mexdulon/tetra-Boards/doc/deutsch/DEC_1_0.pdf

# Decoder v1.0

mexdulon

11. April 2017

1

mexdulon | 1 DECODER

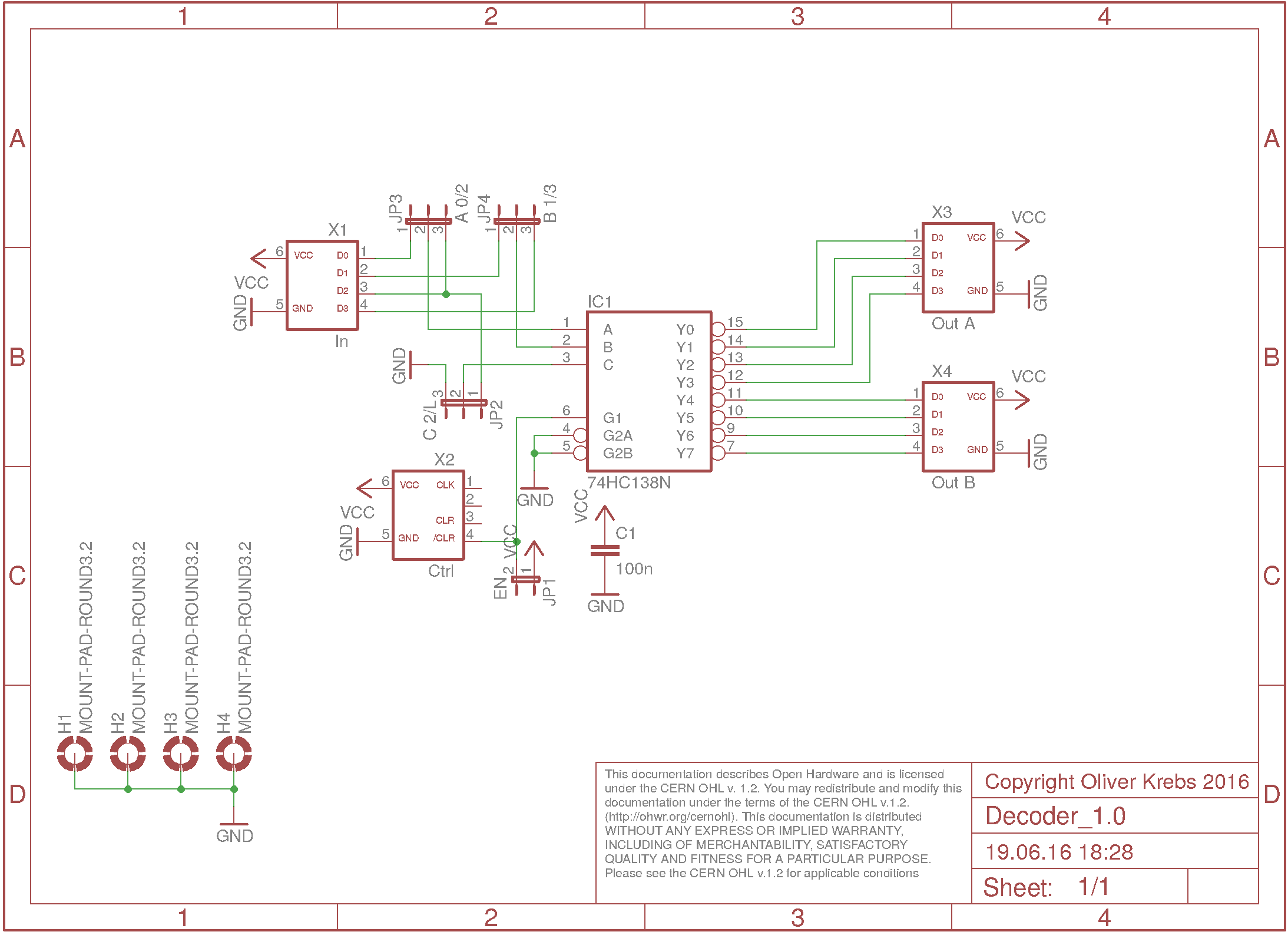
[picture p60: figure]

## 1 Decoder

### 1.1 Allgemein

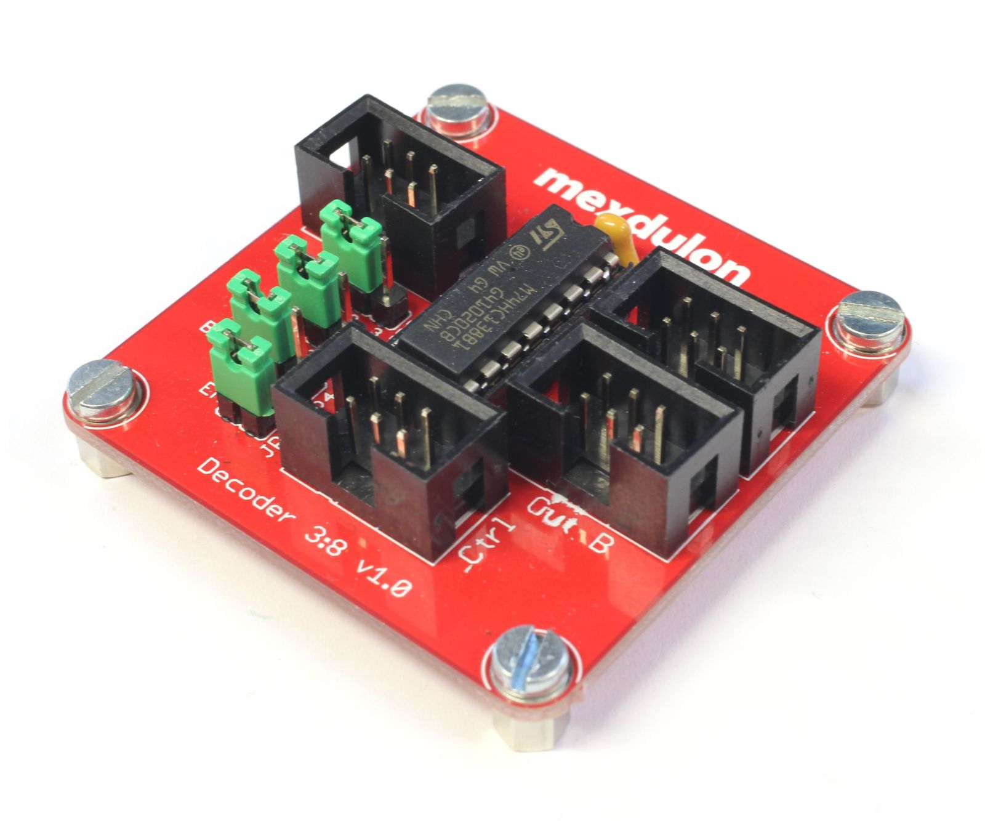
[picture p61: figure]

2

mexdulon | 1 DECODER

### 1.2 Funktion

### 1.3 Aufbau

Kürzel | Wert | Bezeichnung
C1 | 100n | Kondensator
IC1 | 74HC138N | IC (Decoder)
JP1 | EN | Stiftleiste 1x2
JP2 | C 2/L | Stiftleiste 1x3
JP3 | A 0/2 | Stiftleiste 1x3
JP4 | B 1/3 | Stiftleiste 1x3
X1 | In | Wannenstecker
X2 | Ctrl | Wannenstecker
X3 | Out A | Wannenstecker
X4 | Out B | Wannenstecker

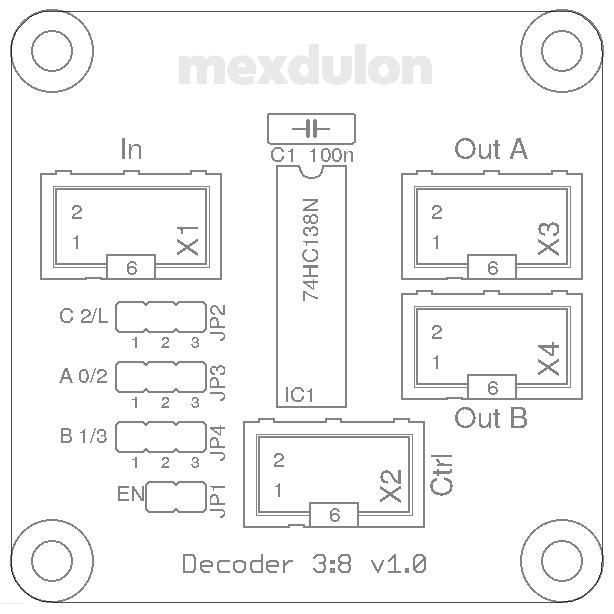
[picture p62: figure]

### 1.4 Test

3
