mexdulon/tetra-Boards/doc/deutsch/INV_1_0.pdf

# Inverter v1.0

mexdulon

11. April 2017

1

mexdulon | 1 INVERTER

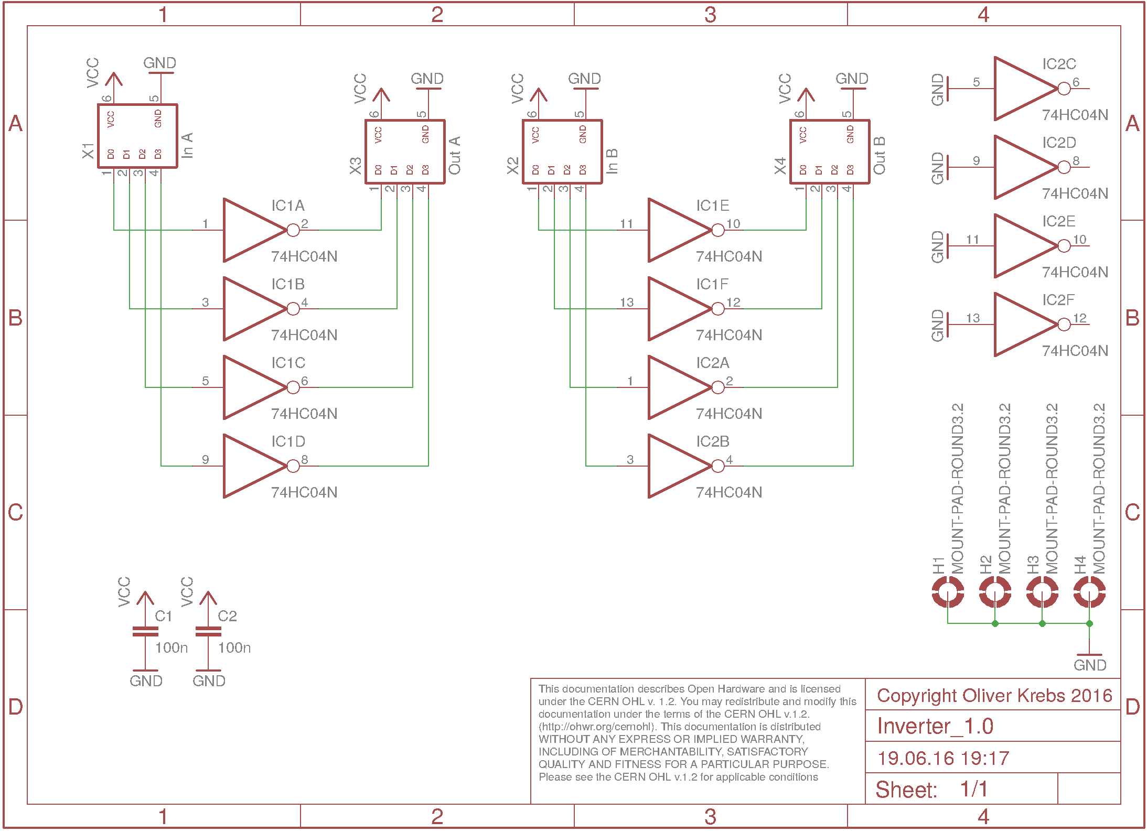
[picture p63: figure]

## 1 Inverter

### 1.1 Allgemein

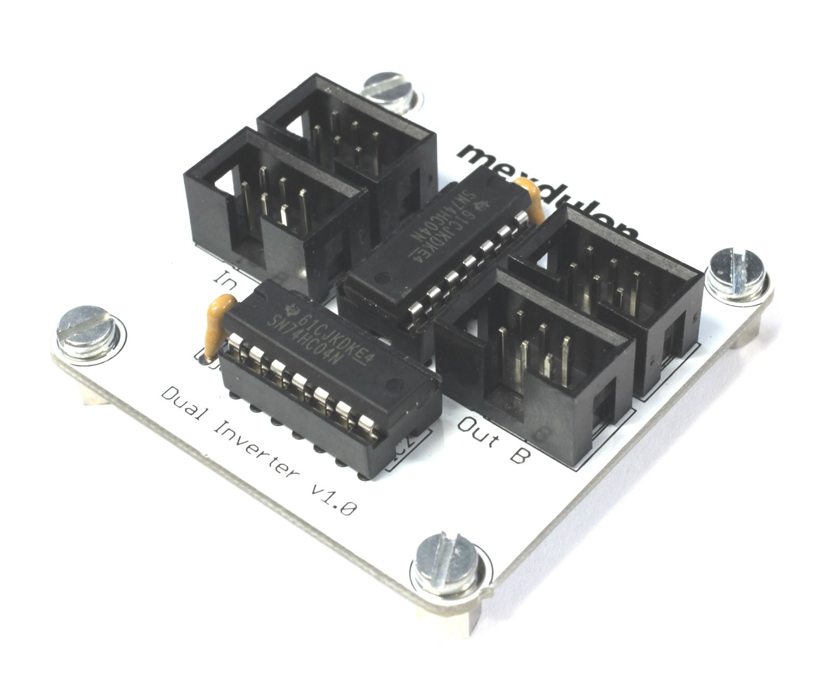
[picture p64: figure]

2

mexdulon | 1 INVERTER

### 1.2 Funktion

### 1.3 Aufbau

Kürzel | Wert | Bezeichnung
C1 | 100n | Kondensator
C2 | 100n | Kondensator
IC1 | 74HC04N | IC (Inverter)
IC2 | 74HC04N | IC (Inverter)
X1 | In A | Wannenstecker
X2 | In B | Wannenstecker
X3 | Out A | Wannenstecker
X4 | Out B | Wannenstecker

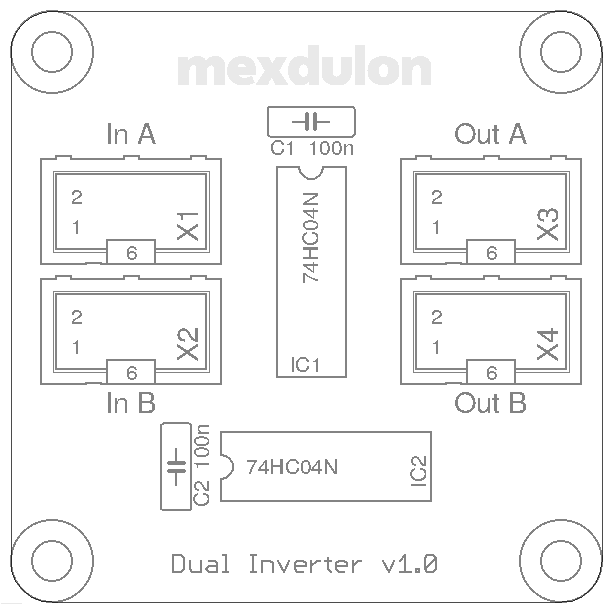
[picture p65: figure]

### 1.4 Test

3
