mexdulon/tetra-Boards/doc/deutsch/JAD_1_0.pdf

# Jumper Adapter v1.0

mexdulon

11. April 2017

1

mexdulon | 1 JUMPER ADAPTER

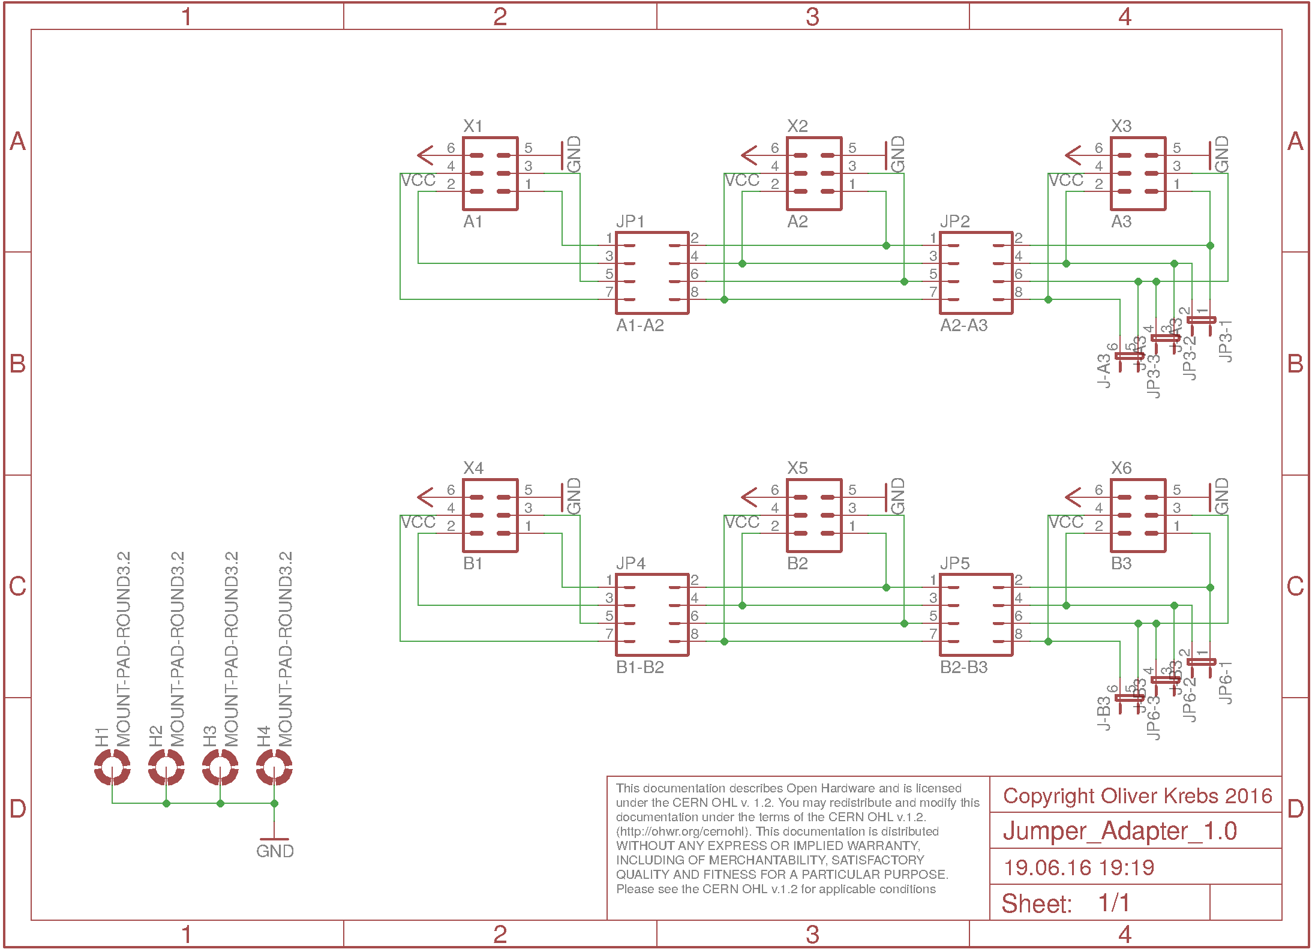
[picture p66: figure]

## 1 Jumper Adapter

### 1.1 Allgemein

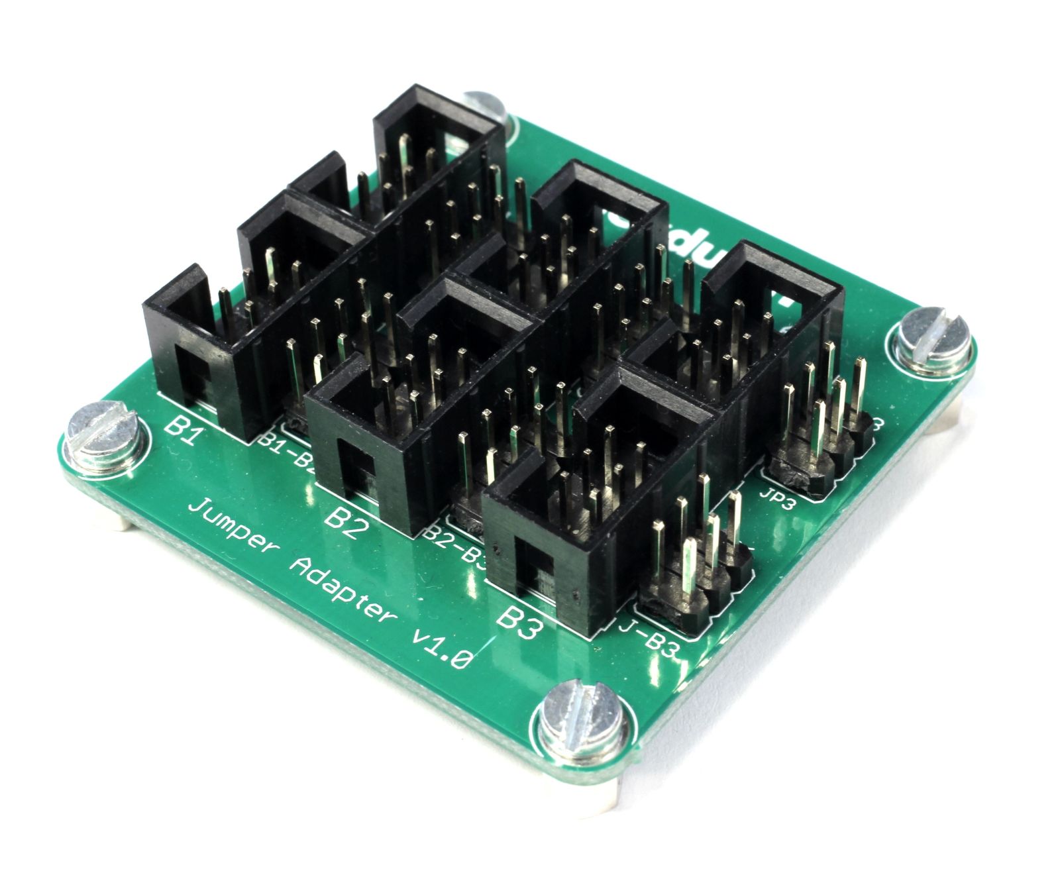
[picture p67: figure]

2

mexdulon | 1 JUMPER ADAPTER

### 1.2 Funktion

### 1.3 Aufbau

Kürzel | Wert | Bezeichnung
JP1 | A1-A2 | Stiftleiste 2x4
JP2 | A2-A3 | Stiftleiste 2x4
JP3 | J-A3 | Stiftleiste 2x3
JP4 | B1-B2 | Stiftleiste 2x4
JP5 | B2-B3 | Stiftleiste 2x4
JP6 | J-B3 | Stiftleiste 2x3
X1 | A1 | Wannenstecker
X2 | A2 | Wannenstecker
X3 | A3 | Wannenstecker
X4 | B1 | Wannenstecker
X5 | B2 | Wannenstecker
X6 | B3 | Wannenstecker

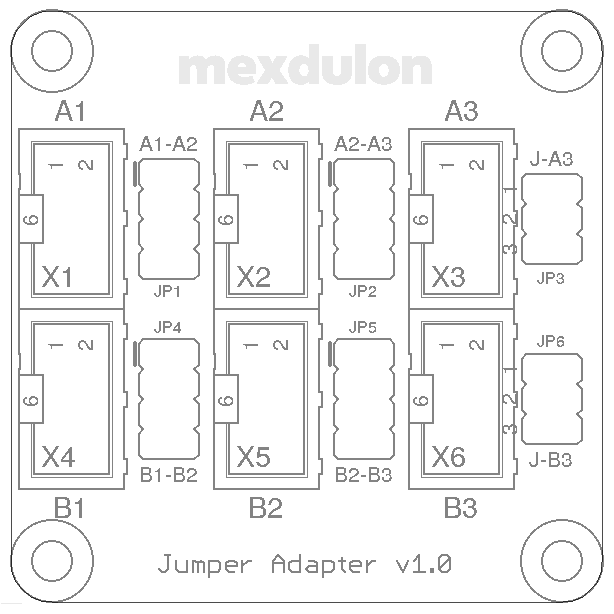
[picture p68: figure]

### 1.4 Test

3
