mexdulon/tetra-Boards/doc/deutsch/JKF_1_0.pdf

# JK Flip-flop v1.0

mexdulon

11. April 2017

1

mexdulon | 1 JK FLIPFLOP

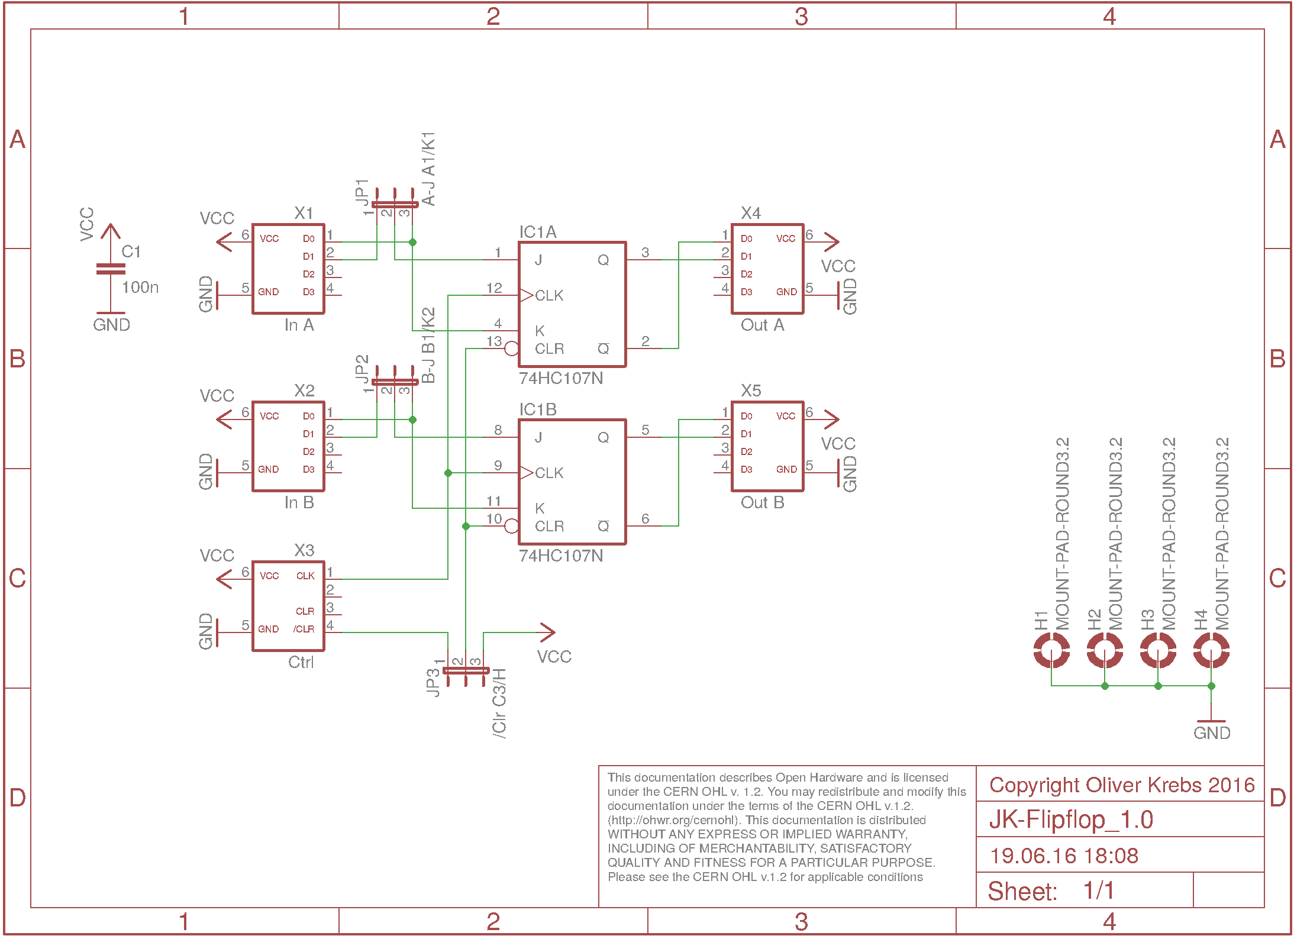
[picture p69: figure]

## 1 JK Flipflop

### 1.1 Allgemein

### 1.2 Funktion

### 1.3 Aufbau

Kürzel | Wert | Bezeichnung
C1 | 100n | Kondensator
IC1 | 74HC107N | IC (Dual Flipflop)
JP1 | A-J A1/K1 | Stiftleiste 1x3
JP2 | B-J B1/K2 | Stiftleiste 1x3
JP3 | /Clr C3/H | Stiftleiste 1x3
X1 | In A | Wannenstecker
X2 | In B | Wannenstecker
X3 | Ctrl | Wannenstecker
X4 | Out A | Wannenstecker
X5 | Out B | Wannenstecker

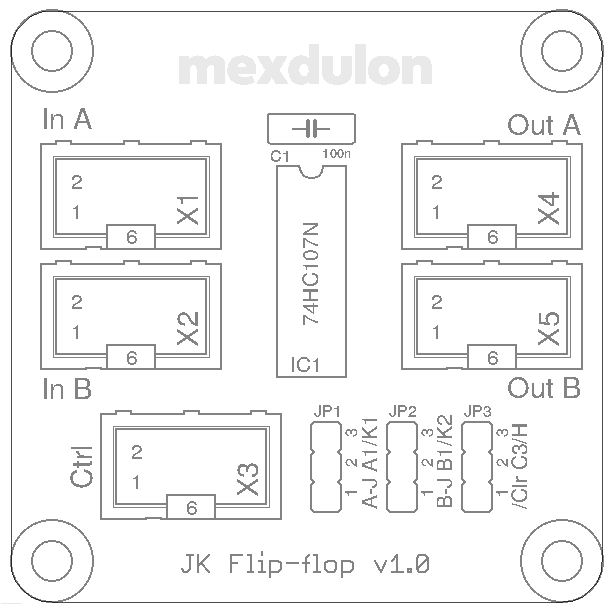
[picture p70: figure]

### 1.4 Test

2
