mexdulon/tetra-Boards/doc/deutsch/LAD_1_0.pdf

# Line Adapter v1.0

mexdulon

11. April 2017

1

mexdulon | 1 LINE ADAPTER

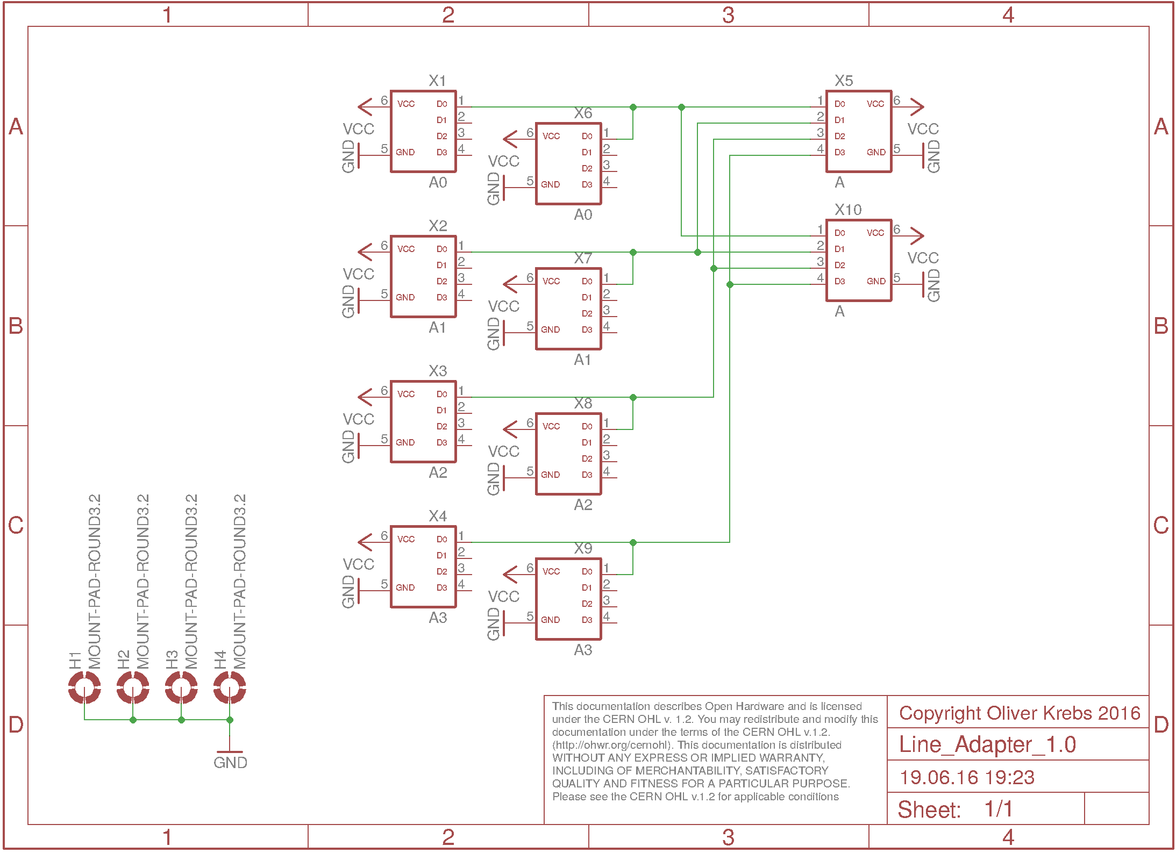
[picture p71: figure]

## 1 Line Adapter

### 1.1 Allgemein

### 1.2 Funktion

### 1.3 Aufbau

Kürzel | Wert | Bezeichnung
X1 | A0 | Wannenstecker
X2 | A1 | Wannenstecker
X3 | A2 | Wannenstecker
X4 | A3 | Wannenstecker
X5 | A | Wannenstecker
X6 | A0 | Wannenstecker
X7 | A1 | Wannenstecker
X8 | A2 | Wannenstecker
X9 | A3 | Wannenstecker
X10 | A | Wannenstecker

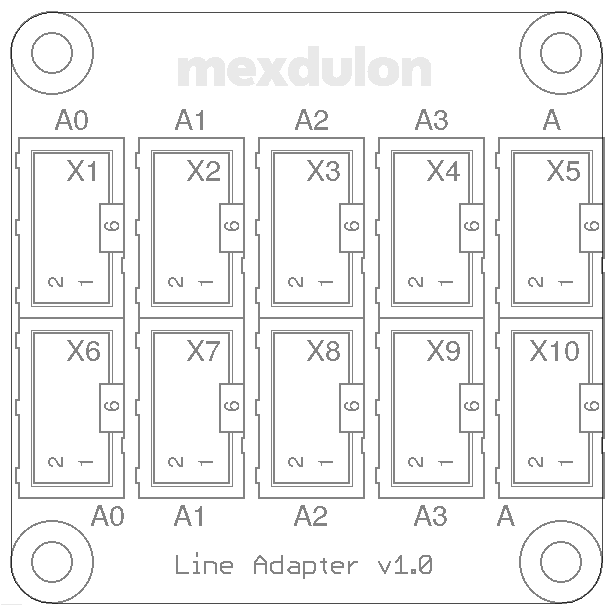
[picture p72: figure]

### 1.4 Test

2
