mexdulon/tetra-Boards/doc/deutsch/SAD_1_0.pdf

# Shift Adapter v1.0

mexdulon

11. April 2017

1

mexdulon | 1 SHIFT ADAPTER

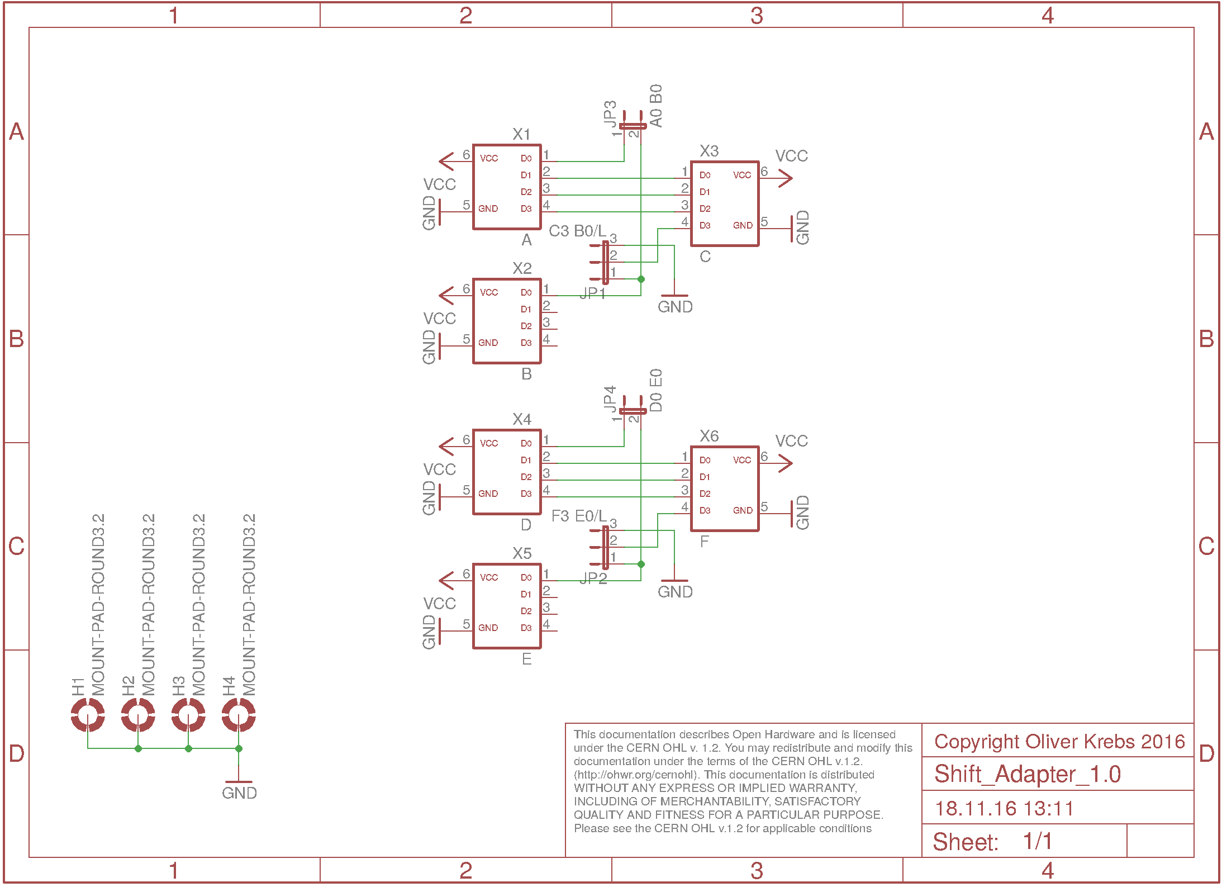
[picture p78: figure]

## 1 Shift Adapter

### 1.1 Allgemein

### 1.2 Funktion

### 1.3 Aufbau

Kürzel | Wert | Bezeichnung
JP1 | C3 B0/L | Stiftleiste 1x3
JP2 | F3 E0/L | Stiftleiste 1x3
JP3 | A0 B0 | Stiftleiste 1x2
JP4 | D0 E0 | Stiftleiste 1x2
X1 | A | Wannenstecker
X2 | B | Wannenstecker
X3 | C | Wannenstecker
X4 | D | Wannenstecker
X5 | E | Wannenstecker
X6 | F | Wannenstecker

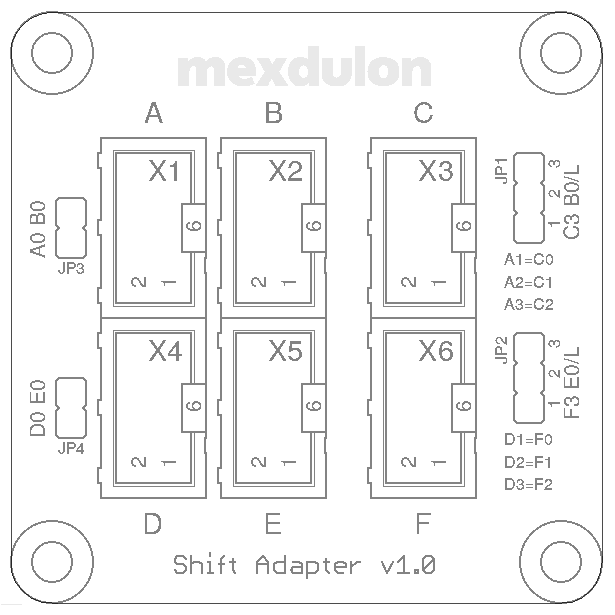
[picture p79: figure]

### 1.4 Test

2
