mexdulon/tetra-Boards/doc/7SD_1_1_sch.png

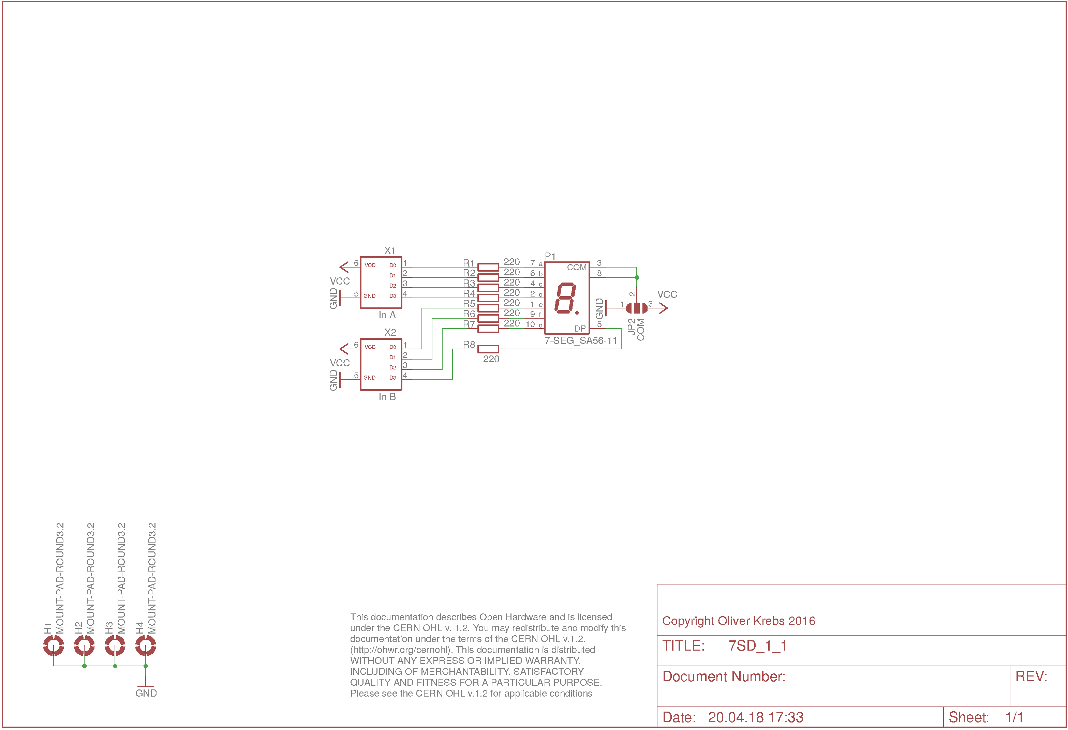
doc/7SD_1_1_sch.png
