mexdulon/tetra-Boards/doc/7SD_1_1_silk.png

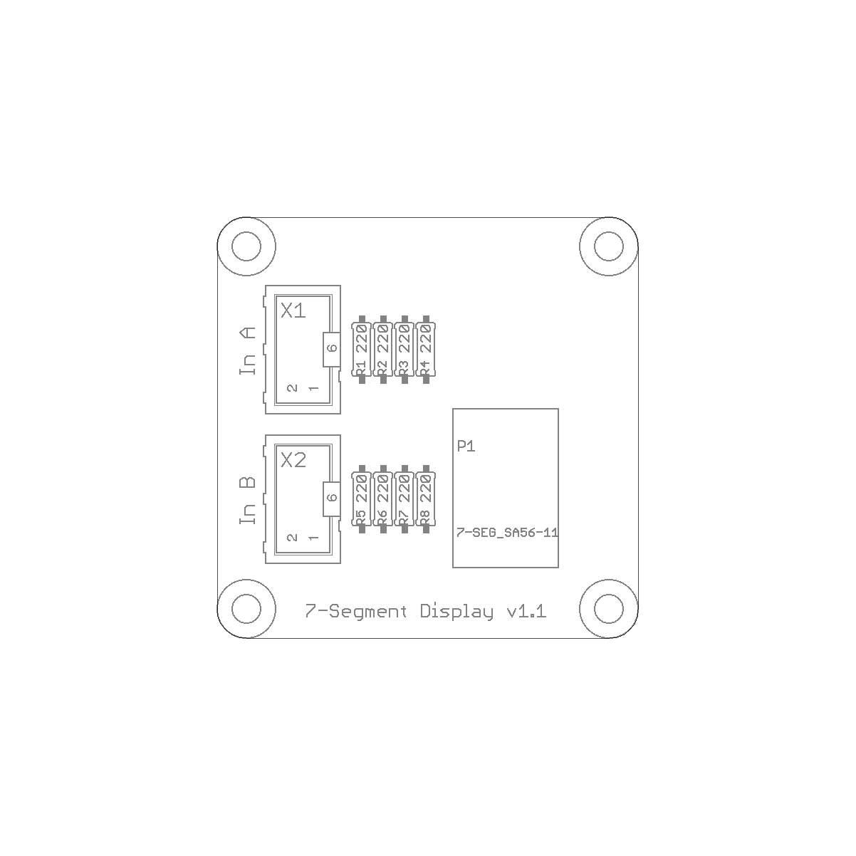
doc/7SD_1_1_silk.png
