mexdulon/tetra-Boards/doc/ADA_1_1_sch.png

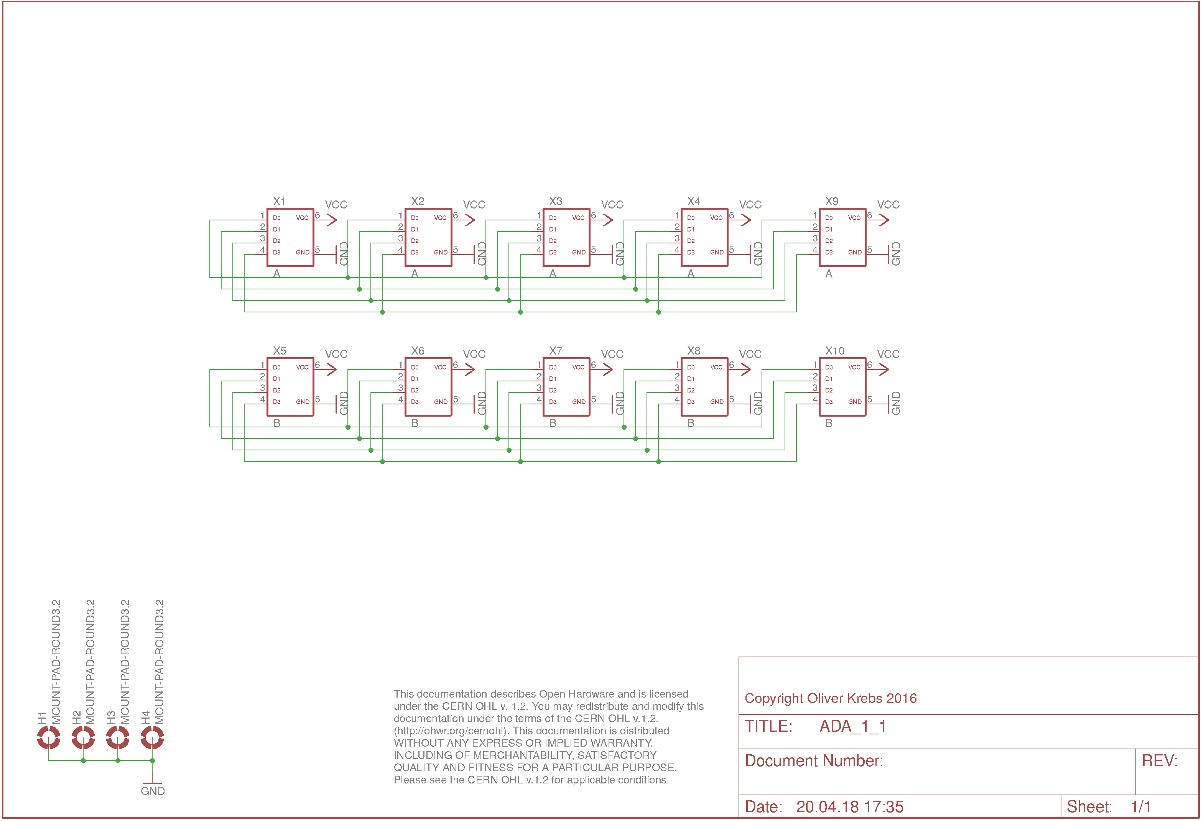
doc/ADA_1_1_sch.png
