mexdulon/tetra-Boards/doc/ADA_1_1_silk.png

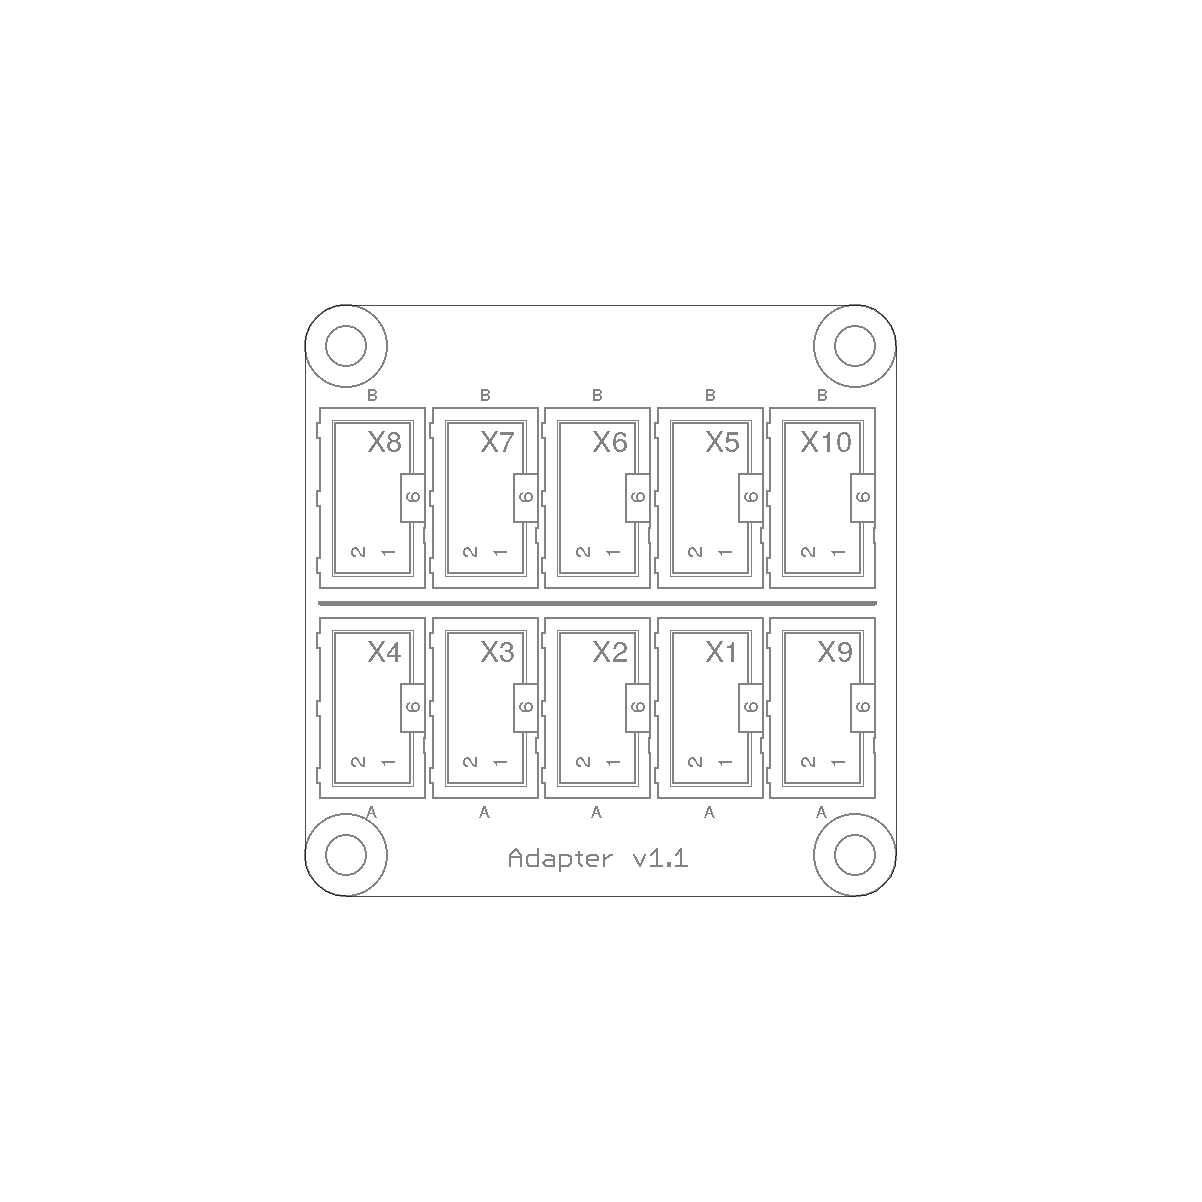
doc/ADA_1_1_silk.png
