mexdulon/tetra-Boards/doc/ADC_1_0_sch.png

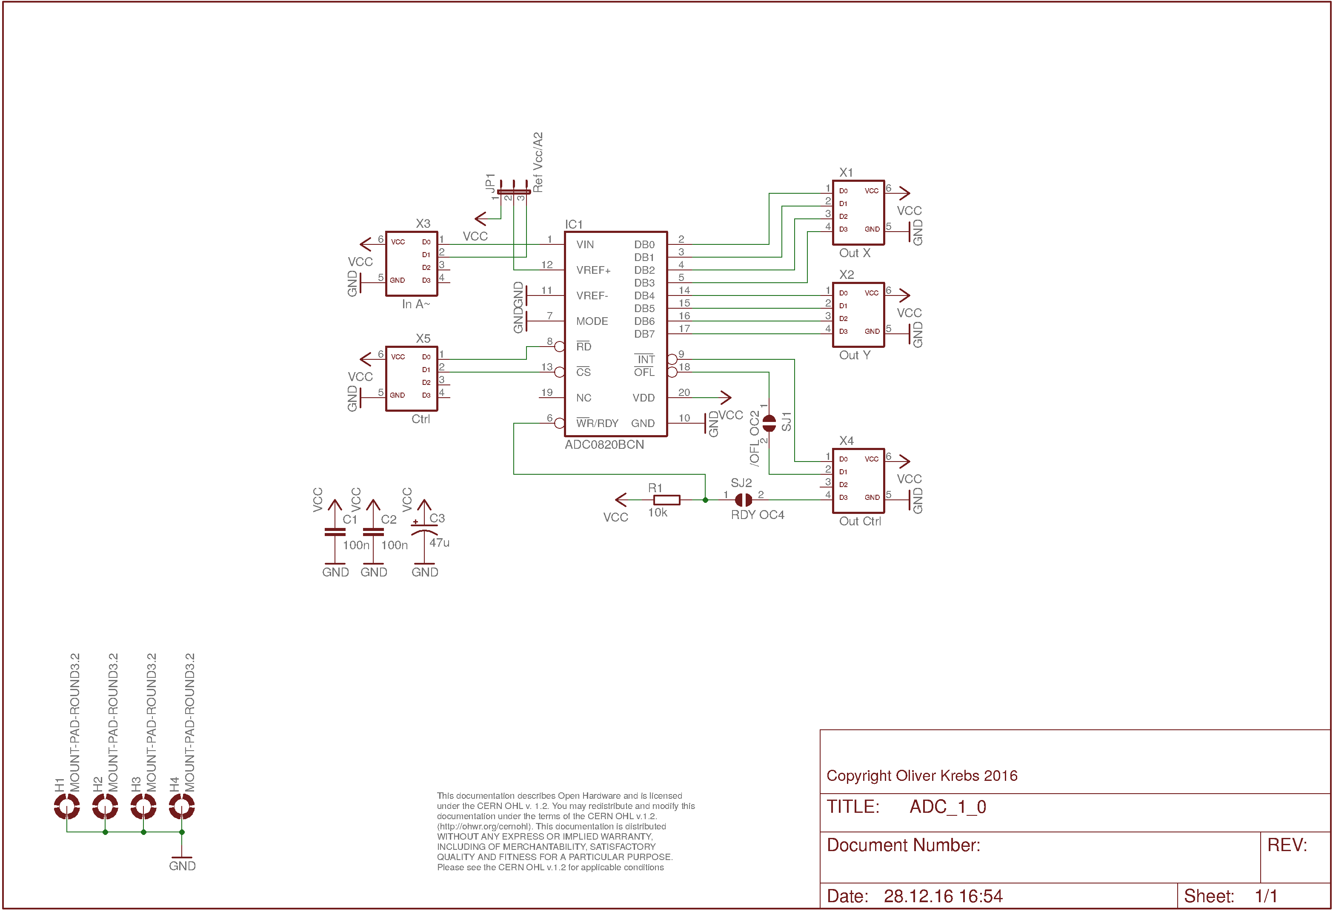
doc/ADC_1_0_sch.png
