mexdulon/tetra-Boards/doc/ADC_1_0_silk.png

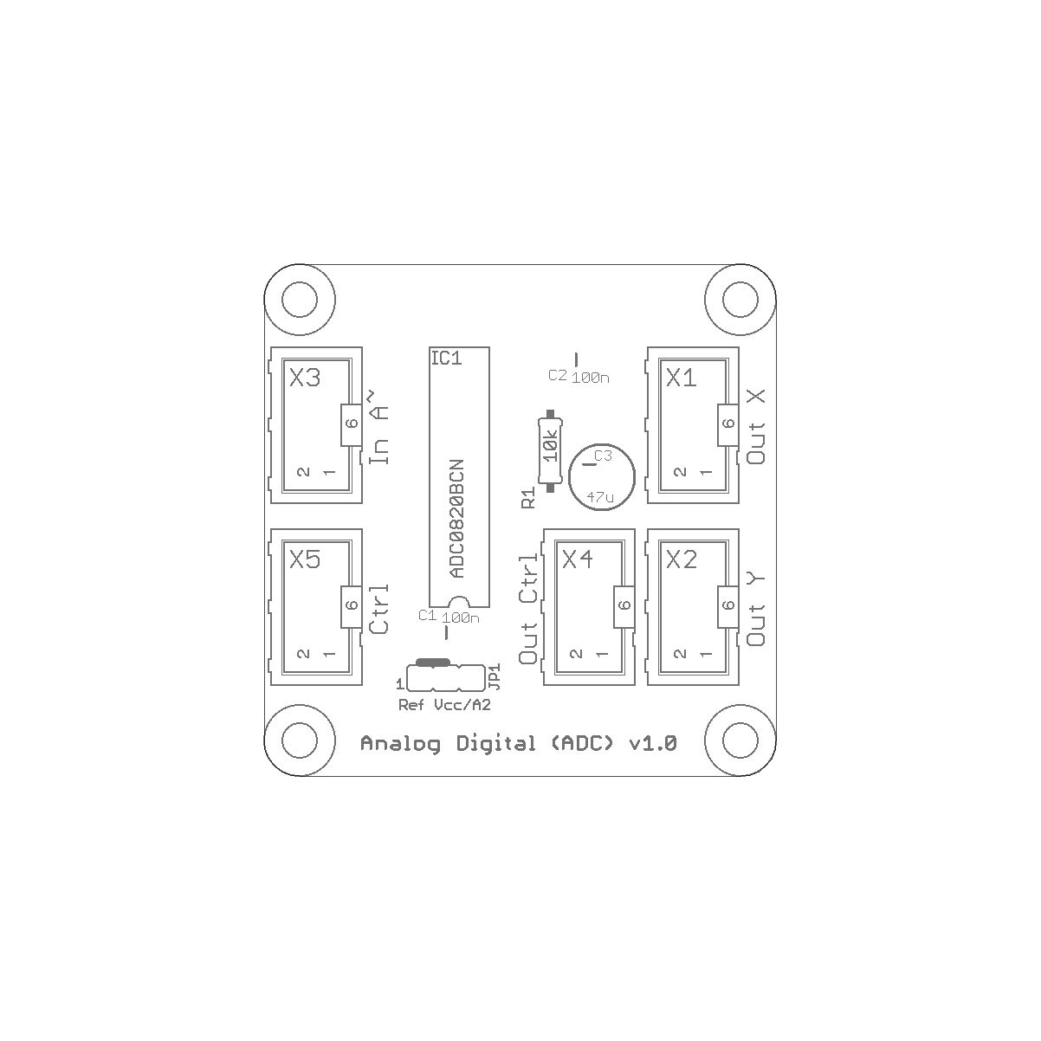
doc/ADC_1_0_silk.png
