mexdulon/tetra-Boards/doc/ADD_1_1_sch.png

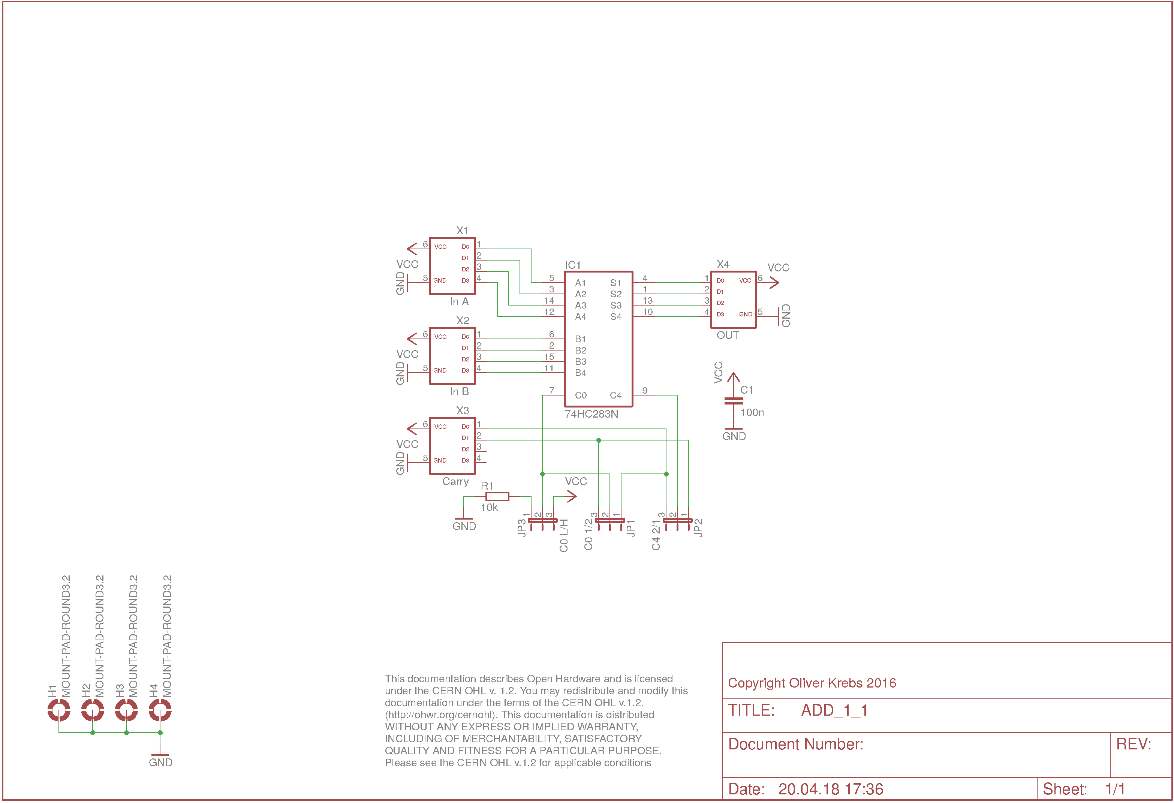
doc/ADD_1_1_sch.png
