mexdulon/tetra-Boards/doc/ALU_1_0_sch.png

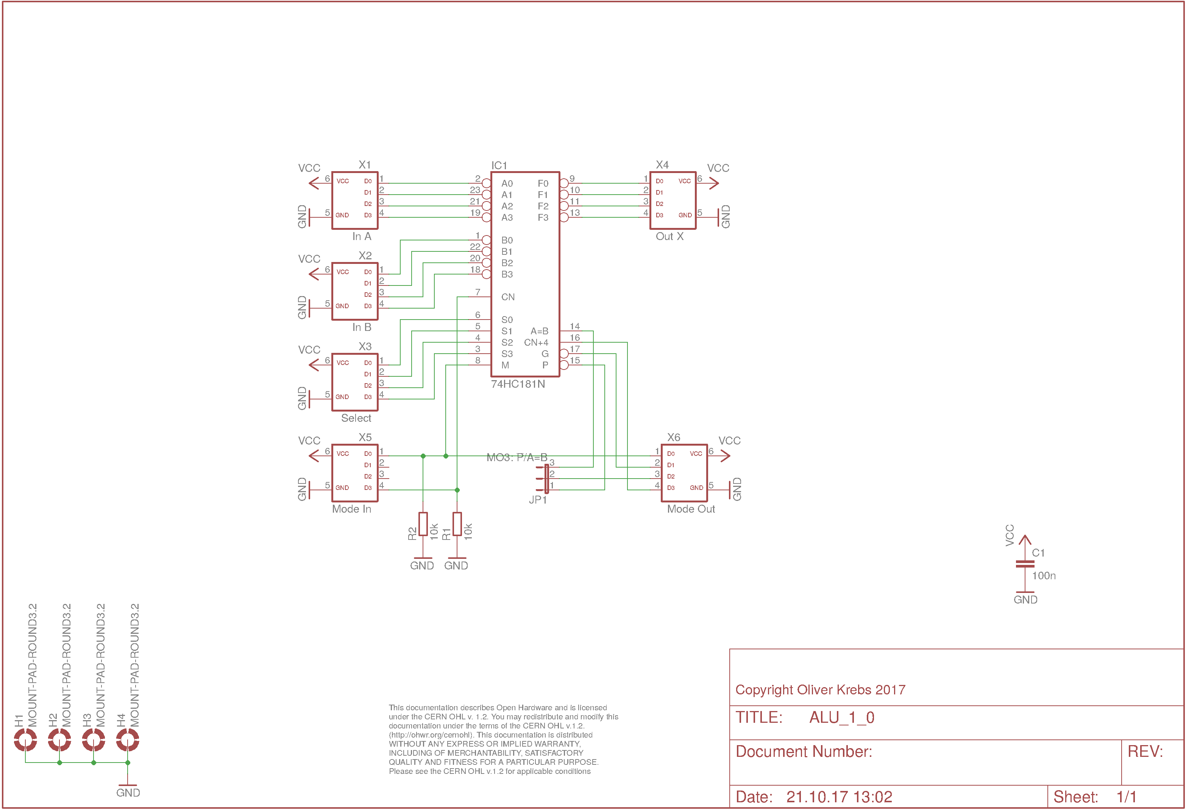
doc/ALU_1_0_sch.png
