mexdulon/tetra-Boards/doc/ALU_1_0_silk.png

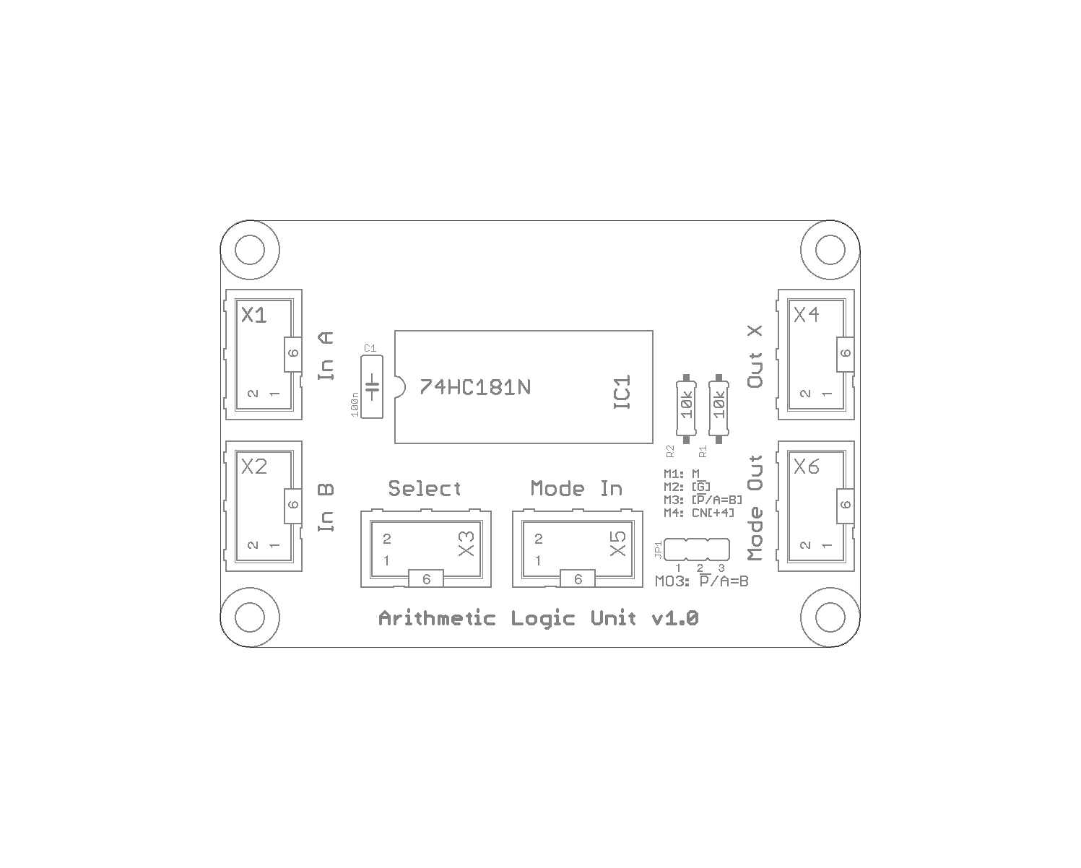
doc/ALU_1_0_silk.png
