mexdulon/tetra-Boards/doc/AMP_1_0_sch.png

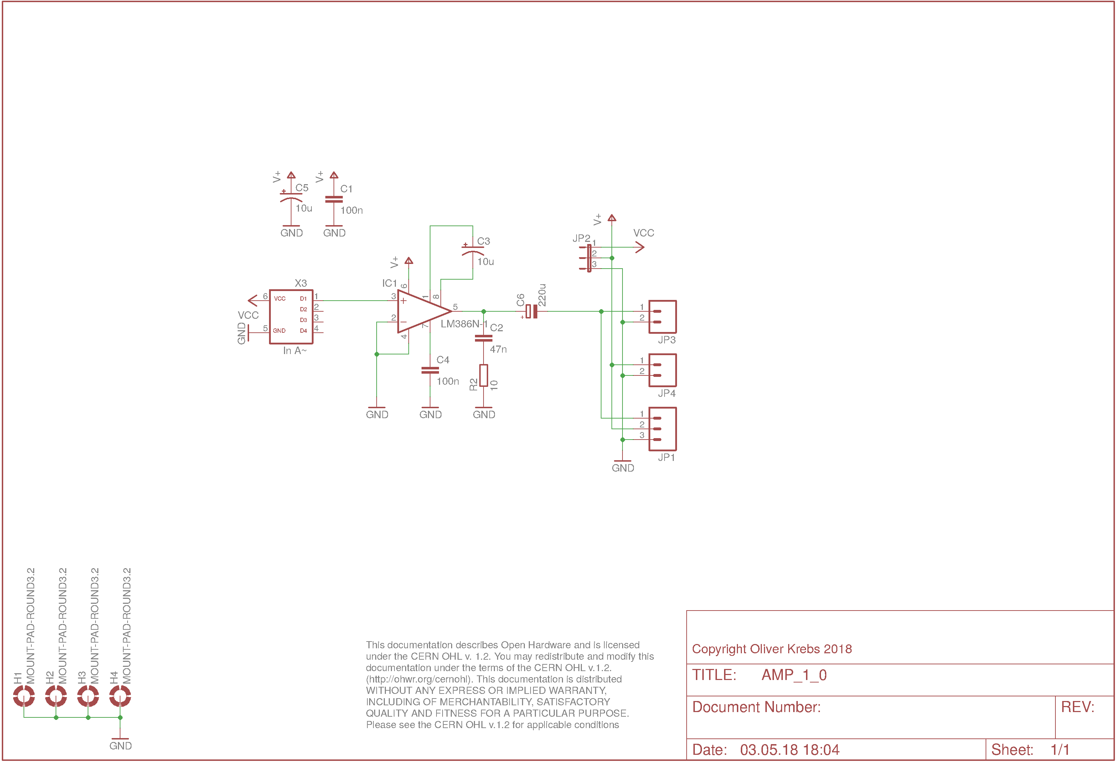
doc/AMP_1_0_sch.png
