mexdulon/tetra-Boards/doc/AMP_1_0_silk.png

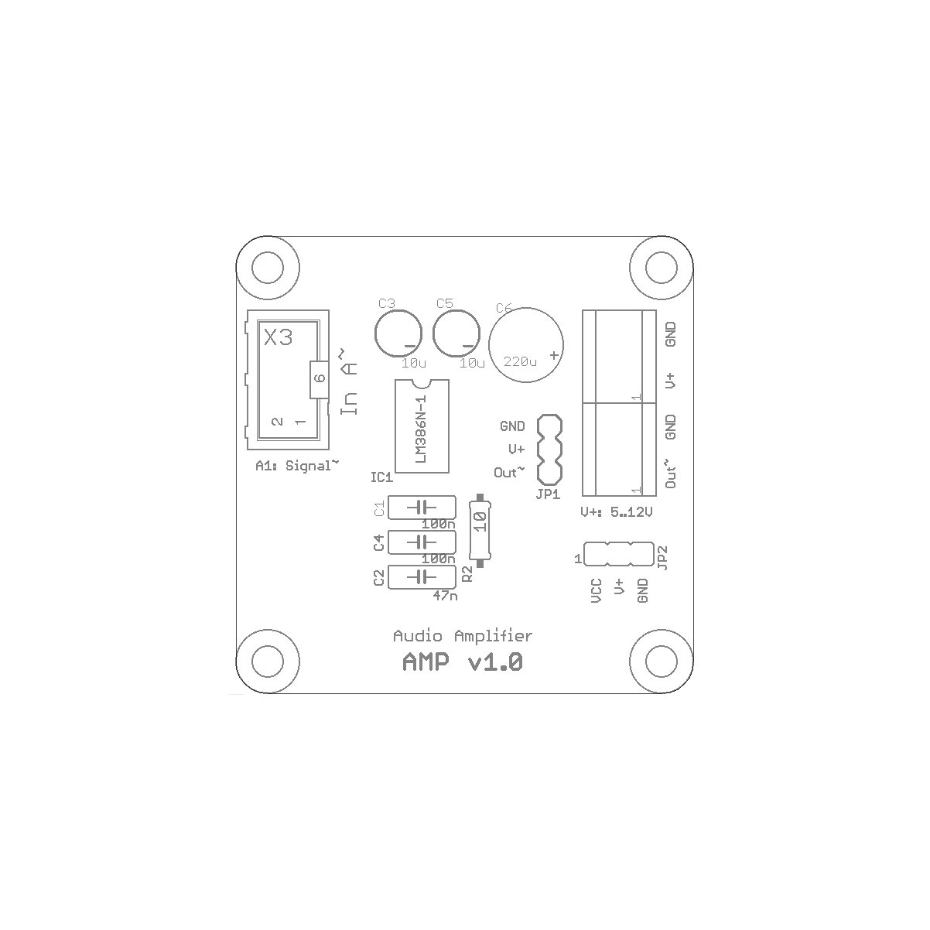
doc/AMP_1_0_silk.png
