mexdulon/tetra-Boards/doc/AND_1_1_sch.png

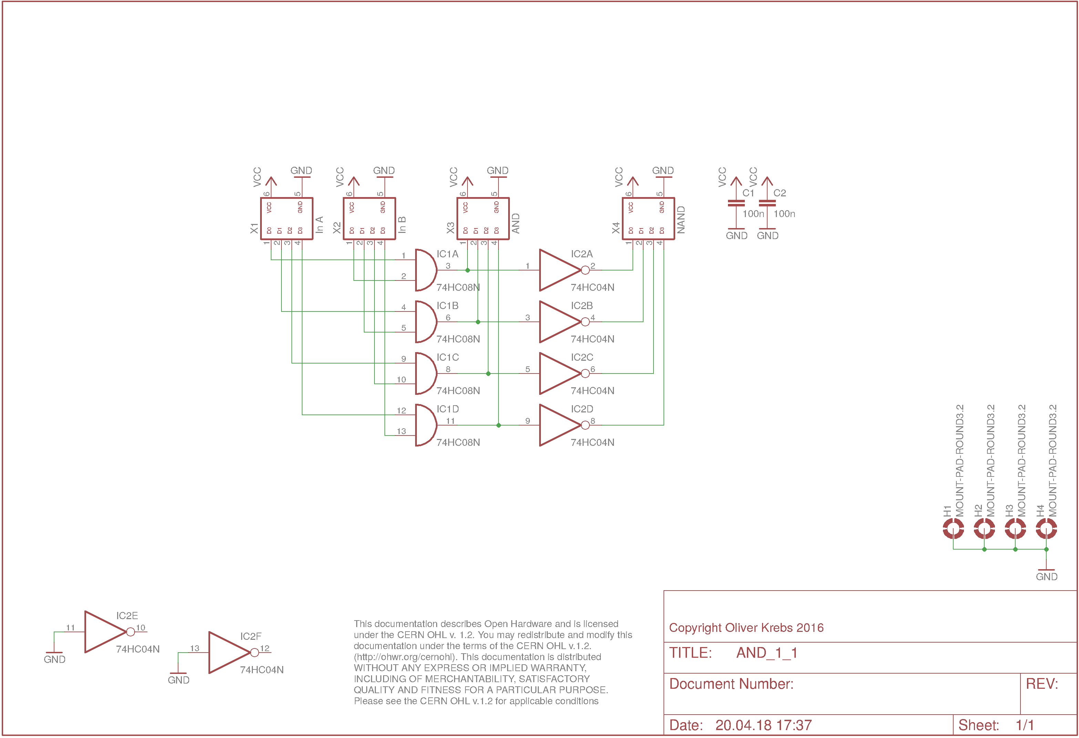
doc/AND_1_1_sch.png
