mexdulon/tetra-Boards/doc/AND_1_1_silk.png

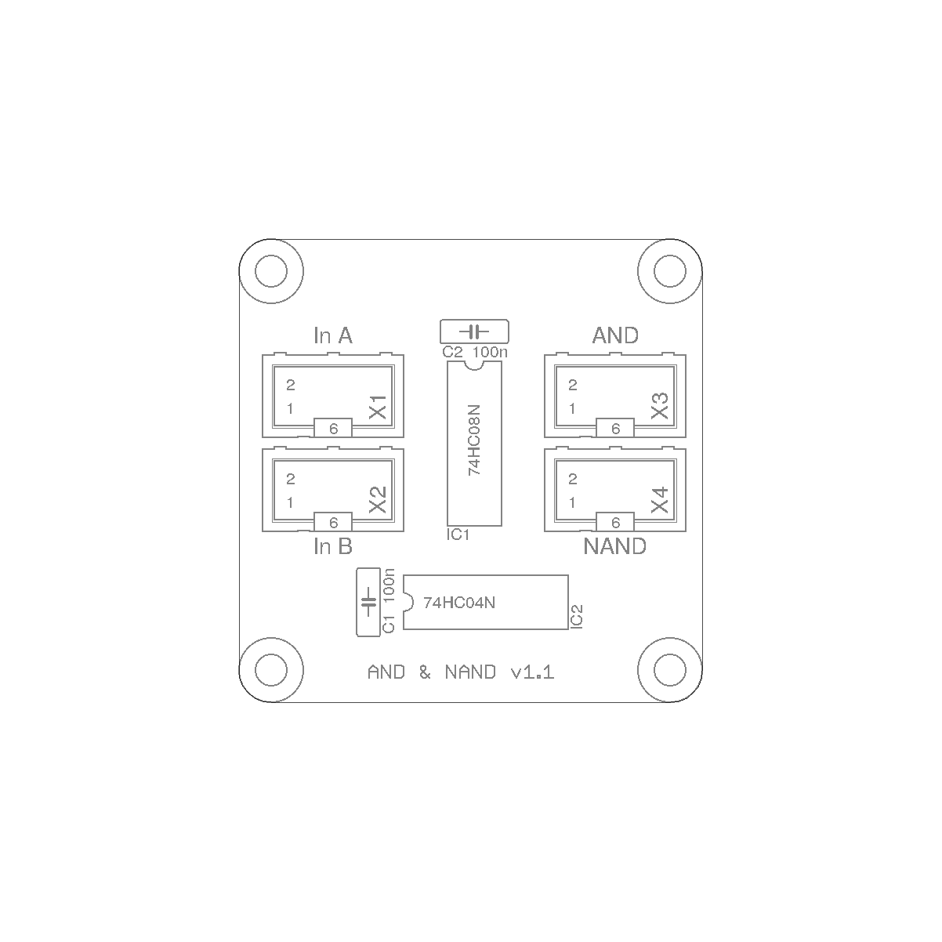
doc/AND_1_1_silk.png
