mexdulon/tetra-Boards/doc/ANS_1_1_sch.png

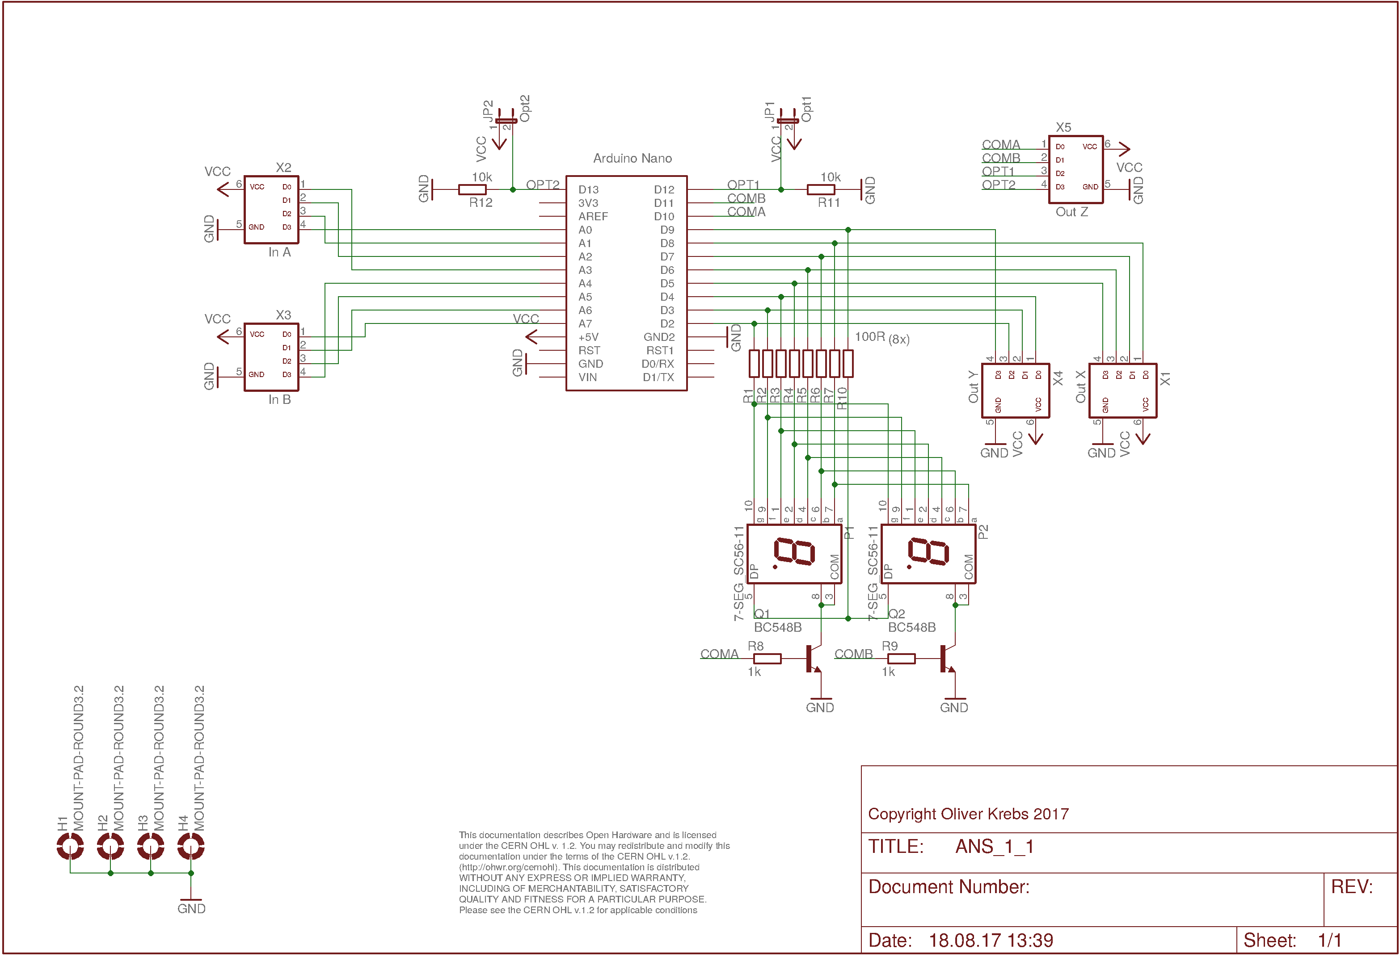
doc/ANS_1_1_sch.png
