mexdulon/tetra-Boards/doc/ANS_1_1_silk.png

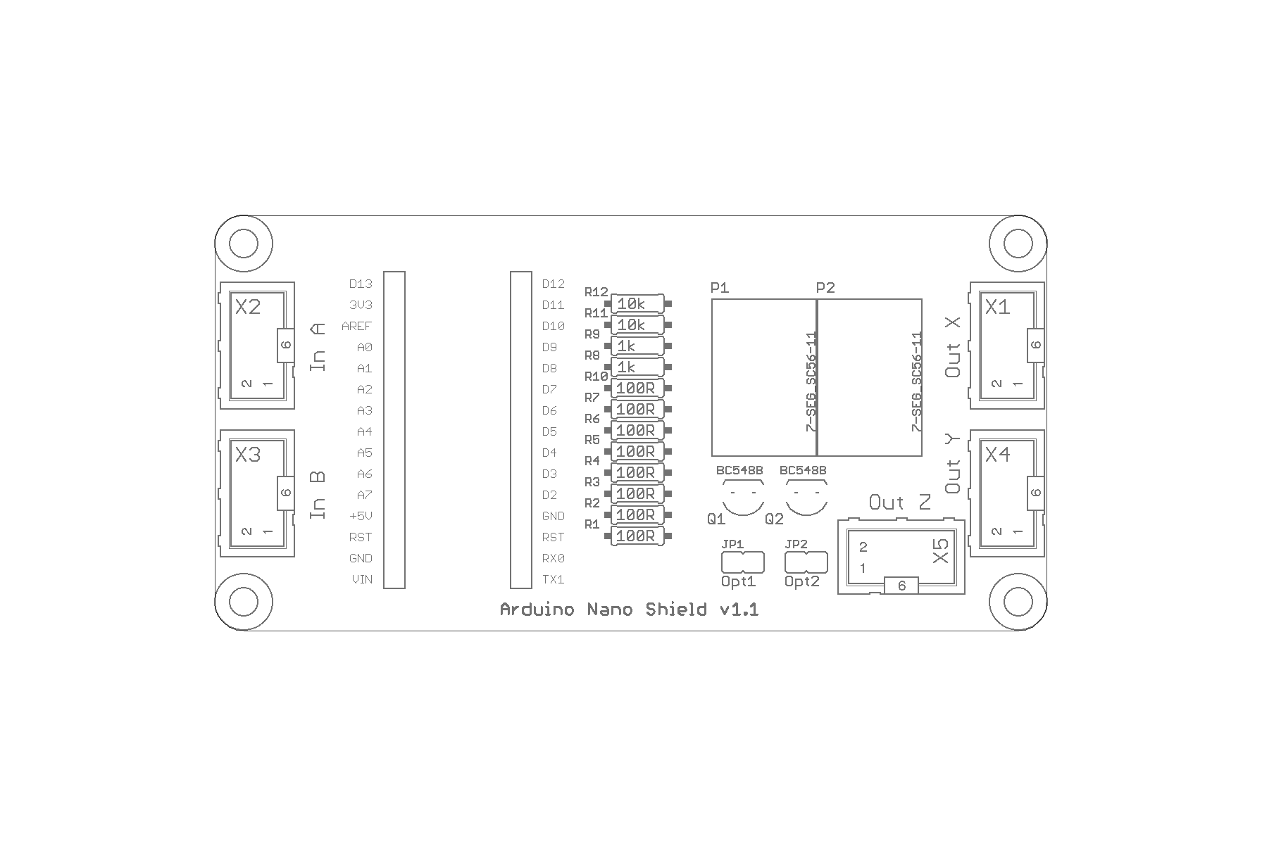
doc/ANS_1_1_silk.png
