mexdulon/tetra-Boards/doc/ARD_1_0_sch.png

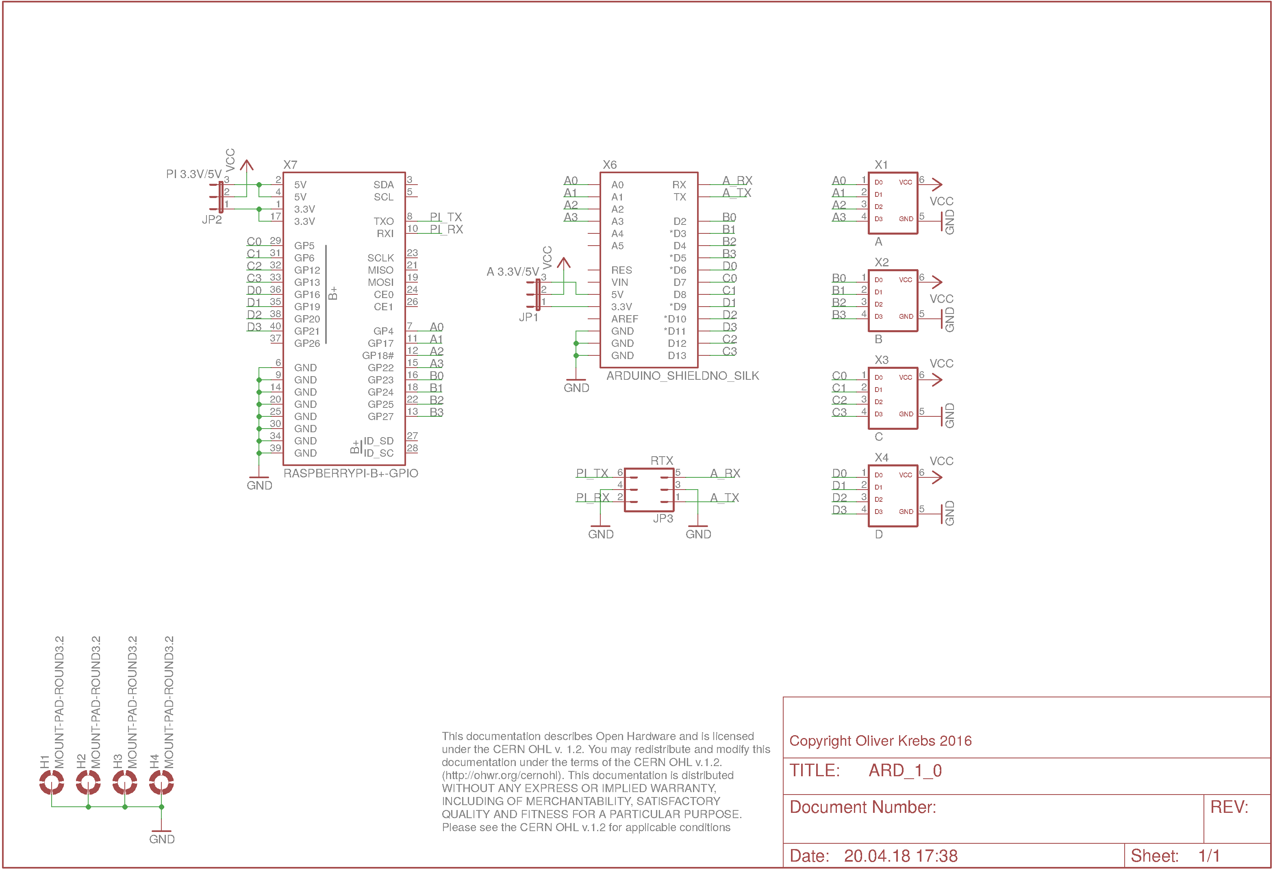
doc/ARD_1_0_sch.png
