mexdulon/tetra-Boards/doc/ARD_1_0_silk.png

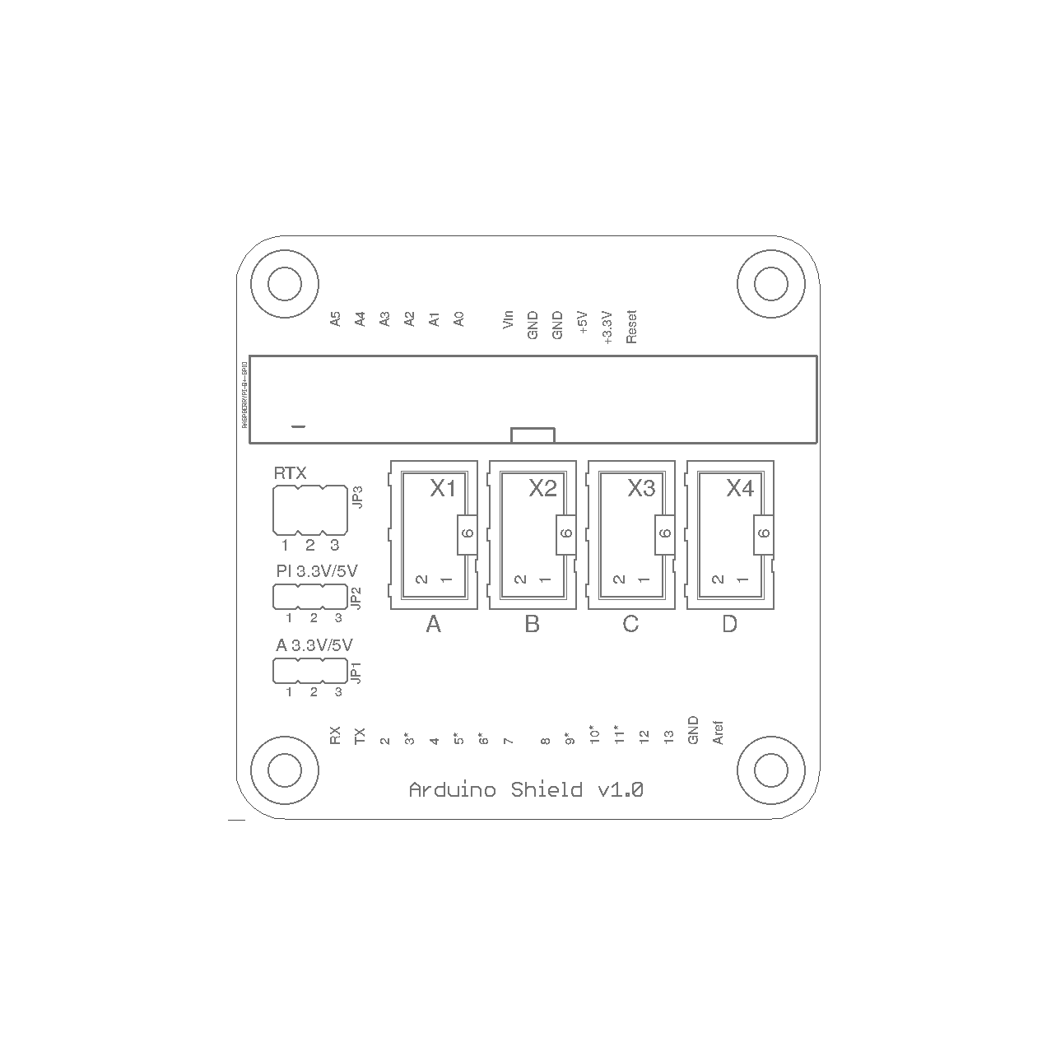
doc/ARD_1_0_silk.png
