mexdulon/tetra-Boards/doc/AVC_1_0_sch.png

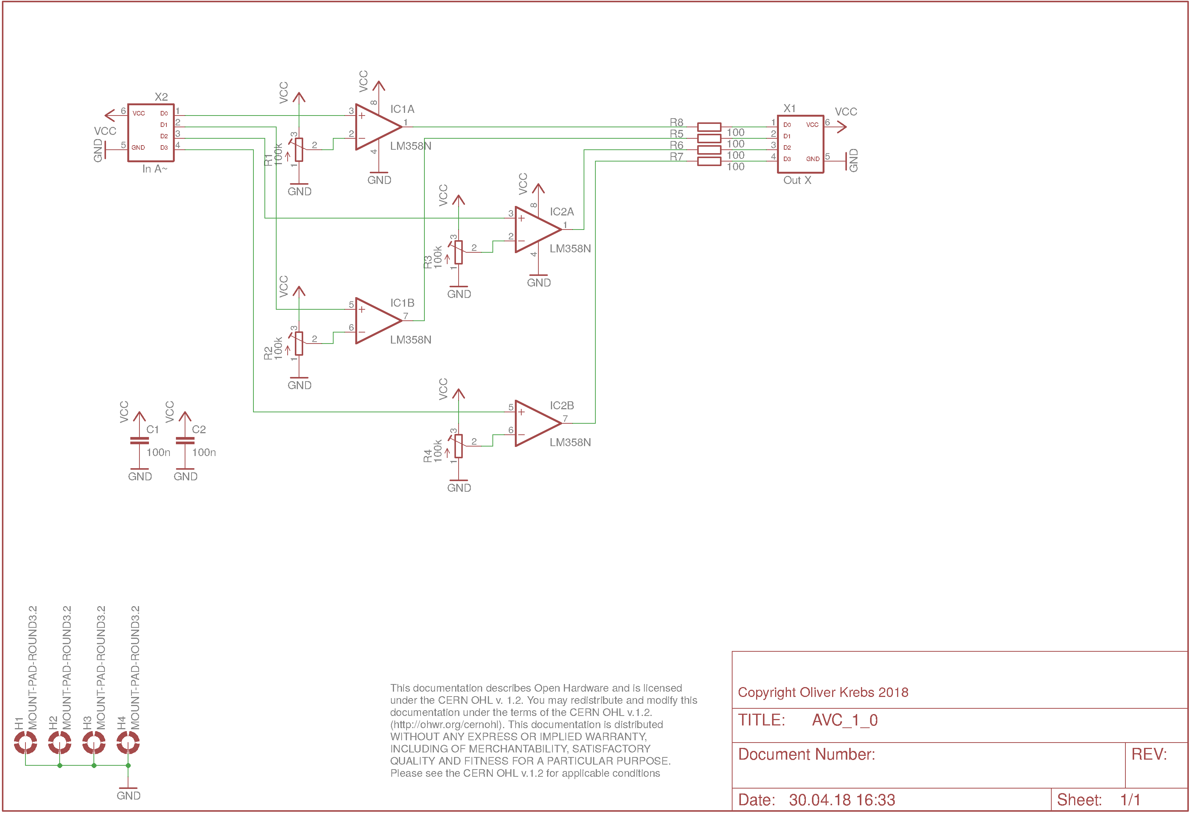
doc/AVC_1_0_sch.png
