mexdulon/tetra-Boards/doc/B7D_1_1_sch.png

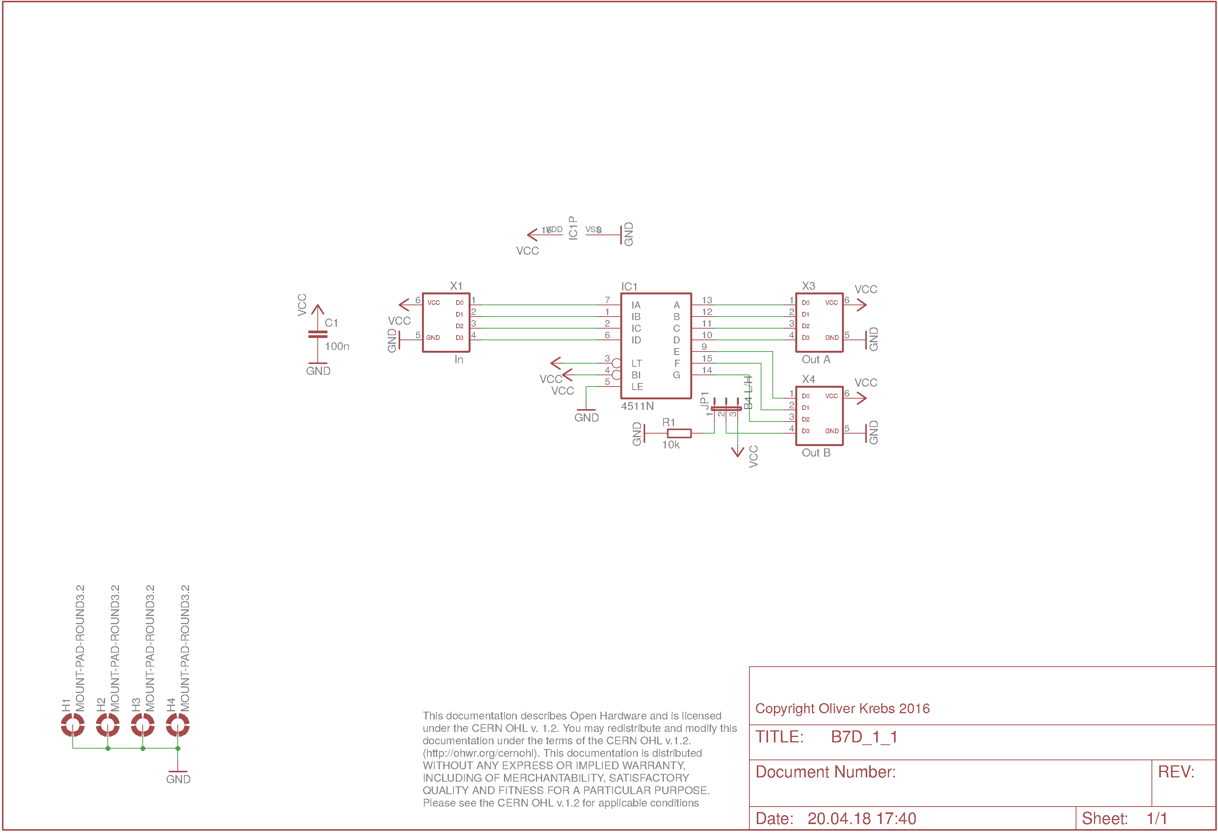
doc/B7D_1_1_sch.png
