mexdulon/tetra-Boards/doc/BCC_1_1_sch.png

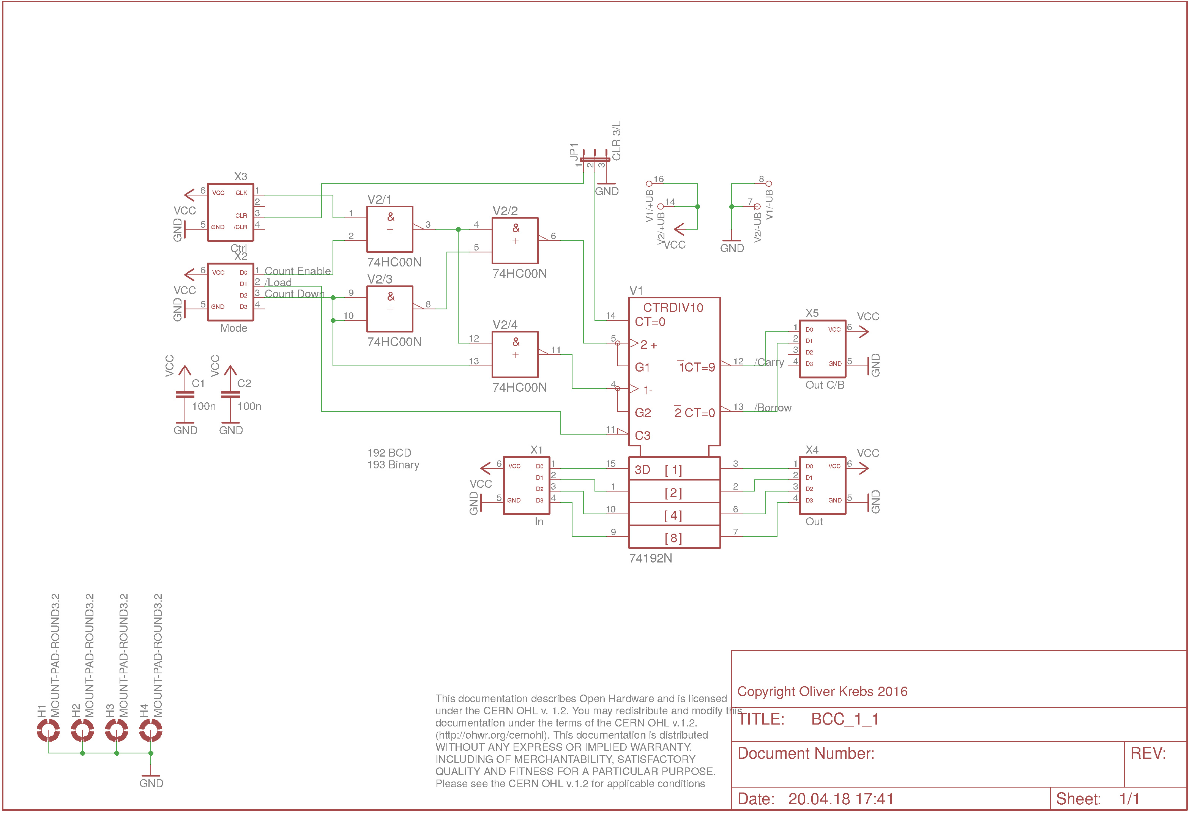
doc/BCC_1_1_sch.png
