mexdulon/tetra-Boards/doc/BNC_1_1_sch.png

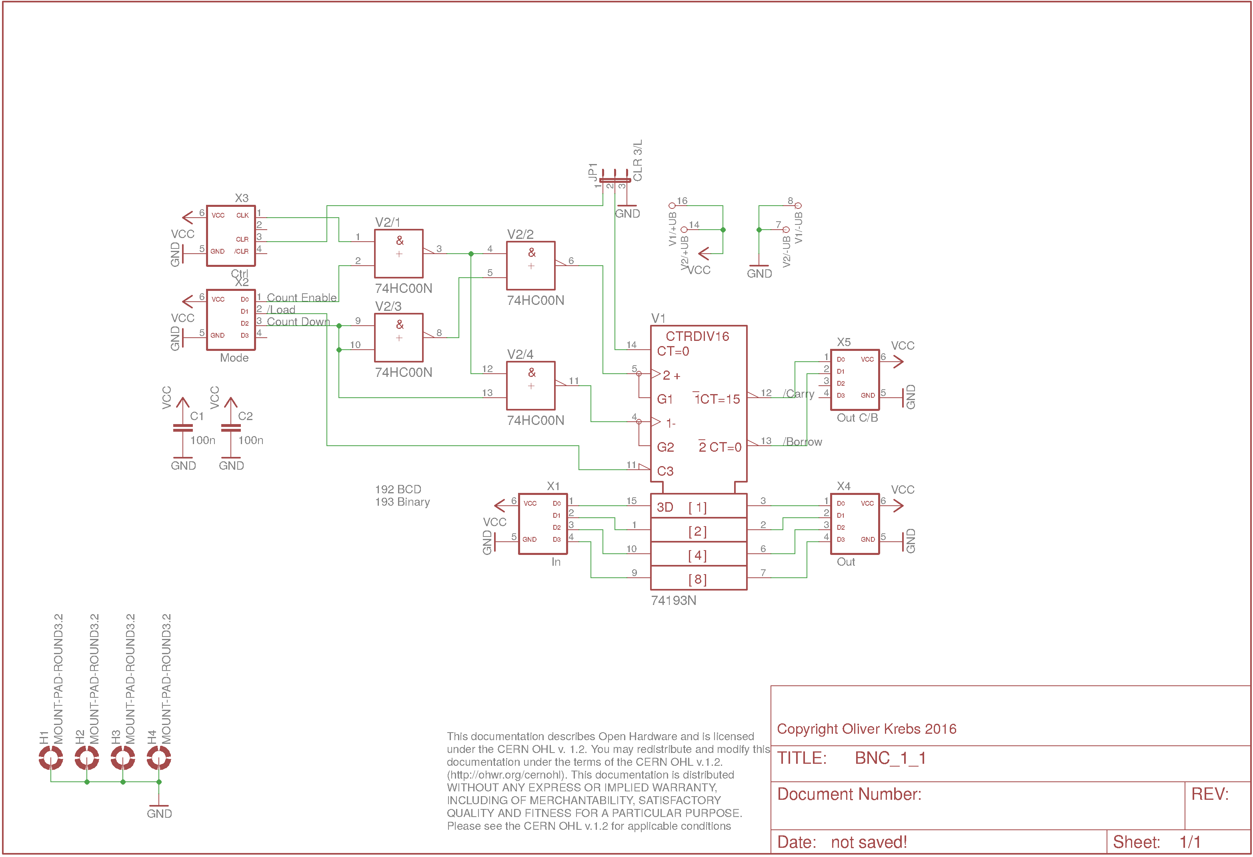
doc/BNC_1_1_sch.png
