mexdulon/tetra-Boards/doc/BTN_1_1_sch.png

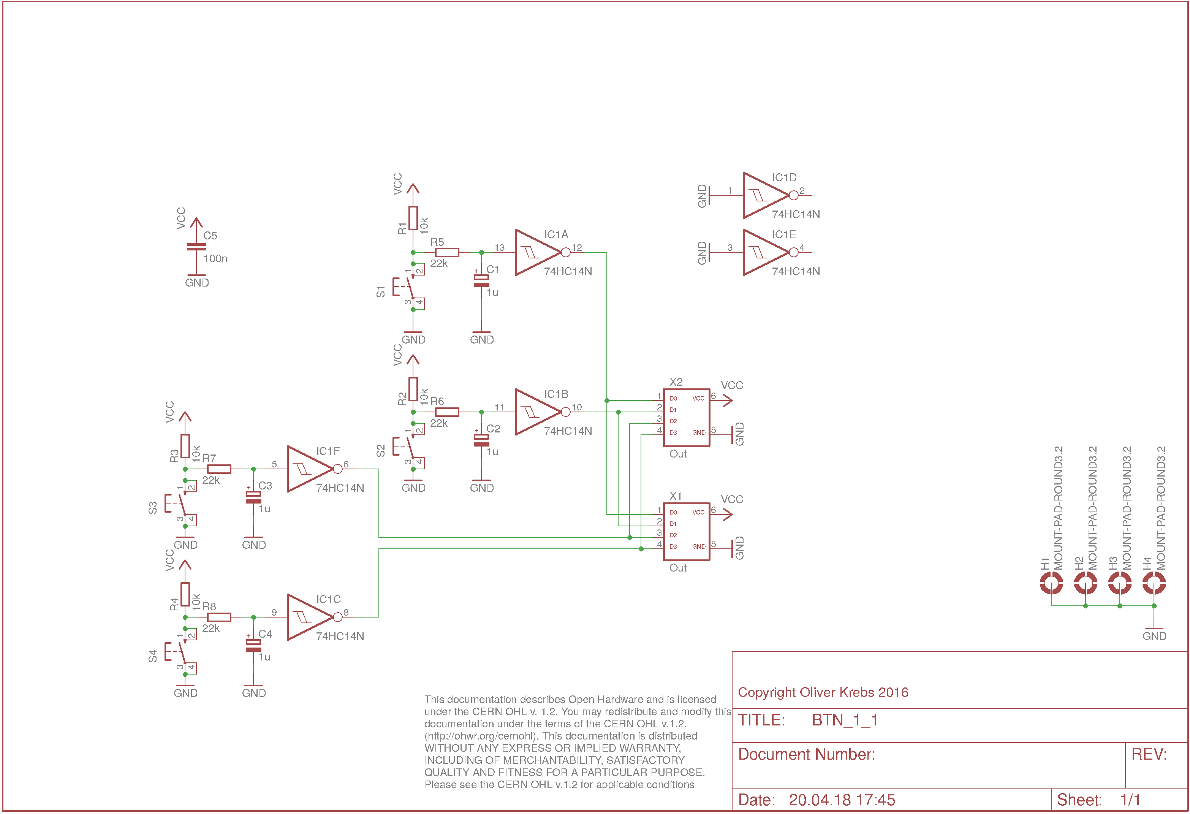
doc/BTN_1_1_sch.png
