mexdulon/tetra-Boards/doc/C12_1_0_sch.png

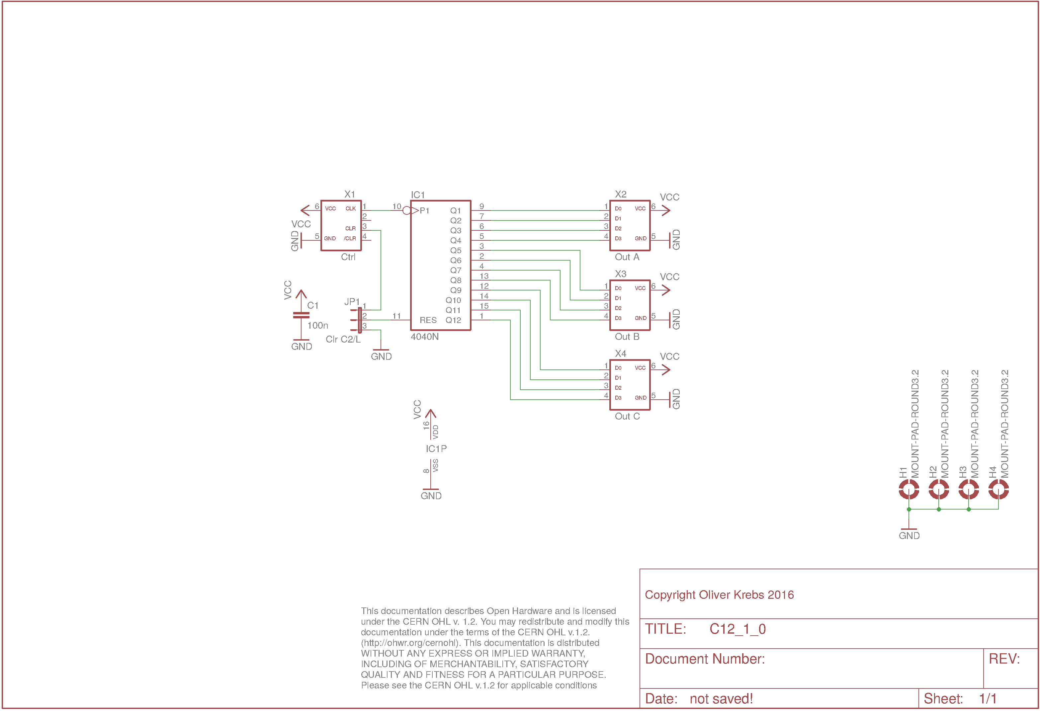
doc/C12_1_0_sch.png
