mexdulon/tetra-Boards/doc/C12_1_0_silk.png

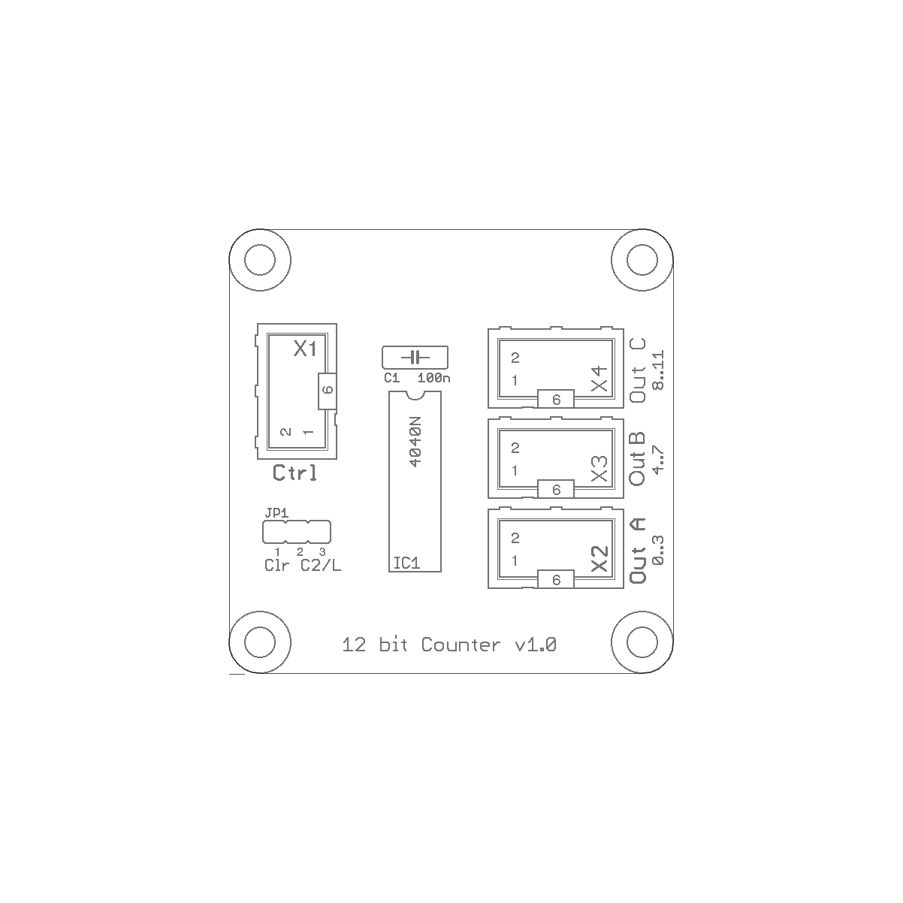
doc/C12_1_0_silk.png
