mexdulon/tetra-Boards/doc/CLK_1_1_sch.png

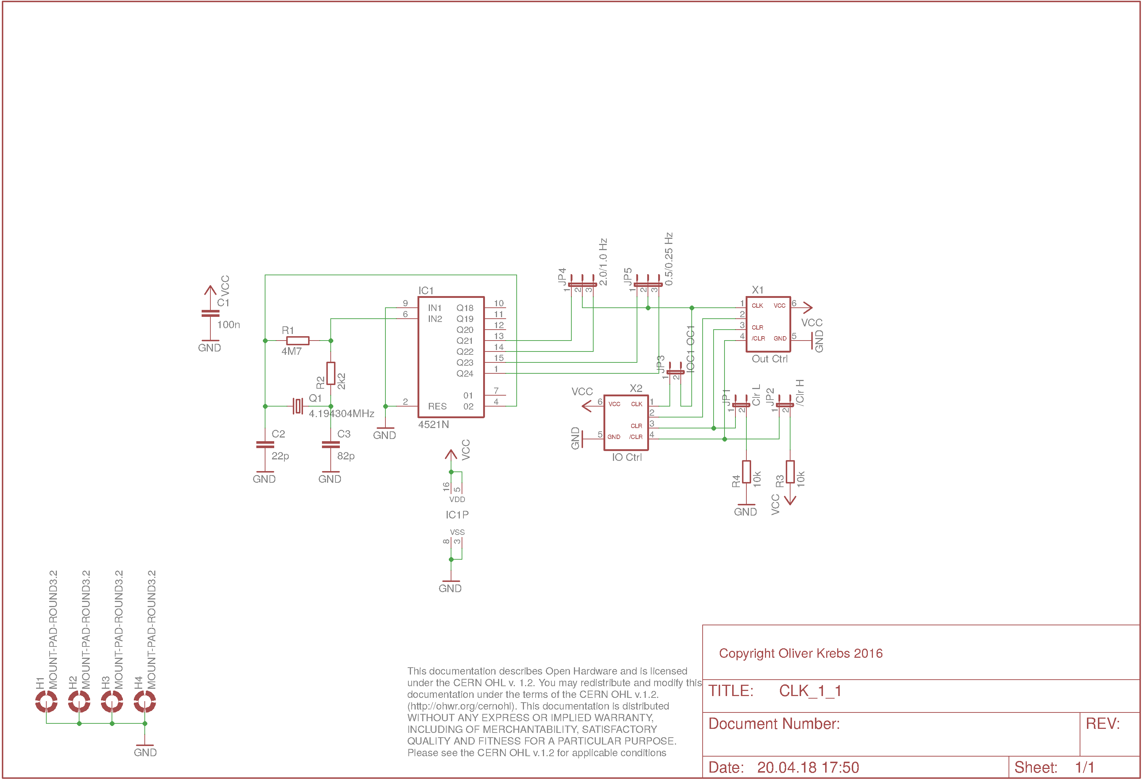
doc/CLK_1_1_sch.png
