mexdulon/tetra-Boards/doc/CMP_1_1_sch.png

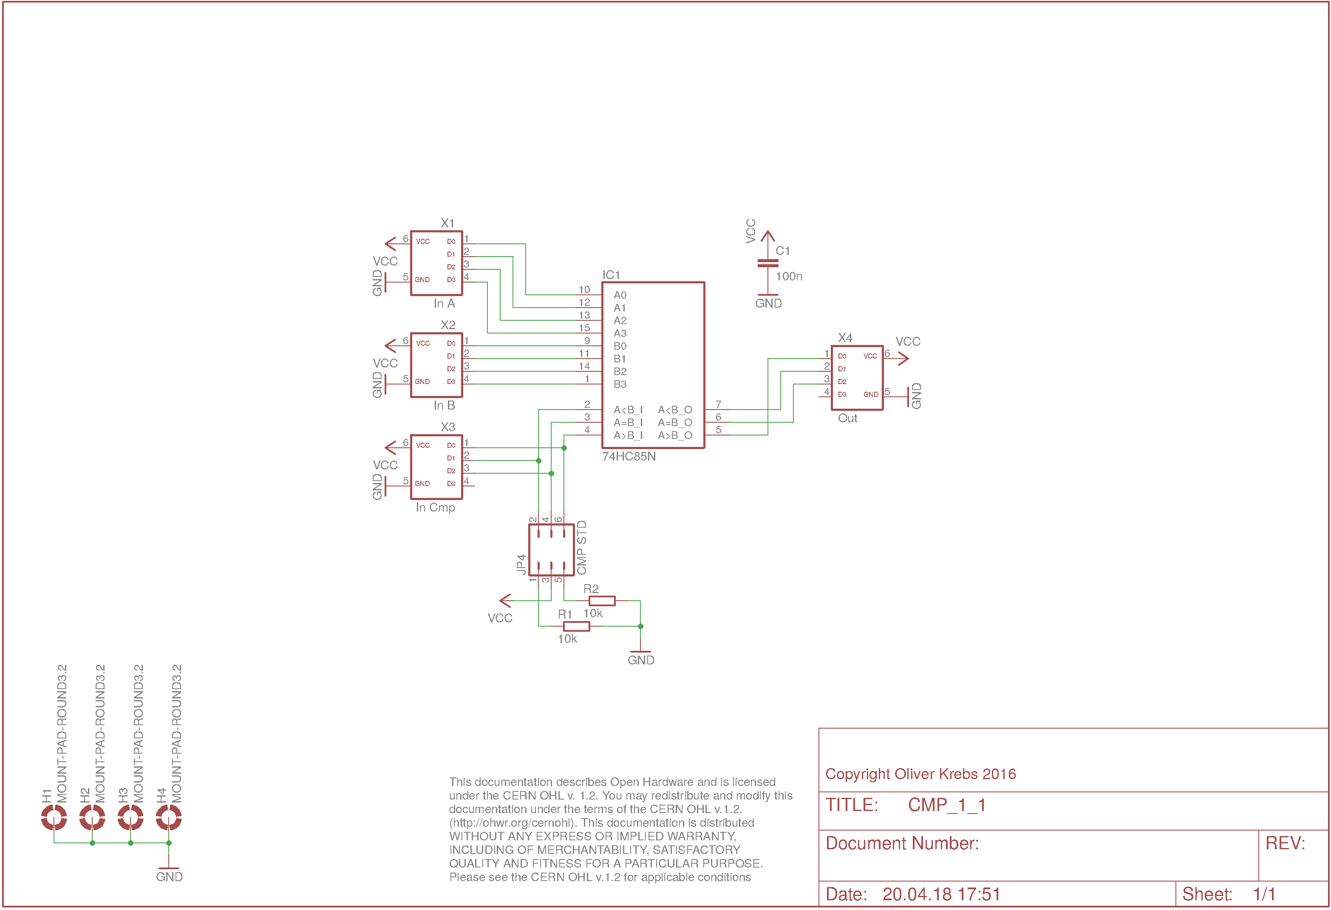
doc/CMP_1_1_sch.png
