mexdulon/tetra-Boards/doc/CNT_1_0_sch.png

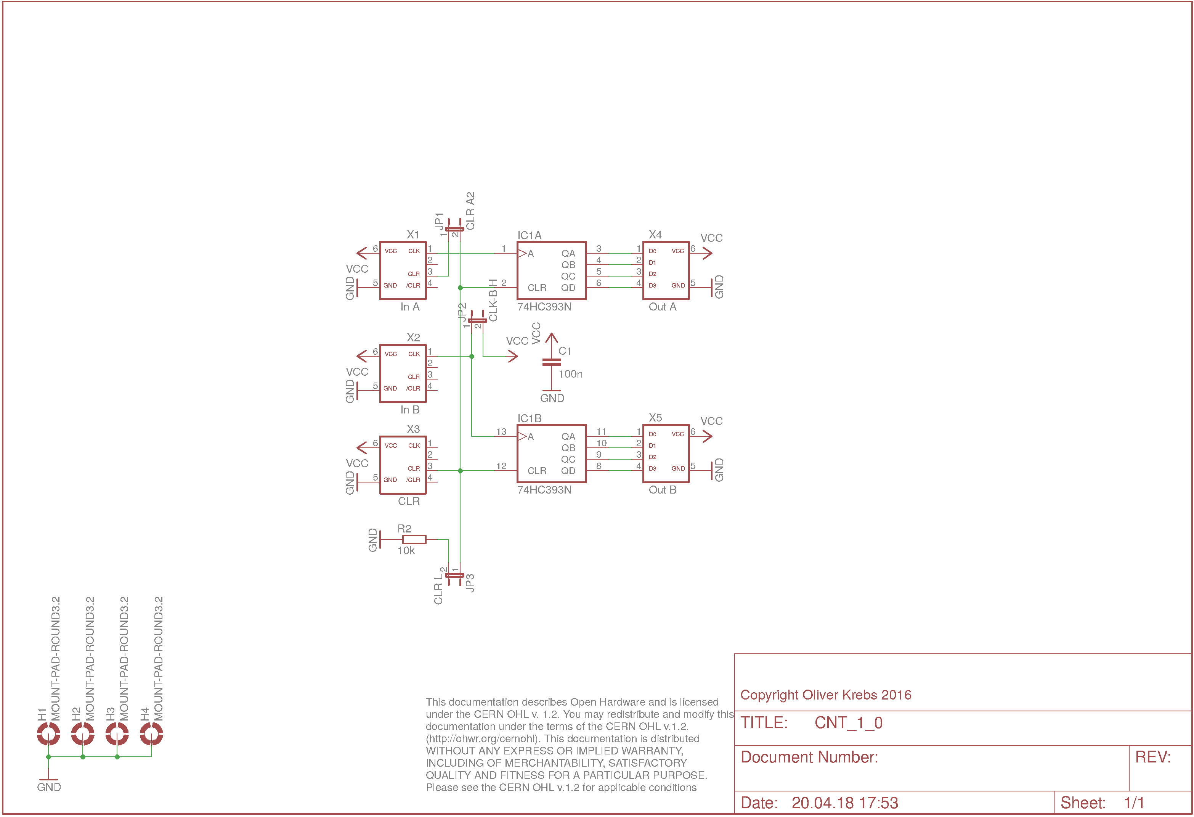
doc/CNT_1_0_sch.png
