mexdulon/tetra-Boards/doc/CNT_1_1_sch.png

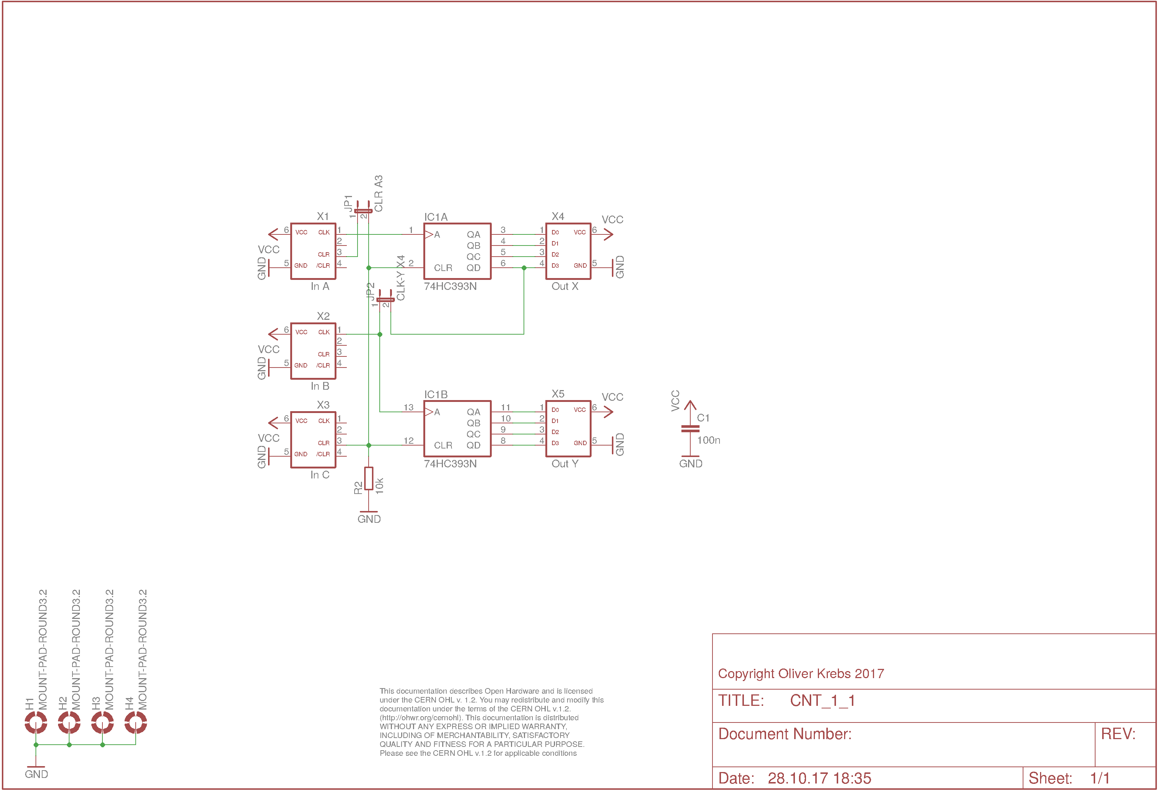
doc/CNT_1_1_sch.png
