mexdulon/tetra-Boards/doc/CNT_1_1_silk.png

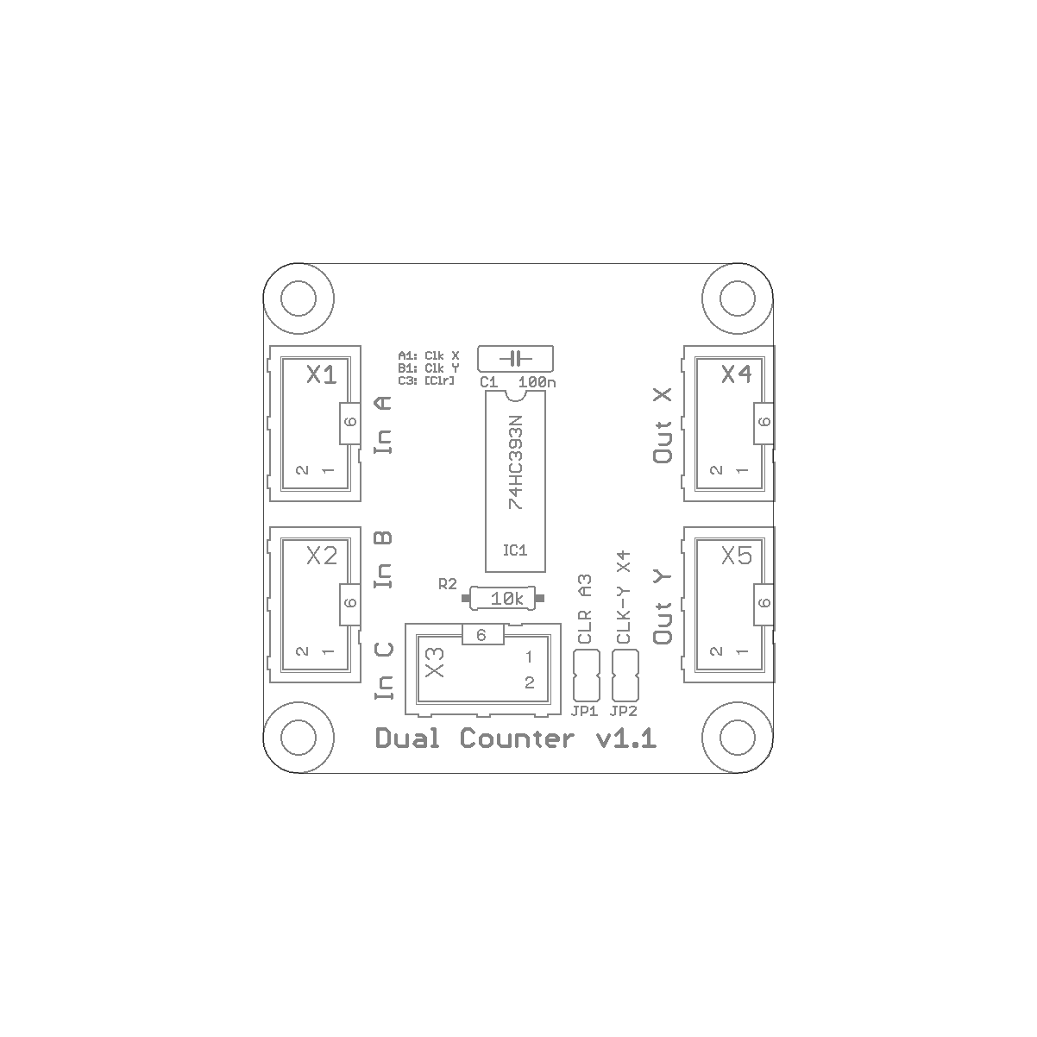
doc/CNT_1_1_silk.png
