mexdulon/tetra-Boards/doc/D12_1_0_sch.png

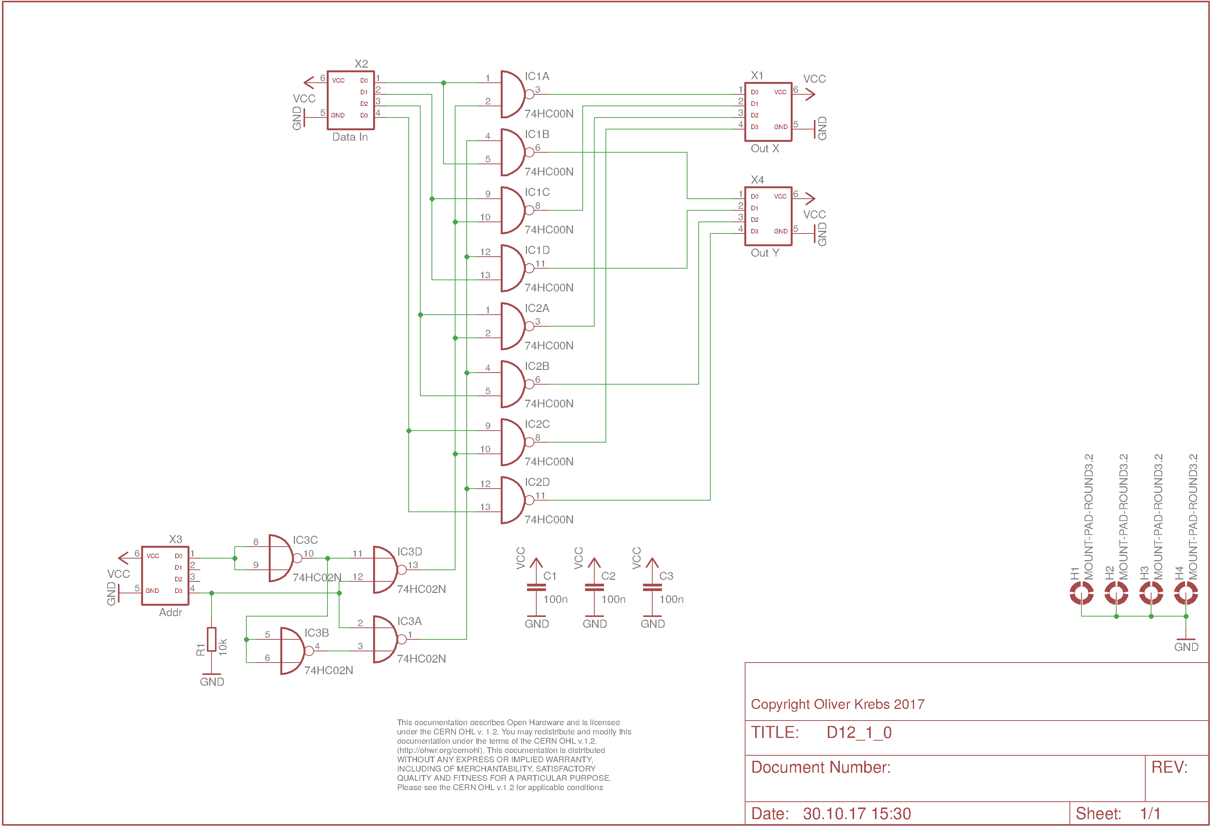
doc/D12_1_0_sch.png
