mexdulon/tetra-Boards/doc/D12_1_0_silk.png

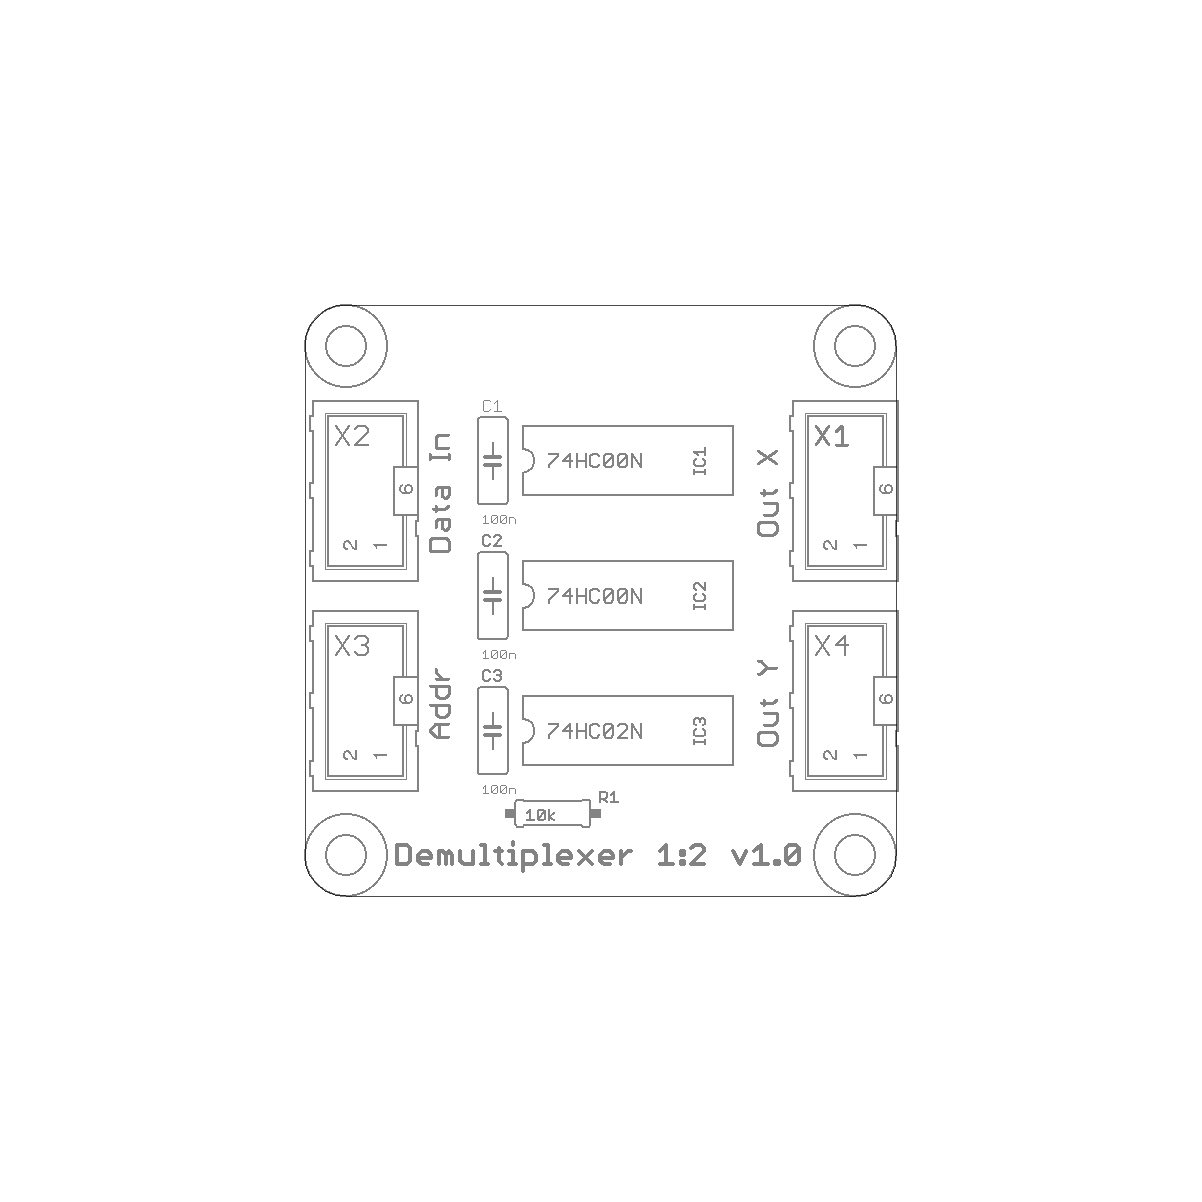
doc/D12_1_0_silk.png
