mexdulon/tetra-Boards/doc/D14_1_0_sch.png

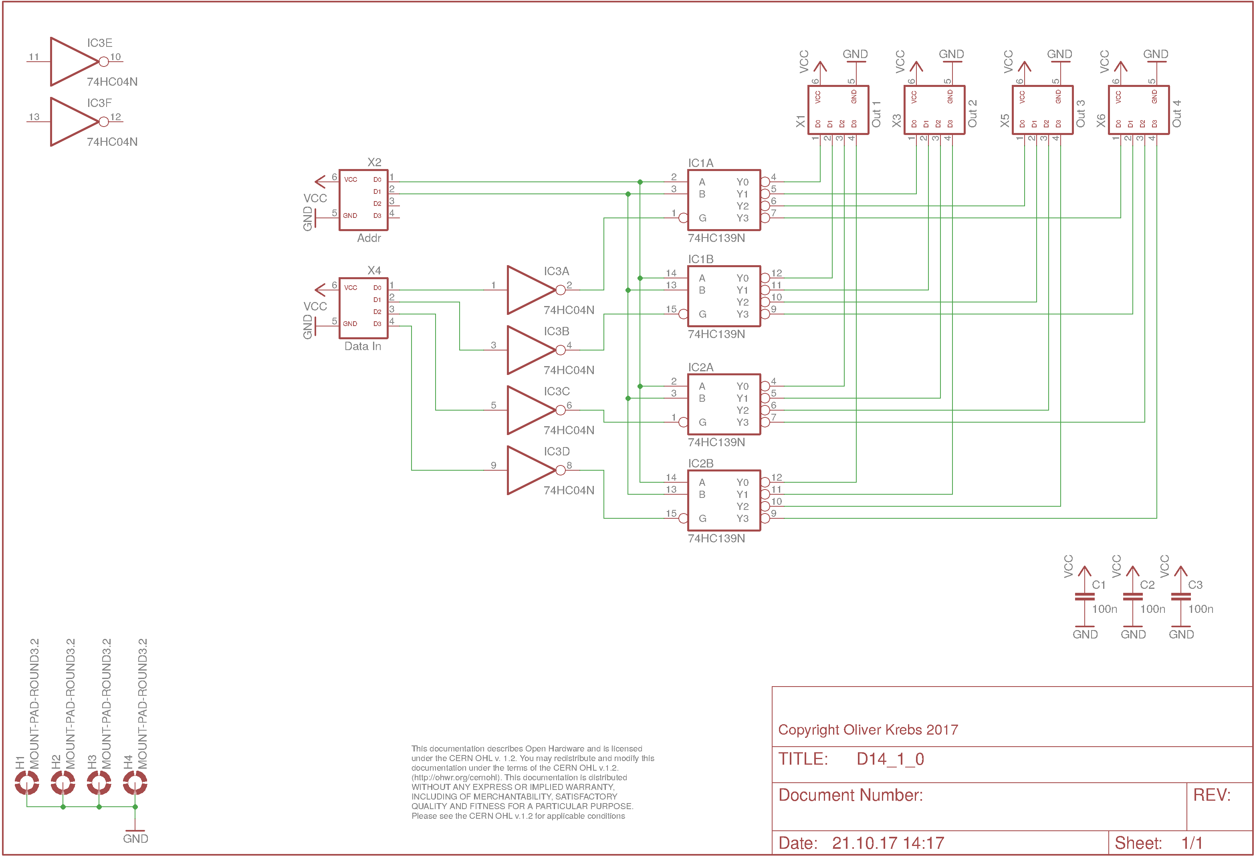
doc/D14_1_0_sch.png
