mexdulon/tetra-Boards/doc/D14_1_0_silk.png

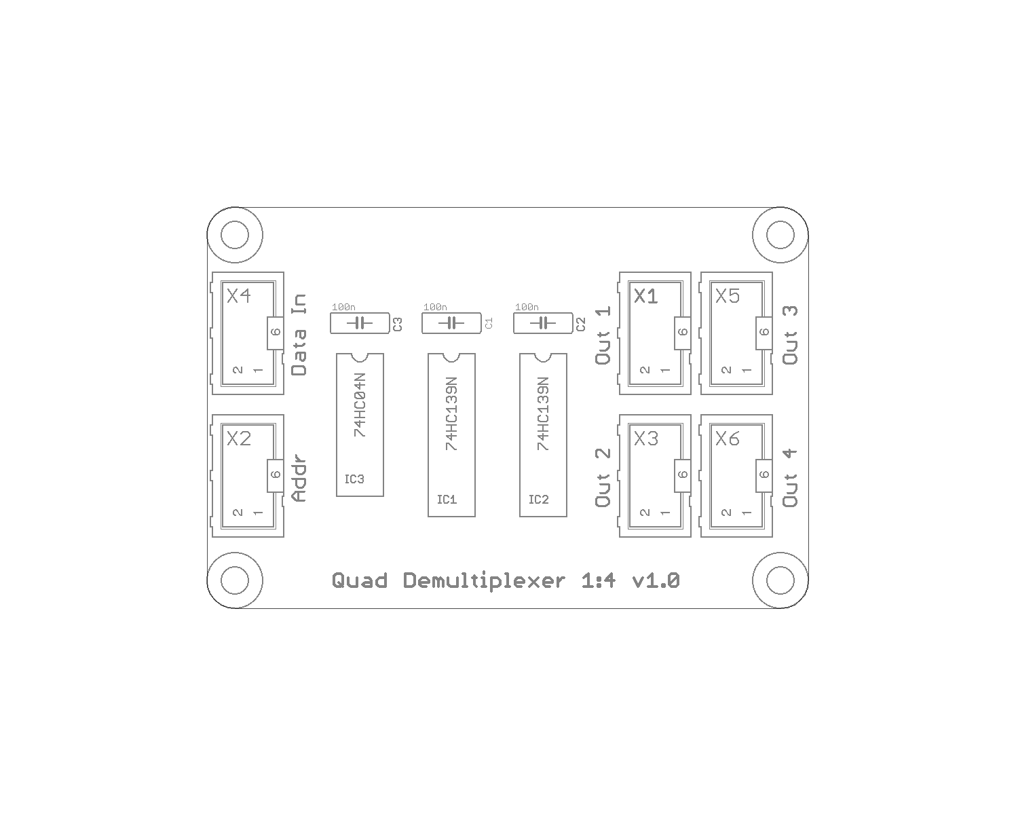
doc/D14_1_0_silk.png
