mexdulon/tetra-Boards/doc/D18_1_0_sch.png

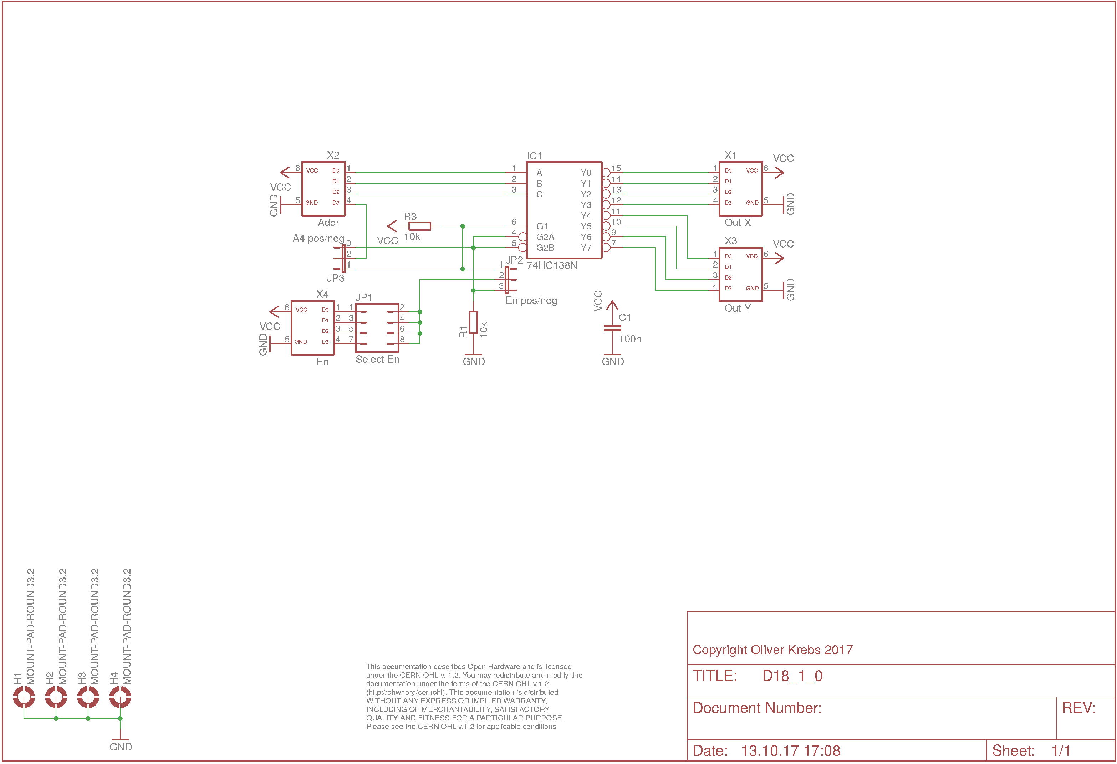
doc/D18_1_0_sch.png
