mexdulon/tetra-Boards/doc/D18_1_0_silk.png

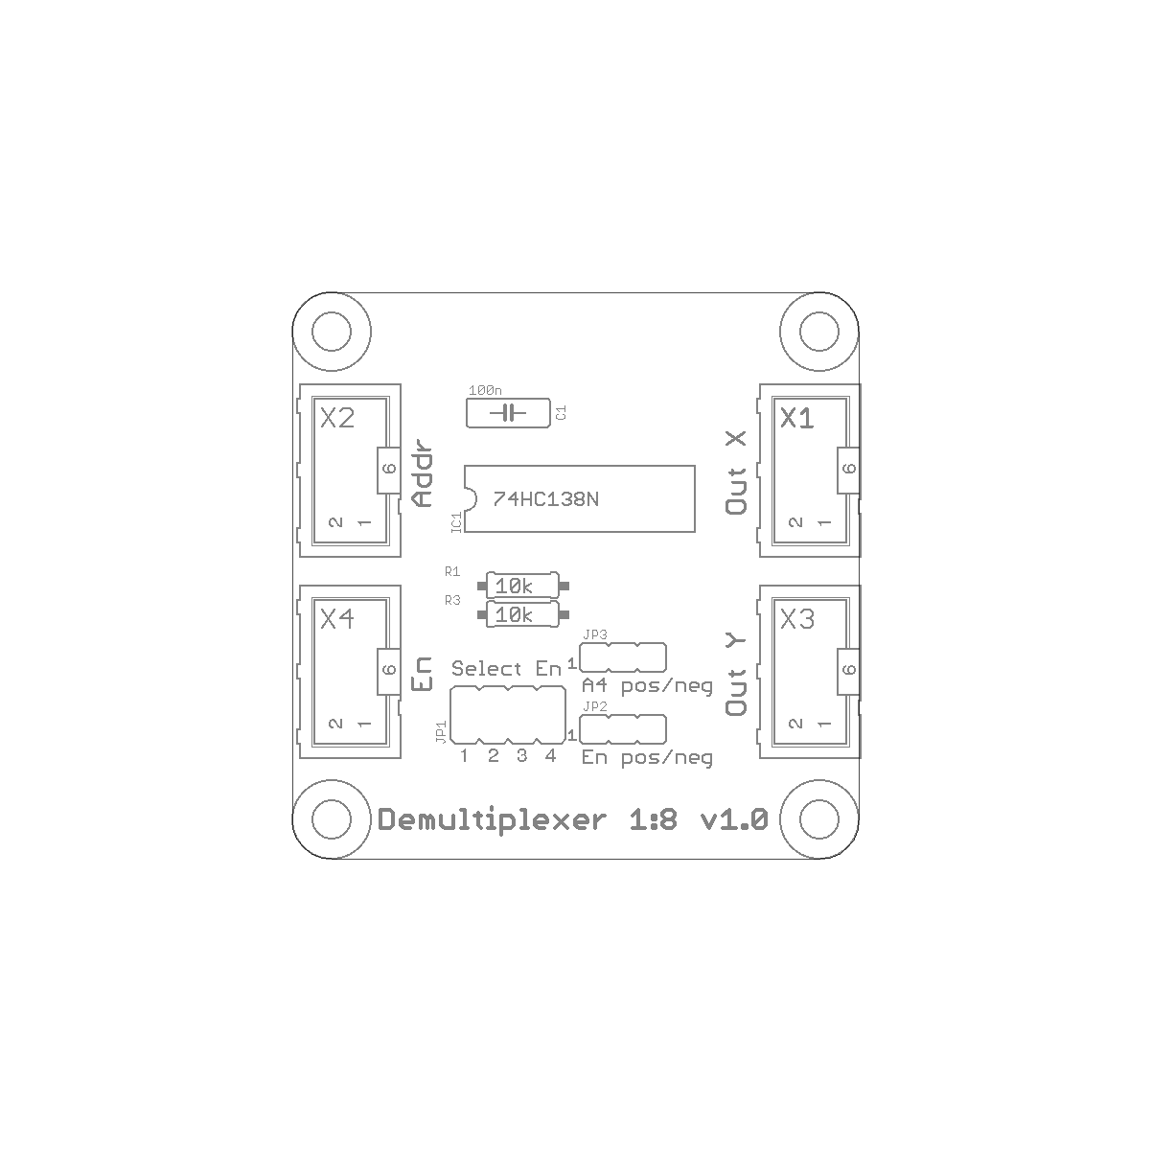
doc/D18_1_0_silk.png
