mexdulon/tetra-Boards/doc/D18_1_1_silk.png

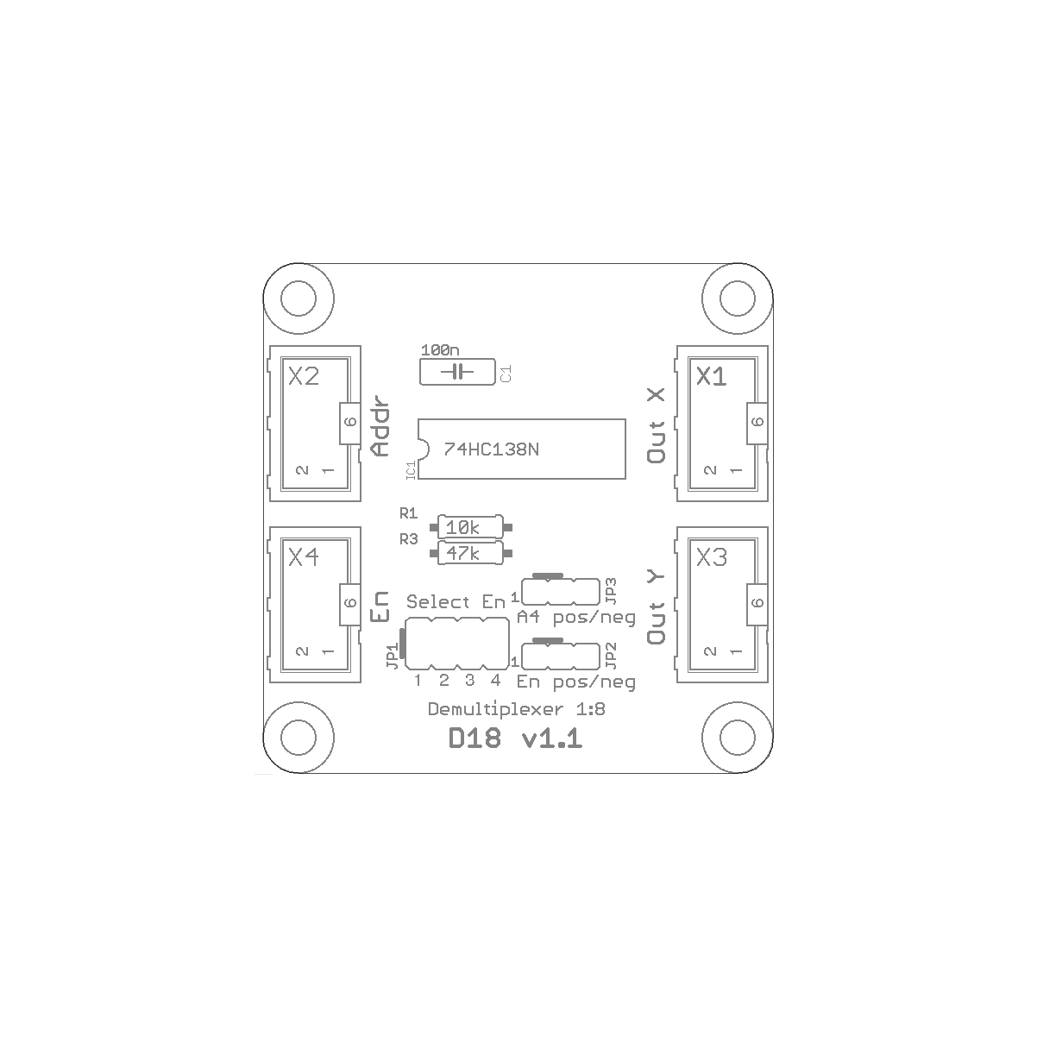
doc/D18_1_1_silk.png
