mexdulon/tetra-Boards/doc/DAC_1_0_sch.png

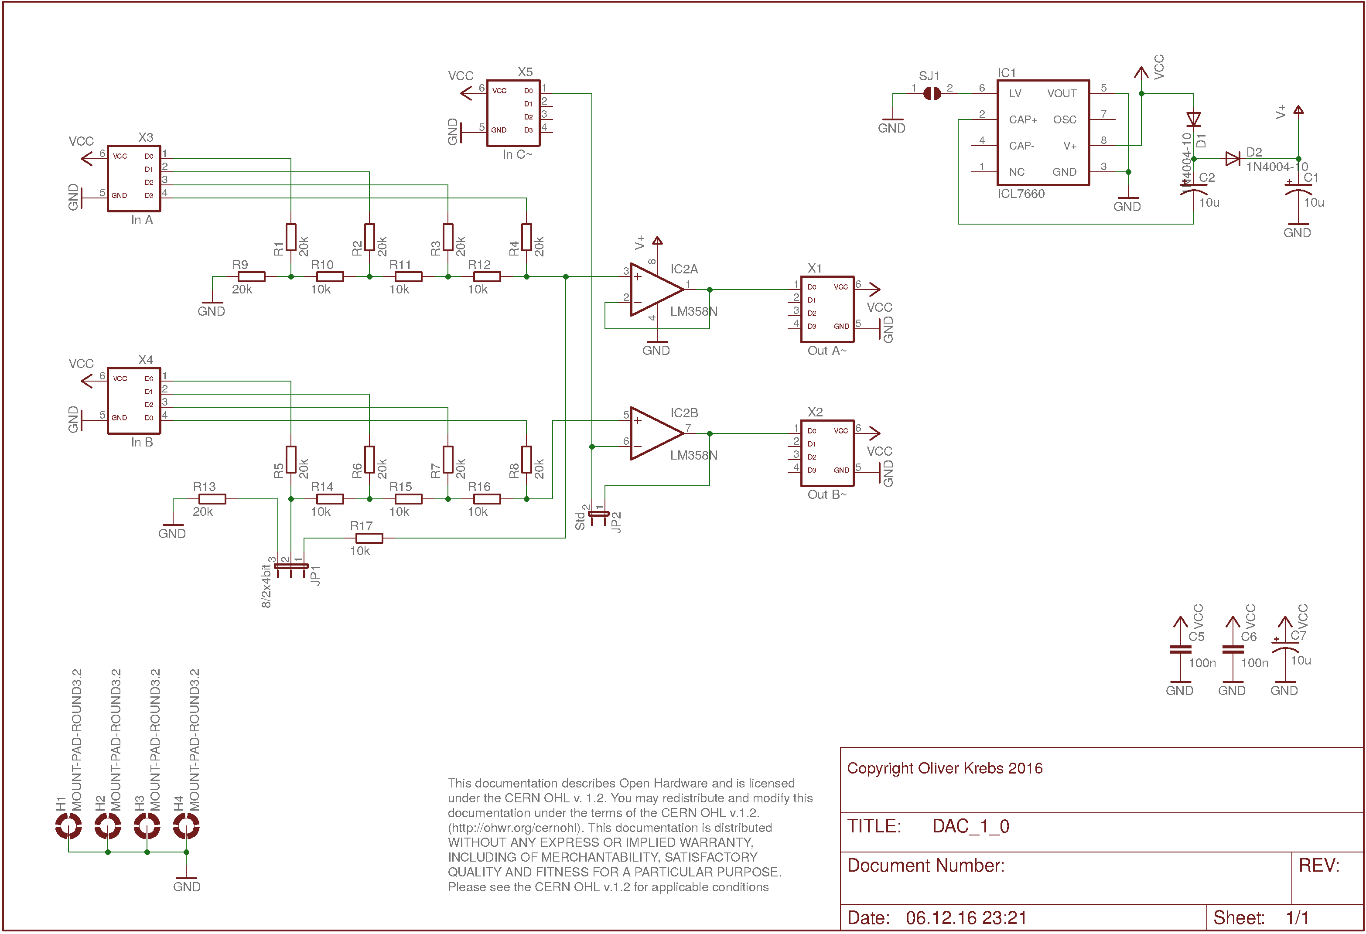
doc/DAC_1_0_sch.png
