mexdulon/tetra-Boards/doc/DEC_1_0_sch.png

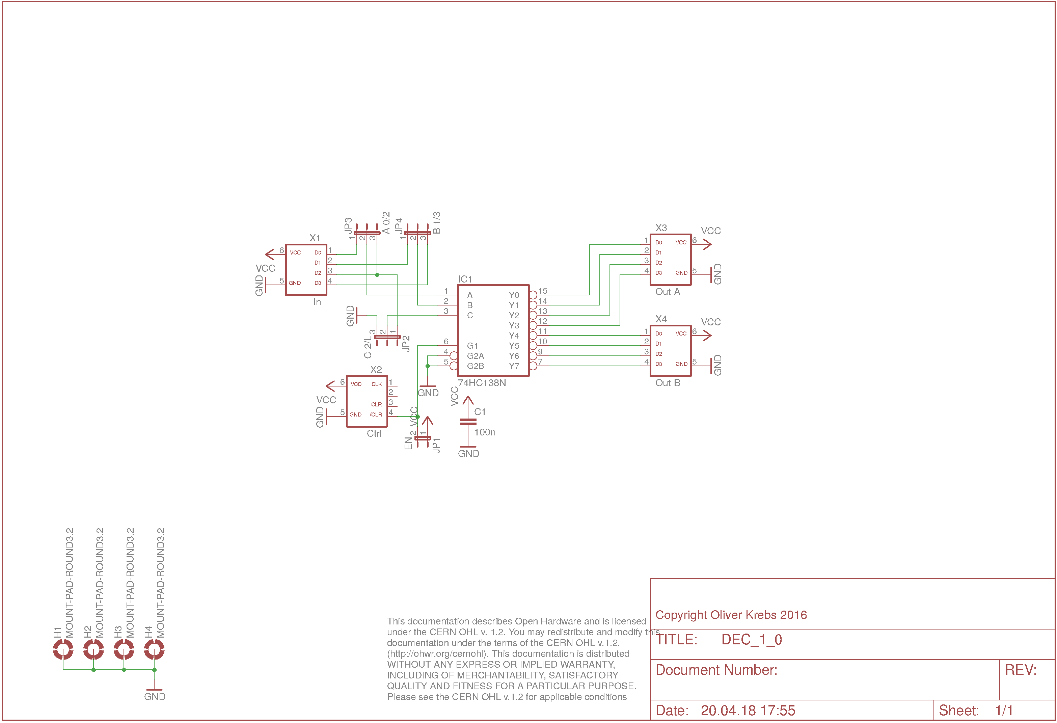
doc/DEC_1_0_sch.png
