mexdulon/tetra-Boards/doc/DFF_1_0_sch.png

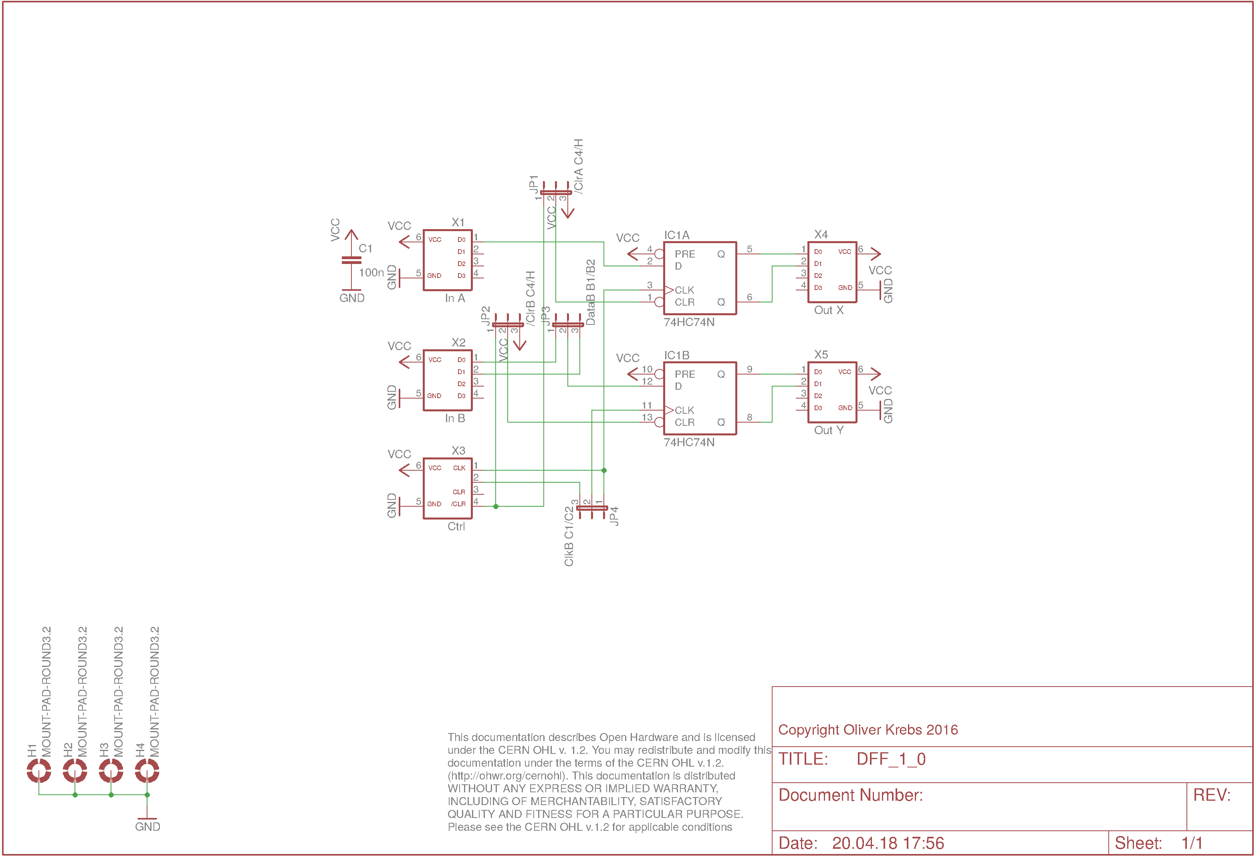
doc/DFF_1_0_sch.png
