mexdulon/tetra-Boards/doc/DIP_1_0_sch.png

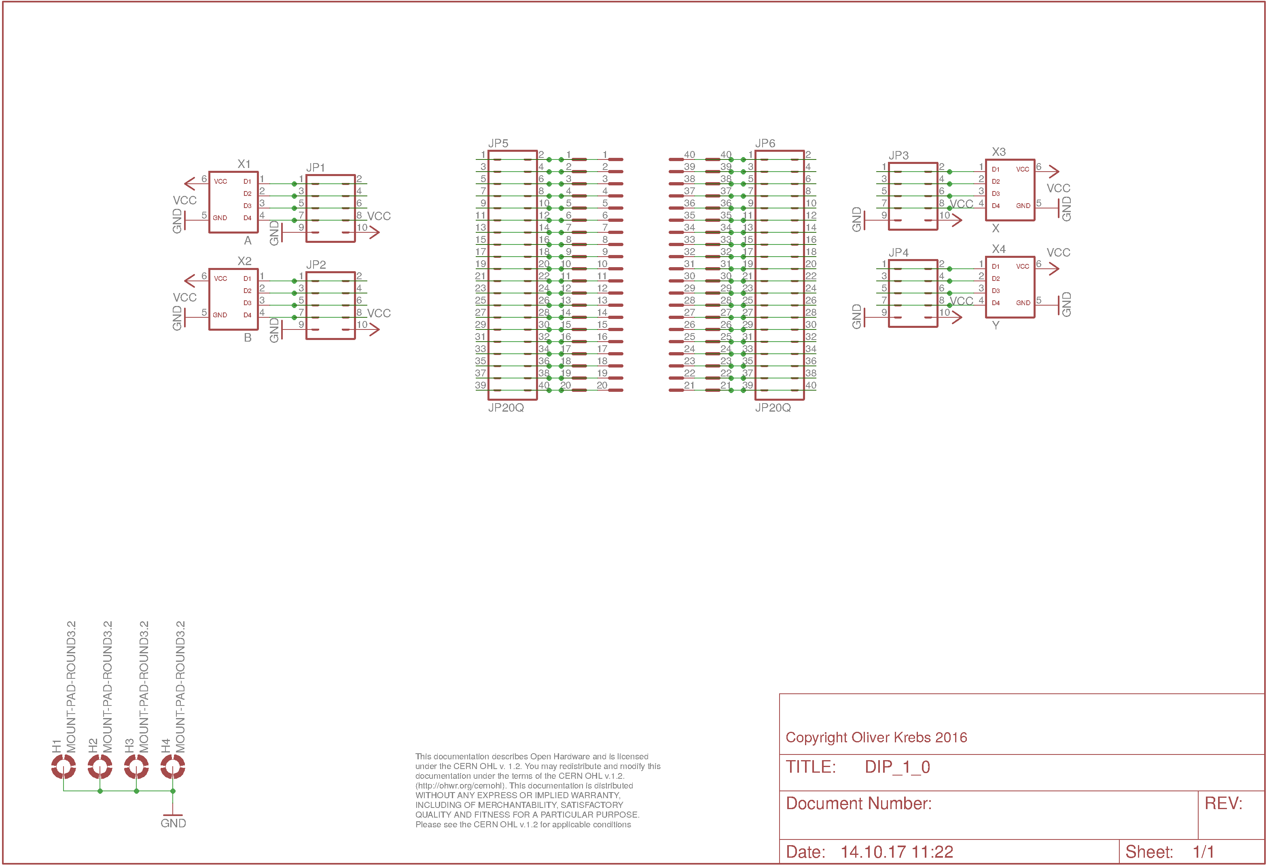
doc/DIP_1_0_sch.png
