mexdulon/tetra-Boards/doc/DIP_1_0_silk.png

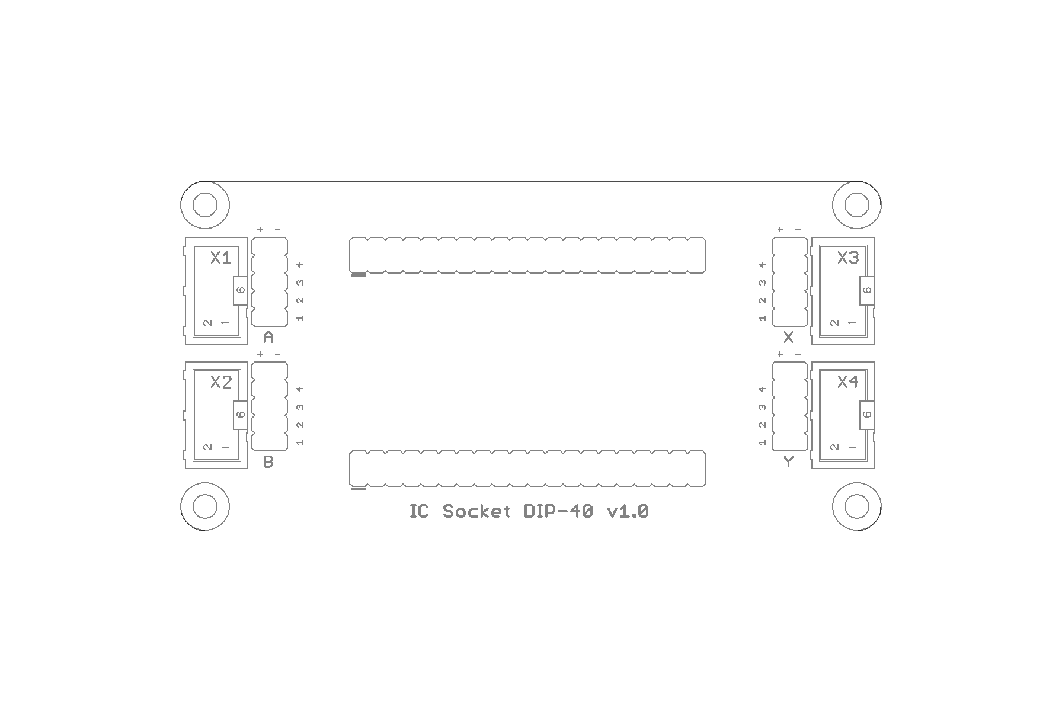
doc/DIP_1_0_silk.png
