mexdulon/tetra-Boards/doc/DLS_1_0_sch.png

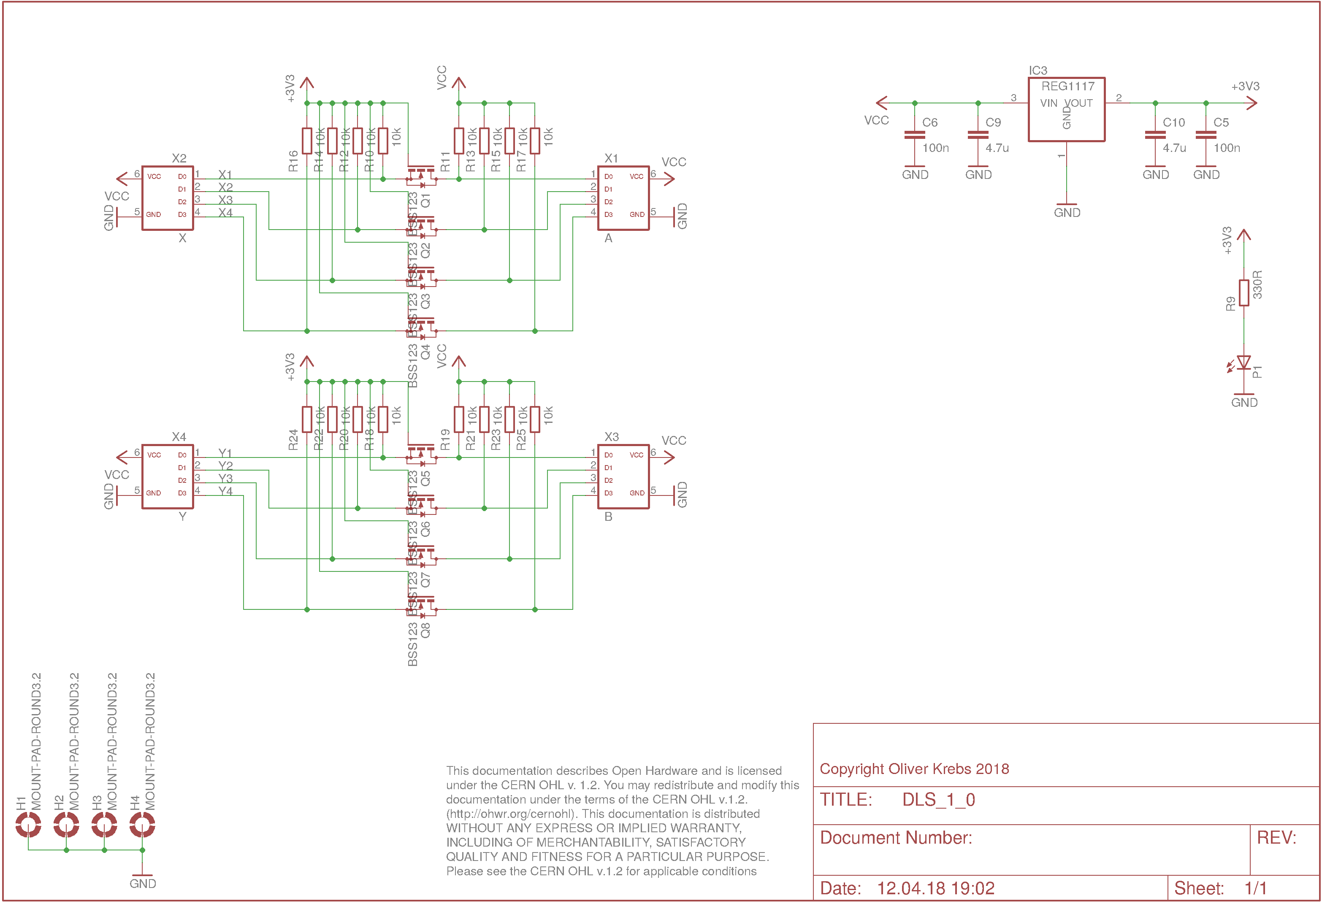
doc/DLS_1_0_sch.png
