mexdulon/tetra-Boards/doc/DLS_1_0_silk.png

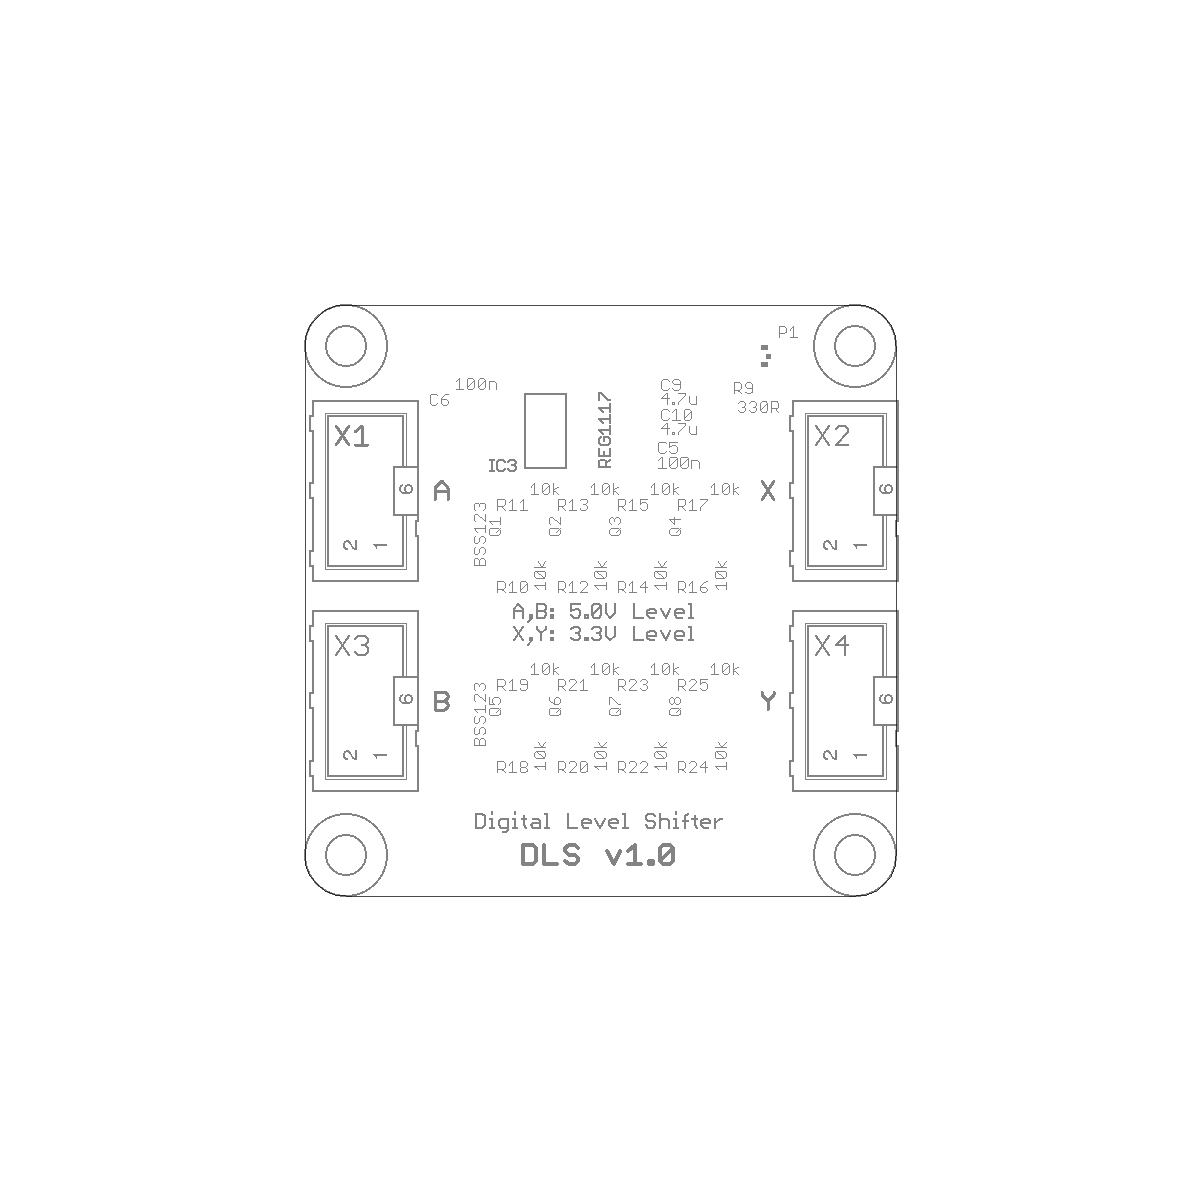
doc/DLS_1_0_silk.png
