mexdulon/tetra-Boards/doc/DLY_1_0_sch.png

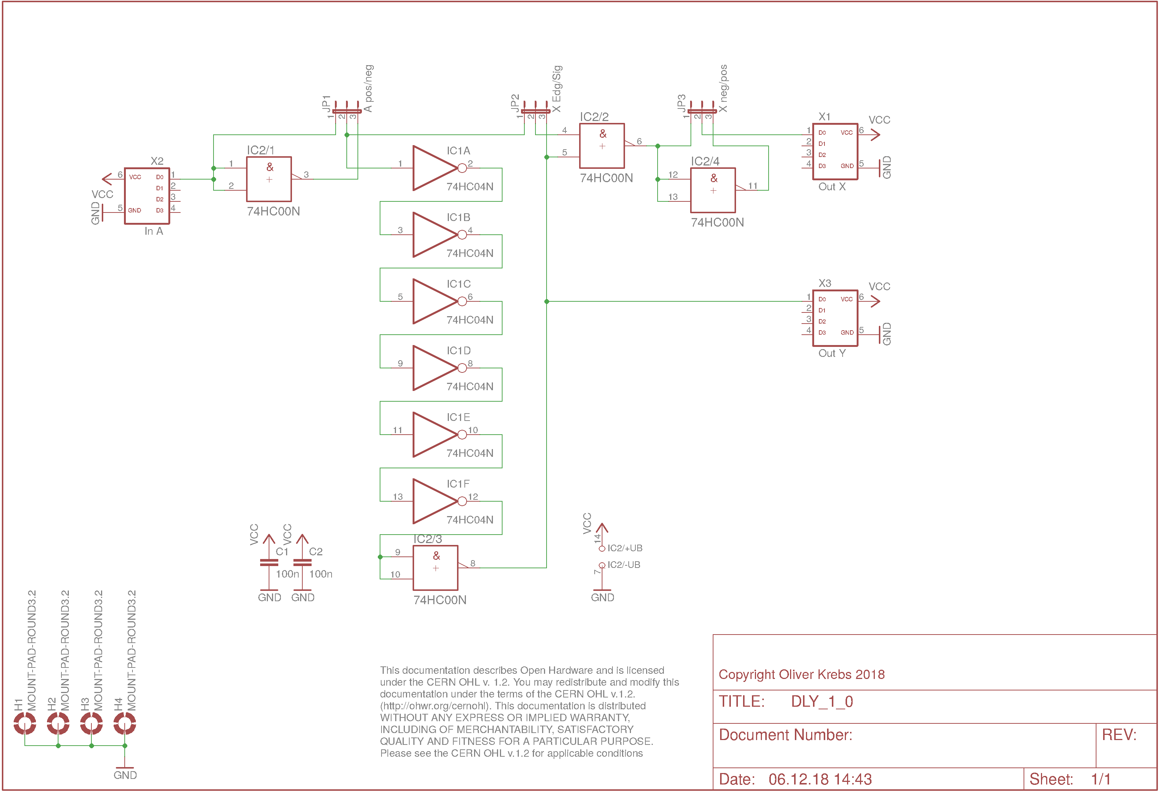
doc/DLY_1_0_sch.png
