mexdulon/tetra-Boards/doc/DMD_1_0_sch.png

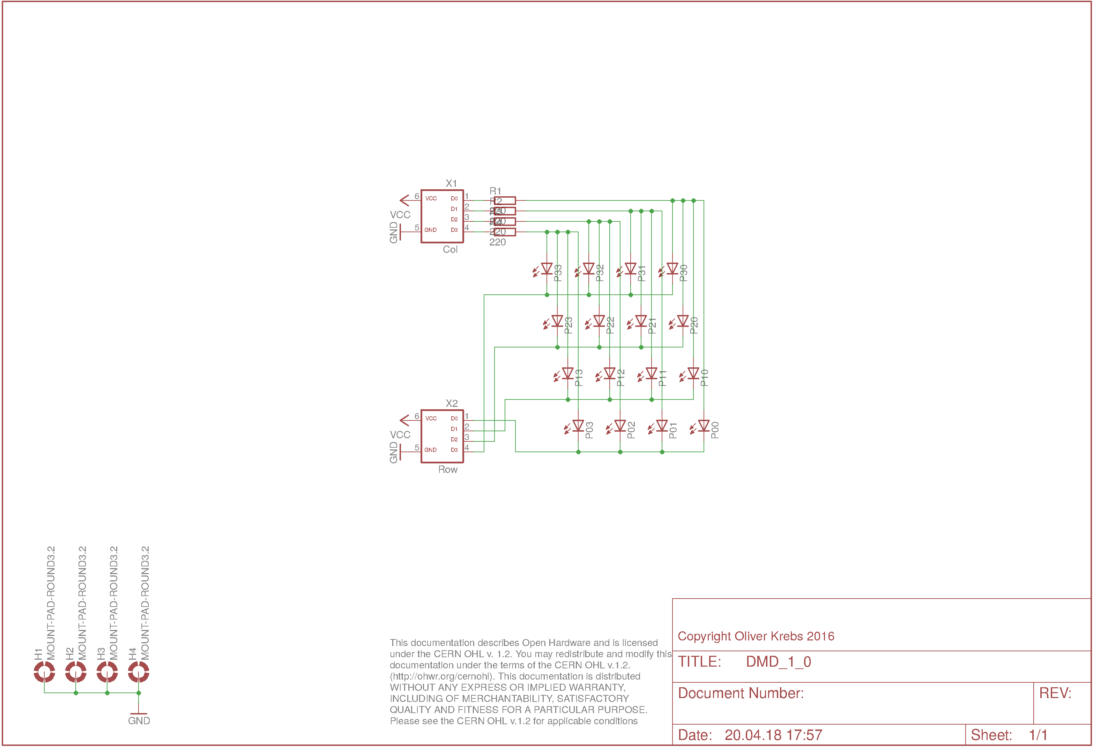
doc/DMD_1_0_sch.png
