mexdulon/tetra-Boards/doc/DMD_1_0_silk.png

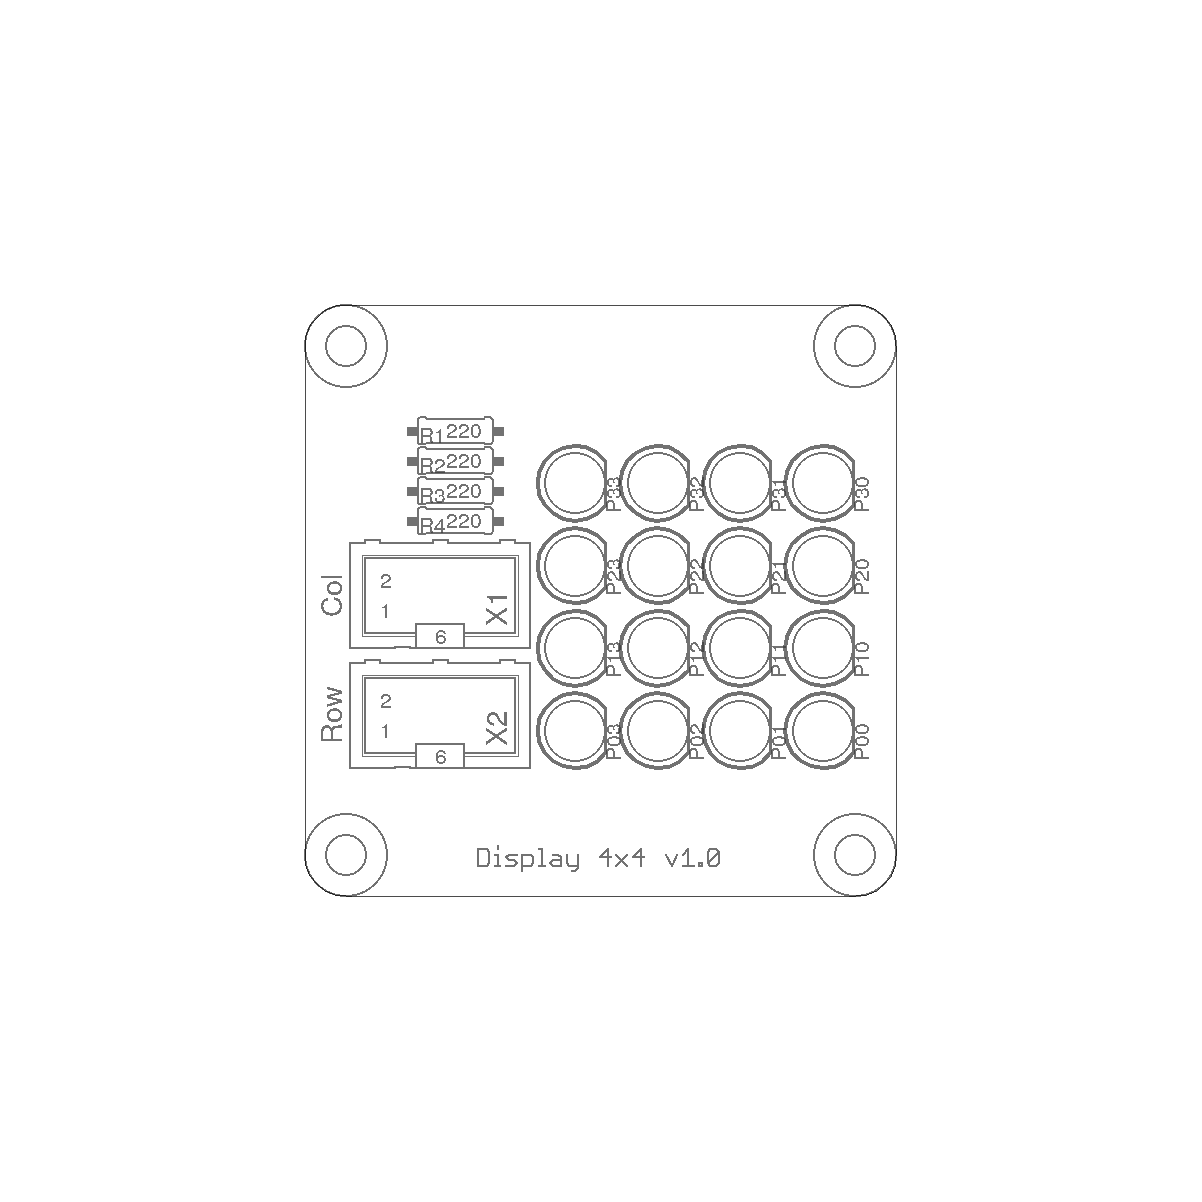
doc/DMD_1_0_silk.png
