mexdulon/tetra-Boards/doc/DMX_1_0_sch.png

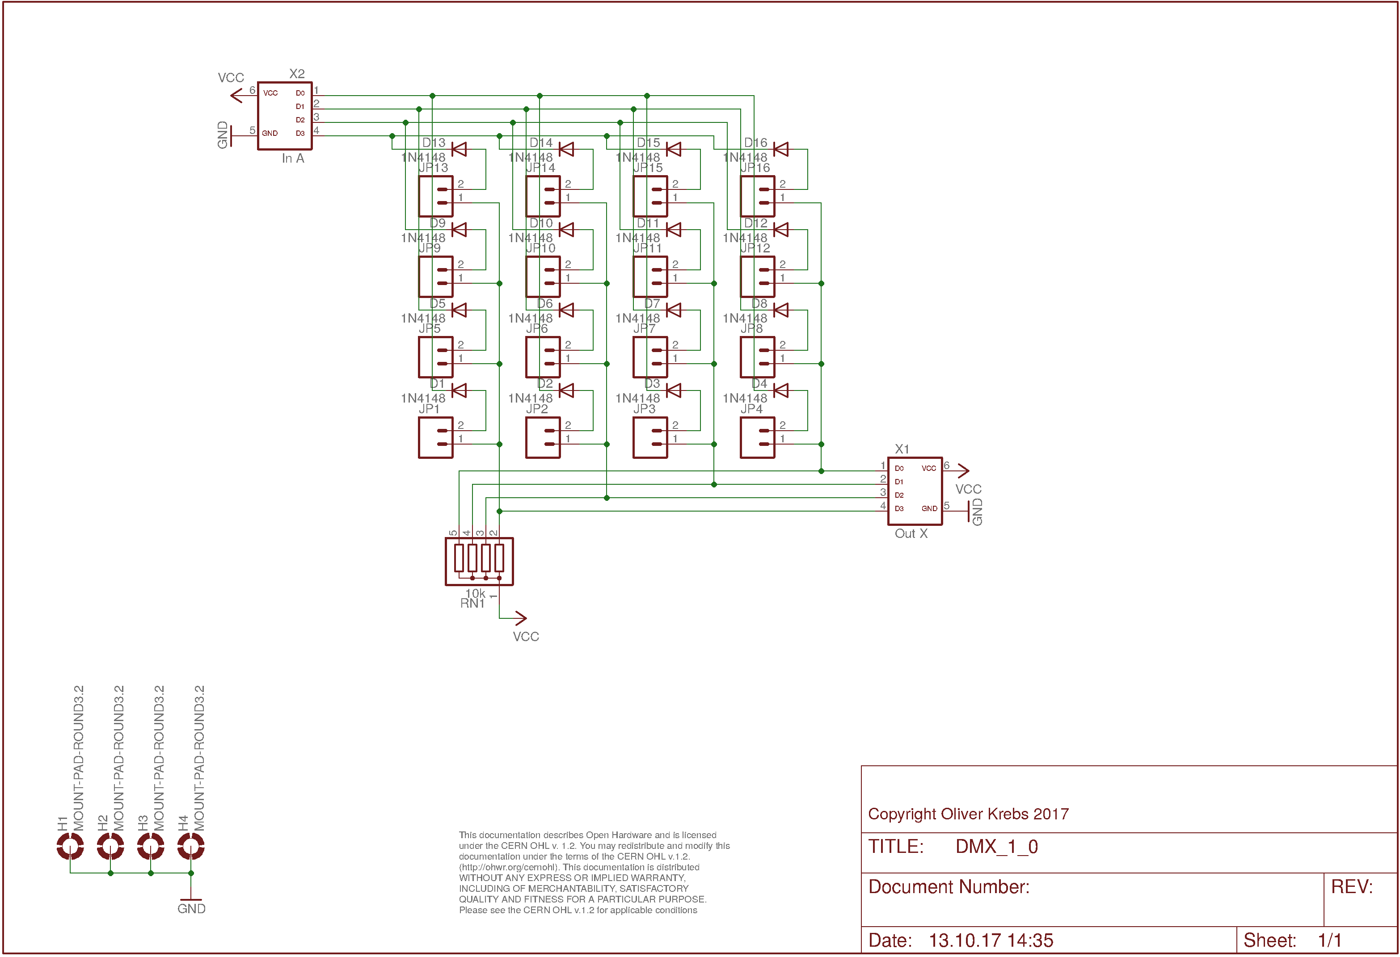
doc/DMX_1_0_sch.png
