mexdulon/tetra-Boards/doc/ENC_1_1_sch.png

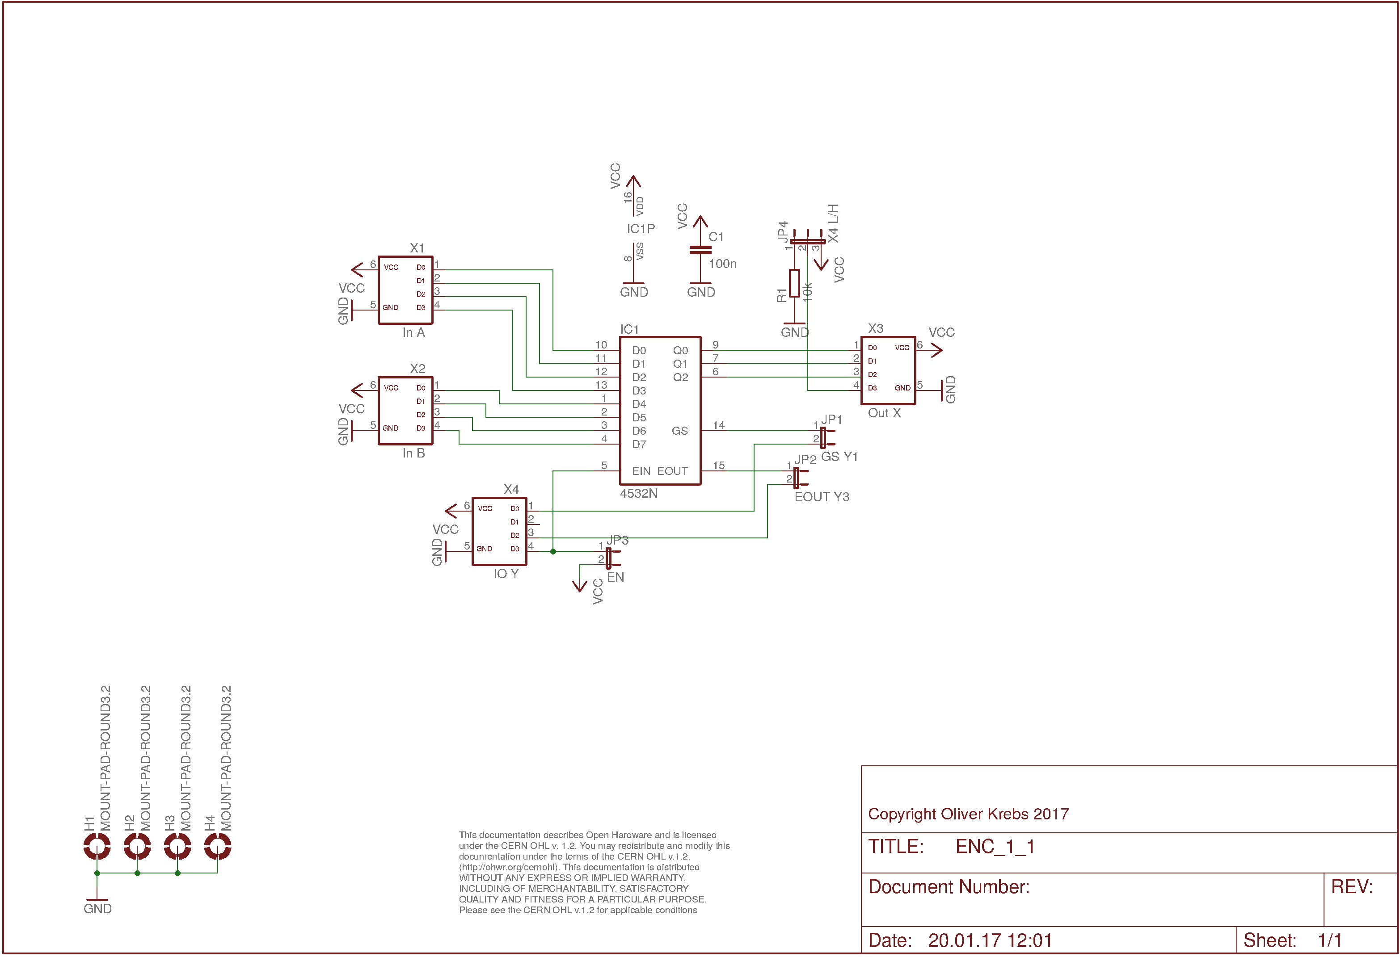
doc/ENC_1_1_sch.png
