mexdulon/tetra-Boards/doc/FET_1_0_sch.png

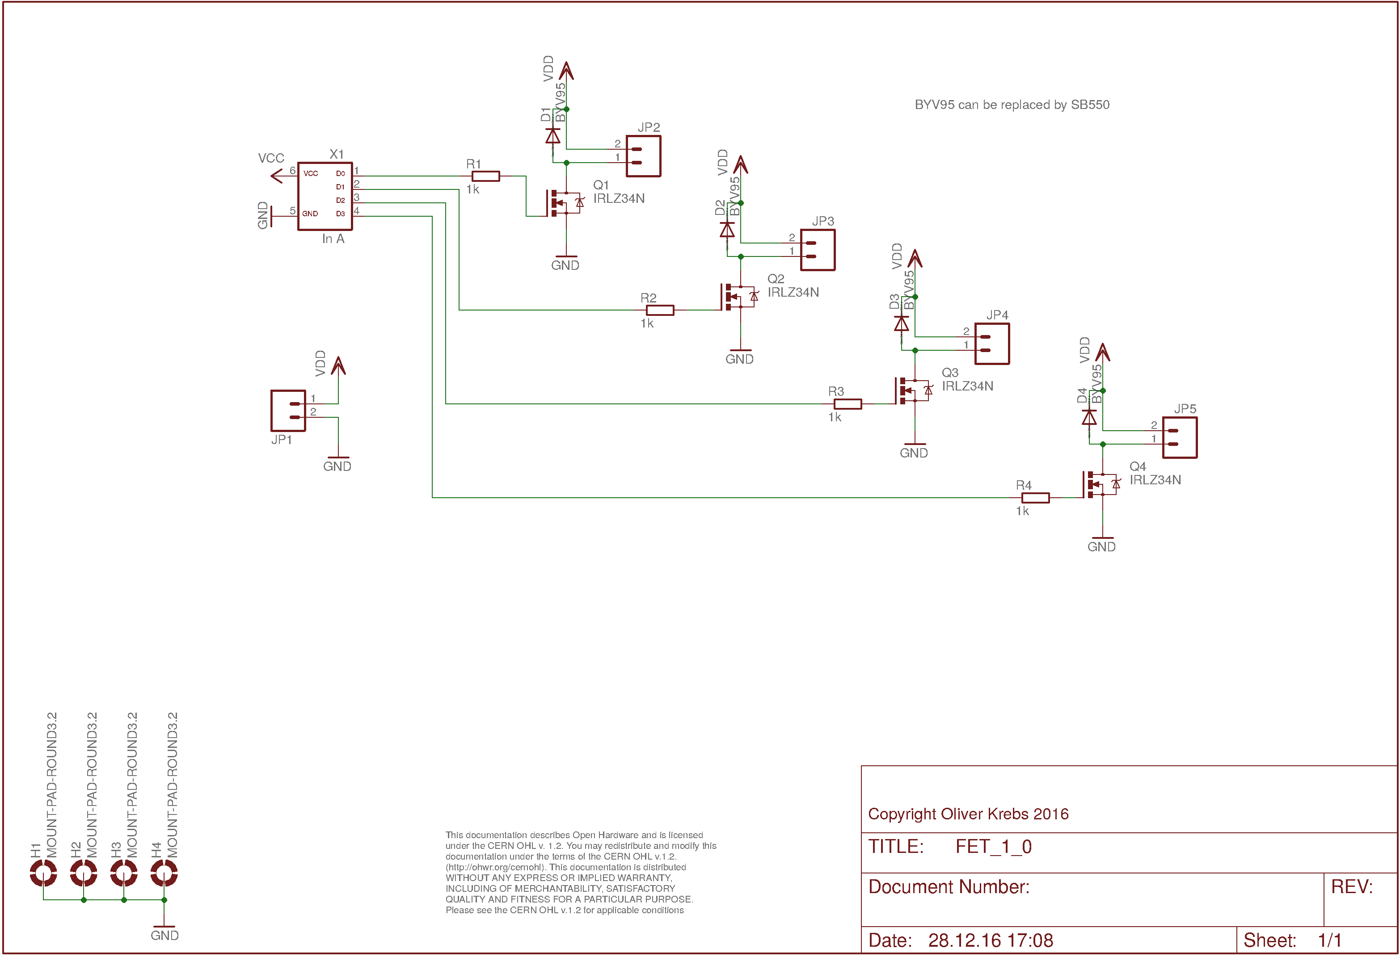
doc/FET_1_0_sch.png
