mexdulon/tetra-Boards/doc/FET_1_0_silk.png

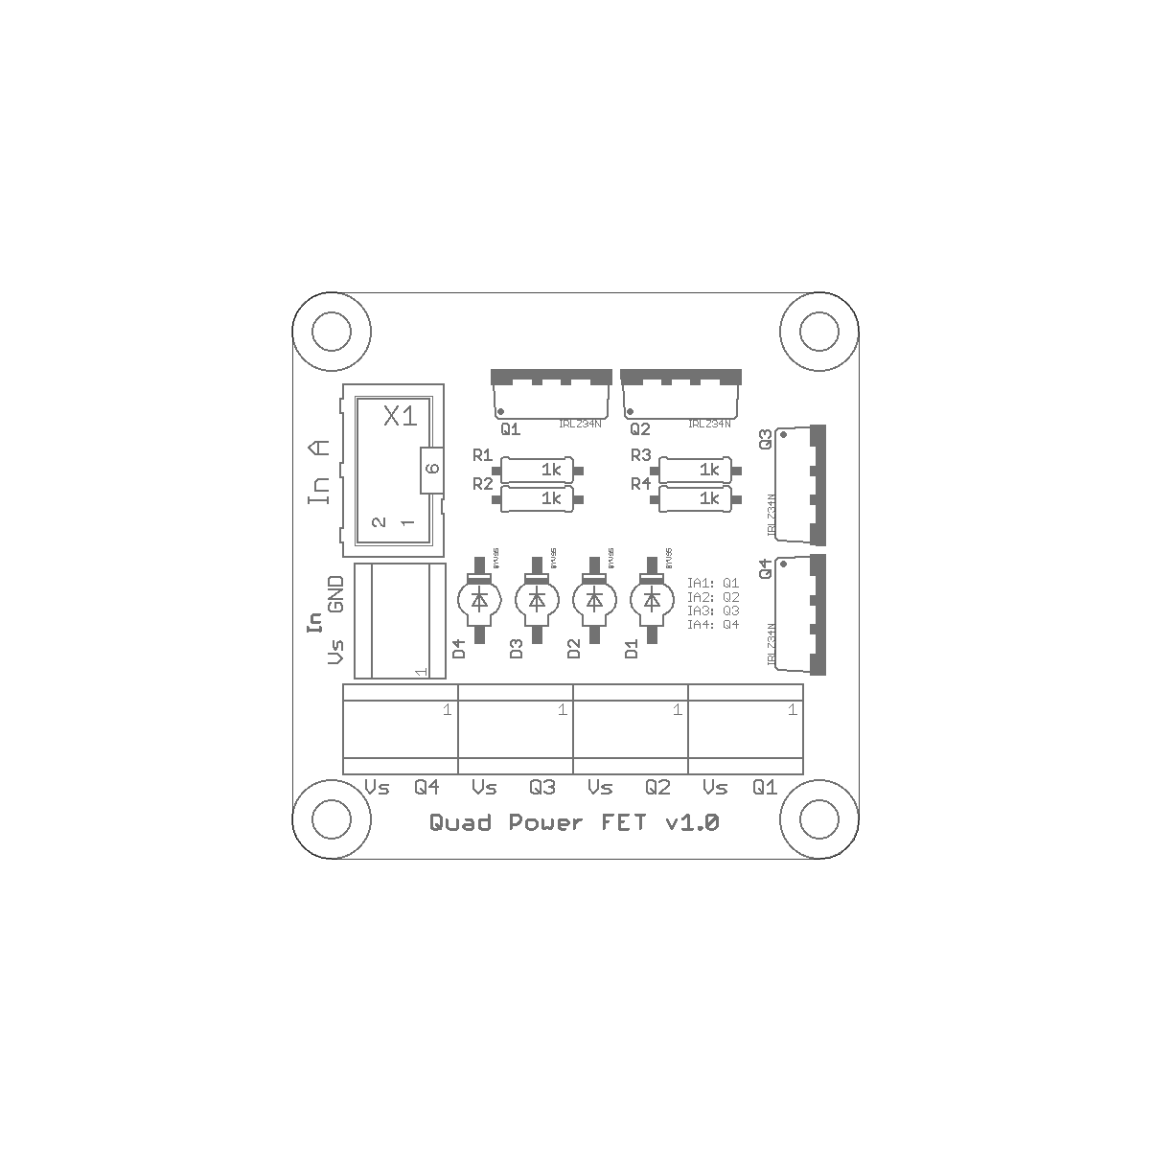
doc/FET_1_0_silk.png
