mexdulon/tetra-Boards/doc/HPF_1_0_sch.png

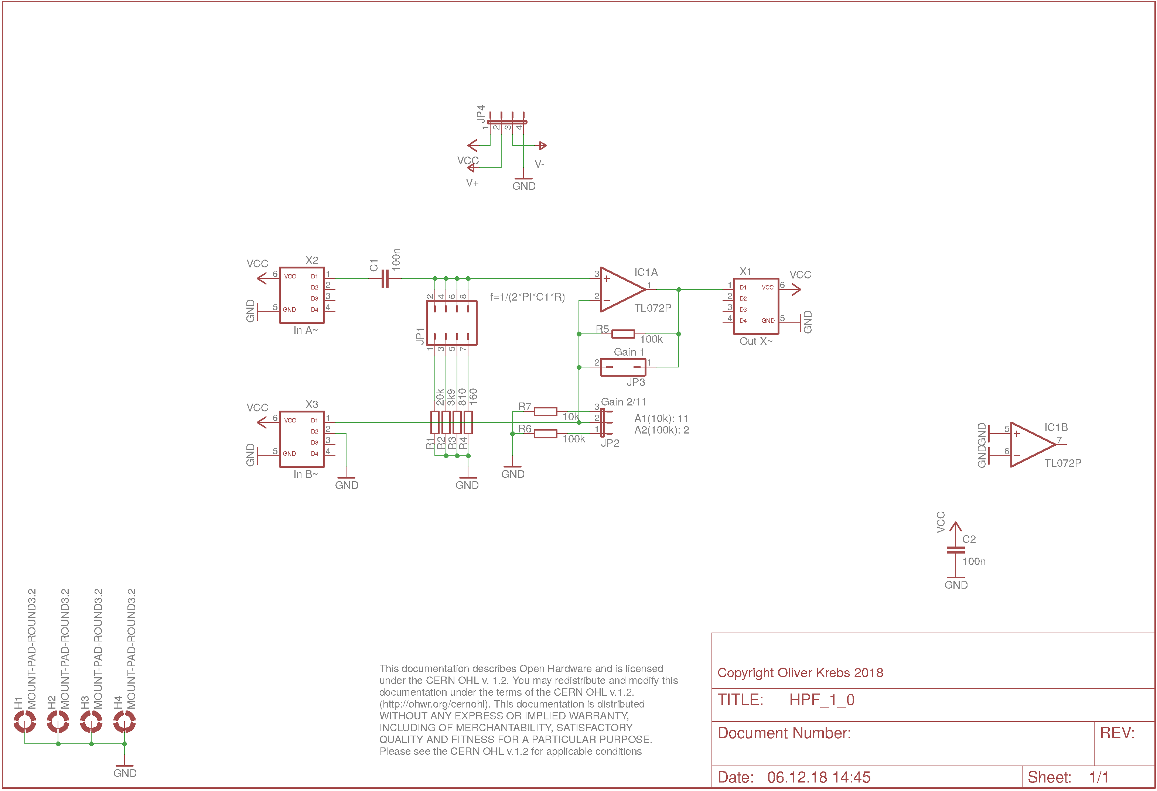
doc/HPF_1_0_sch.png
