mexdulon/tetra-Boards/doc/INV_1_0_sch.png

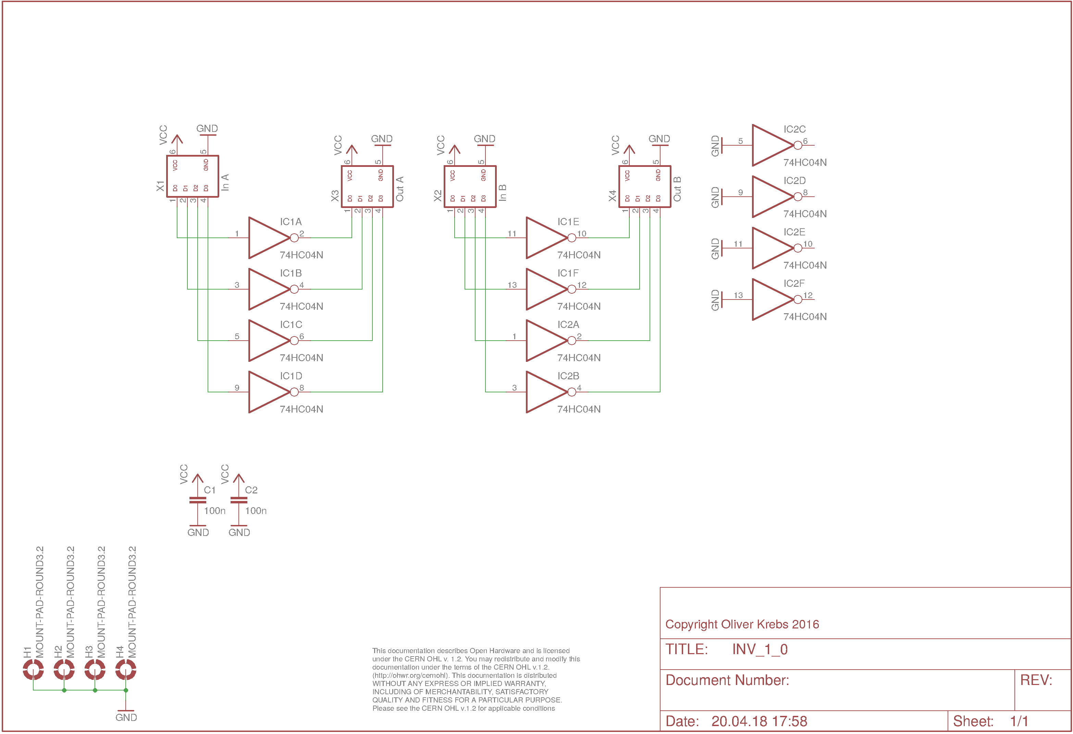
doc/INV_1_0_sch.png
