mexdulon/tetra-Boards/doc/IOP_1_0_sch.png

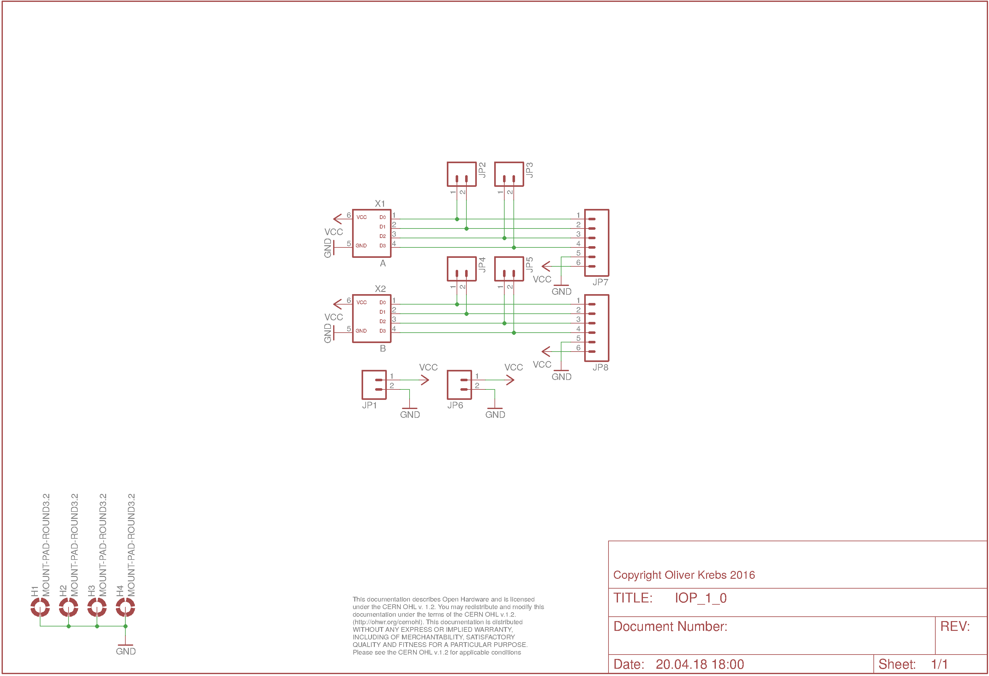
doc/IOP_1_0_sch.png
