mexdulon/tetra-Boards/doc/IOP_1_2_sch.png

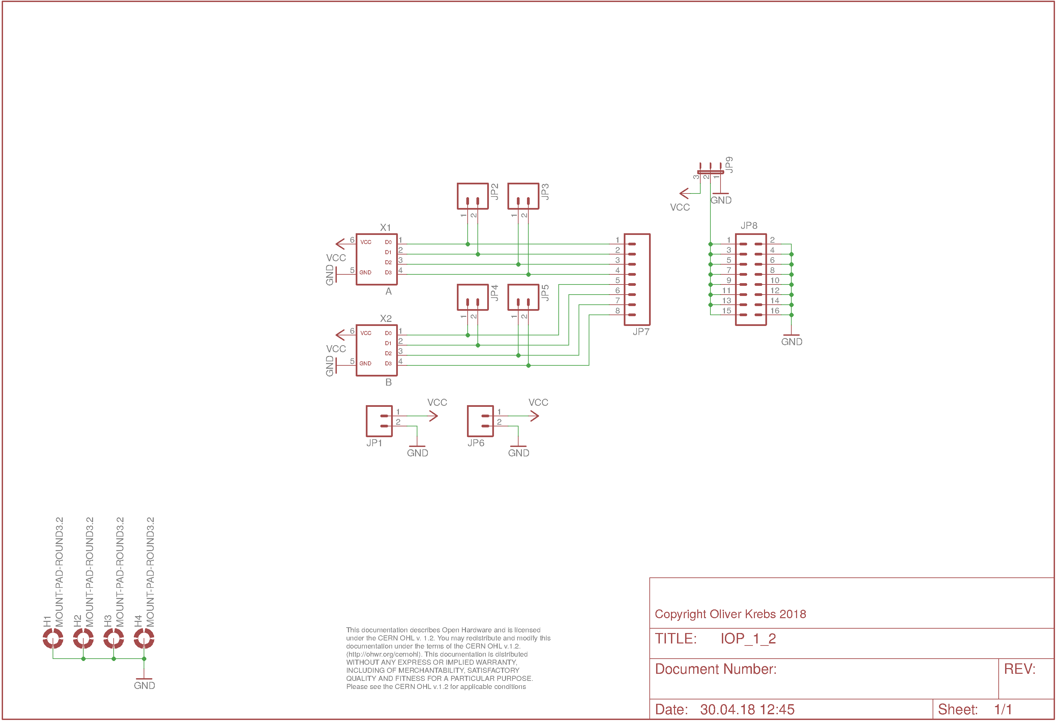
doc/IOP_1_2_sch.png
