mexdulon/tetra-Boards/doc/JAD_1_0_sch.png

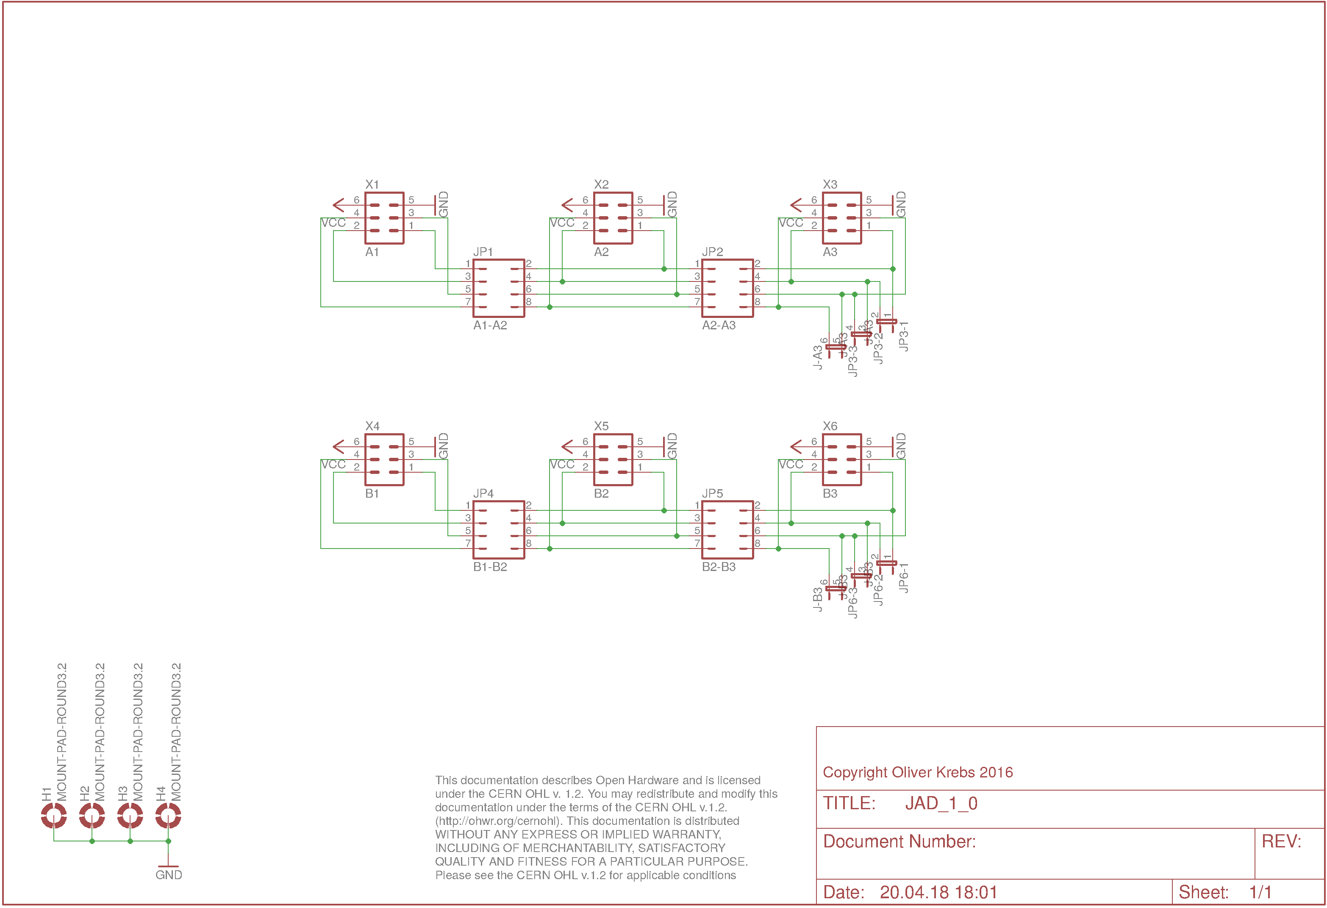
doc/JAD_1_0_sch.png
