mexdulon/tetra-Boards/doc/JKF_1_0_sch.png

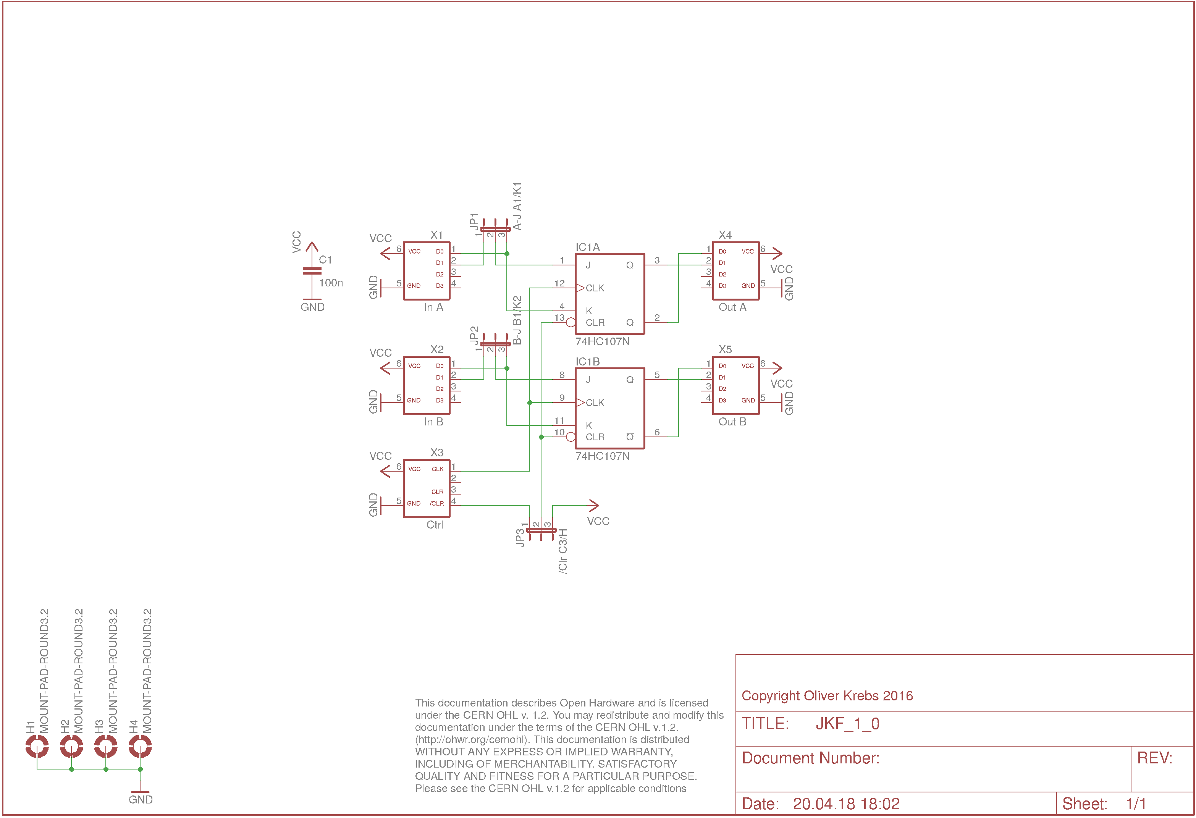
doc/JKF_1_0_sch.png
