mexdulon/tetra-Boards/doc/JMP_1_1_sch.png

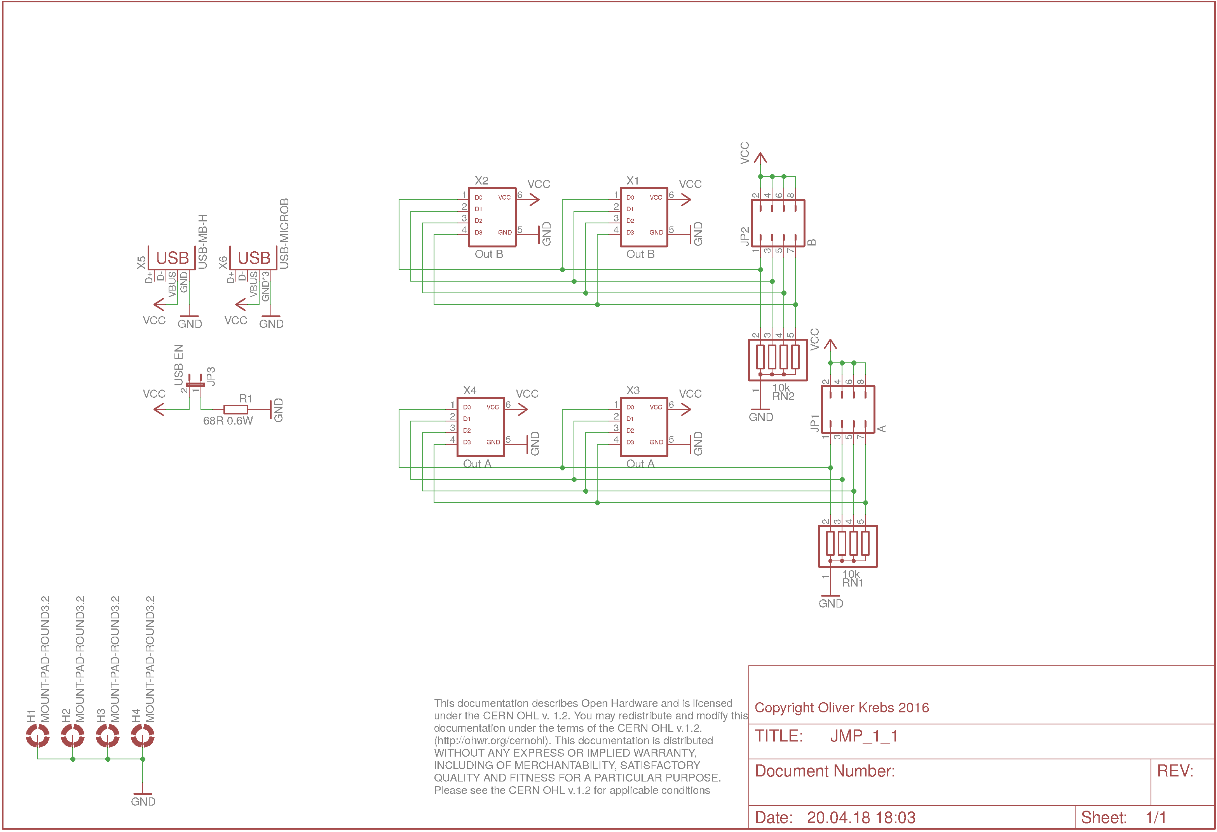
doc/JMP_1_1_sch.png
