mexdulon/tetra-Boards/doc/JMP_1_1_silk.png

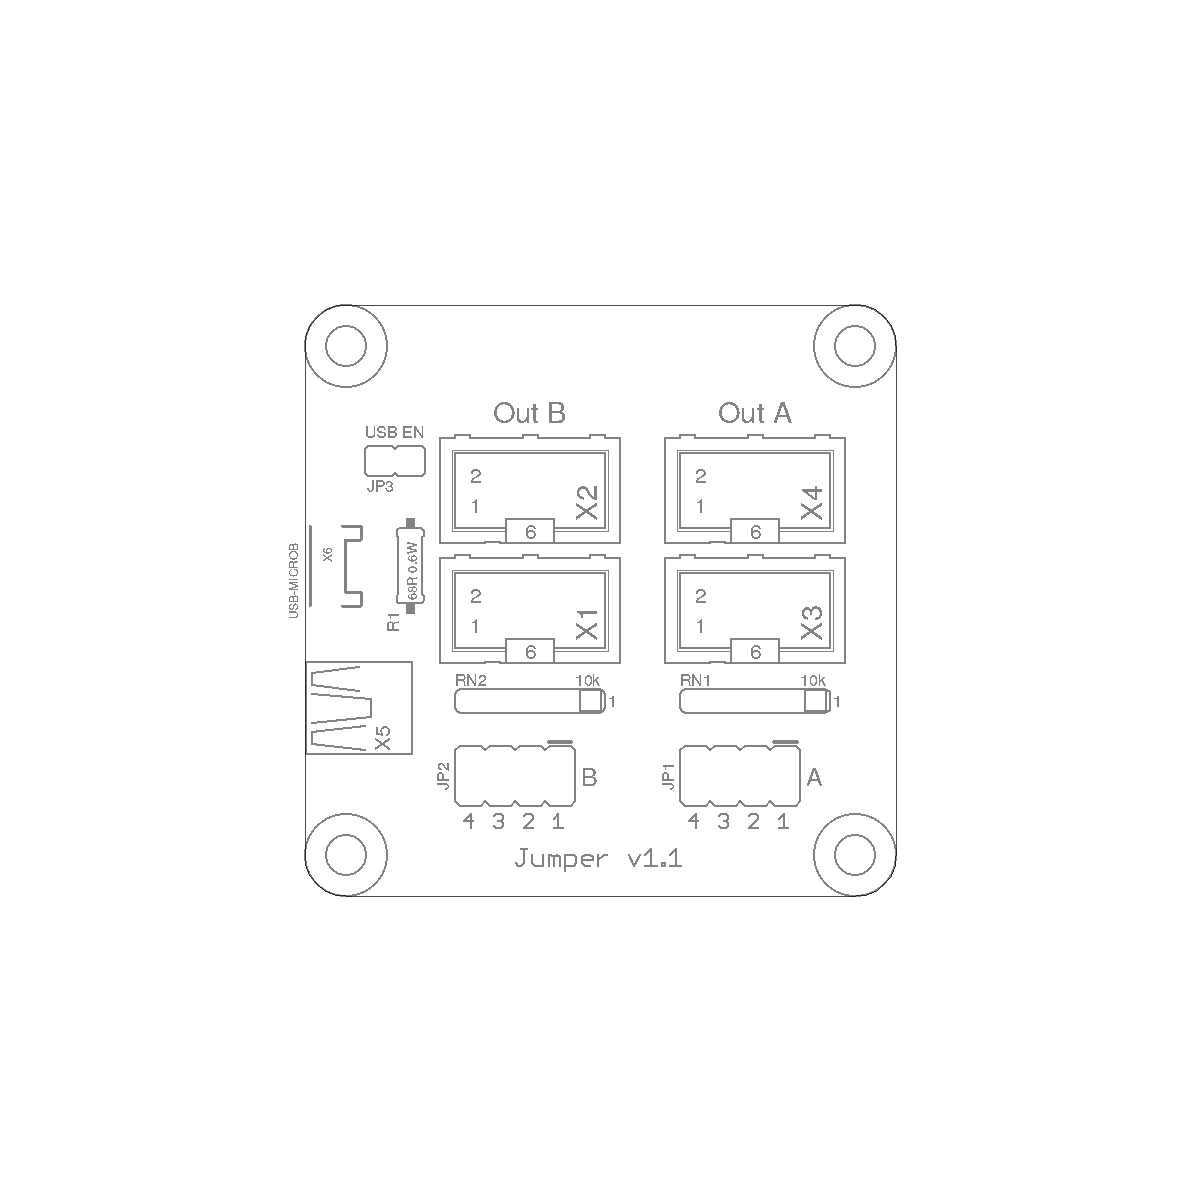
doc/JMP_1_1_silk.png
