mexdulon/tetra-Boards/doc/JMP_2_0_sch.png

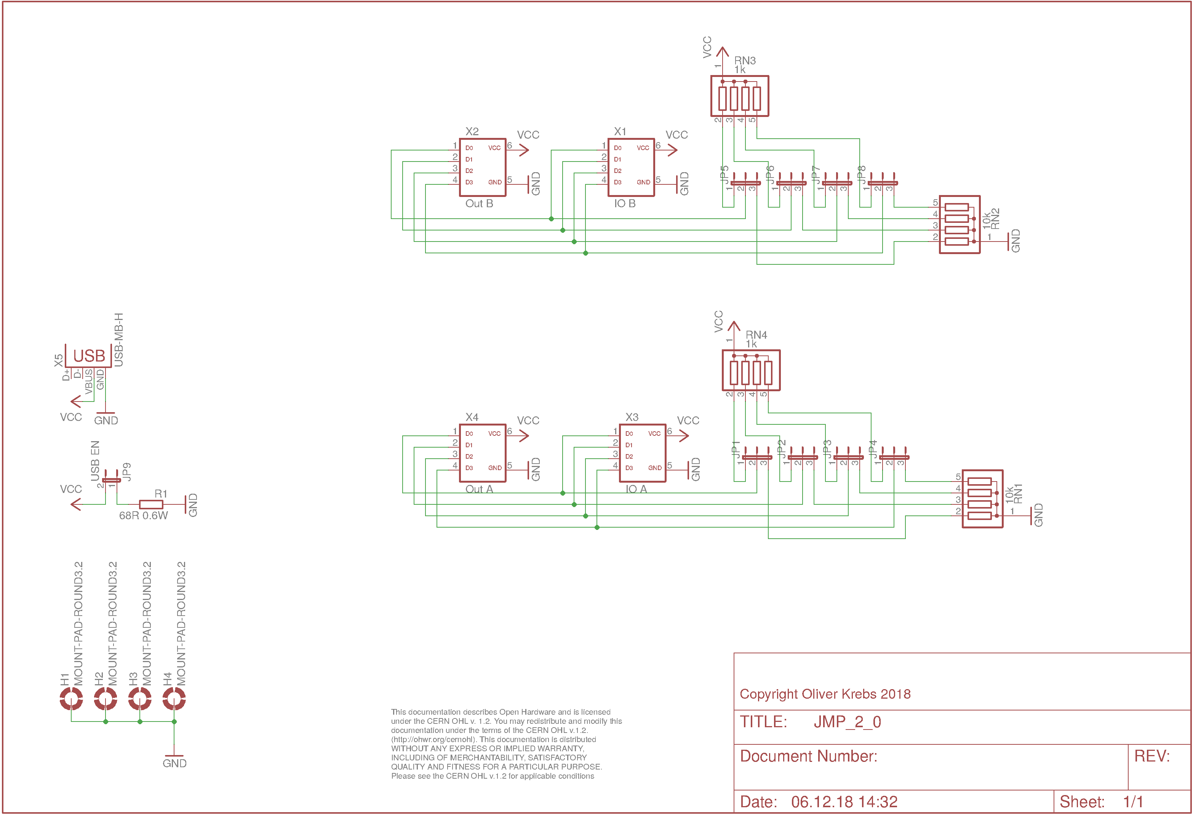
doc/JMP_2_0_sch.png
