mexdulon/tetra-Boards/doc/JOY_1_0_sch.png

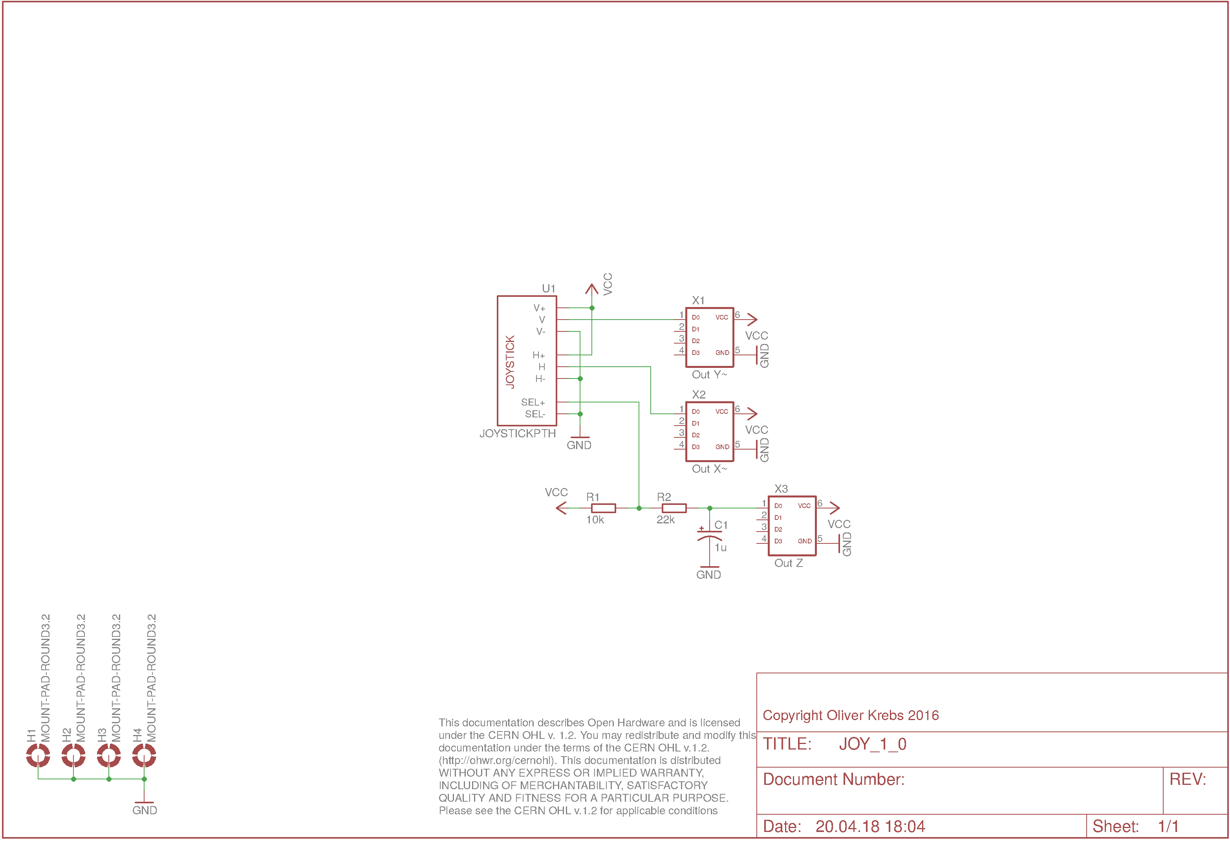
doc/JOY_1_0_sch.png
