mexdulon/tetra-Boards/doc/JOY_1_0_silk.png

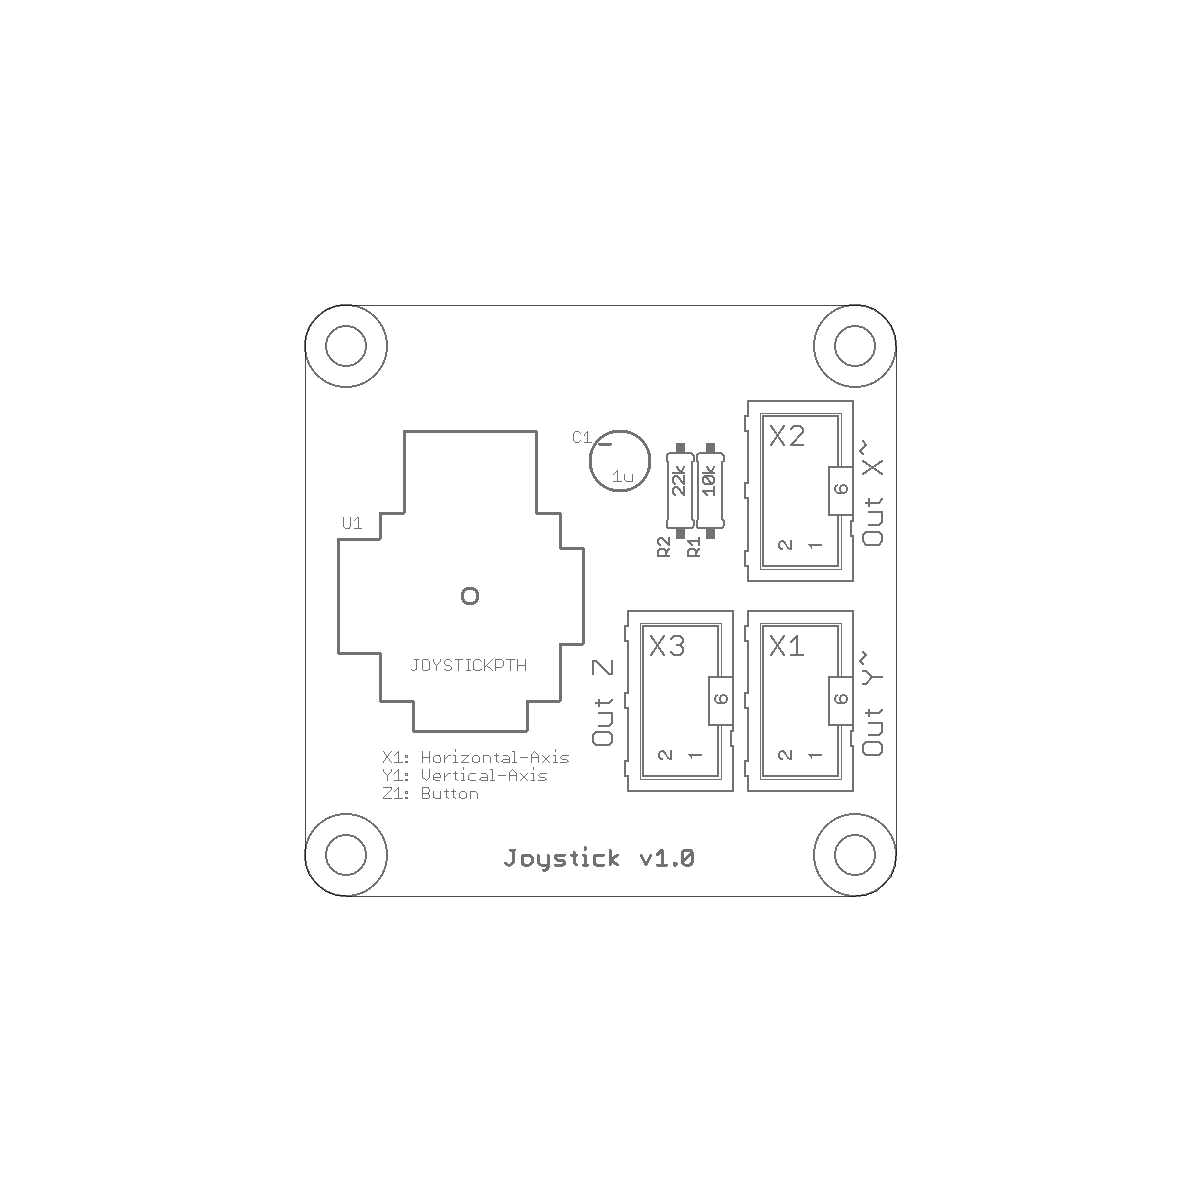
doc/JOY_1_0_silk.png
