mexdulon/tetra-Boards/doc/KEY_1_0_sch.png

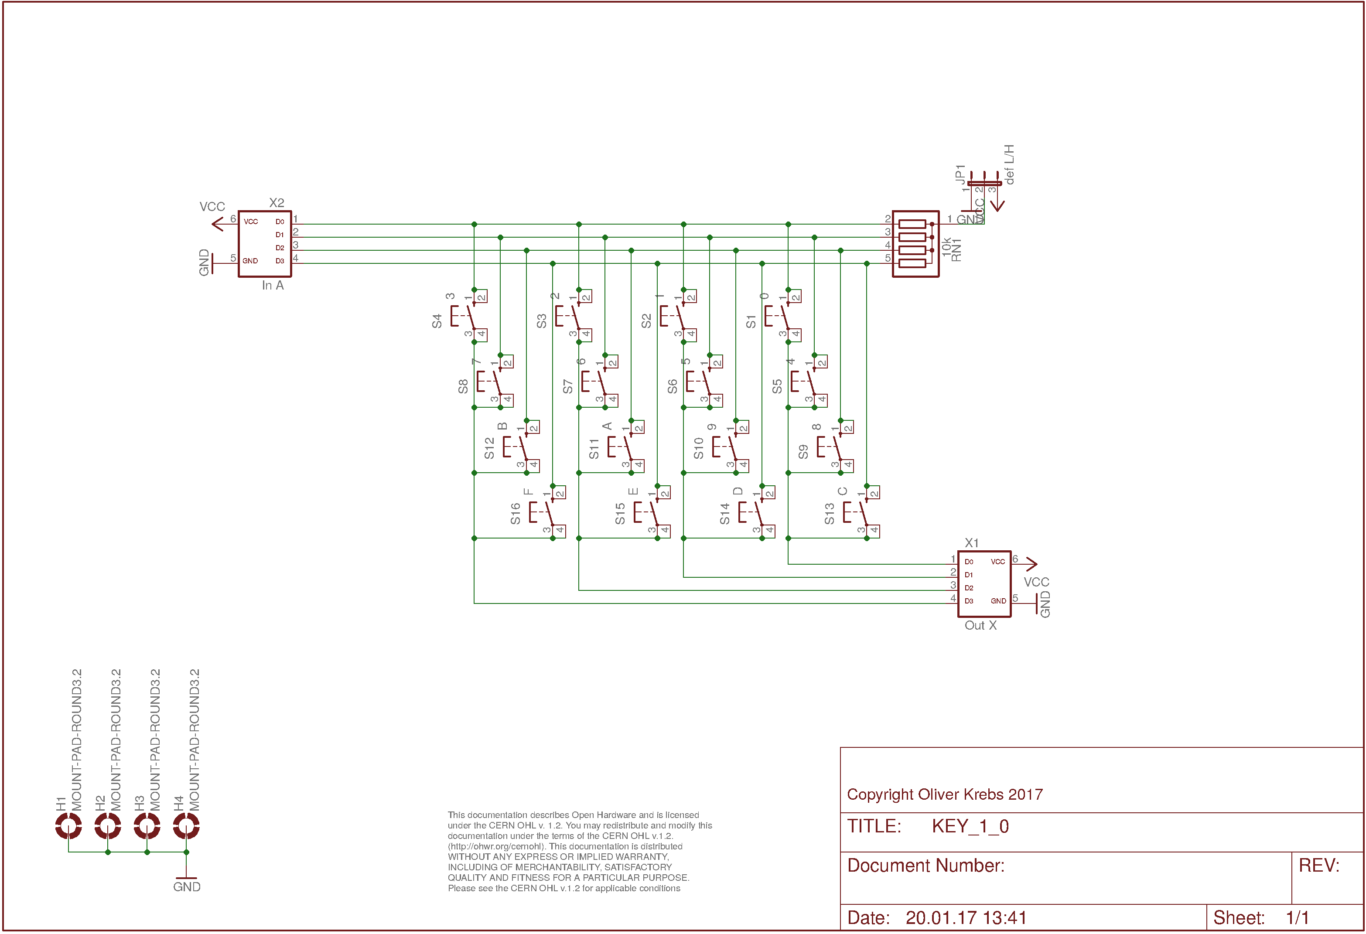
doc/KEY_1_0_sch.png
