mexdulon/tetra-Boards/doc/KEY_1_0_silk.png

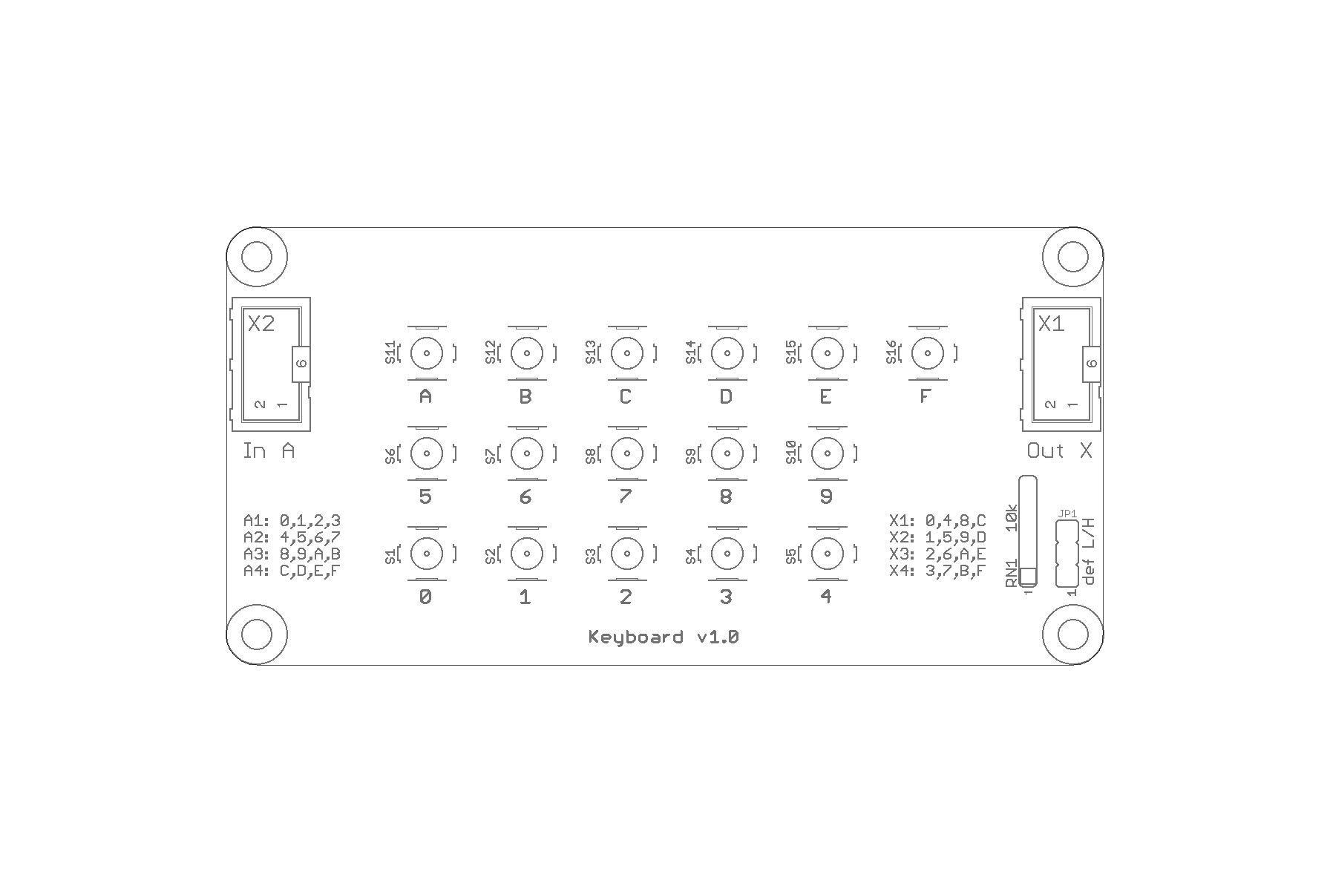
doc/KEY_1_0_silk.png
