mexdulon/tetra-Boards/doc/LAD_1_0_sch.png

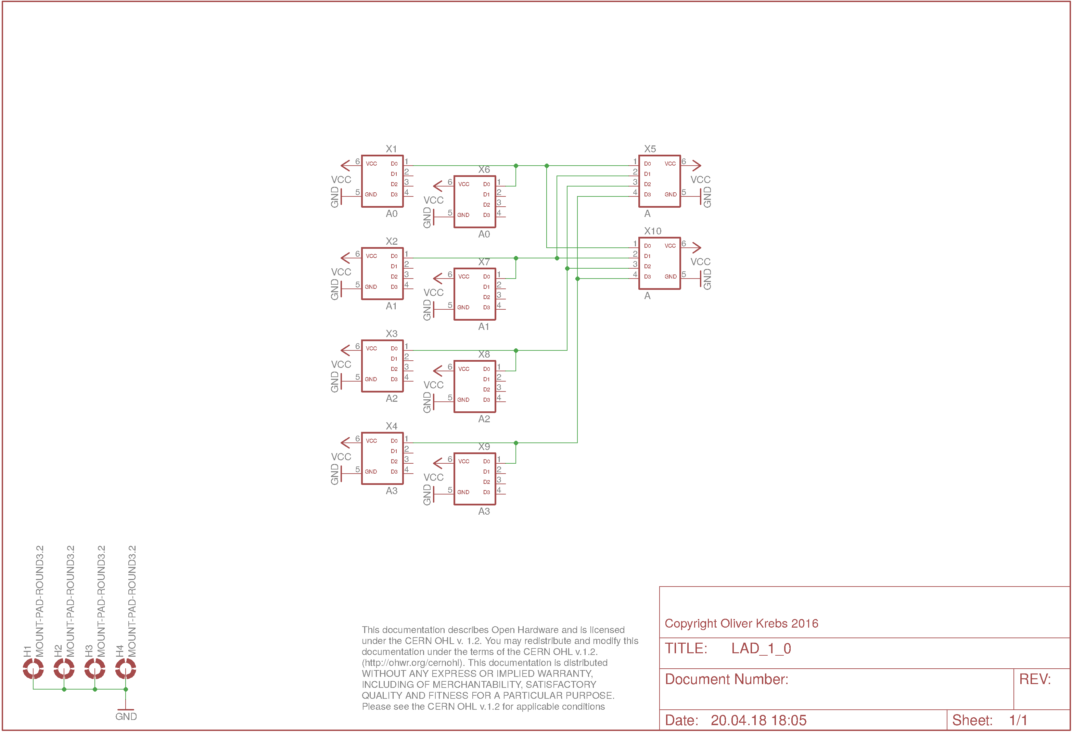
doc/LAD_1_0_sch.png
