mexdulon/tetra-Boards/doc/LAD_1_1_sch.png

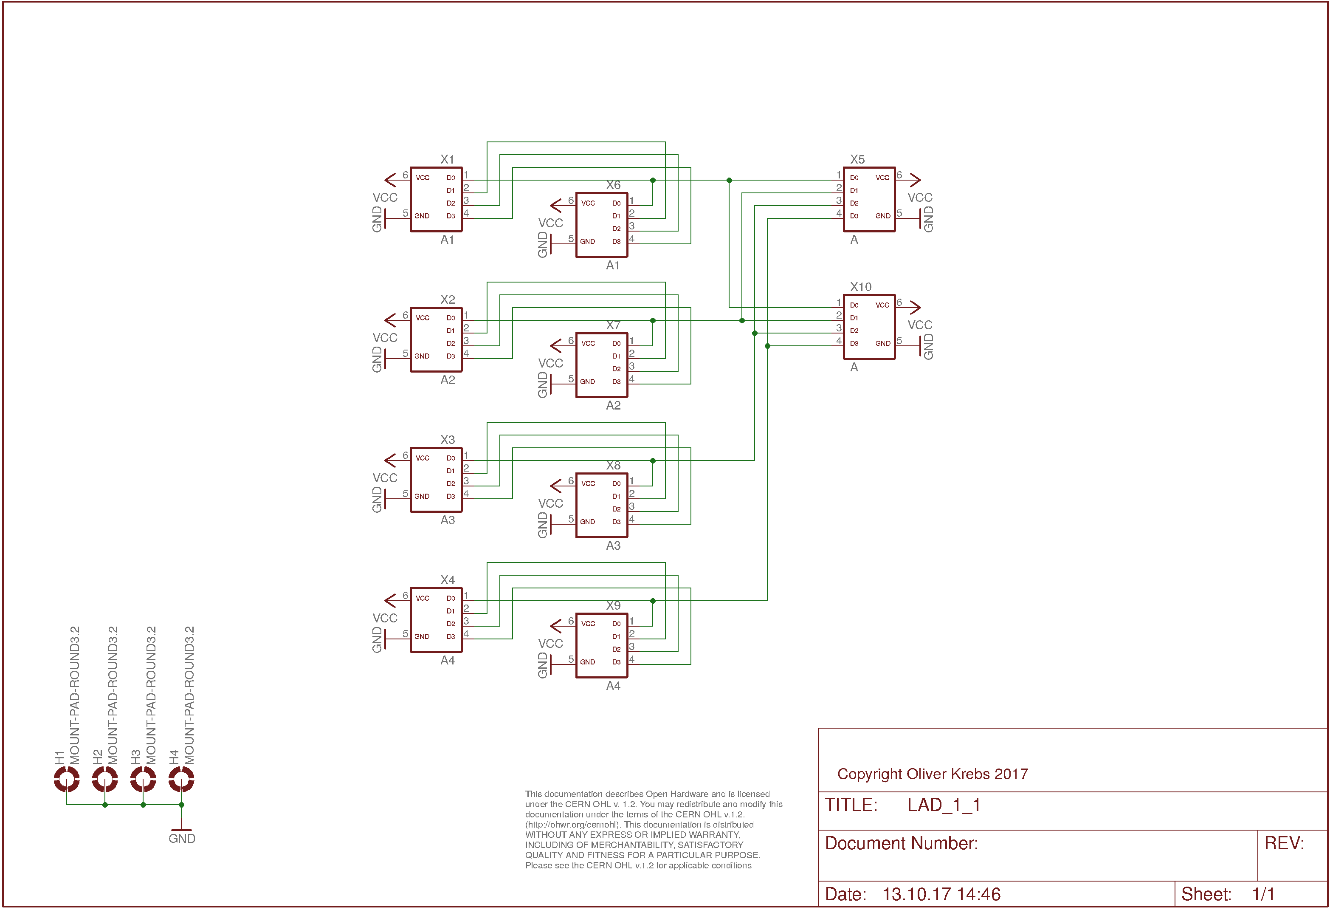
doc/LAD_1_1_sch.png
