mexdulon/tetra-Boards/doc/LPF_1_0_sch.png

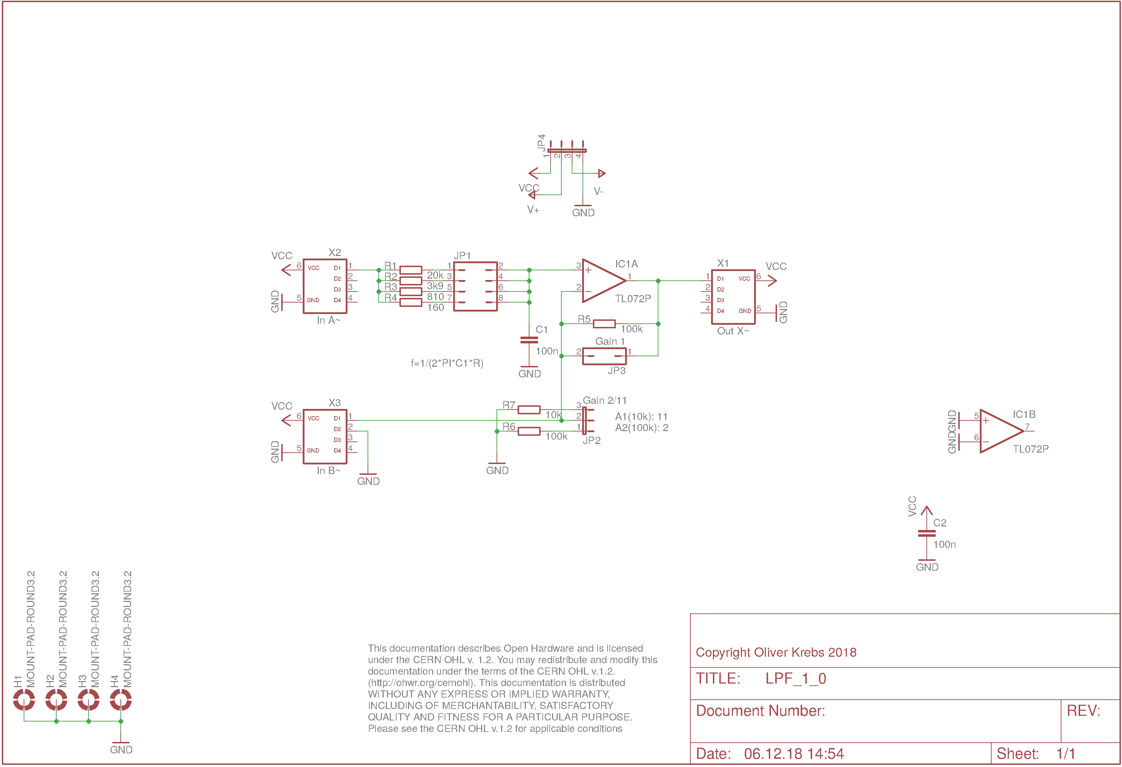
doc/LPF_1_0_sch.png
