mexdulon/tetra-Boards/doc/M81_1_0_sch.png

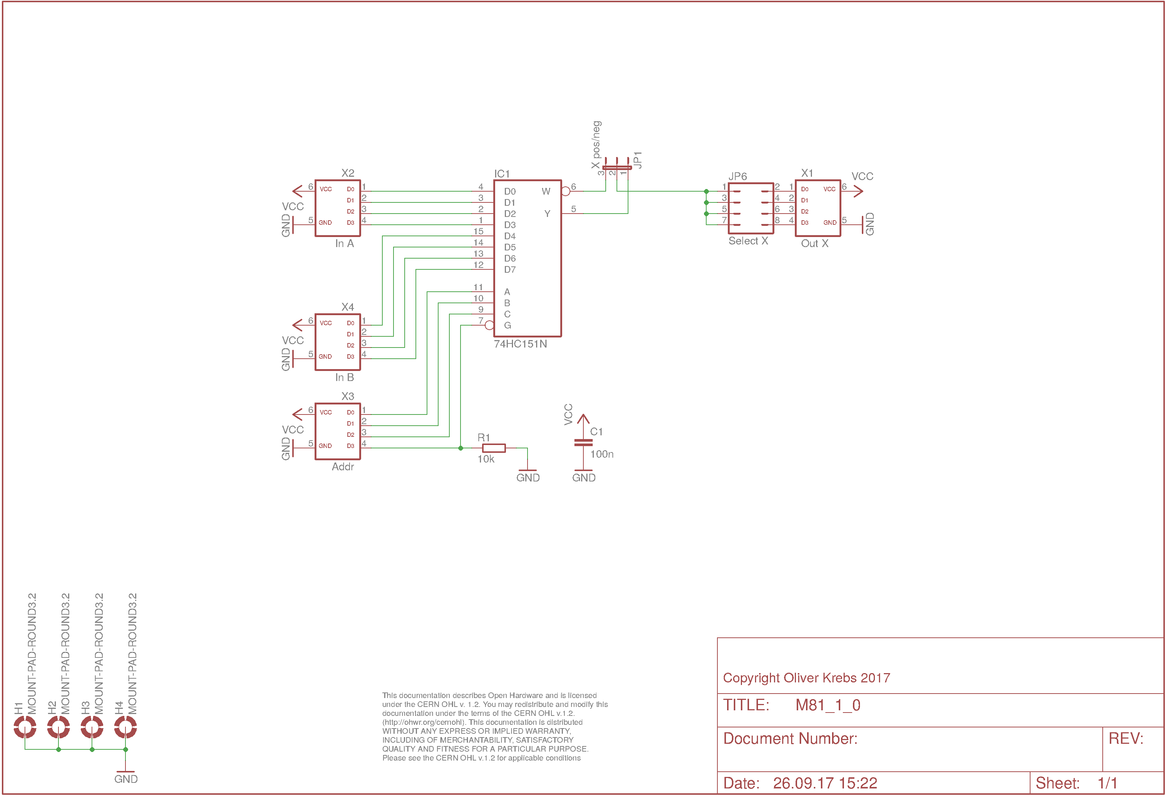
doc/M81_1_0_sch.png
