mexdulon/tetra-Boards/doc/MIC_1_0_sch.png

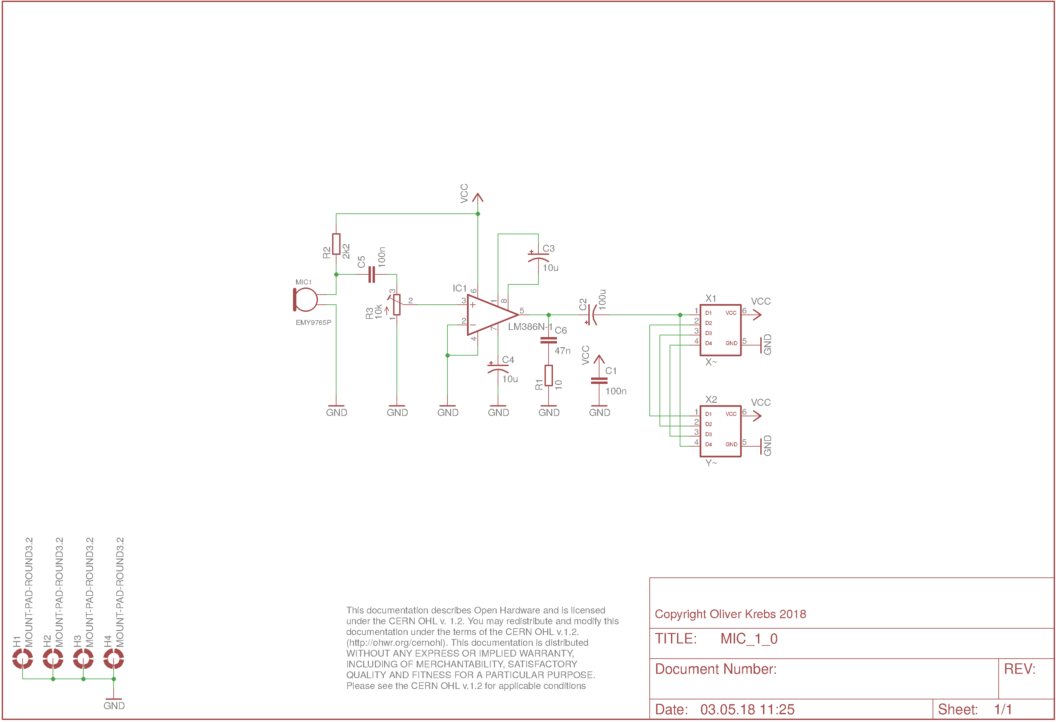
doc/MIC_1_0_sch.png
