mexdulon/tetra-Boards/doc/MIC_1_0_silk.png

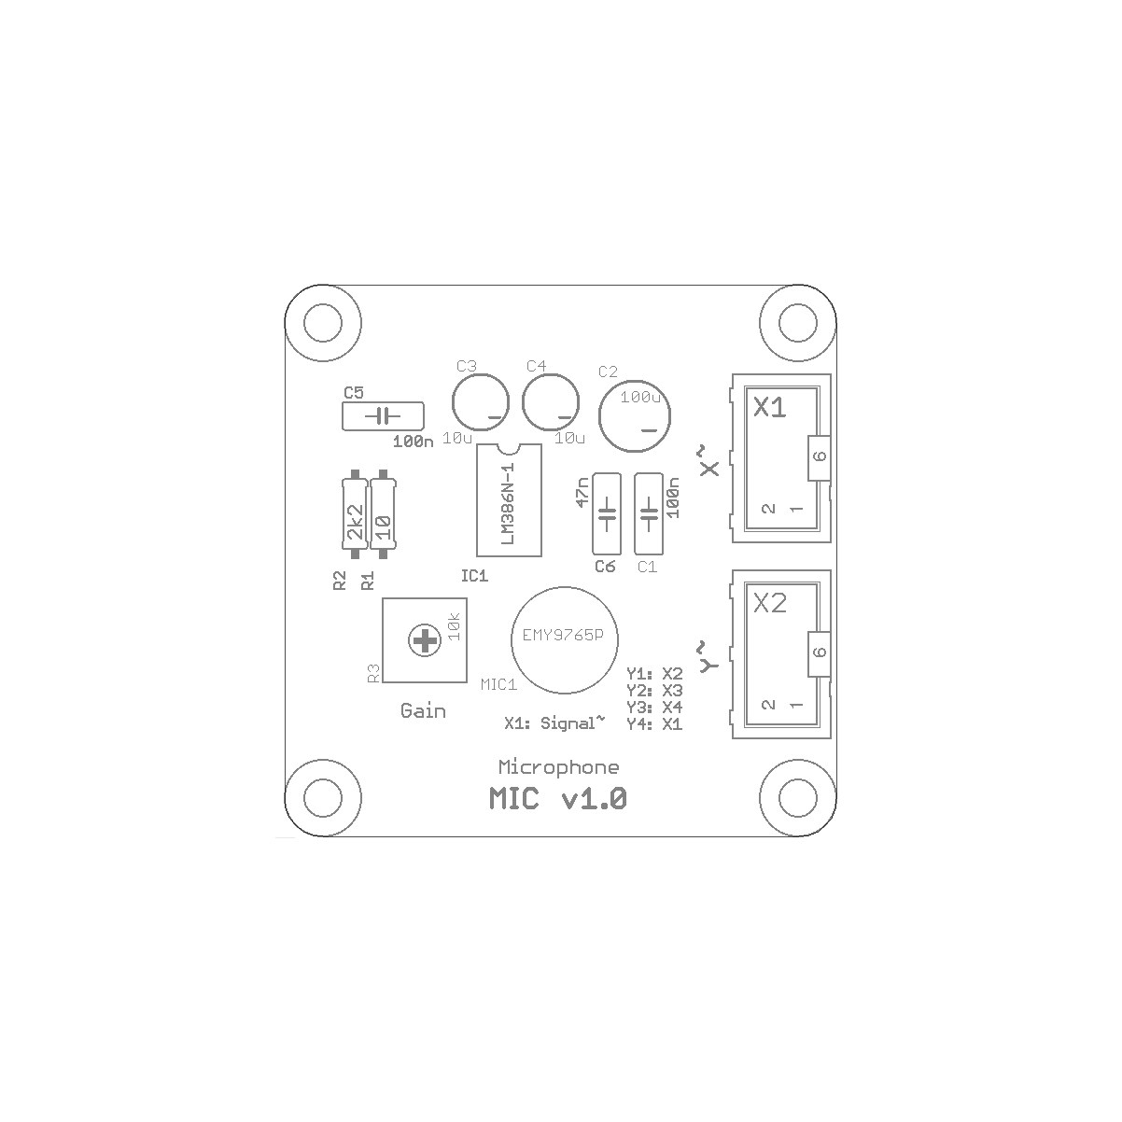
doc/MIC_1_0_silk.png
