mexdulon/tetra-Boards/doc/MTR_1_0_sch.png

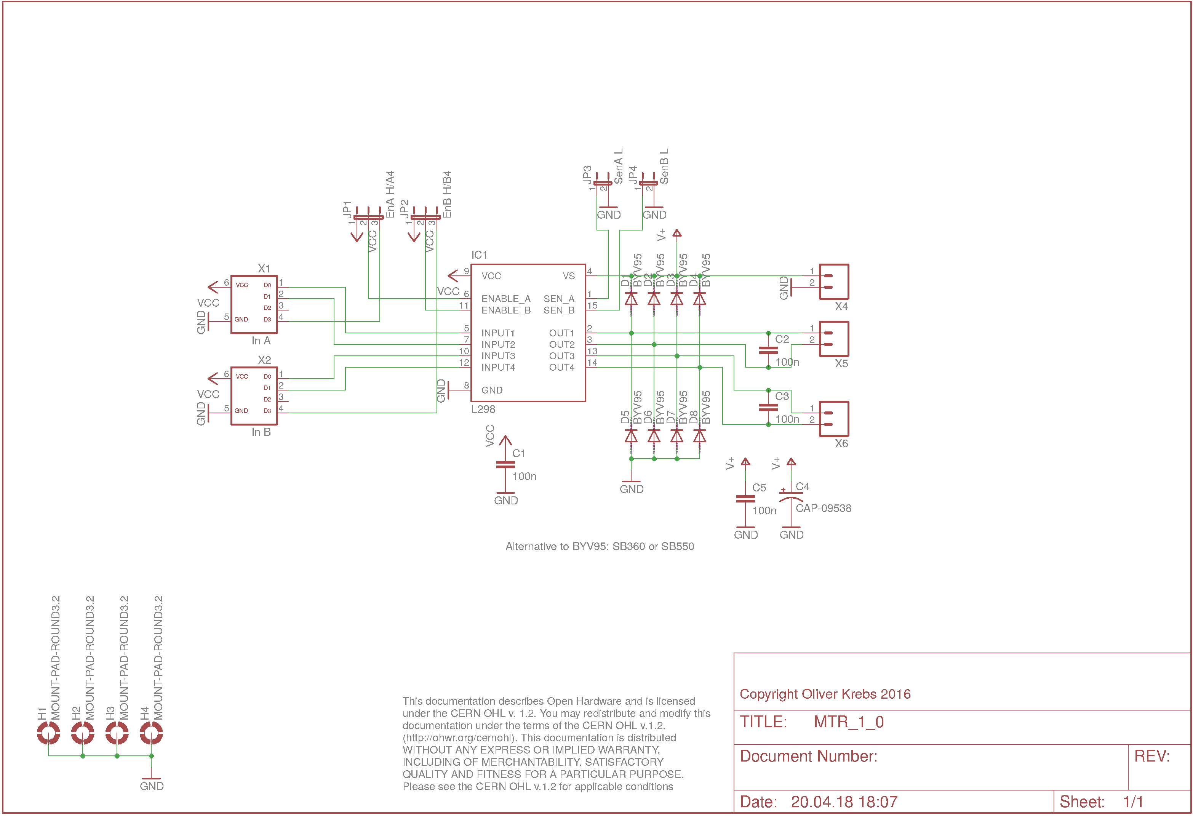
doc/MTR_1_0_sch.png
