mexdulon/tetra-Boards/doc/MUX_1_1_sch.png

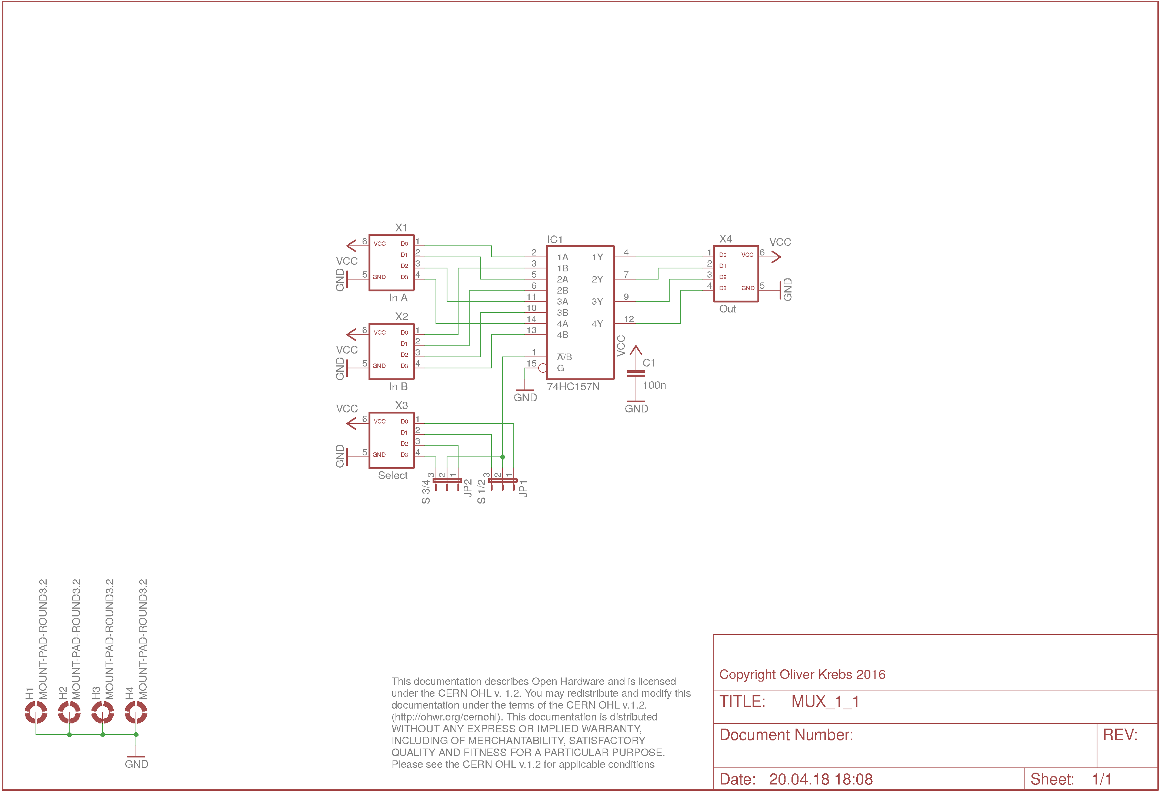
doc/MUX_1_1_sch.png
