mexdulon/tetra-Boards/doc/MXC_1_0_sch.png

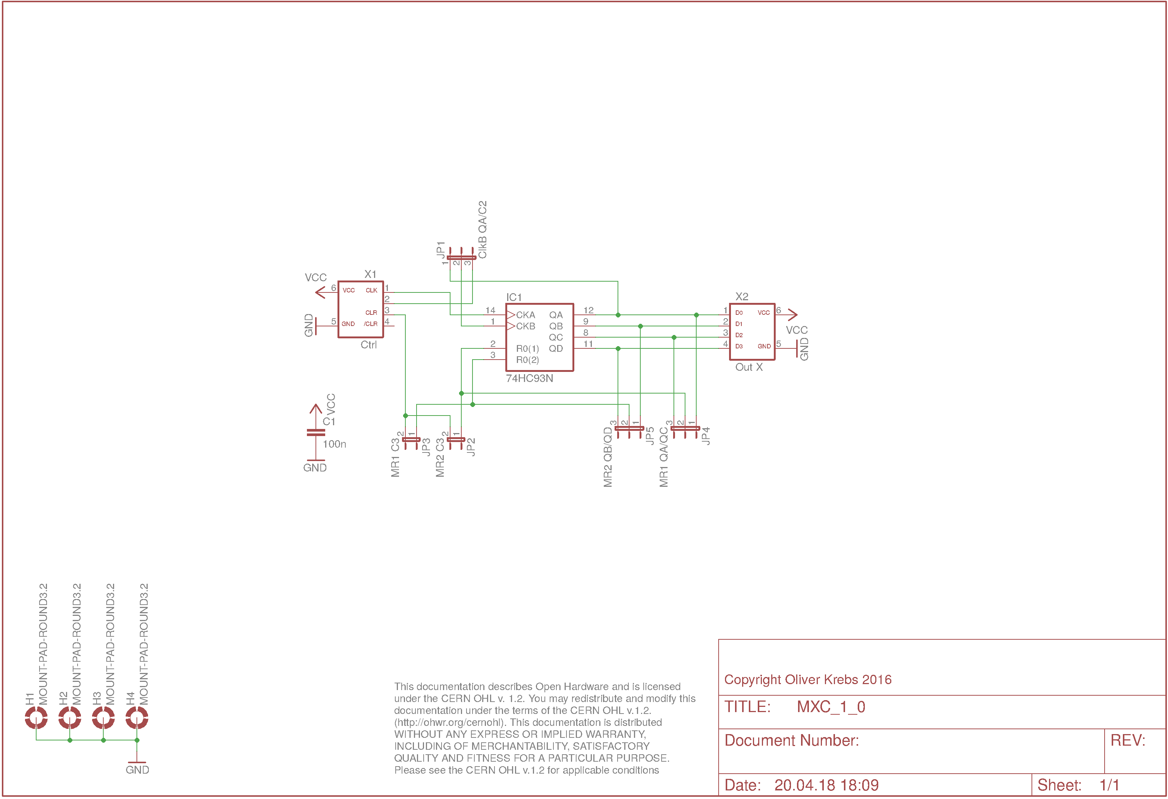
doc/MXC_1_0_sch.png
