mexdulon/tetra-Boards/doc/N33_1_0_sch.png

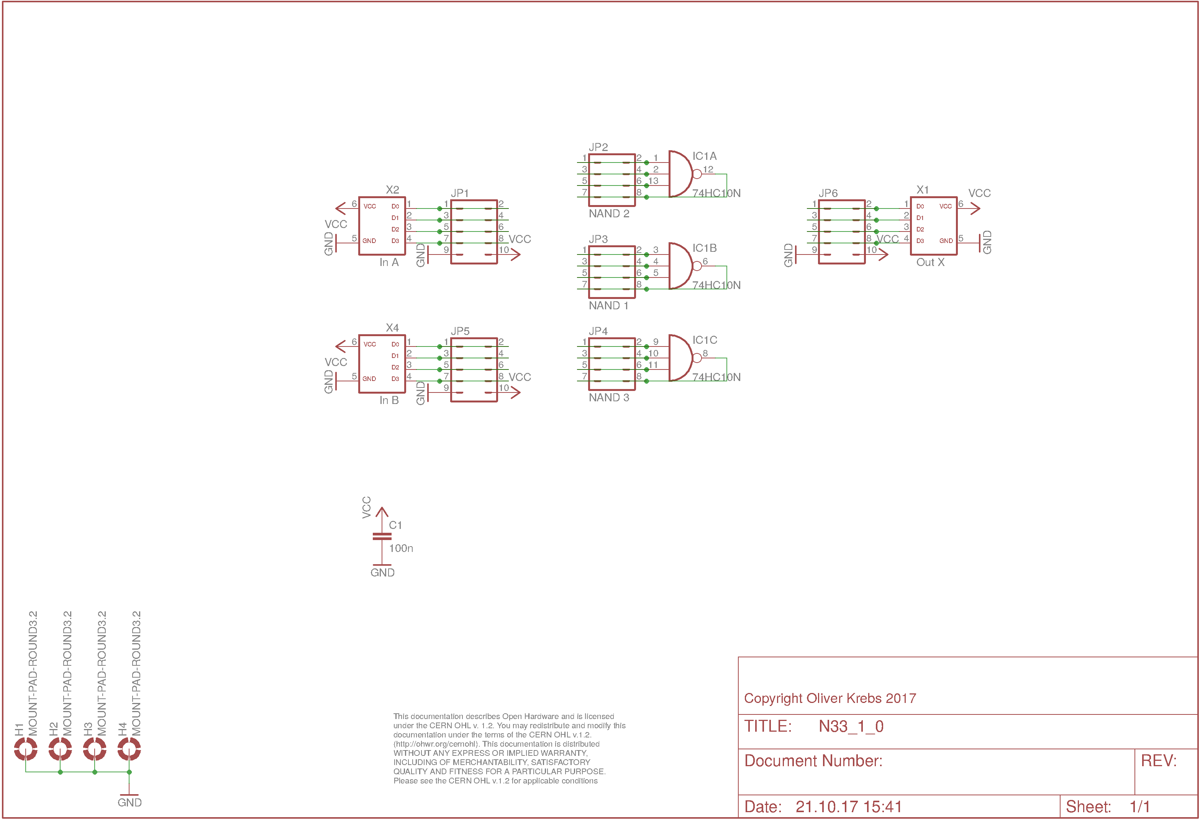
doc/N33_1_0_sch.png
