mexdulon/tetra-Boards/doc/NOR_1_1_sch.png

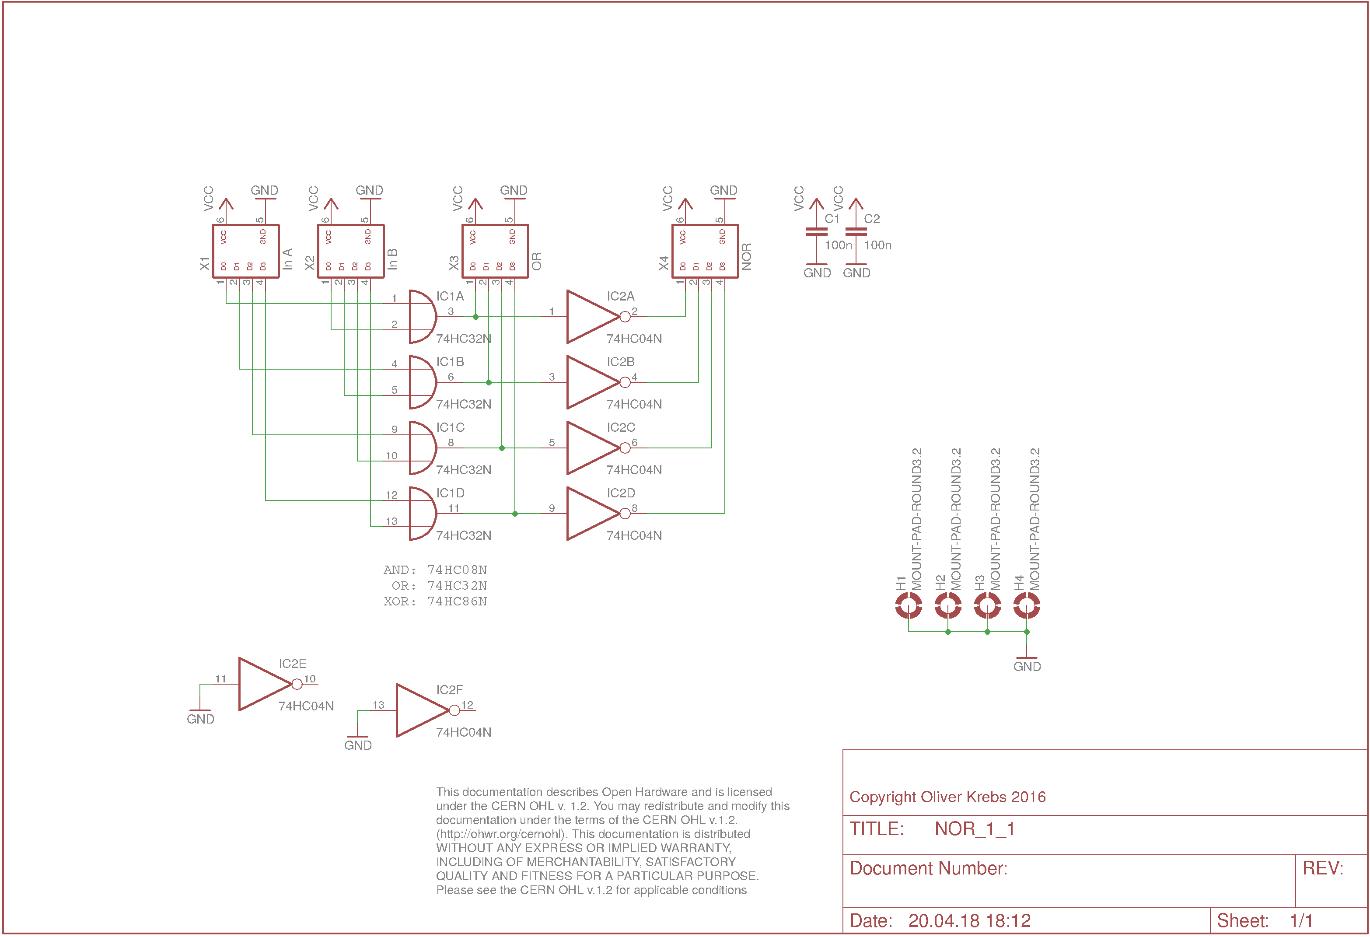
doc/NOR_1_1_sch.png
