mexdulon/tetra-Boards/doc/NOT_1_0_sch.png

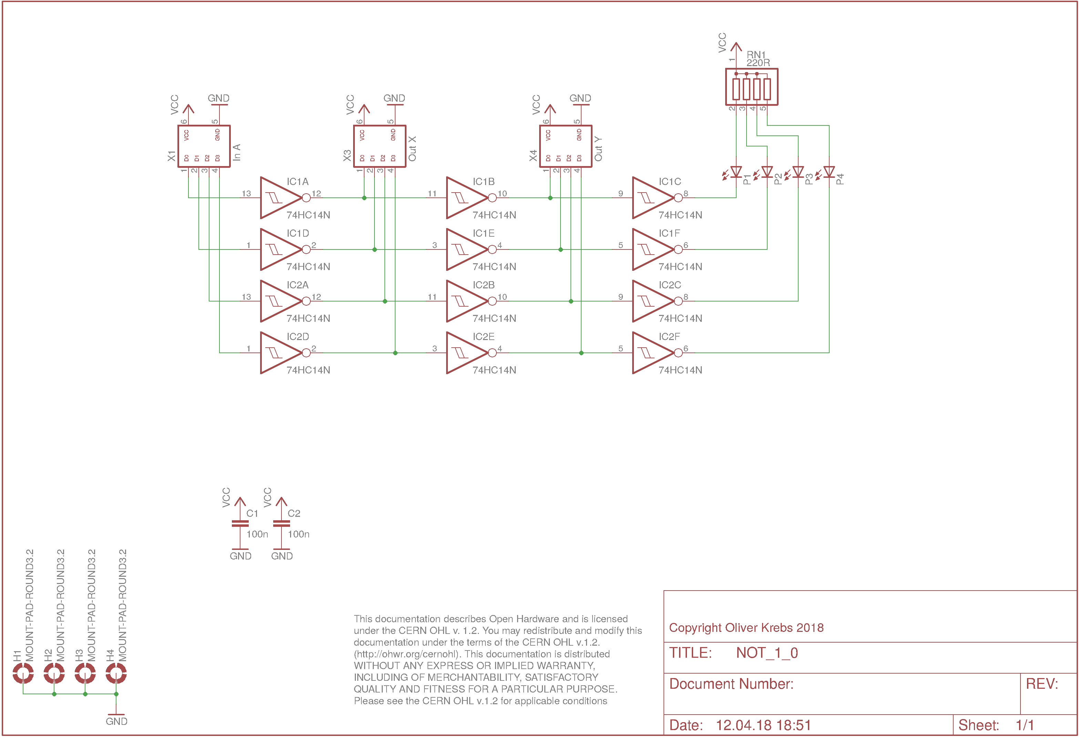
doc/NOT_1_0_sch.png
