mexdulon/tetra-Boards/doc/OPA_1_1_sch.png

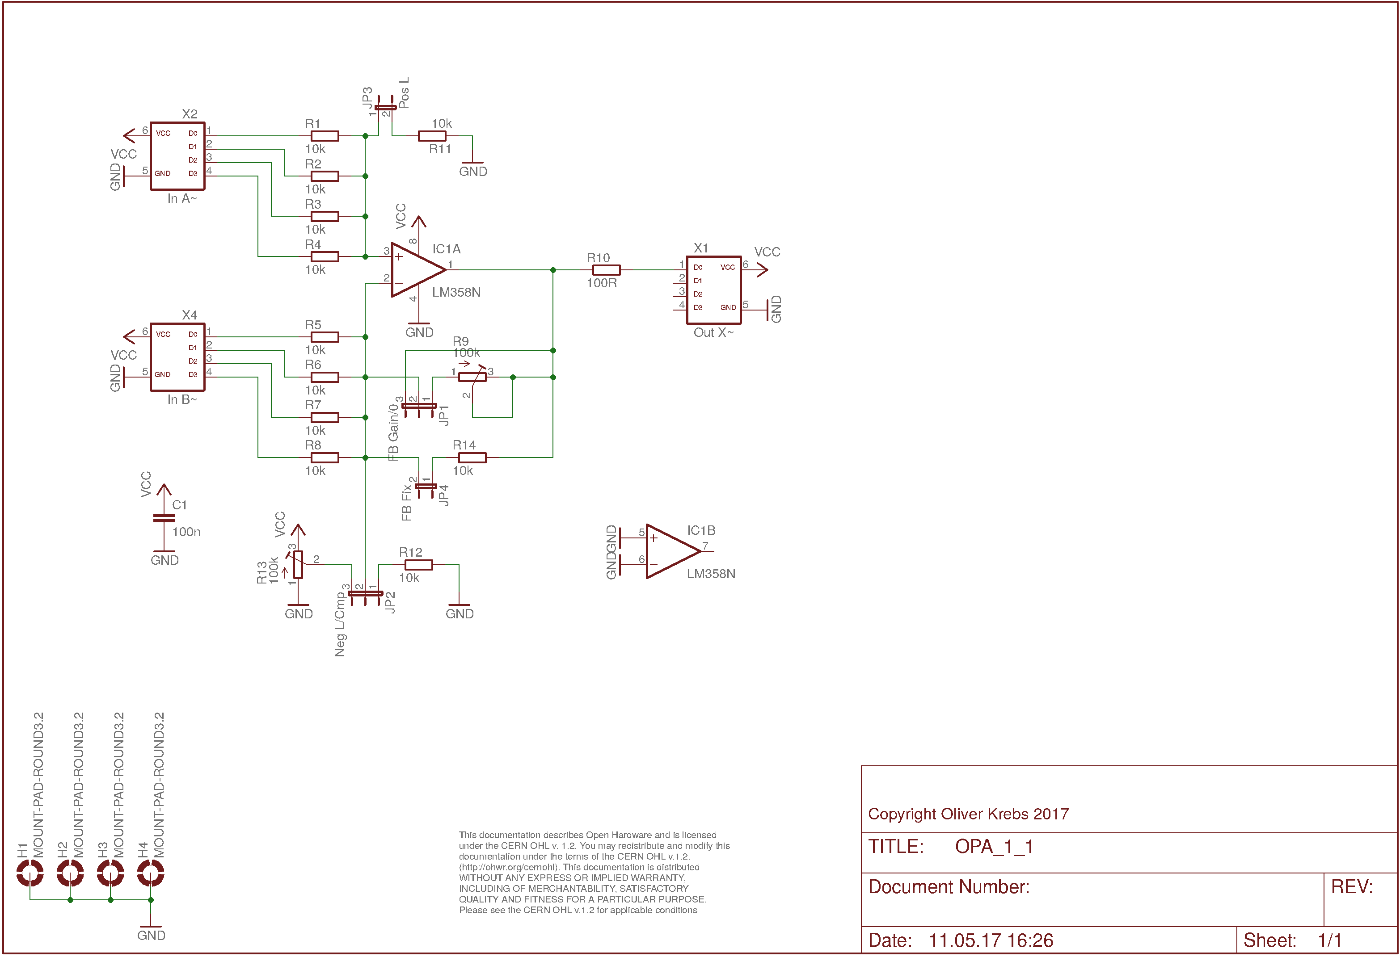
doc/OPA_1_1_sch.png
