mexdulon/tetra-Boards/doc/PAN_1_0_sch.png

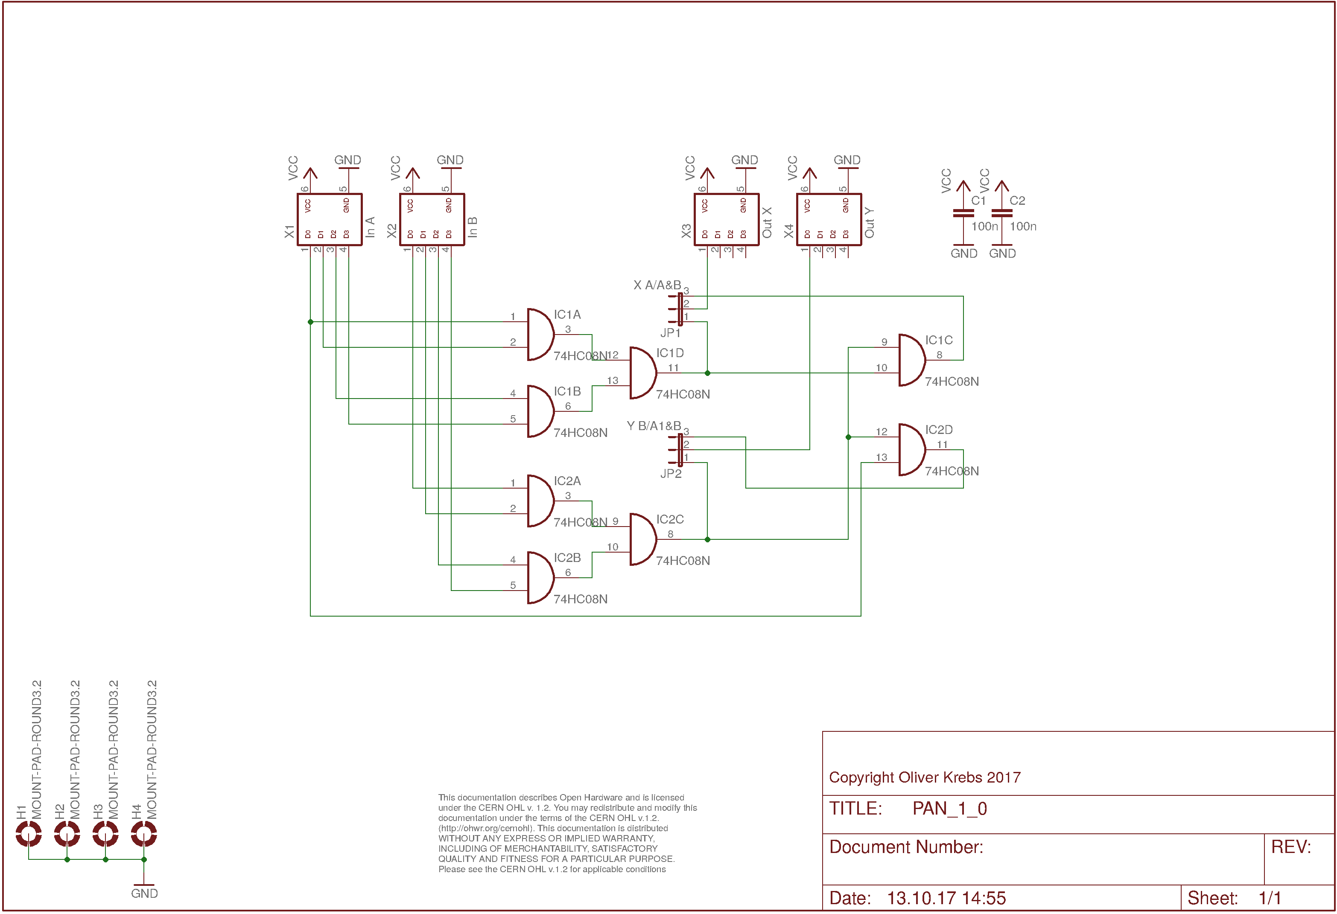
doc/PAN_1_0_sch.png
