mexdulon/tetra-Boards/doc/PIN_1_0_sch.png

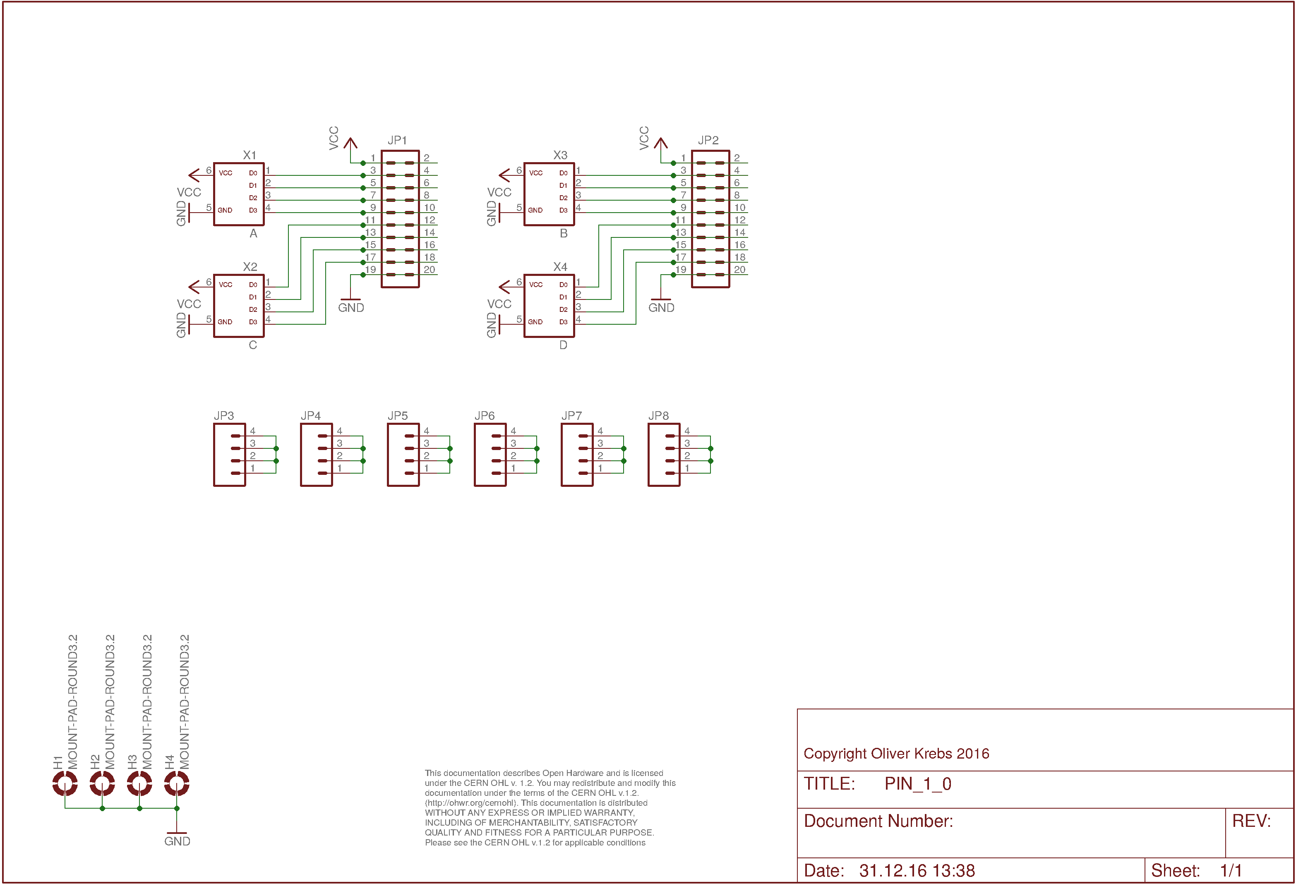
doc/PIN_1_0_sch.png
