mexdulon/tetra-Boards/doc/PIN_1_1_sch.png

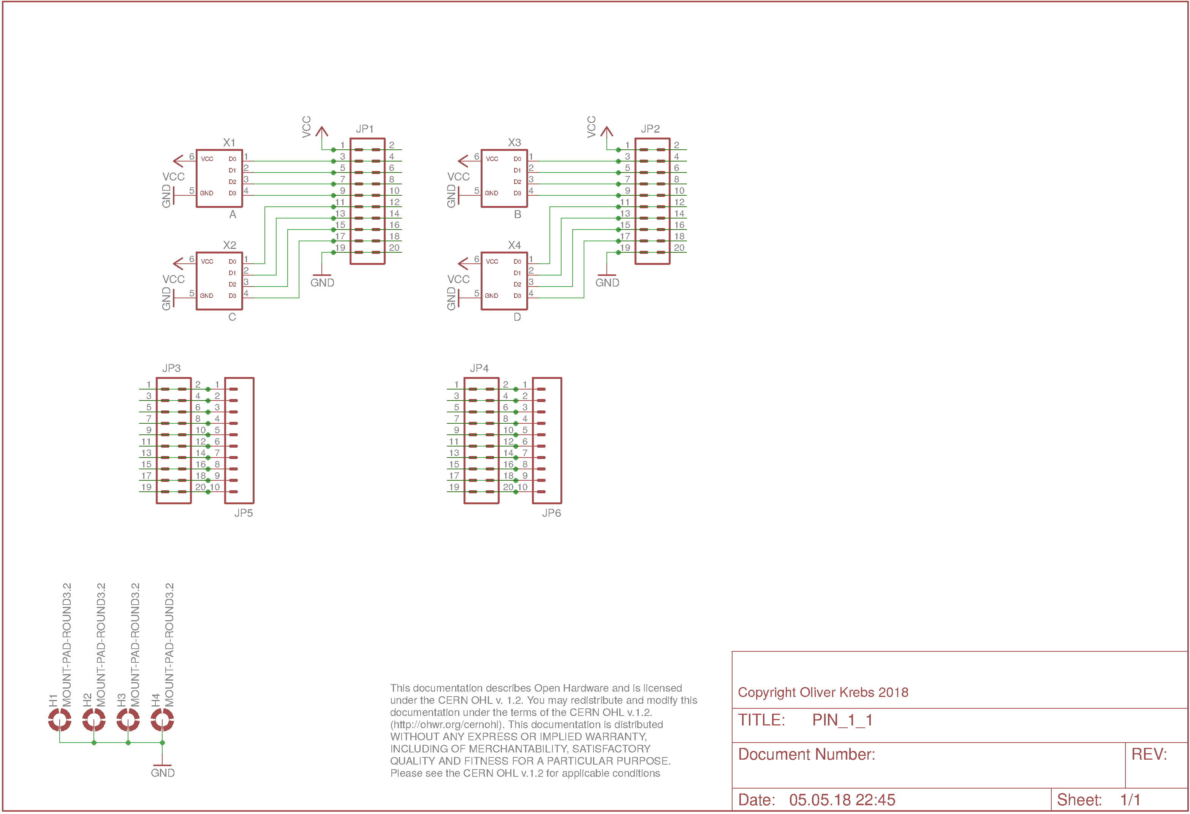
doc/PIN_1_1_sch.png
