mexdulon/tetra-Boards/doc/POT_1_0_sch.png

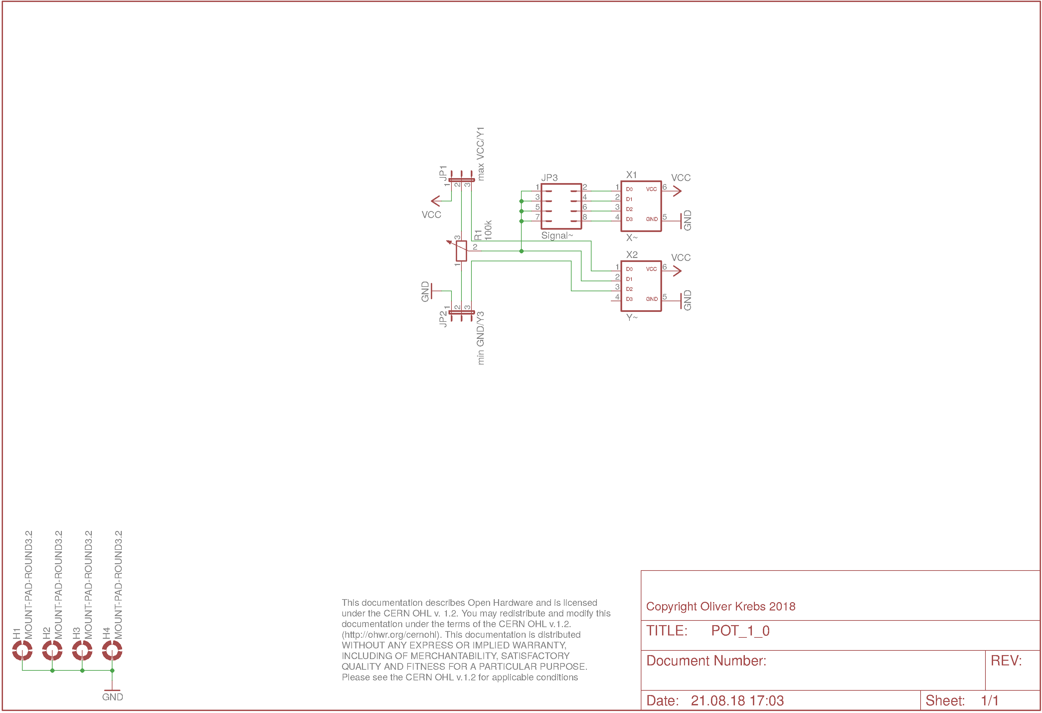
doc/POT_1_0_sch.png
