mexdulon/tetra-Boards/doc/PRE_1_0_sch.png

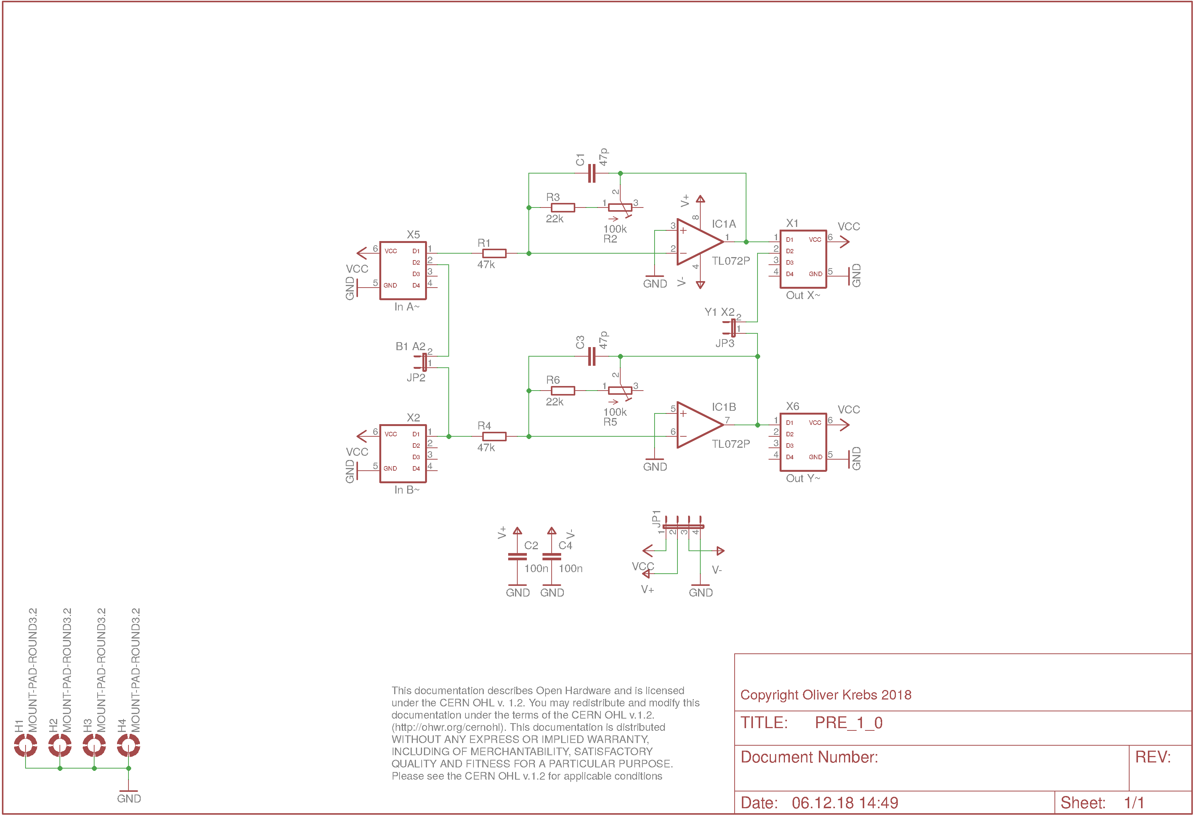
doc/PRE_1_0_sch.png
