mexdulon/tetra-Boards/doc/PRG_1_0_sch.png

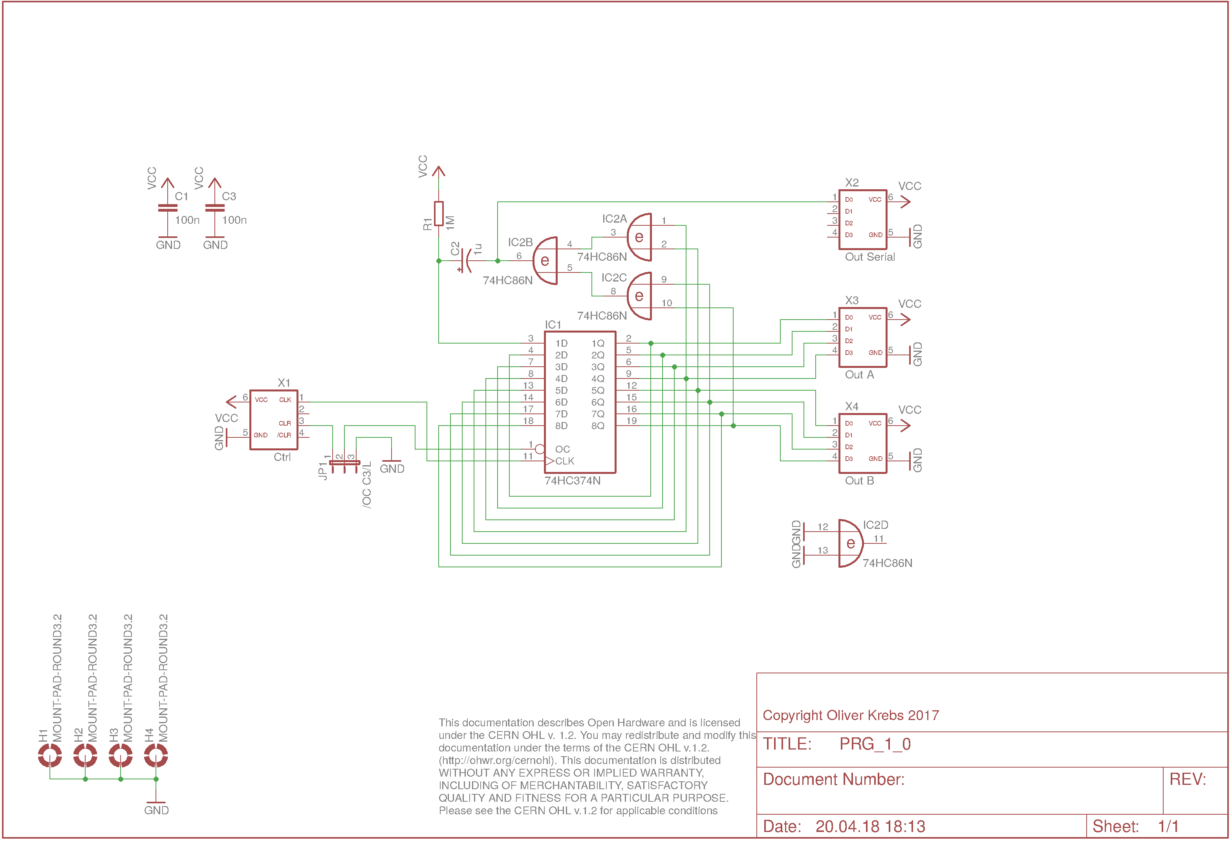
doc/PRG_1_0_sch.png
