mexdulon/tetra-Boards/doc/PRG_1_0_silk.png

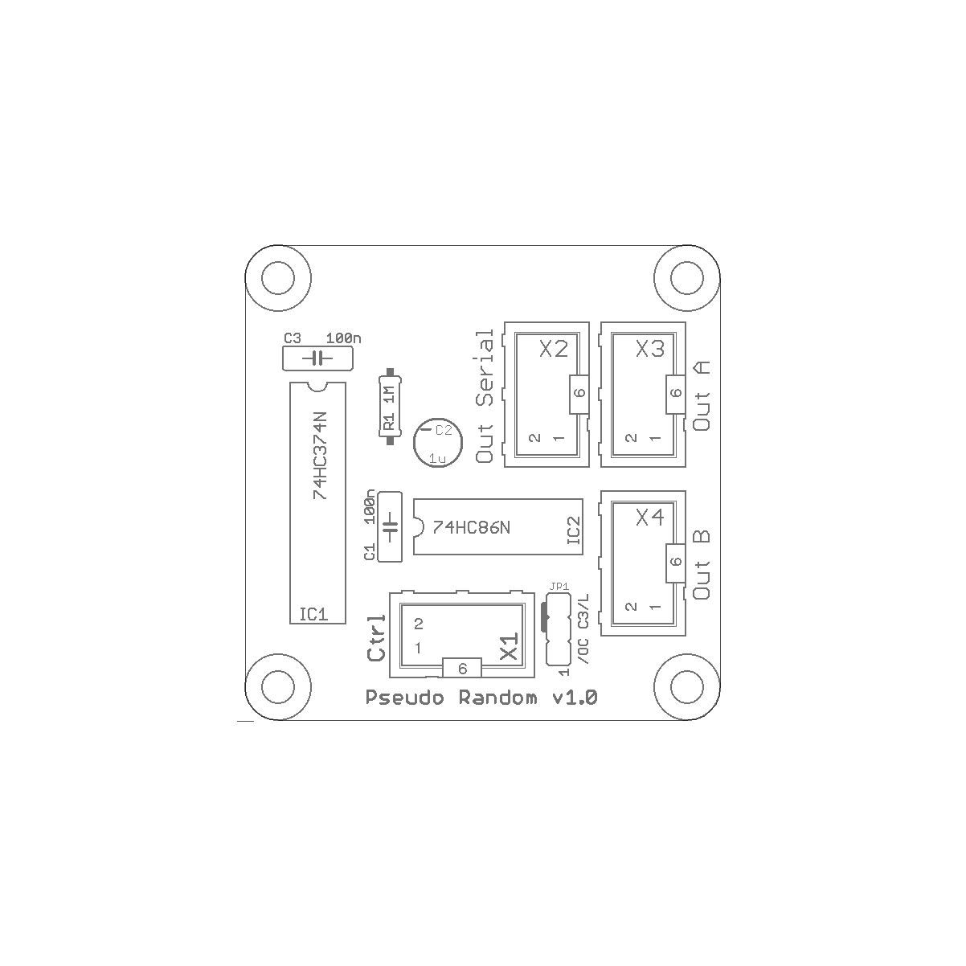
doc/PRG_1_0_silk.png
