mexdulon/tetra-Boards/doc/PWA_1_0_sch.png

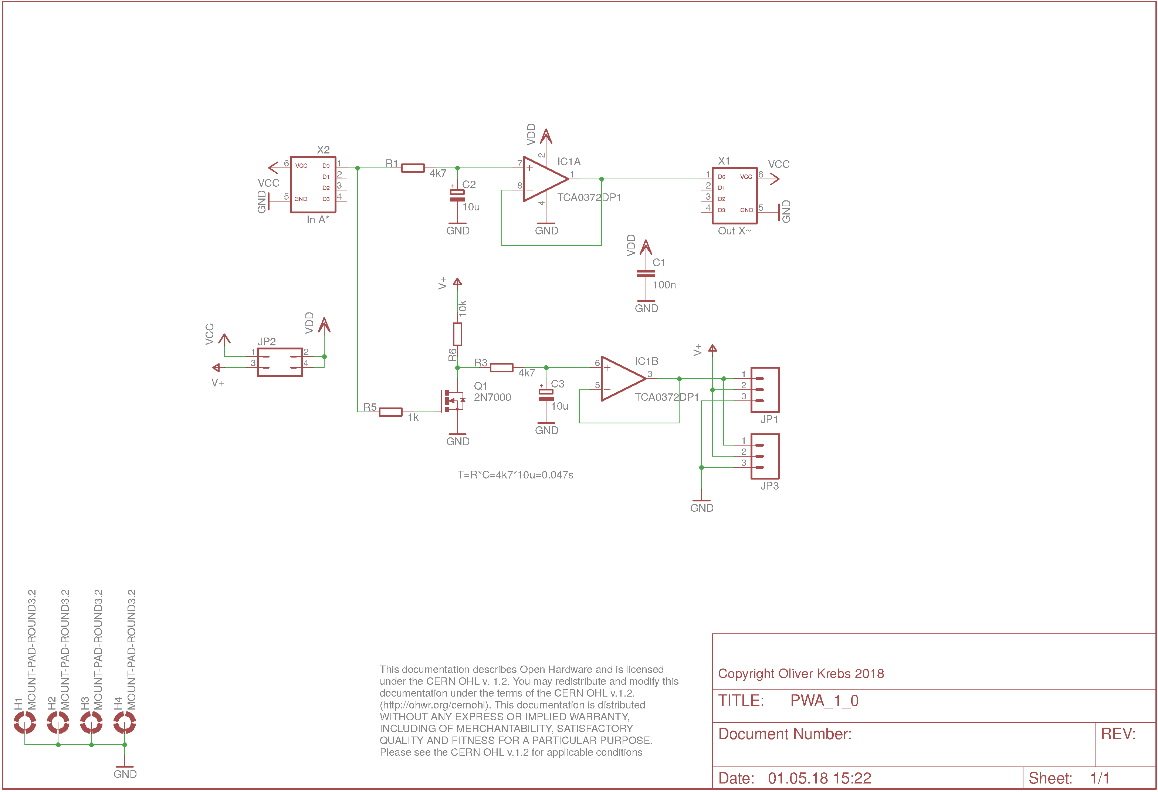
doc/PWA_1_0_sch.png
