mexdulon/tetra-Boards/doc/PWM_1_1_sch.png

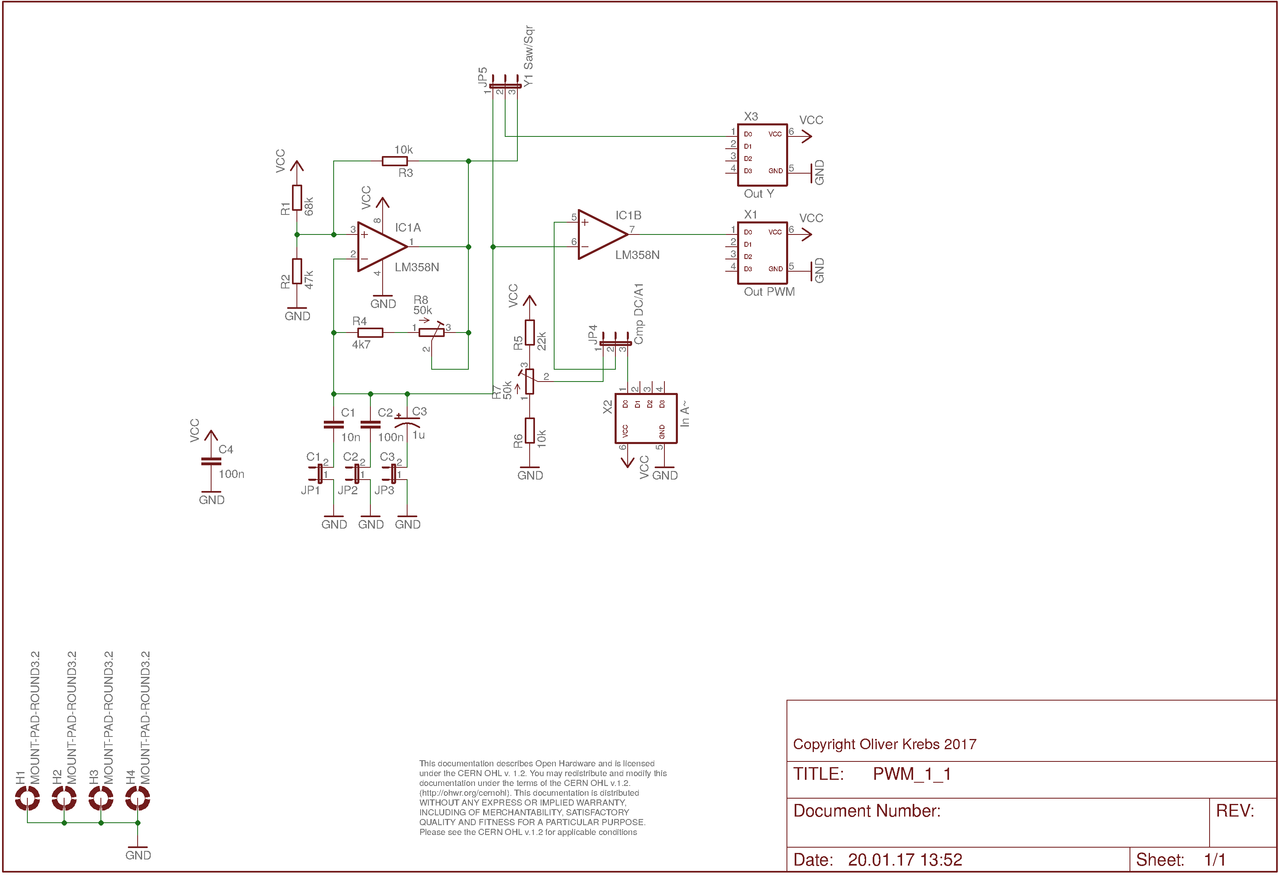
doc/PWM_1_1_sch.png
