mexdulon/tetra-Boards/doc/PWM_1_1_silk.png

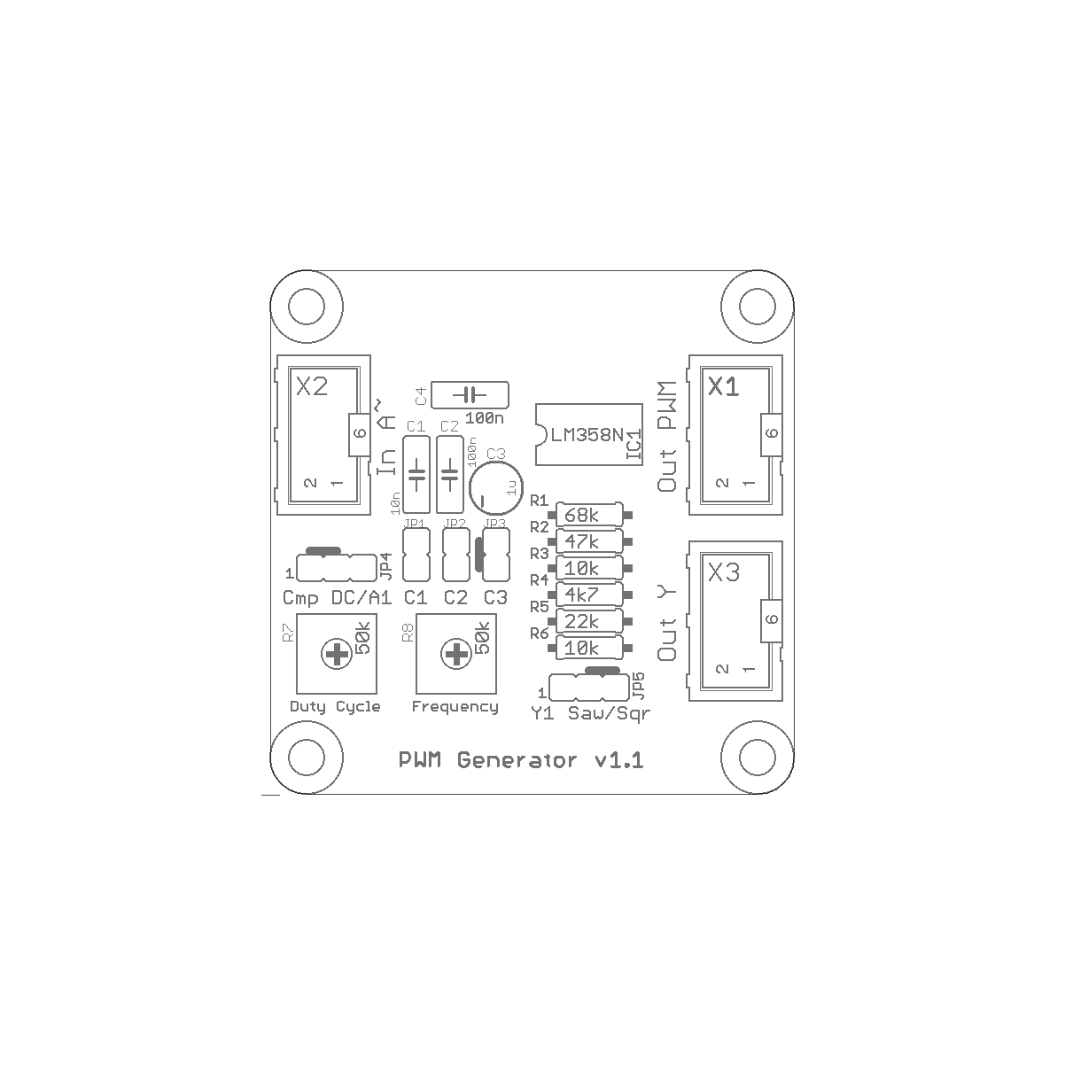
doc/PWM_1_1_silk.png
