mexdulon/tetra-Boards/doc/PWR_1_0_sch.png

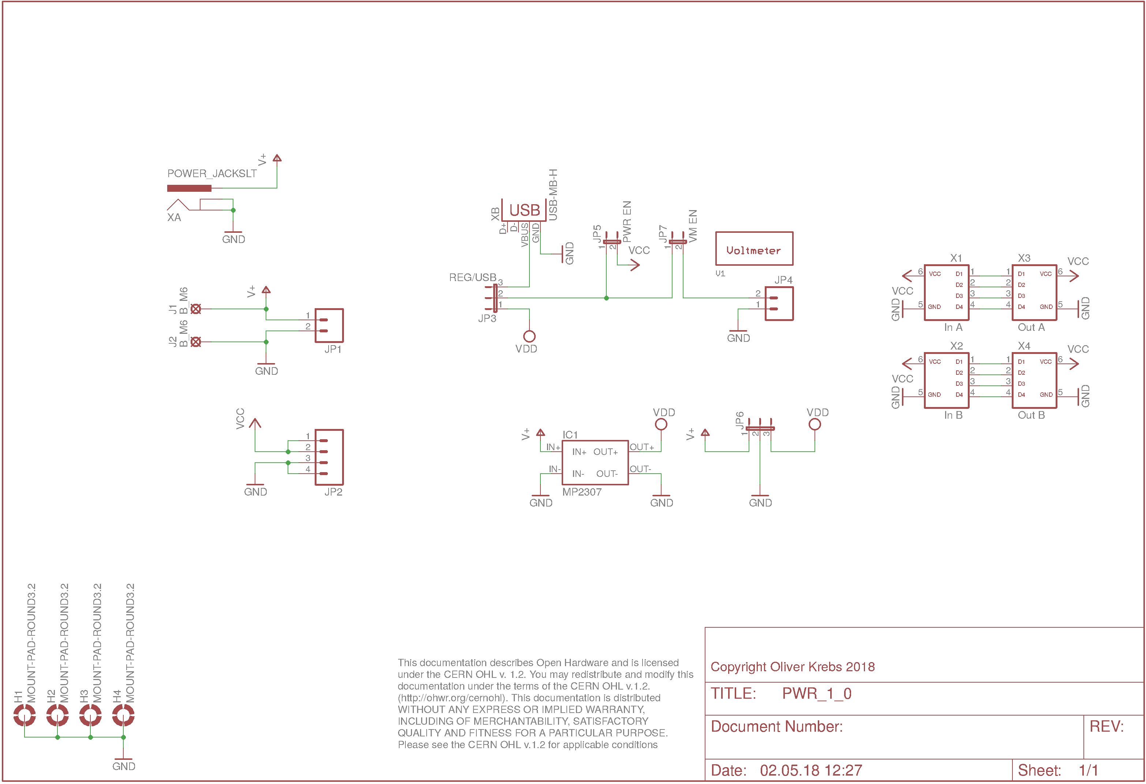
doc/PWR_1_0_sch.png
