mexdulon/tetra-Boards/doc/PWR_1_0_silk.png

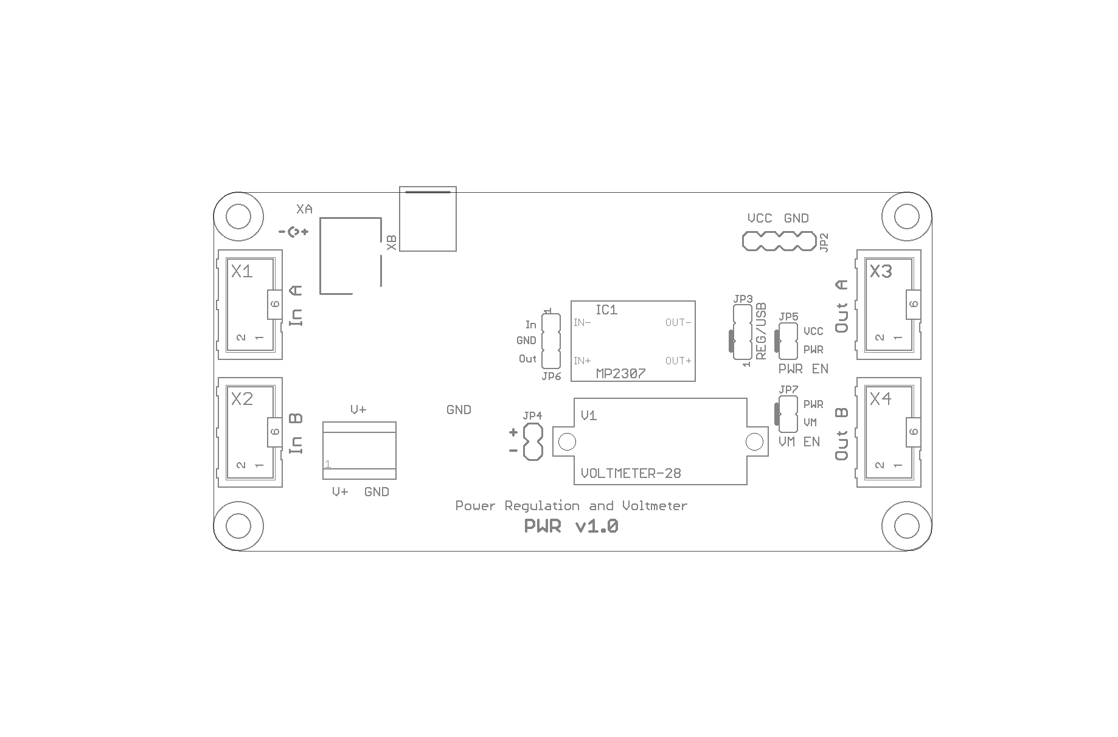
doc/PWR_1_0_silk.png
