mexdulon/tetra-Boards/doc/QRS_1_0_sch.png

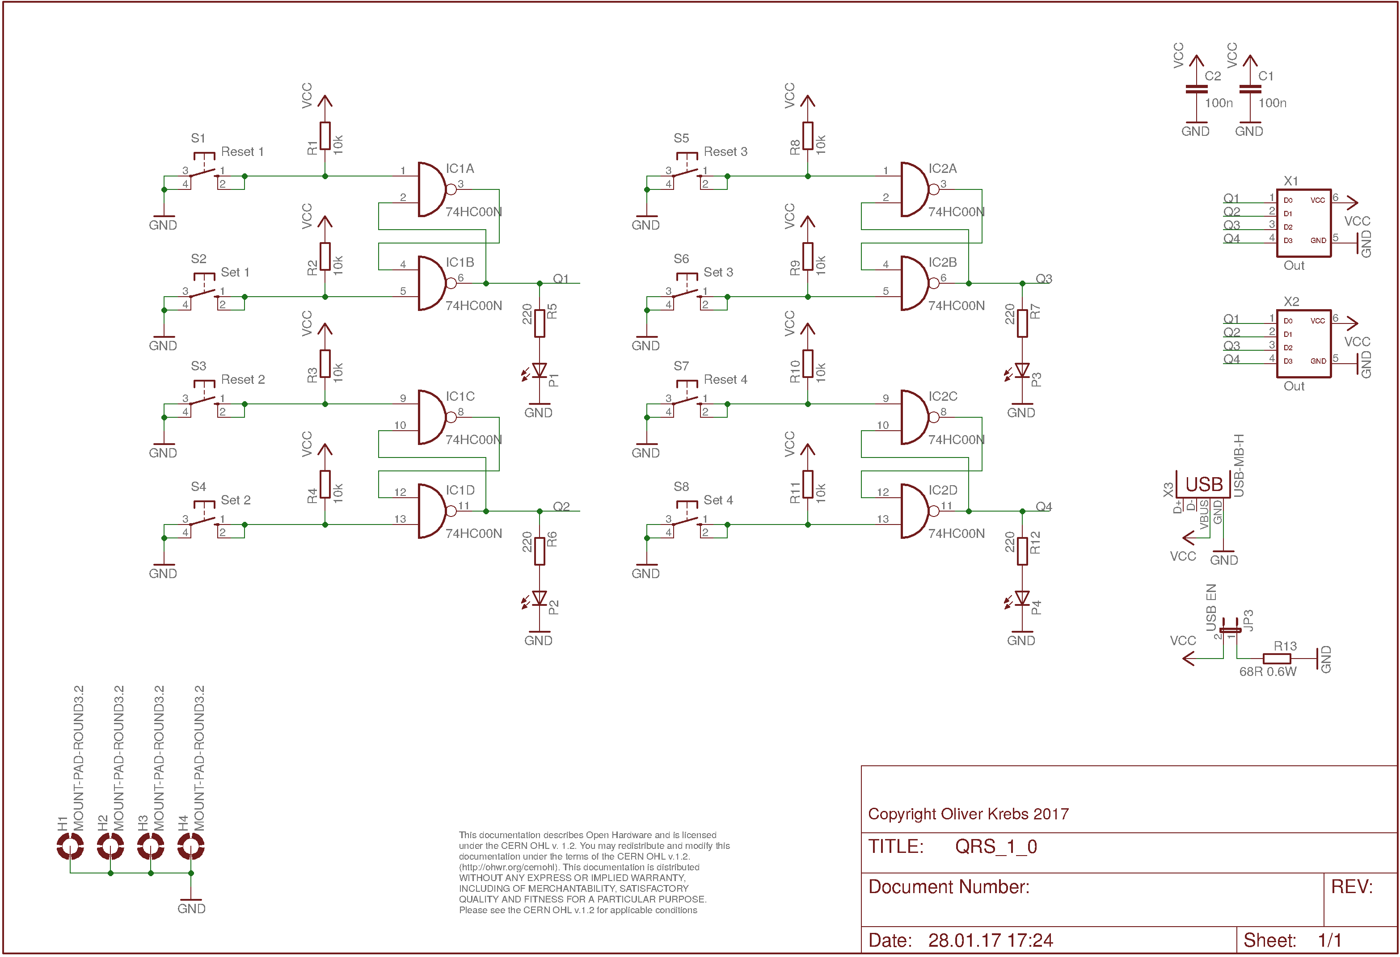
doc/QRS_1_0_sch.png
