mexdulon/tetra-Boards/doc/QRS_1_0_silk.png

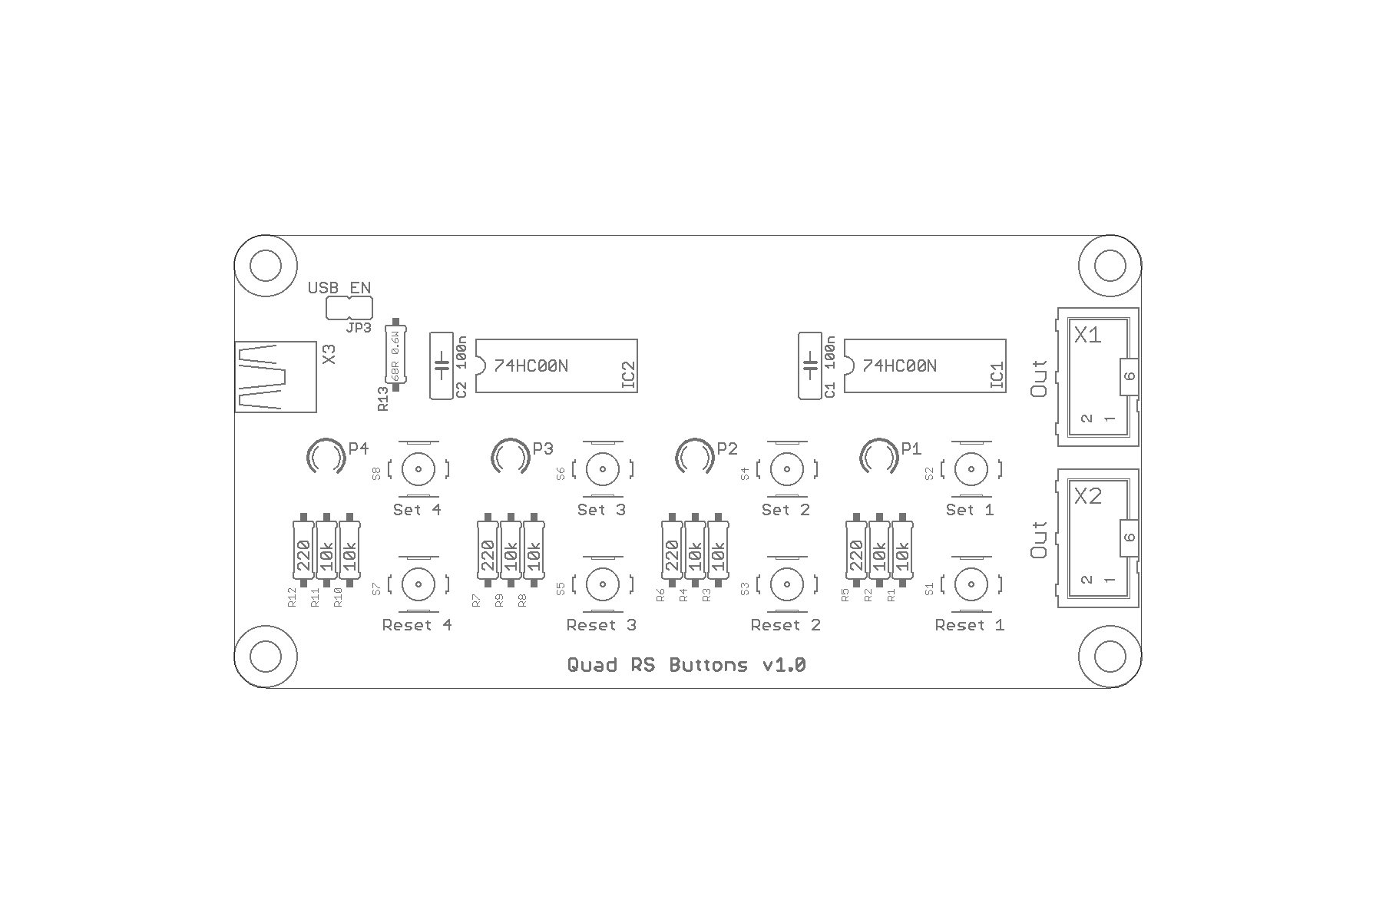
doc/QRS_1_0_silk.png
