mexdulon/tetra-Boards/doc/REG_1_0_sch.png

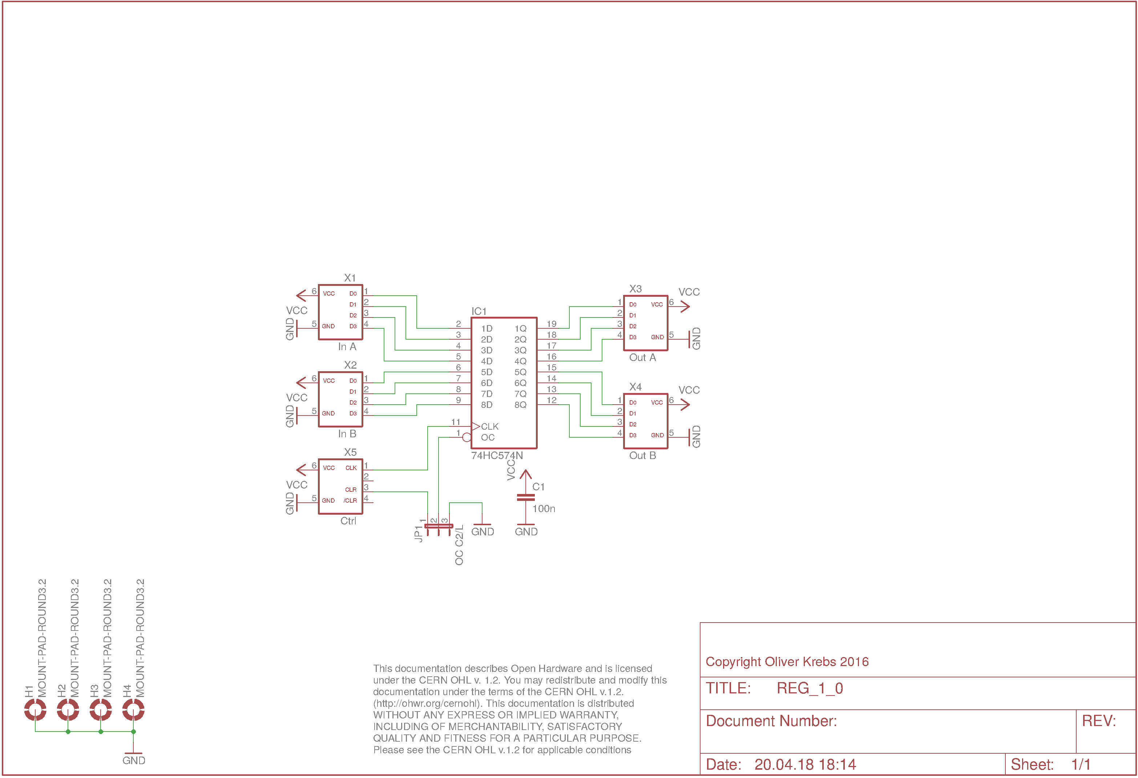
doc/REG_1_0_sch.png
