mexdulon/tetra-Boards/doc/RGB_1_1_b_sch.png

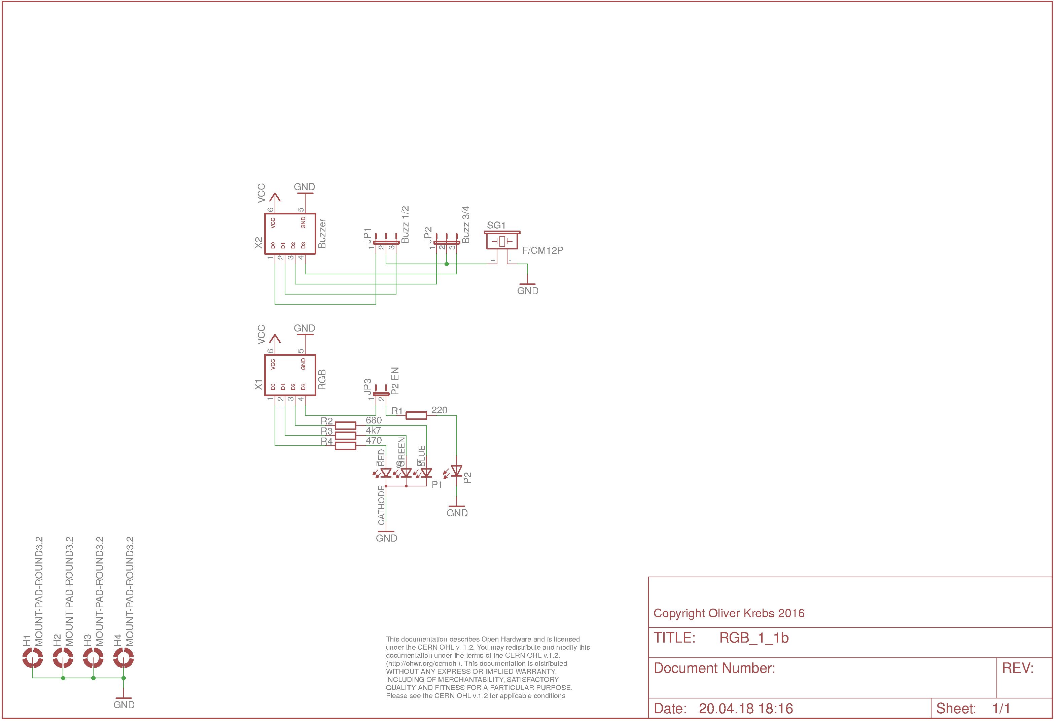
doc/RGB_1_1_b_sch.png
