mexdulon/tetra-Boards/doc/RGB_1_1_sch.png

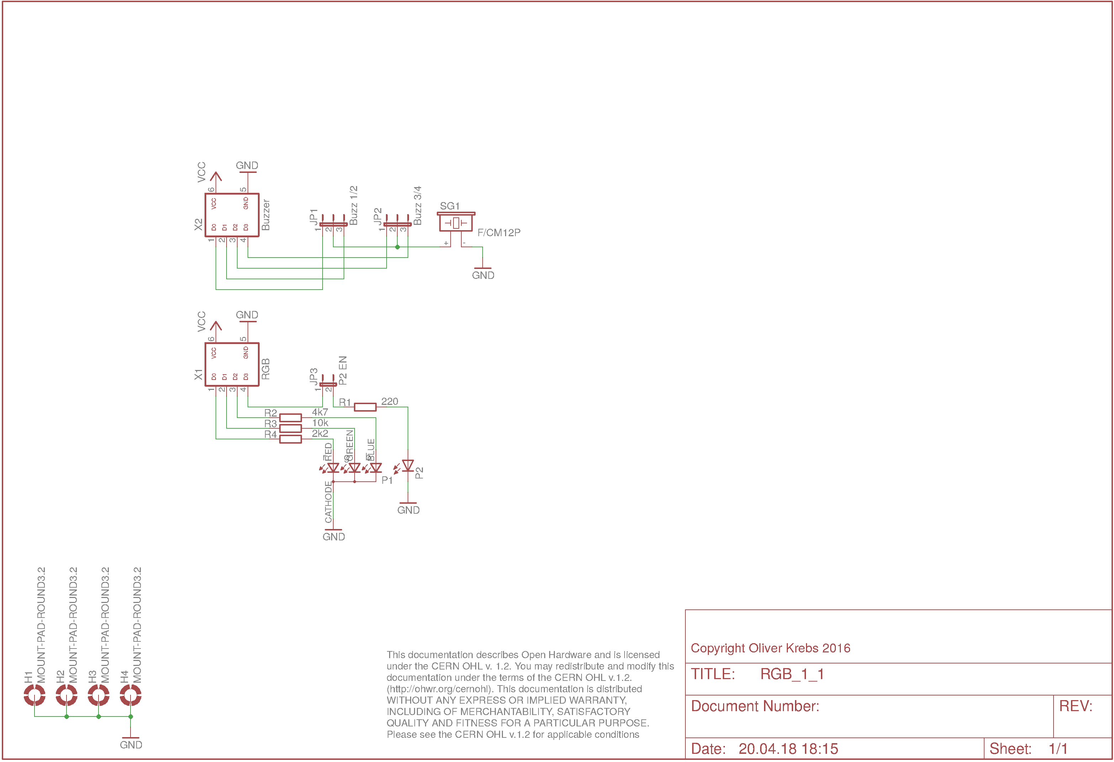
doc/RGB_1_1_sch.png
