mexdulon/tetra-Boards/doc/RGF_2_0_sch.png

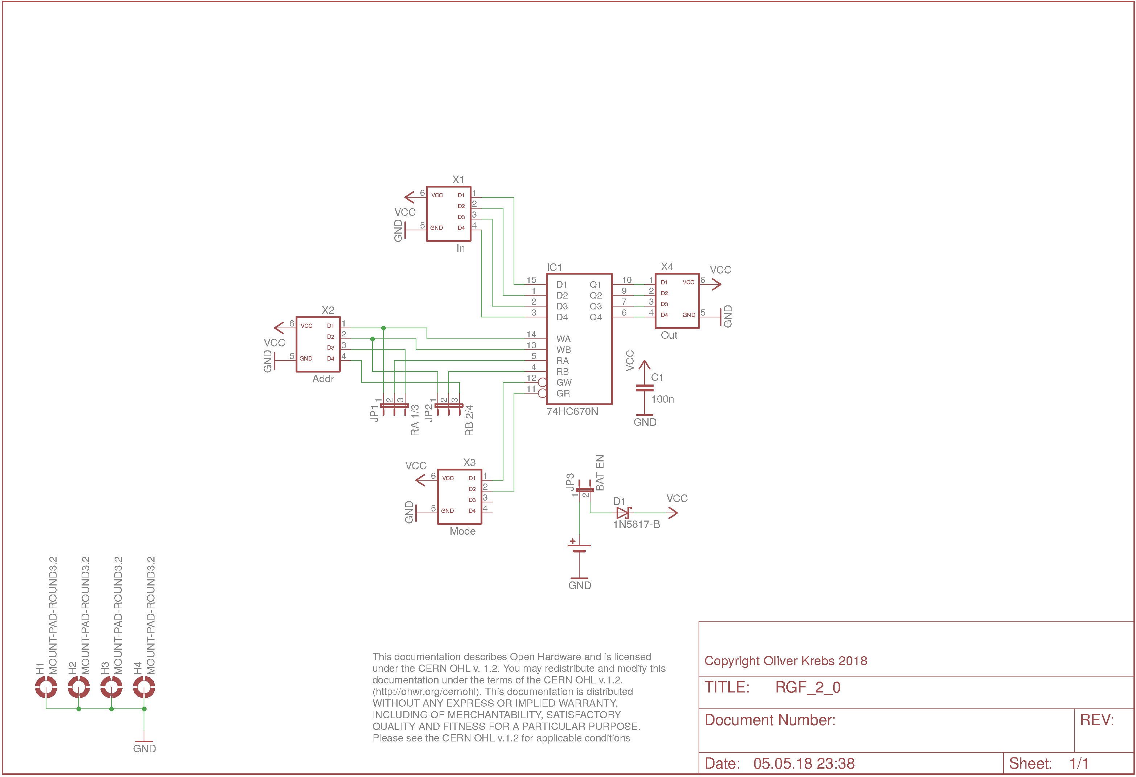
doc/RGF_2_0_sch.png
