mexdulon/tetra-Boards/doc/RLY_1_0_sch.png

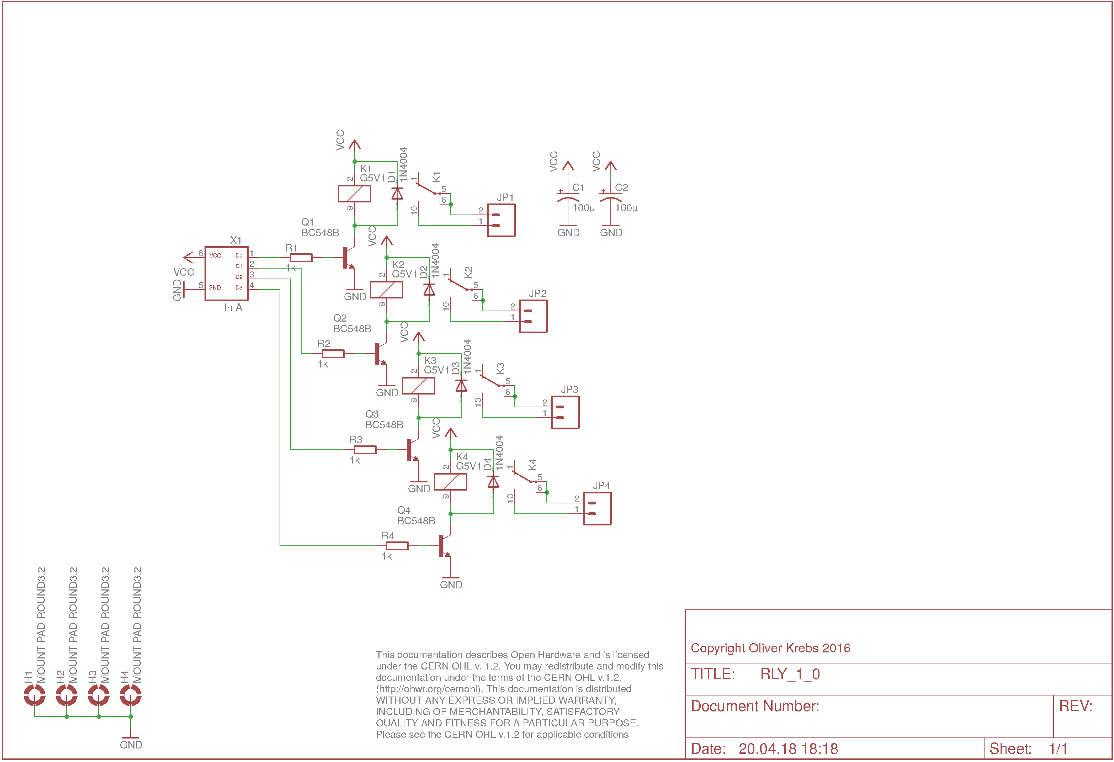
doc/RLY_1_0_sch.png
