mexdulon/tetra-Boards/doc/RSG_1_0_sch.png

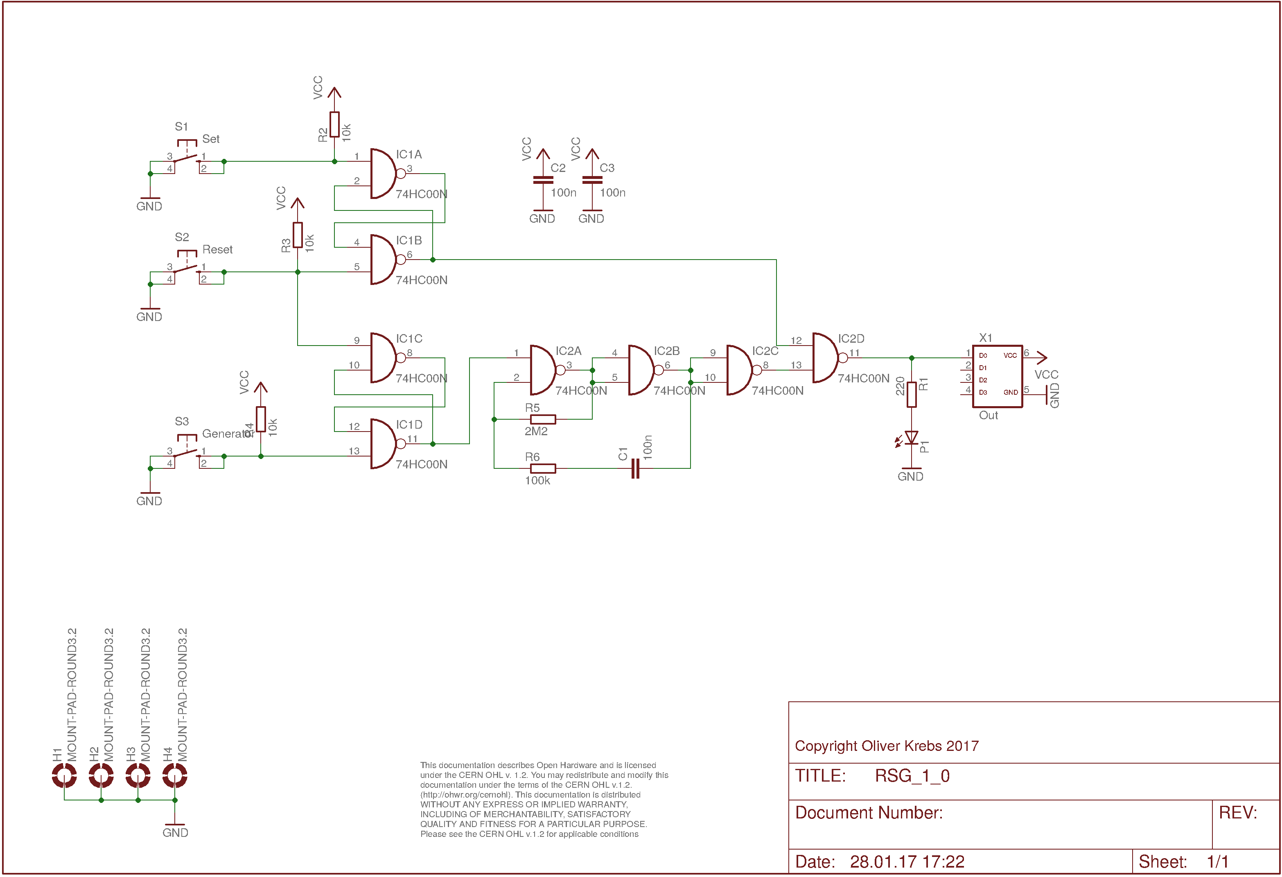
doc/RSG_1_0_sch.png
