mexdulon/tetra-Boards/doc/RSG_1_0_silk.png

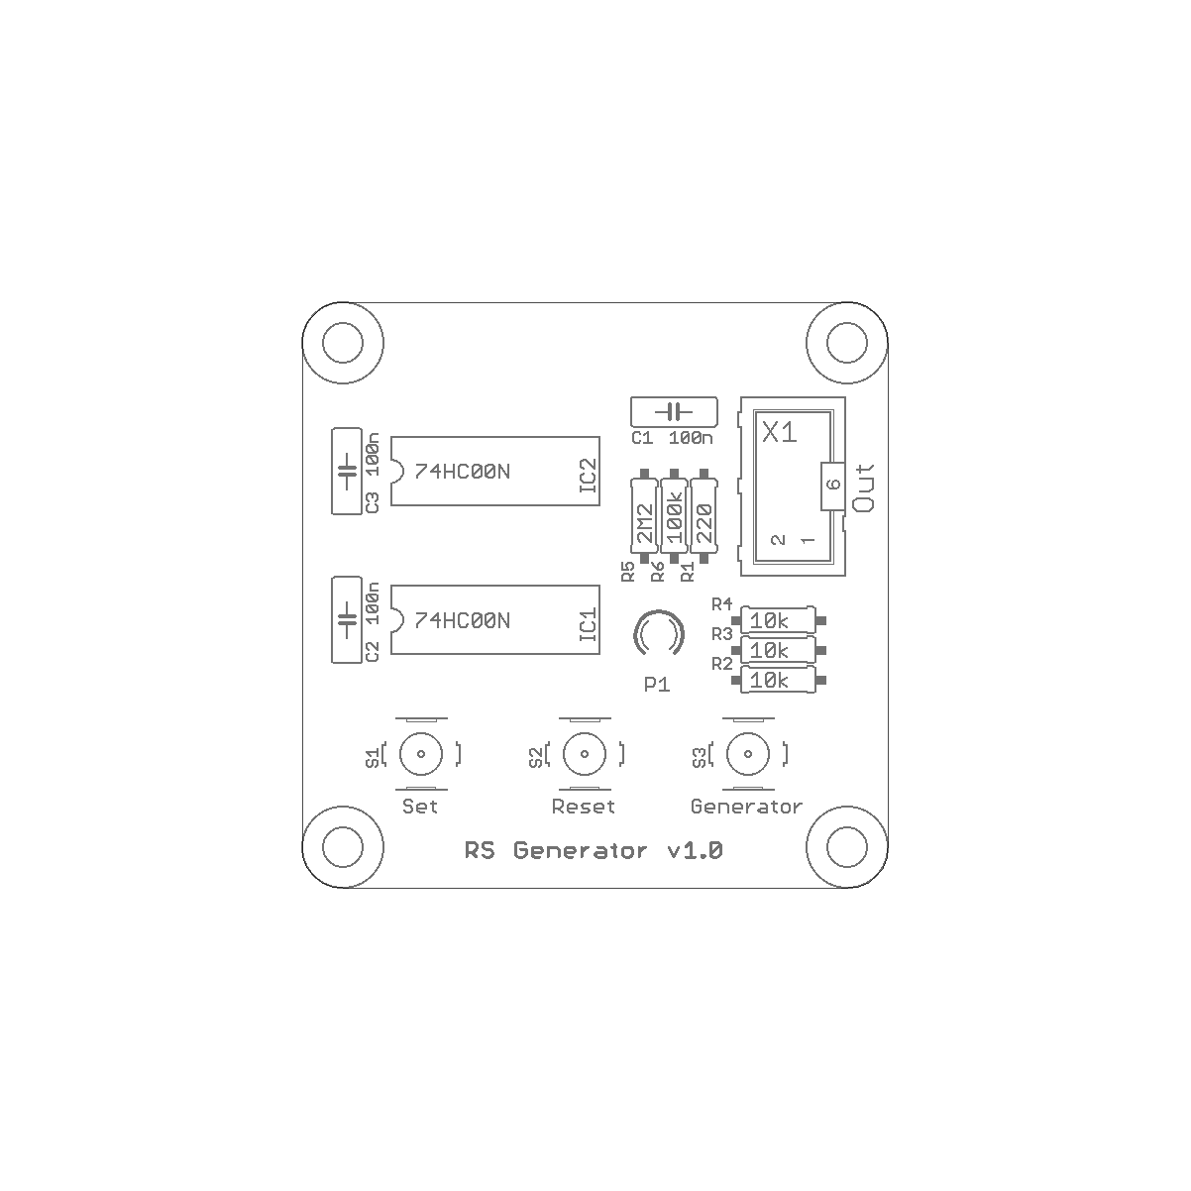
doc/RSG_1_0_silk.png
