mexdulon/tetra-Boards/doc/SAD_1_1_sch.png

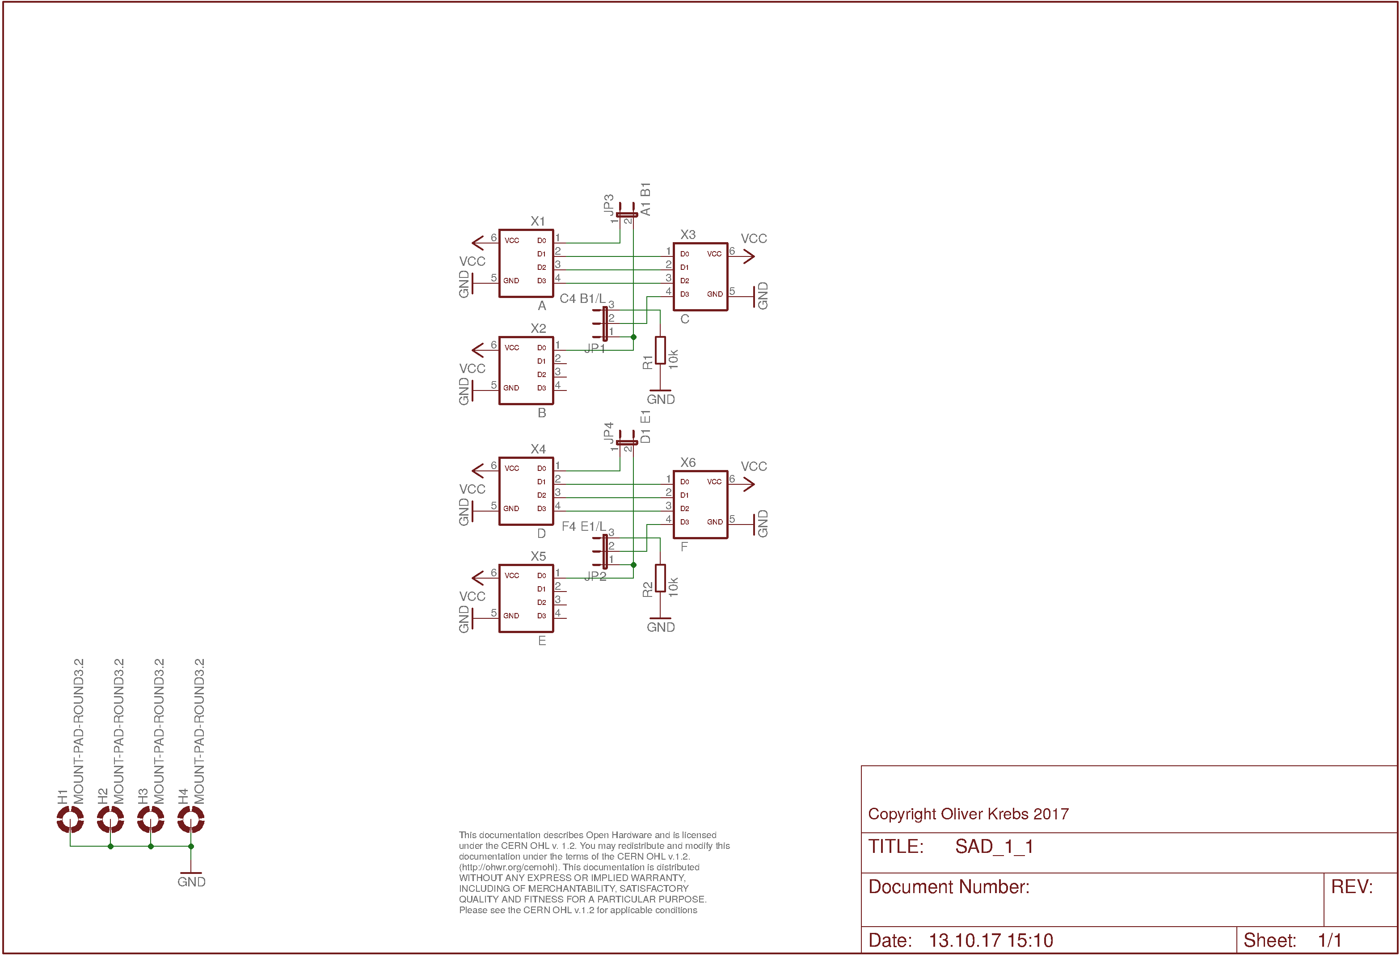
doc/SAD_1_1_sch.png
