mexdulon/tetra-Boards/doc/SOC_1_0_sch.png

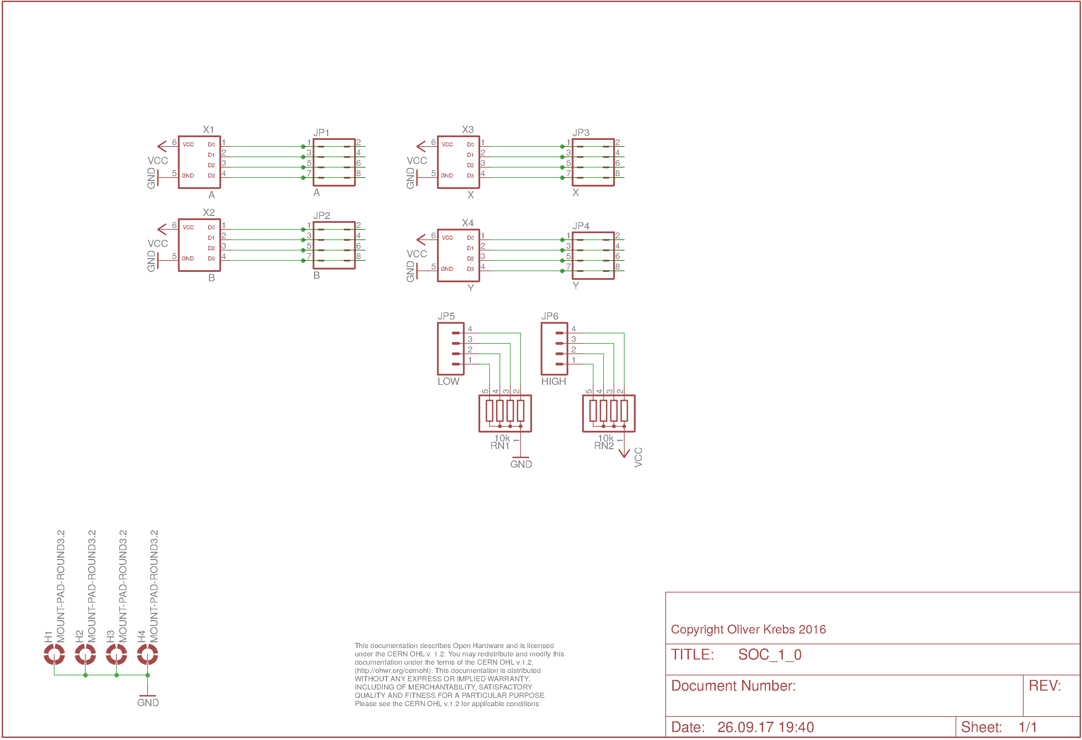
doc/SOC_1_0_sch.png
