mexdulon/tetra-Boards/doc/SOC_1_0_silk.png

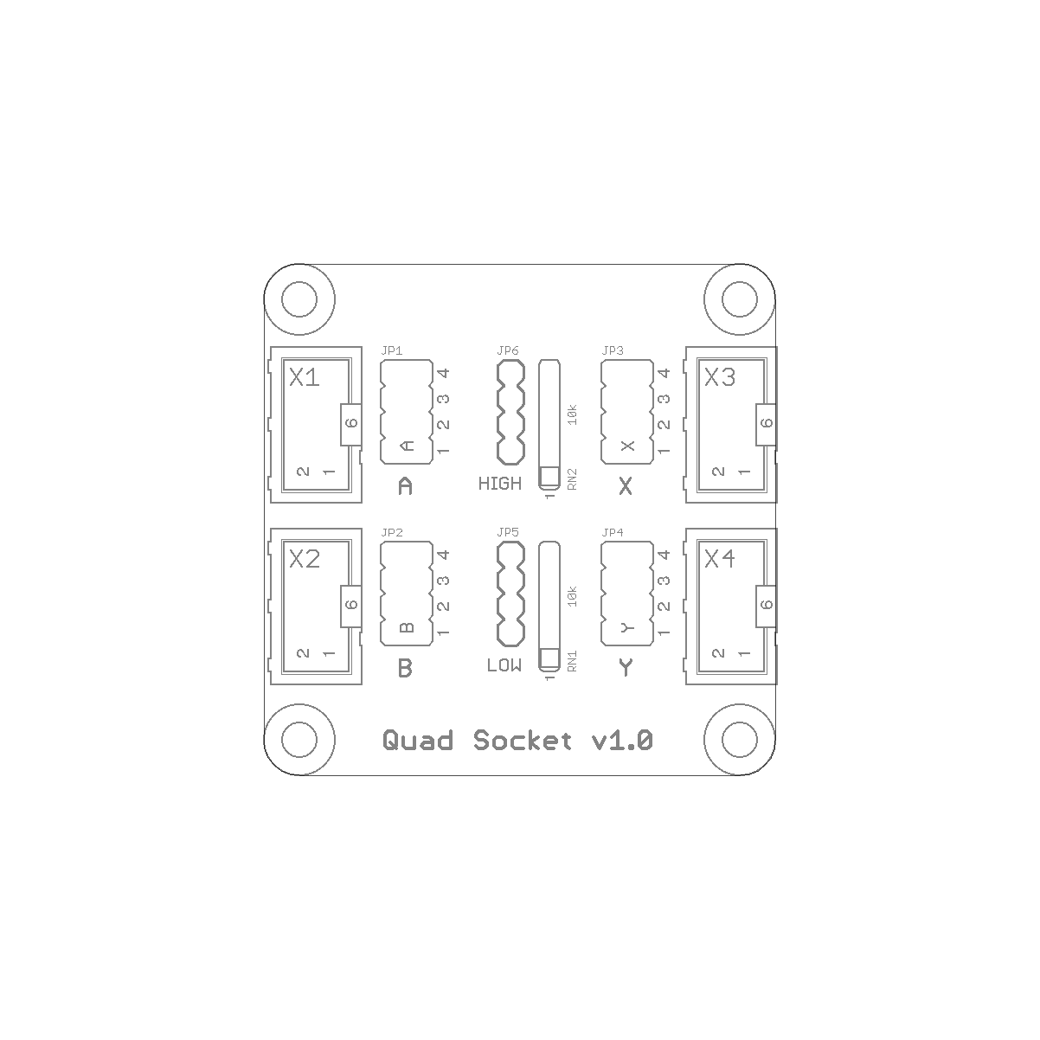
doc/SOC_1_0_silk.png
