mexdulon/tetra-Boards/doc/SOC_2_0_sch.png

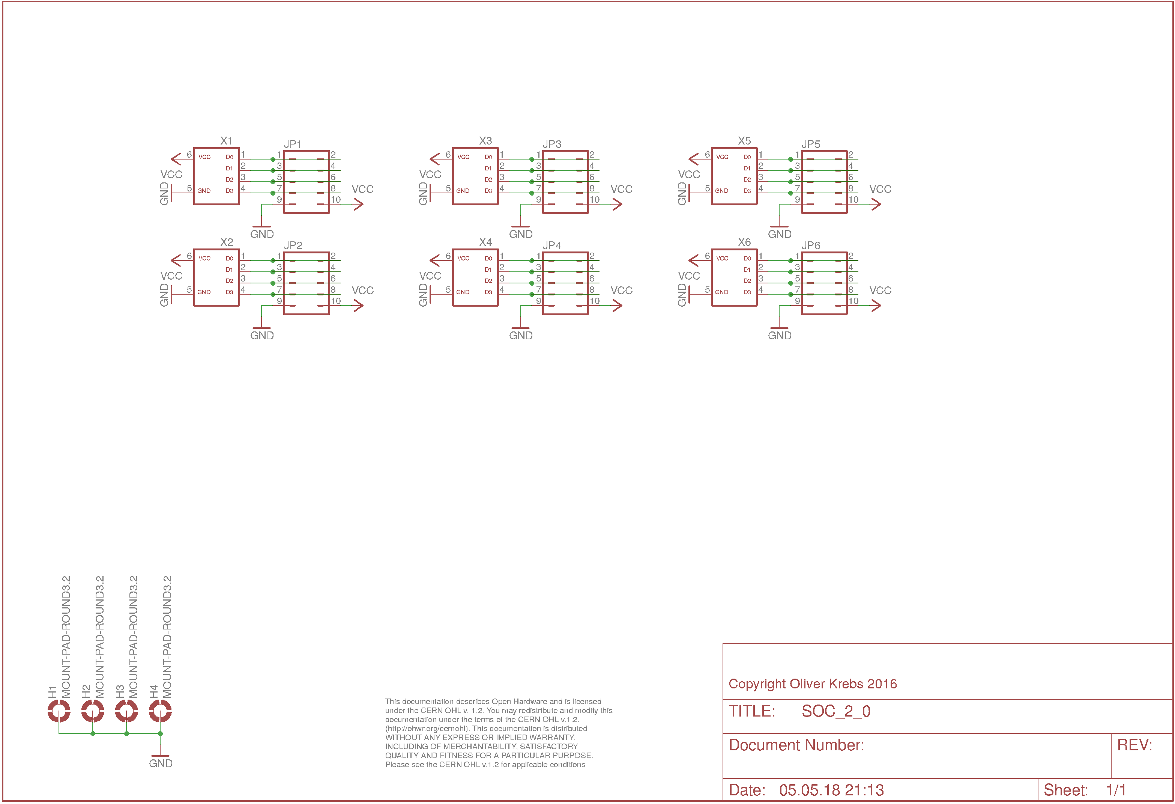
doc/SOC_2_0_sch.png
