mexdulon/tetra-Boards/doc/SPL_1_0_sch.png

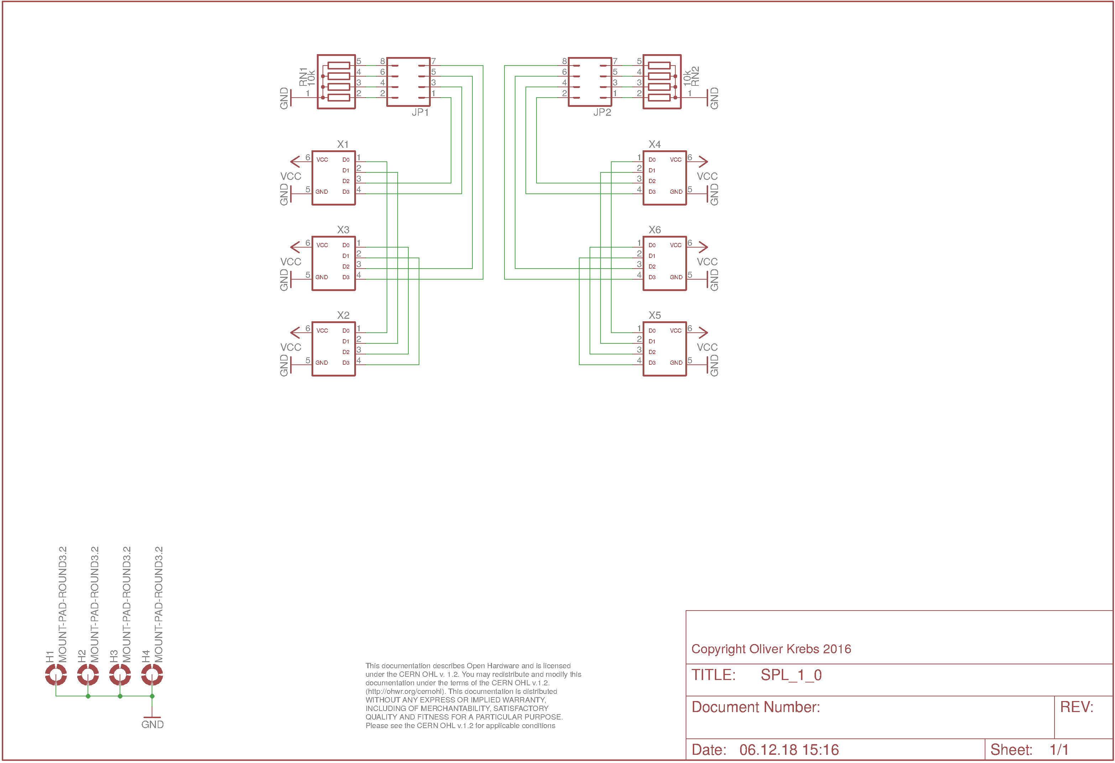
doc/SPL_1_0_sch.png
