mexdulon/tetra-Boards/doc/SRC_1_0_sch.png

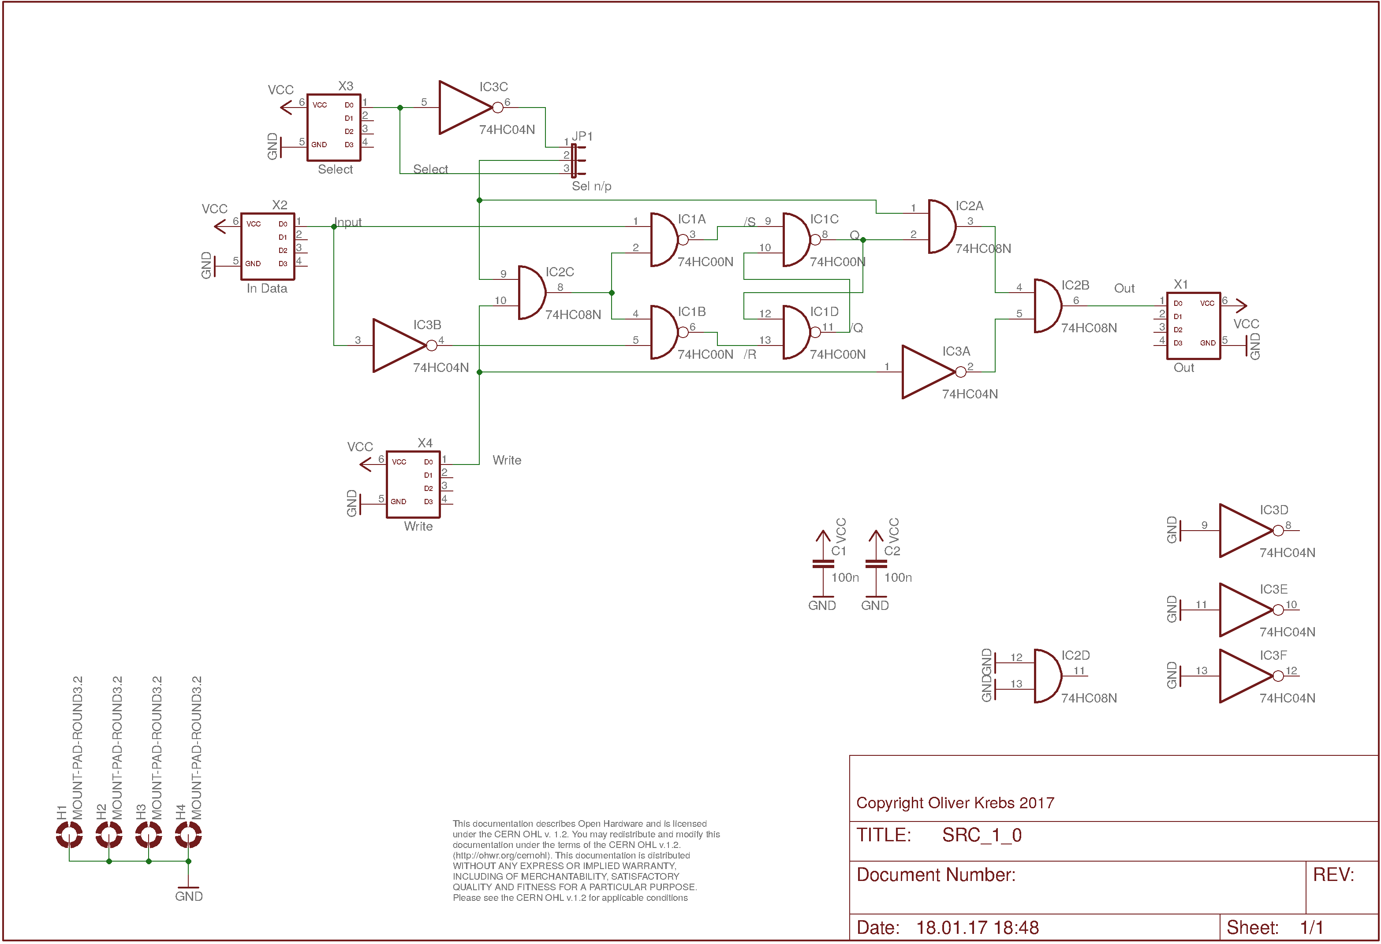
doc/SRC_1_0_sch.png
