mexdulon/tetra-Boards/doc/SRG_1_0_sch.png

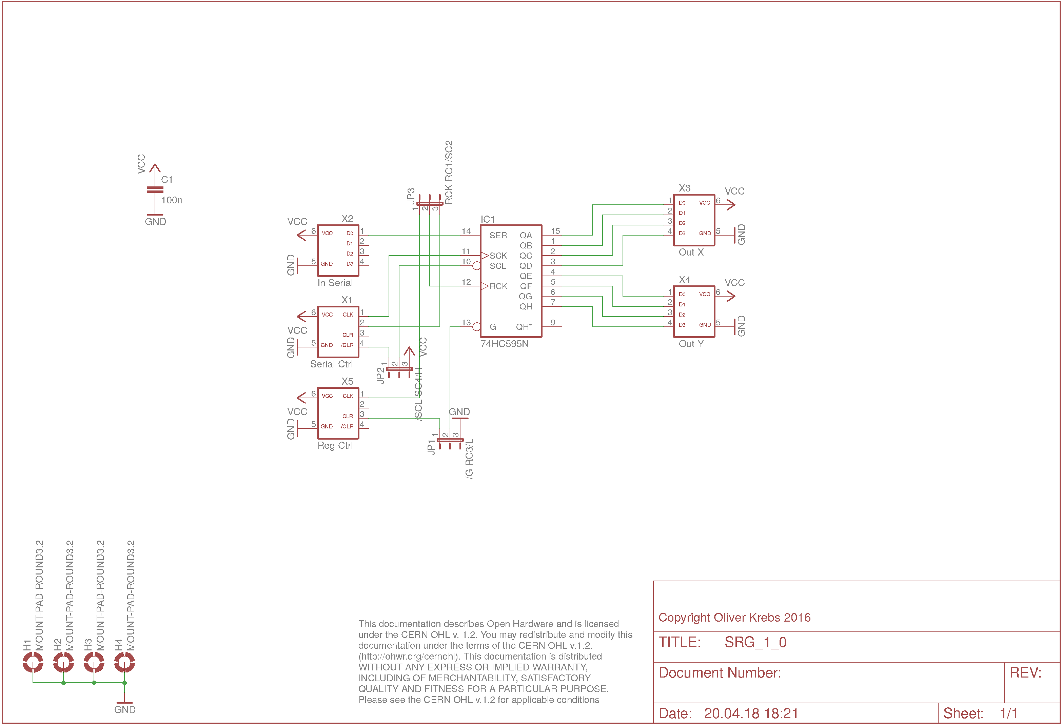
doc/SRG_1_0_sch.png
