mexdulon/tetra-Boards/doc/SWG_1_1_sch.png

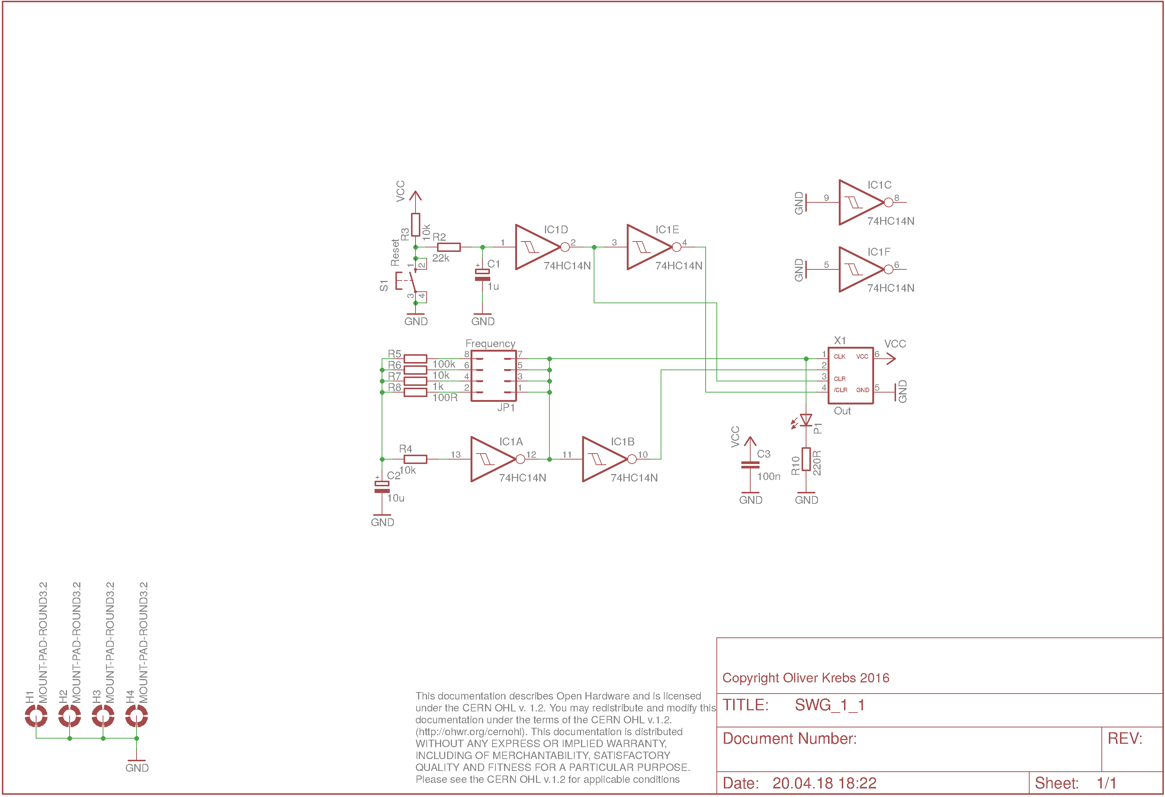
doc/SWG_1_1_sch.png
