mexdulon/tetra-Boards/doc/SWG_1_1_silk.png

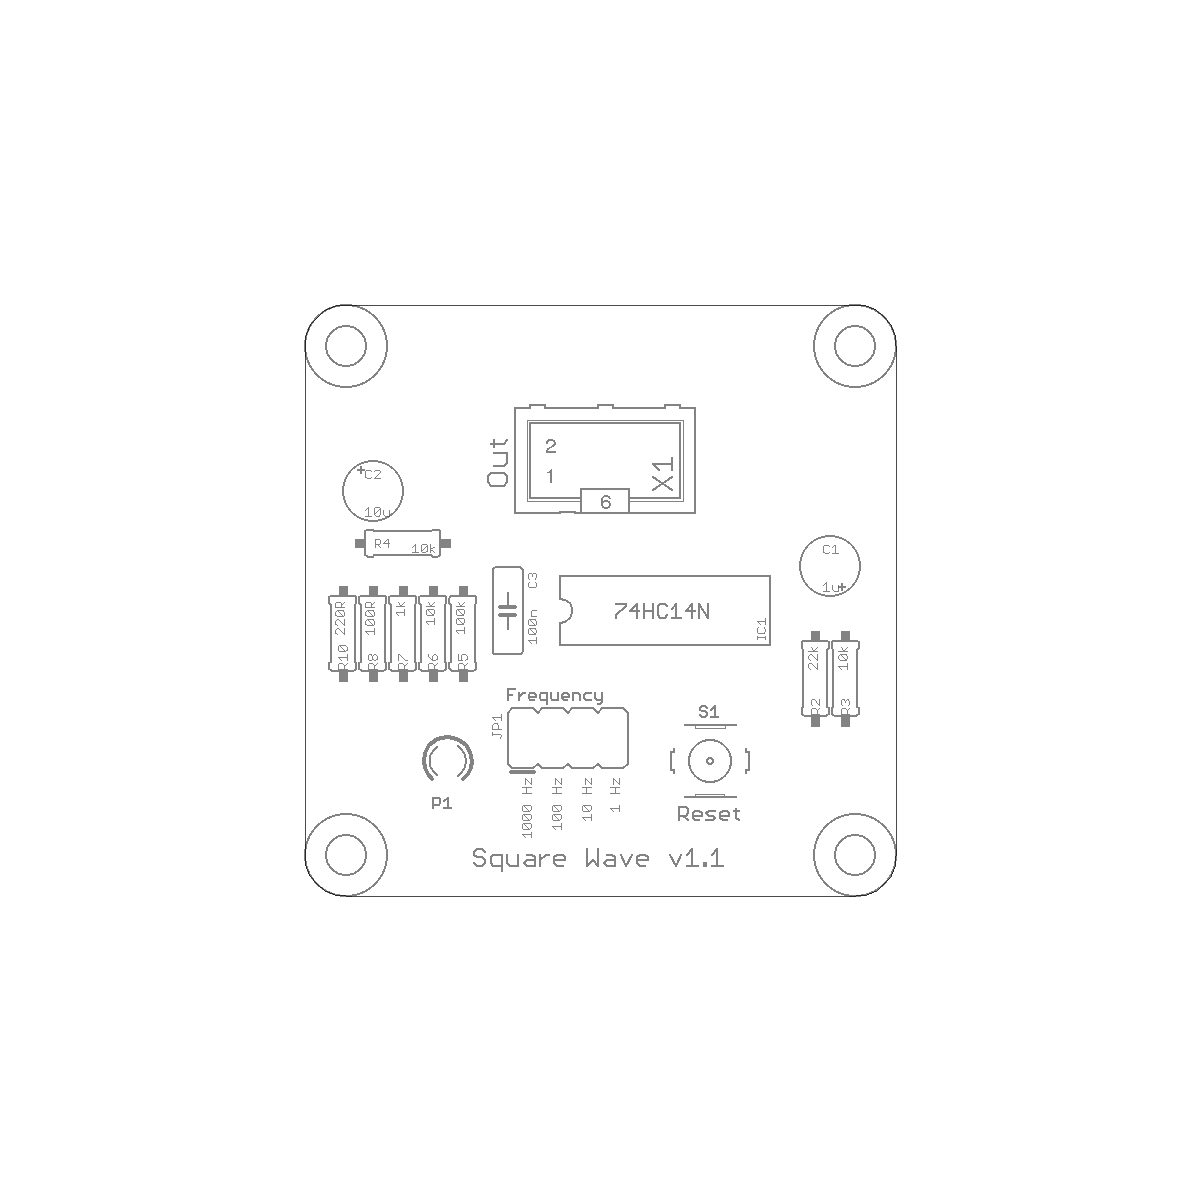
doc/SWG_1_1_silk.png
