mexdulon/tetra-Boards/doc/SWI_1_0_sch.png

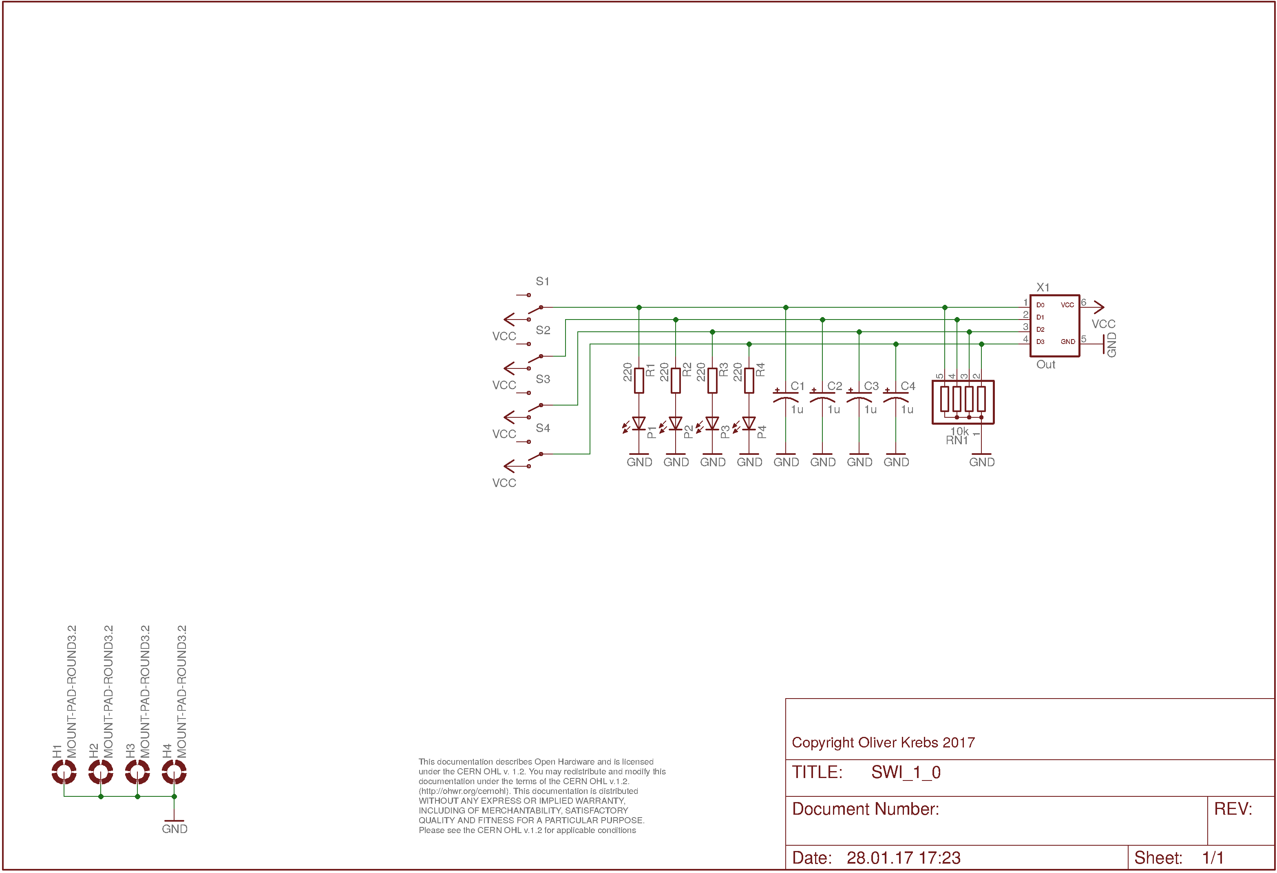
doc/SWI_1_0_sch.png
