mexdulon/tetra-Boards/doc/SWI_1_1_sch.png

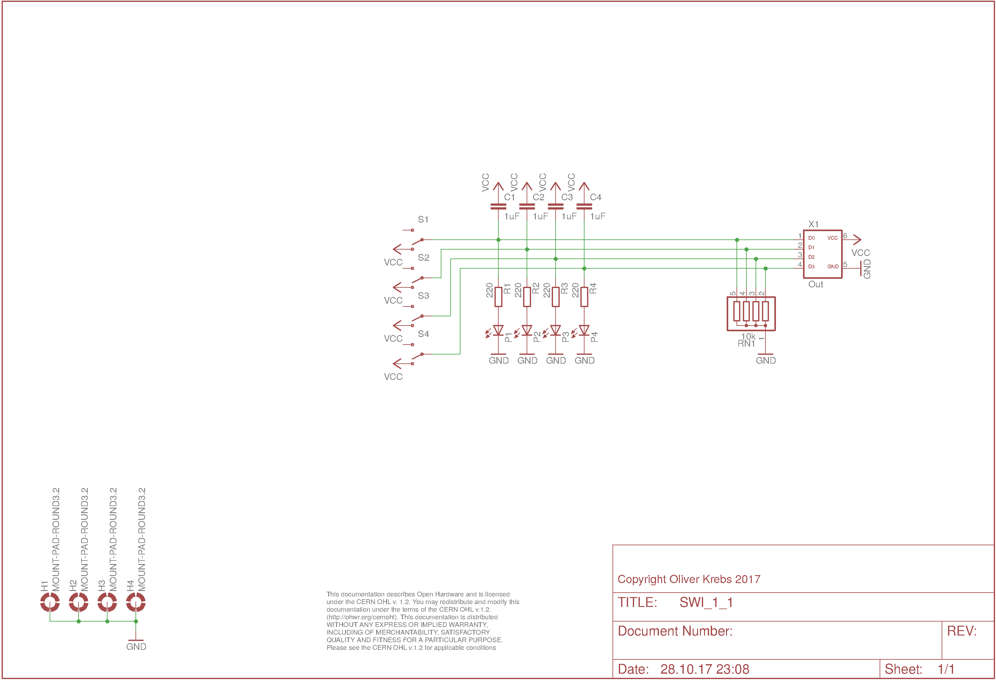
doc/SWI_1_1_sch.png
