mexdulon/tetra-Boards/doc/TFF_1_0_sch.png

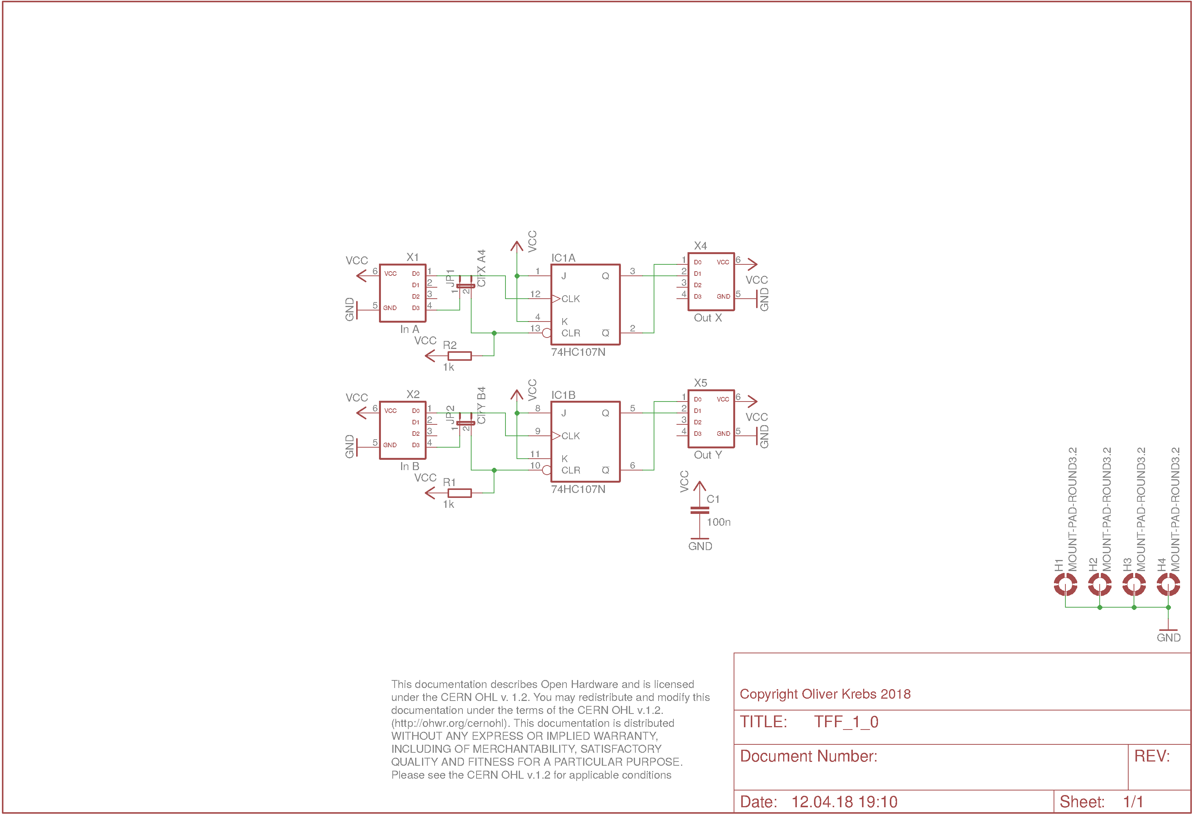
doc/TFF_1_0_sch.png
