mexdulon/tetra-Boards/doc/TMP_1_0_sch.png

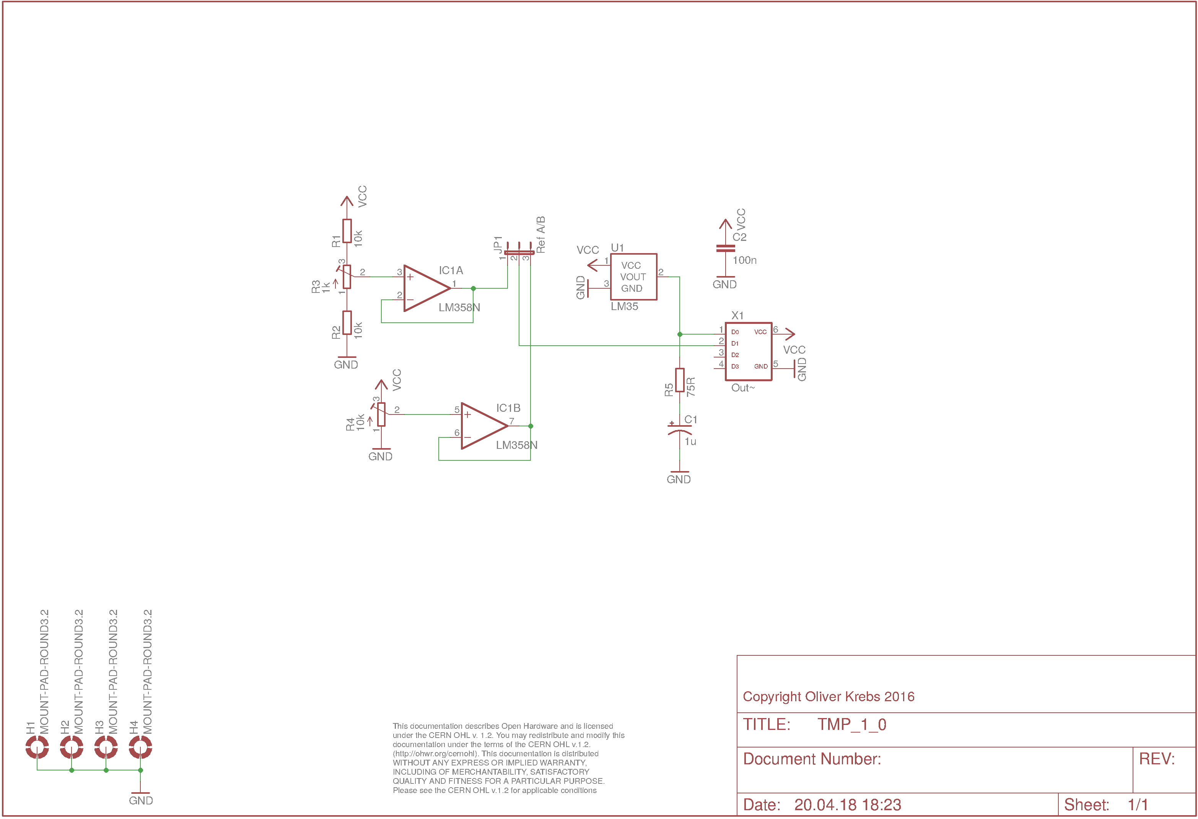
doc/TMP_1_0_sch.png
