mexdulon/tetra-Boards/doc/TMP_1_0_silk.png

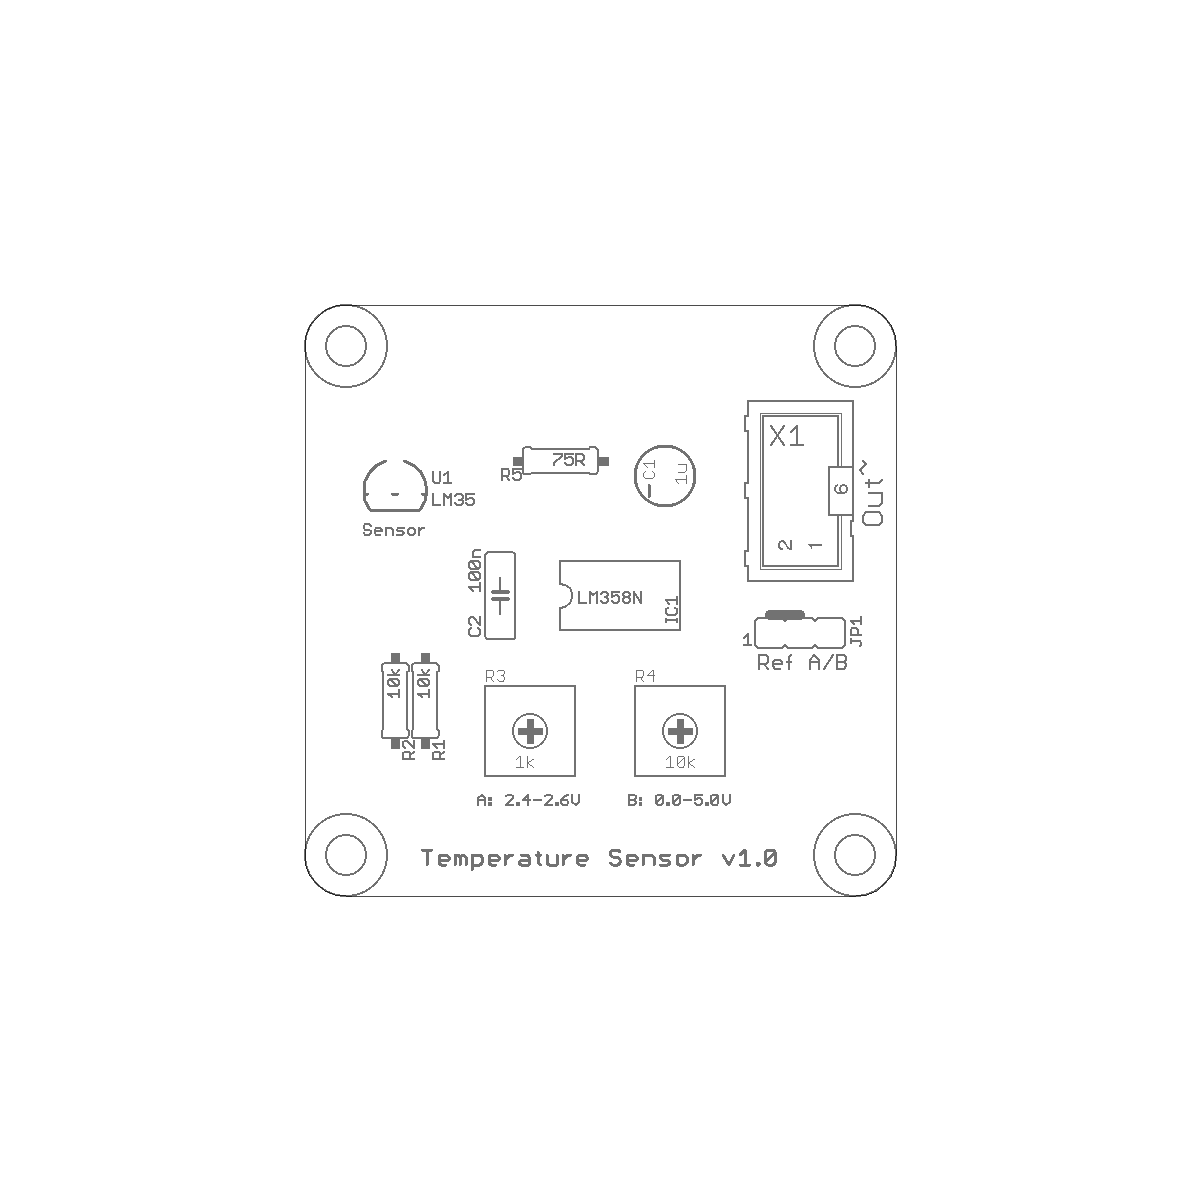
doc/TMP_1_0_silk.png
