mexdulon/tetra-Boards/doc/UNI_1_1_sch.png

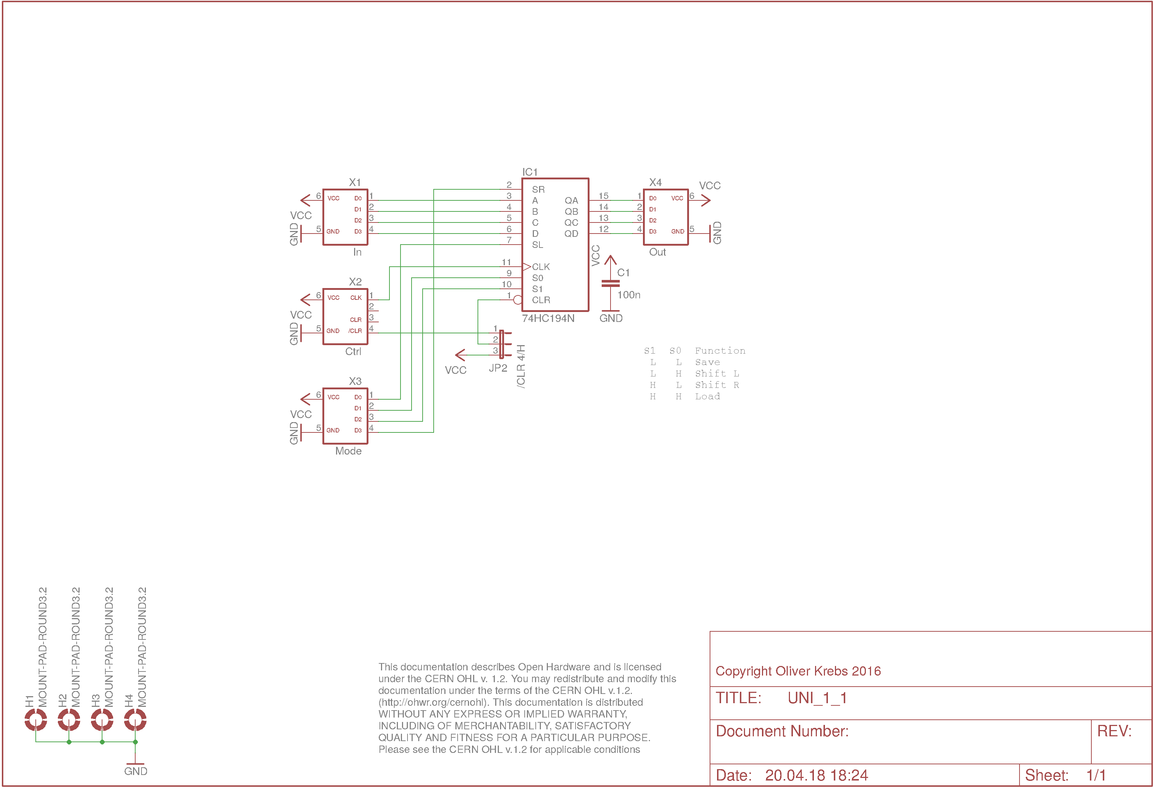
doc/UNI_1_1_sch.png
