mexdulon/tetra-Boards/doc/VLT_1_0_sch.png

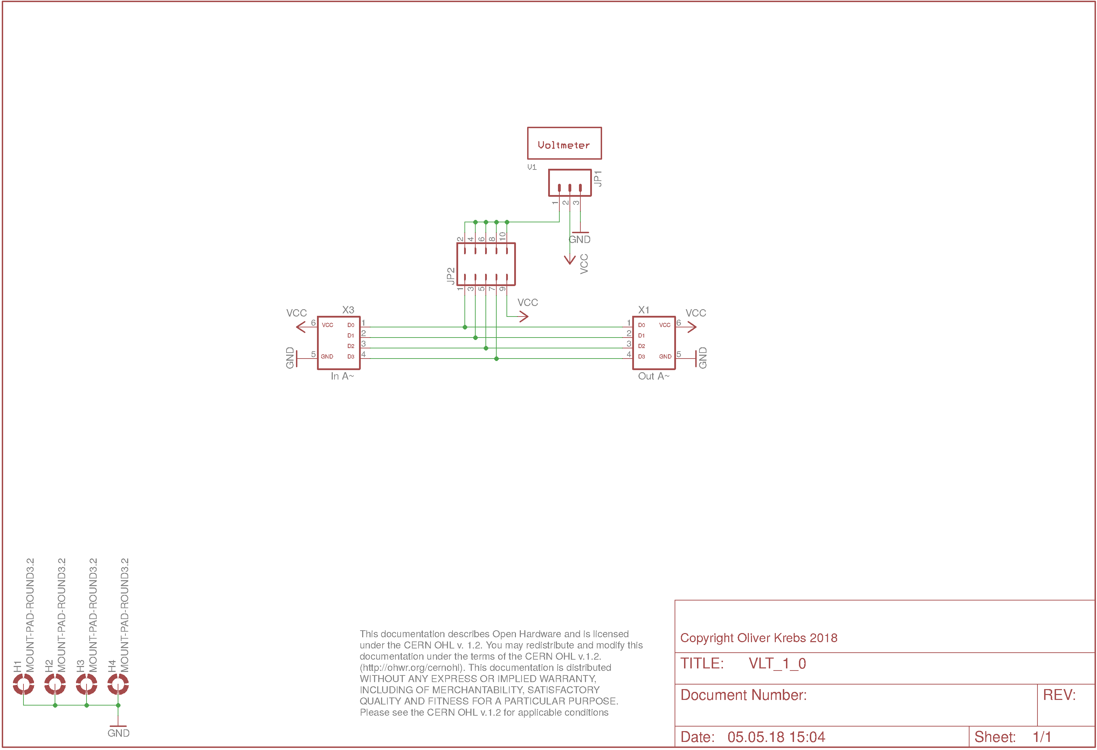
doc/VLT_1_0_sch.png
