mexdulon/tetra-Boards/doc/WNG_1_0_sch.png

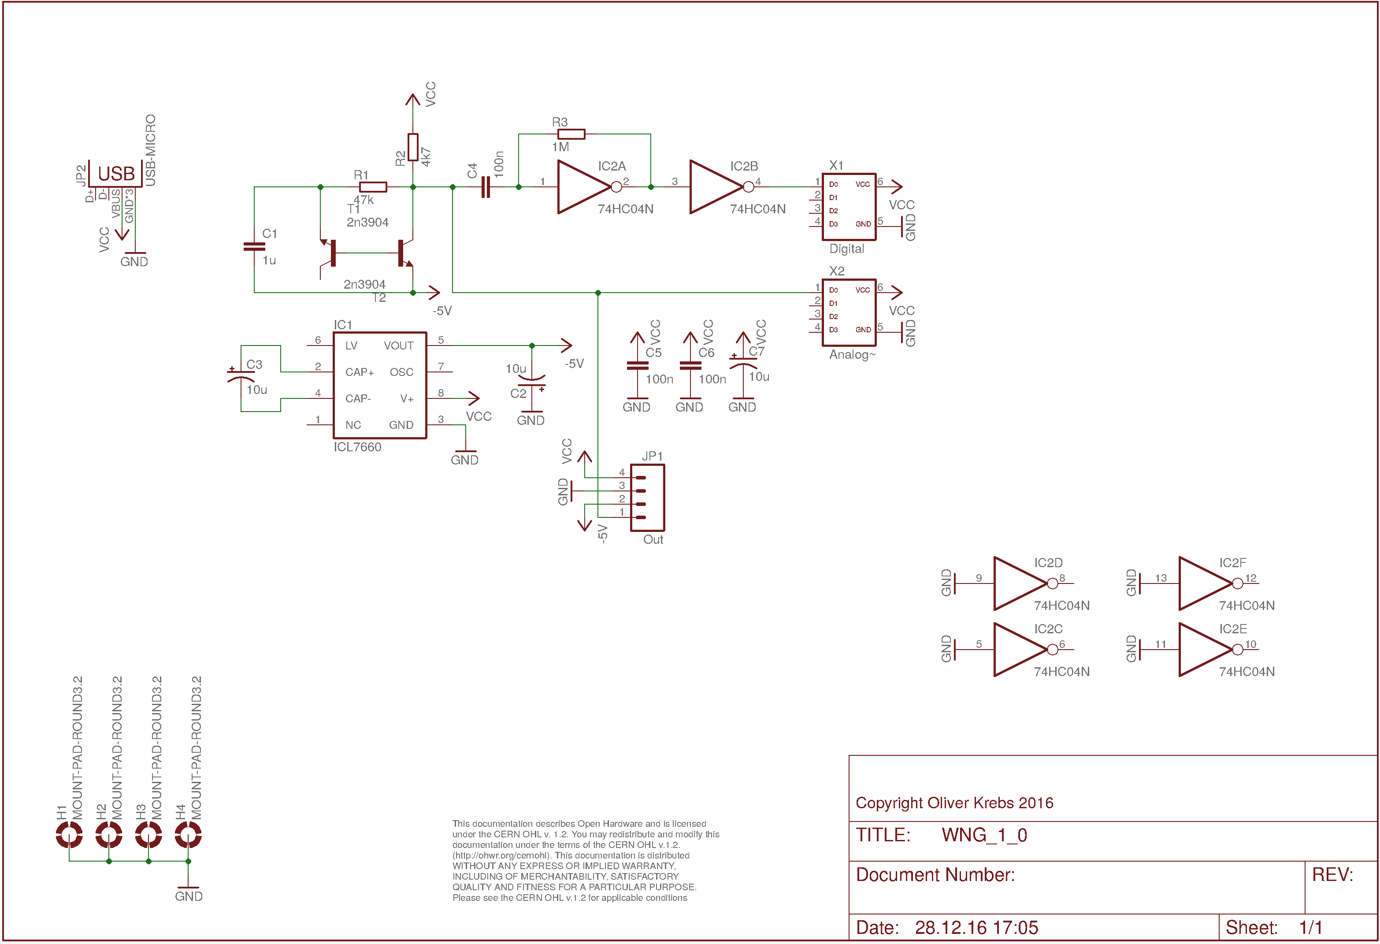
doc/WNG_1_0_sch.png
