mexdulon/tetra-Boards/doc/WNG_1_0_silk.png

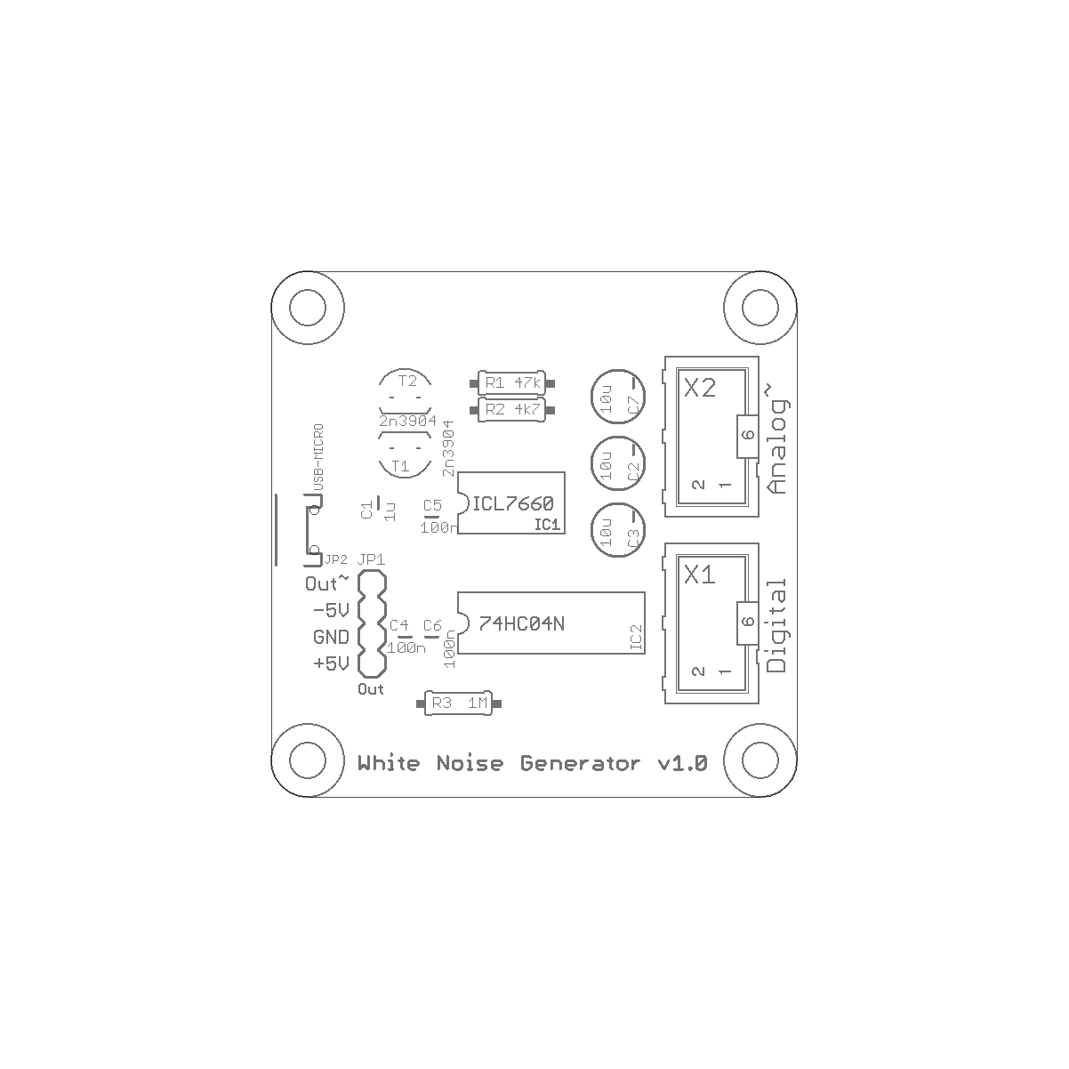
doc/WNG_1_0_silk.png
