mexdulon/tetra-Boards/doc/XOR_1_1_sch.png

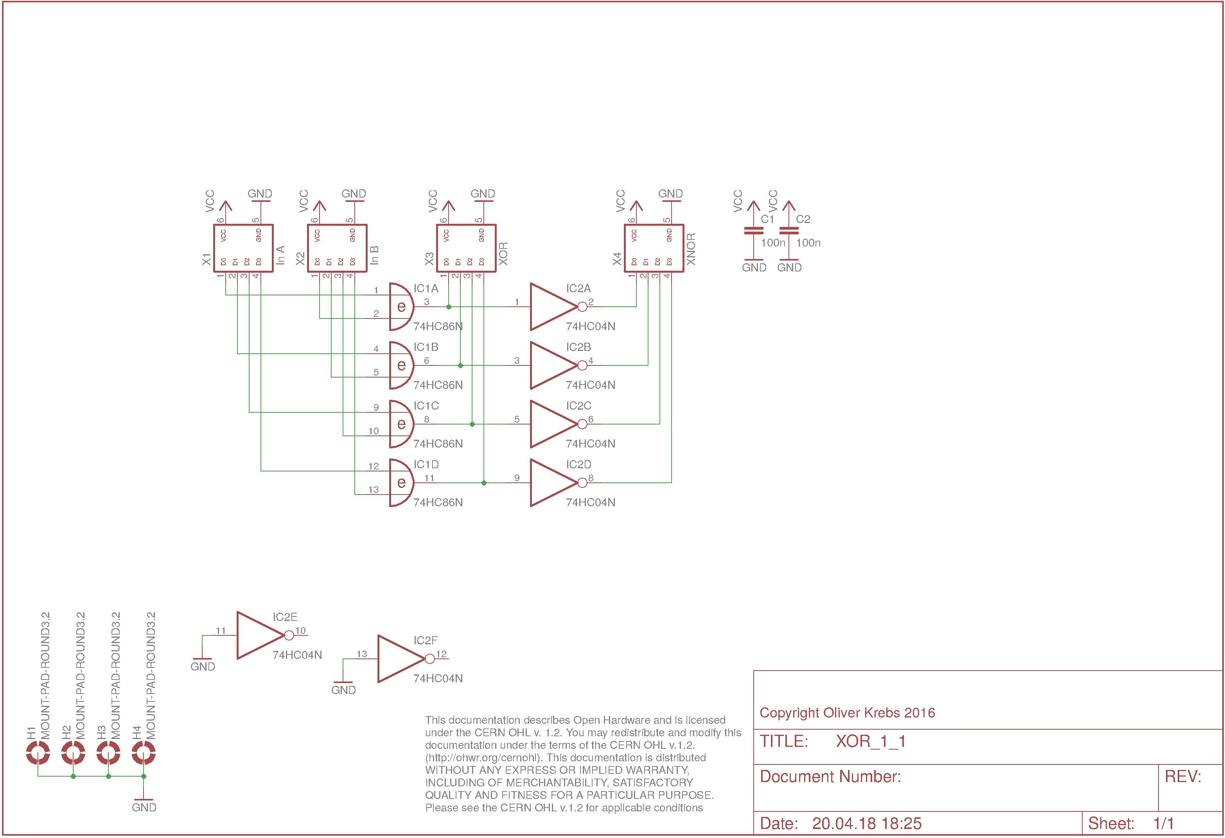
doc/XOR_1_1_sch.png
