mexdulon/tetra-Boards/eagle/MIC_1_0.brd

## EAGLE design eagle/MIC_1_0.brd (2018-08-21)

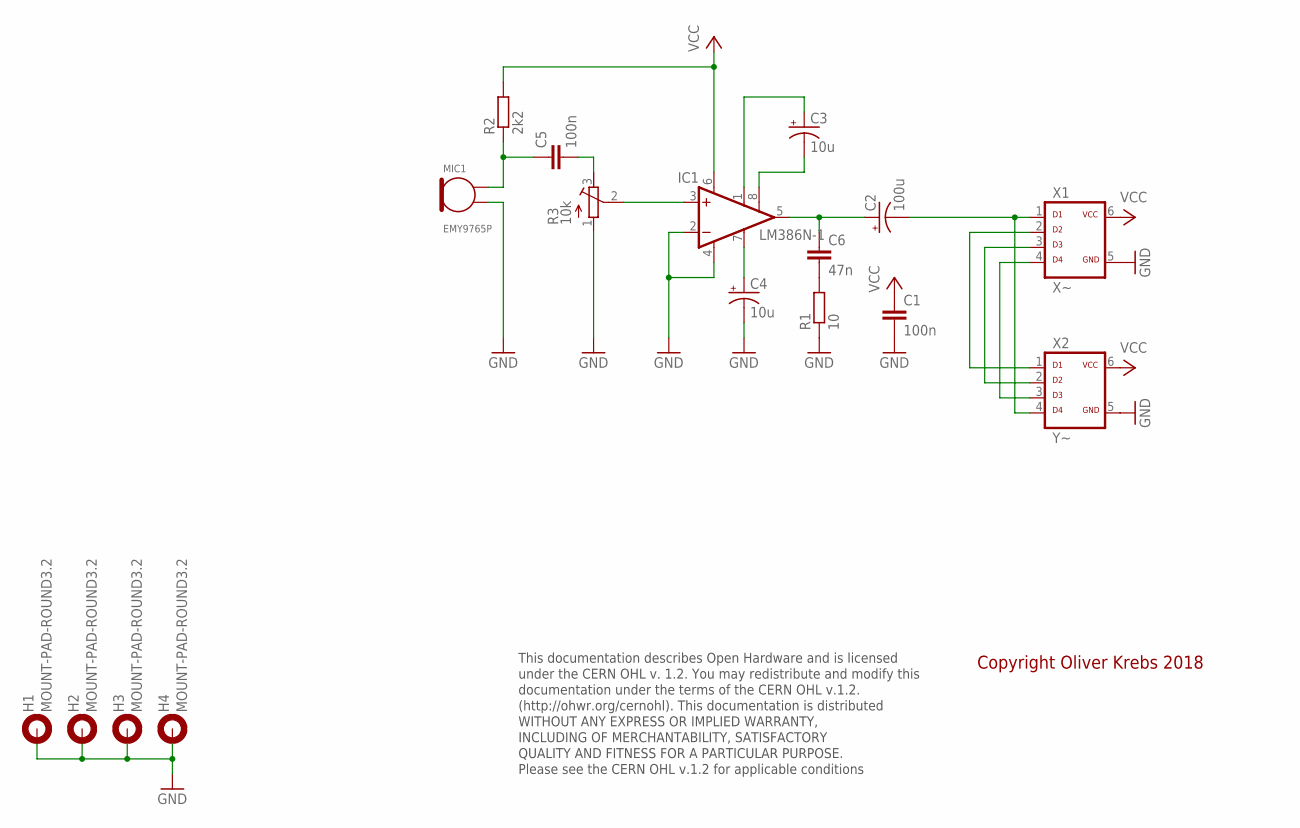
[picture p221: schematic MIC_1_0.sch]

Parts:
C1, C5: 100n; C050-025X075
C2: 100u; CPOL-RADIAL-100UF-25V
C3, C4: 10u; CPOL-RADIAL-10UF-25V
C6: 47n; C050-025X075
H1, H2, H3, H4: MOUNT-PAD-ROUND3.2; 3,2-PAD
IC1: LM386N-1; DIL08
MIC1: EMY9765P
R1: 10; 0207/10
R2: 2k2; 0207/10
R3: 10k; ACP-6L
X1: X~; ML-6
X2: Y~; ML-6

Connections:
GND: C1.2, C4.2 (-), H1.B3,2, H2.B3,2, H3.B3,2, H4.B3,2, IC1.2 (-IN), IC1.4 (GND), MIC1.P$2, R1.1, R3.1 (A), X1.5, X2.5
unnamed: C3.2 (-), IC1.8 (GAIN)
unnamed: C3.1 (+), IC1.1 (GAIN)
unnamed: C5.2, R3.3 (E)
unnamed: X1.4, X2.3
unnamed: C5.1, MIC1.P$1, R2.1
unnamed: IC1.3 (+IN), R3.2 (S)
unnamed: X1.3, X2.2
unnamed: C4.1 (+), IC1.7 (BYPASS)
unnamed: C2.1 (+), C6.1, IC1.5 (OUT)
unnamed: C6.2, R1.2
unnamed: C2.2 (-), X1.1, X2.4
unnamed: X1.2, X2.1
VCC: C1.1, IC1.6 (VS), R2.2, X1.6, X2.6

Notes on the sheet:
This documentation describes Open Hardware and is licensed under the CERN OHL v. 1.2. You may redistribute and modify this documentation under the terms of the CERN OHL v.1.2. (http://ohwr.org/cernohl). This documentation is distributed WITHOUT ANY EXPRESS OR IMPLIED WARRANTY, INCLUDING OF MERCHANT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
Copyright Oliver Krebs 2018

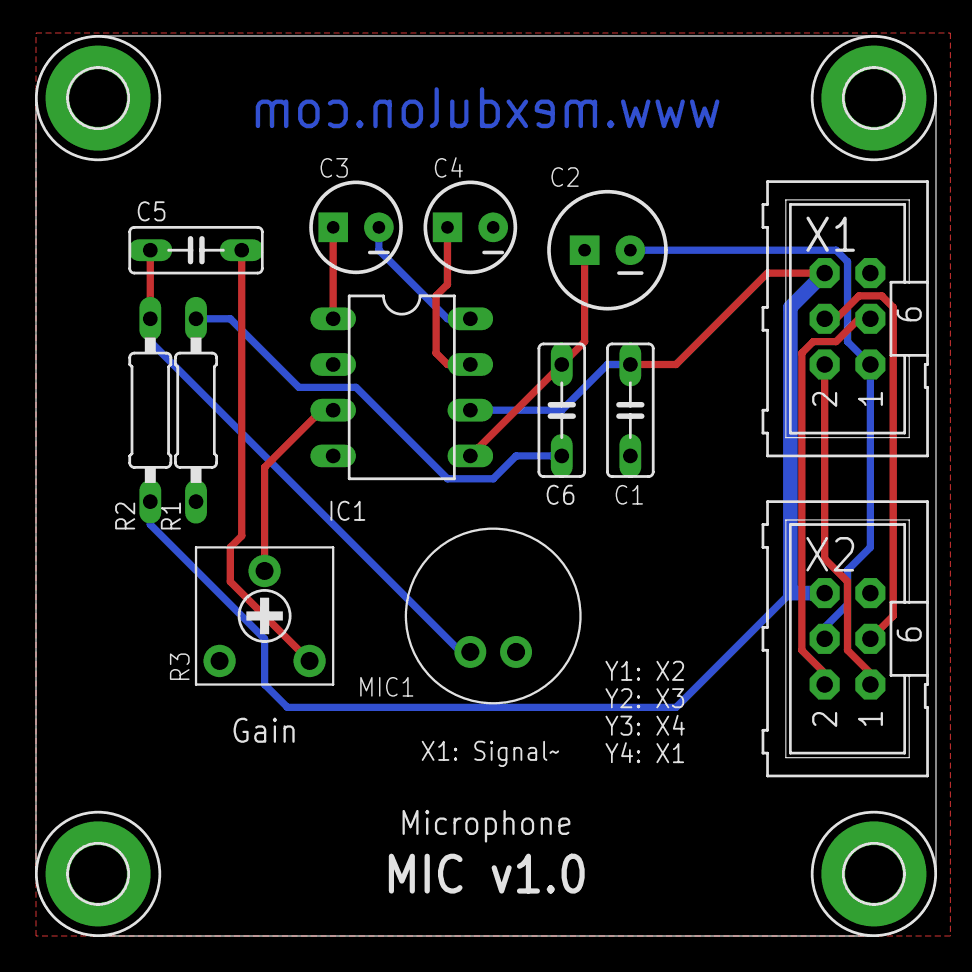
[picture p222: board MIC_1_0.brd from above]

Board: 2 copper layers, 50.0 x 50.0 mm, 17 parts (0 on the bottom side), 14 nets.
