mexdulon/tetra-Boards/eagle/D18_1_1.brd

## EAGLE design eagle/D18_1_1.brd (2018-08-21)

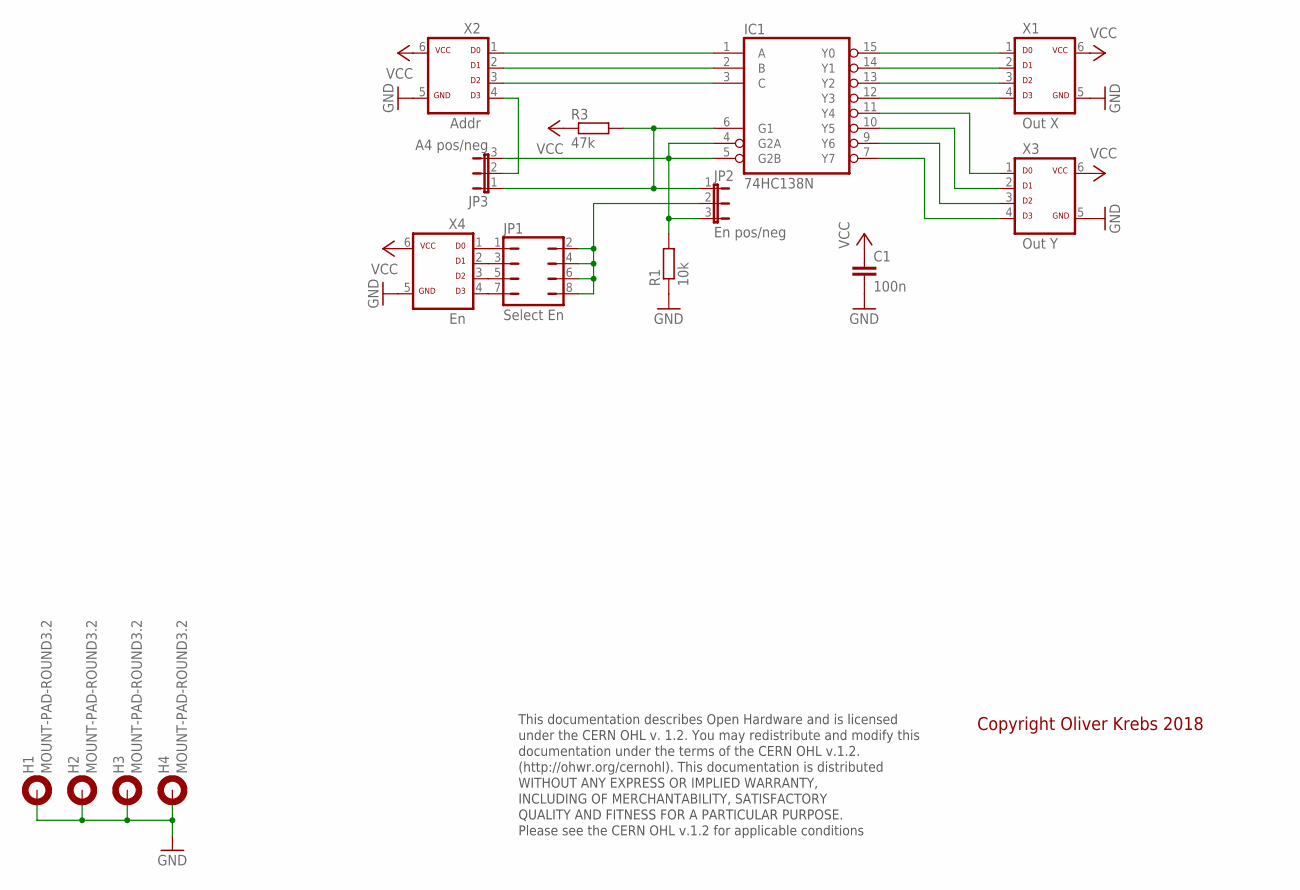
[picture p223: schematic D18_1_1.sch]

Parts:
C1: 100n; C050-025X075
H1, H2, H3, H4: MOUNT-PAD-ROUND3.2; 3,2-PAD
IC1: 74HC138N; DIL16
JP1: Select En; JP4Q
JP2: En pos/neg; JP2-U
JP3: A4 pos/neg; JP2-U
R1: 10k; 0207/10
R3: 47k; 0207/10
X1: Out X; ML-6
X2: Addr; ML-6
X3: Out Y; ML-6
X4: En; ML-6

Connections:
GND: C1.2, H1.B3,2, H2.B3,2, H3.B3,2, H4.B3,2, IC1.8 (GND), R1.1, X1.5, X2.5, X3.5, X4.5
unnamed: IC1.1 (A), X2.1
unnamed: IC1.2 (B), X2.2
unnamed: IC1.3 (C), X2.3
unnamed: JP3.2, X2.4
unnamed: JP1.2, JP1.4, JP1.6, JP1.8, JP2.2
unnamed: JP1.1, X4.1
unnamed: JP1.3, X4.2
unnamed: JP1.5, X4.3
unnamed: JP1.7, X4.4
unnamed: IC1.15 (Y0), X1.1
unnamed: IC1.14 (Y1), X1.2
unnamed: IC1.13 (Y2), X1.3
unnamed: IC1.12 (Y3), X1.4
unnamed: IC1.11 (Y4), X3.1
unnamed: IC1.10 (Y5), X3.2
unnamed: IC1.9 (Y6), X3.3
unnamed: IC1.7 (Y7), X3.4
unnamed: IC1.4 (G2A), IC1.5 (G2B), JP2.3, JP3.3, R1.2
unnamed: IC1.6 (G1), JP2.1, JP3.1, R3.2
VCC: C1.1, IC1.16 (VCC), R3.1, X1.6, X2.6, X3.6, X4.6

Notes on the sheet:
This documentation describes Open Hardware and is licensed under the CERN OHL v. 1.2. You may redistribute and modify this documentation under the terms of the CERN OHL v.1.2. (http://ohwr.org/cernohl). This documentation is distributed WITHOUT ANY EXPRESS OR IMPLIED WARRANTY, INCLUDING OF MERCHANT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
Copyright Oliver Krebs 2018

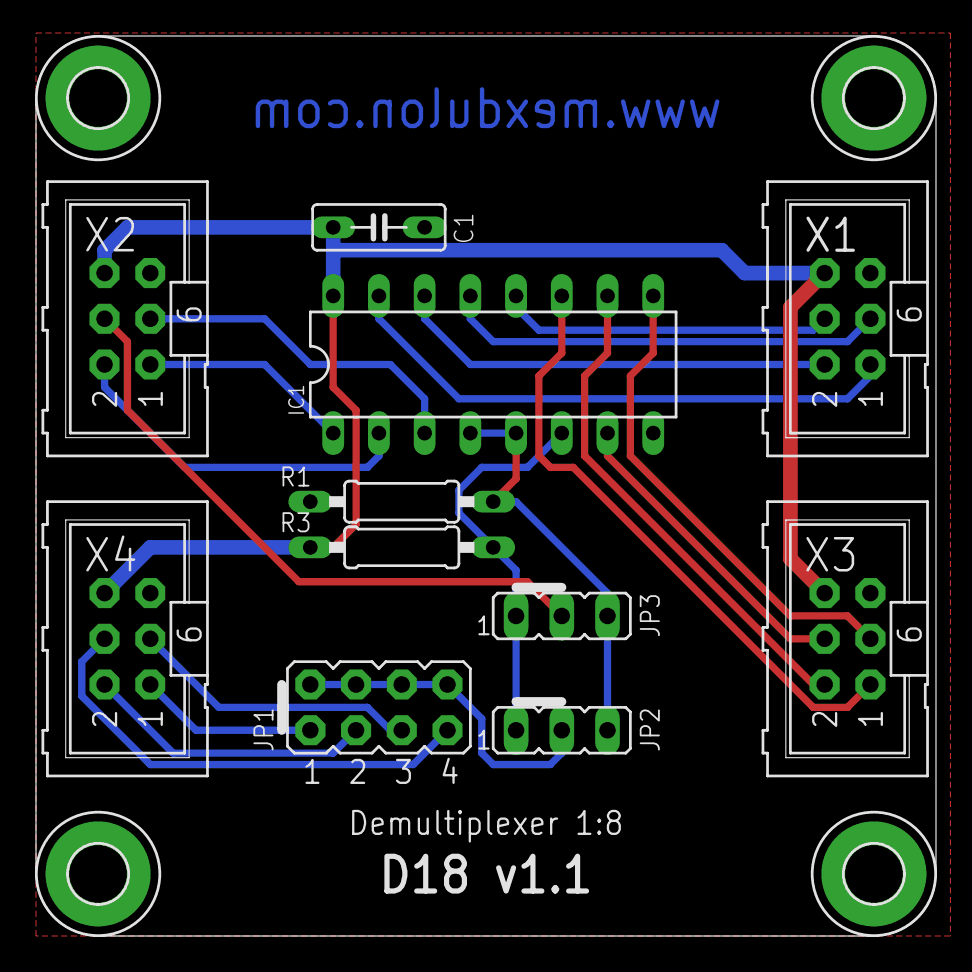
[picture p224: board D18_1_1.brd from above]

Board: 2 copper layers, 50.0 x 50.0 mm, 15 parts (0 on the bottom side), 21 nets.
