mexdulon/tetra-Boards/eagle/PWA_1_0.brd

## EAGLE design eagle/PWA_1_0.brd (2018-08-21)

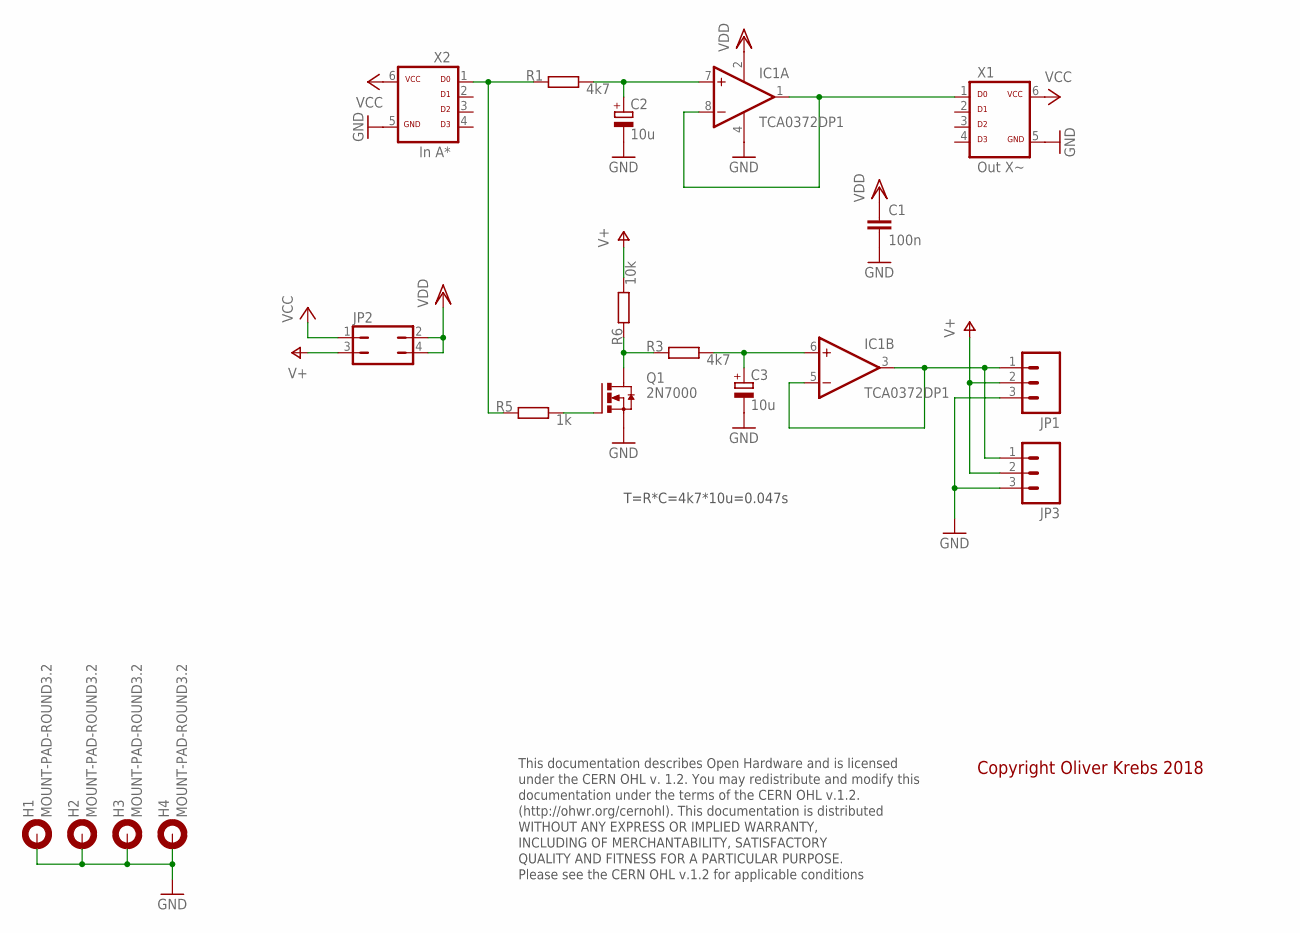
[picture p225: schematic PWA_1_0.sch]

Parts:
C1: 100n; C050-025X075
C2, C3: 10u; E2-4
H1, H2, H3, H4: MOUNT-PAD-ROUND3.2; 3,2-PAD
IC1: TCA0372DP1; DIL08
JP1: M03PTH; 1X03
JP2: JP2Q
JP3: M03BIG_5.08; 1X03_BIG_5.08
Q1: 2N7000; TO92-LINE
R1, R3: 4k7; 0207/10
R5: 1k; 0207/10
R6: 10k; 0207/10
X1: Out X~; ML-6
X2: In A*; ML-6

Connections:
GND: C1.2, C2.-, C3.-, H1.B3,2, H2.B3,2, H3.B3,2, H4.B3,2, IC1.4 (GND), JP1.3, JP3.3, Q1.3 (S), X1.5, X2.5
unnamed: C2.+, IC1.7 (+IN), R1.2
unnamed: IC1.1 (OUT), IC1.8 (-IN), X1.1
unnamed: R1.1, R5.1, X2.1
unnamed: IC1.3 (OUT), IC1.5 (-IN), JP1.1, JP3.1
unnamed: C3.+, IC1.6 (+IN), R3.2
unnamed: Q1.1 (D), R3.1, R6.1
unnamed: Q1.2 (G), R5.2
V+: JP1.2, JP2.3, JP3.2, R6.2
VCC: JP2.1, X1.6, X2.6
VDD: C1.1, IC1.2 (VDD), JP2.2, JP2.4

Notes on the sheet:
This documentation describes Open Hardware and is licensed under the CERN OHL v. 1.2. You may redistribute and modify this documentation under the terms of the CERN OHL v.1.2. (http://ohwr.org/cernohl). This documentation is distributed WITHOUT ANY EXPRESS OR IMPLIED WARRANTY, INCLUDING OF MERCHANT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
Copyright Oliver Krebs 2018
T=R*C=4k7*10u=0.047s

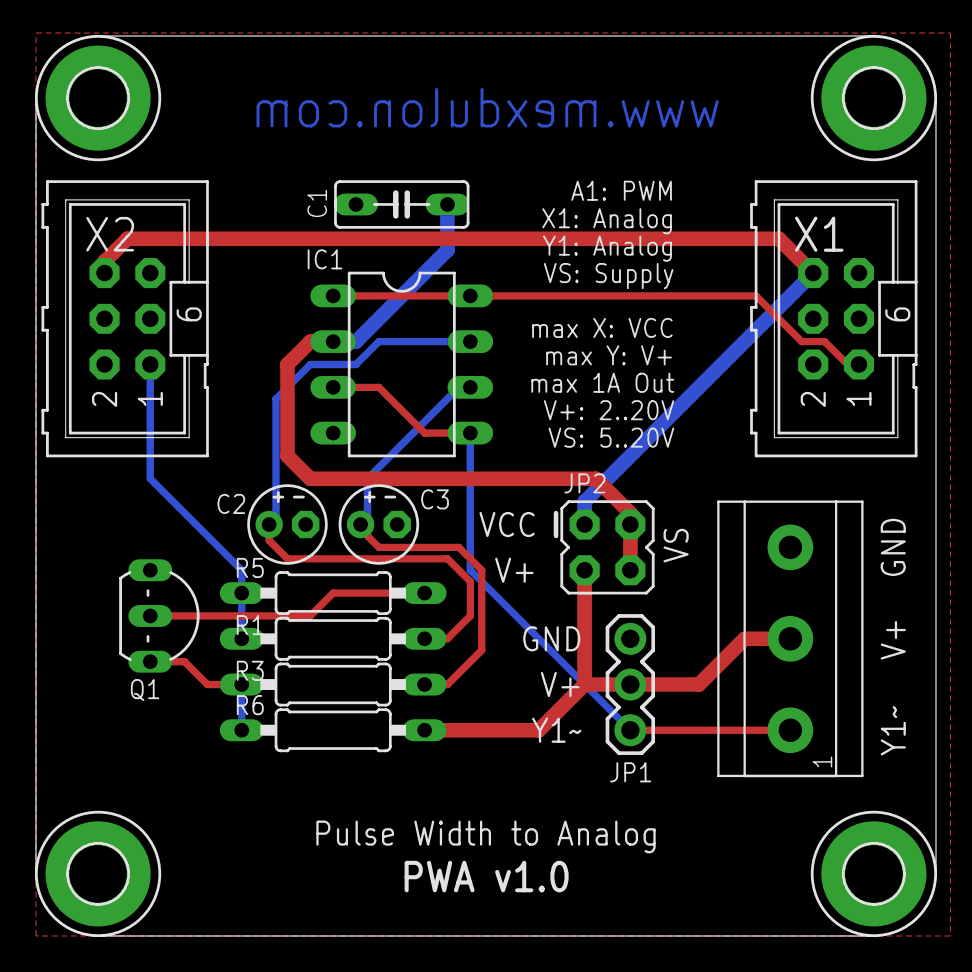
[picture p226: board PWA_1_0.brd from above]

Board: 2 copper layers, 50.0 x 50.0 mm, 18 parts (0 on the bottom side), 11 nets.
