mexdulon/tetra-Boards/eagle/AVC_1_0.brd

## EAGLE design eagle/AVC_1_0.brd (2018-08-21)

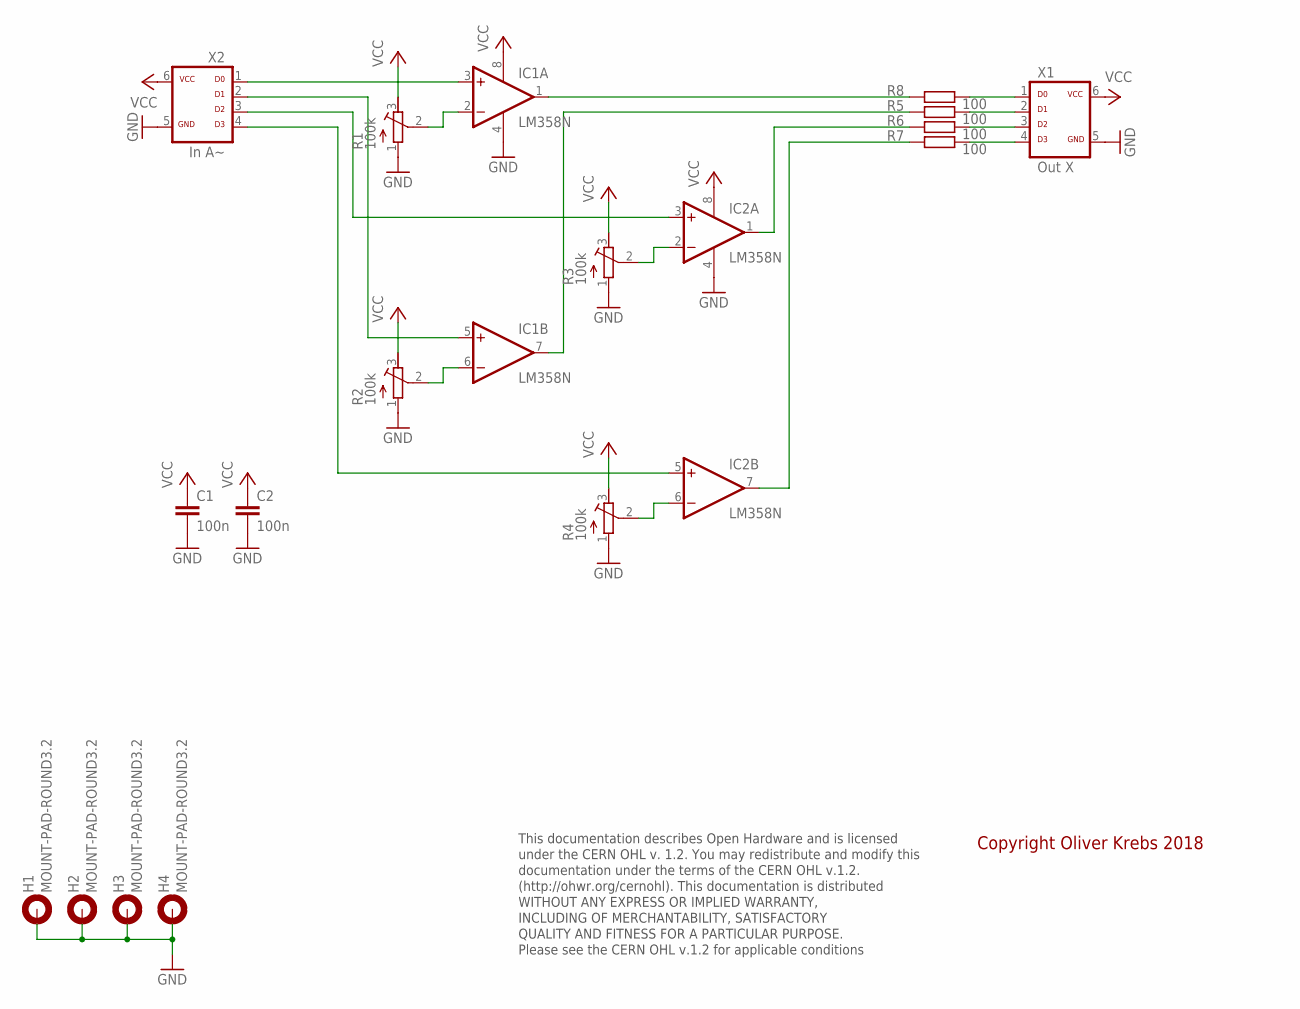
[picture p227: schematic AVC_1_0.sch]

Parts:
C1, C2: 100n; C050-025X075
H1, H2, H3, H4: MOUNT-PAD-ROUND3.2; 3,2-PAD
IC1, IC2: LM358N; DIL08
R1, R2, R3, R4: 100k; ACP-6L
R5, R6, R7, R8: 100; 0207/10
X1: Out X; ML-6
X2: In A~; ML-6

Connections:
GND: C1.2, C2.2, H1.B3,2, H2.B3,2, H3.B3,2, H4.B3,2, IC1.4 (V-), IC2.4 (V-), R1.1 (A), R2.1 (A), R3.1 (A), R4.1 (A), X1.5, X2.5
unnamed: IC1.3 (+IN), X2.1
unnamed: IC1.2 (-IN), R1.2 (S)
unnamed: IC1.5 (+IN), X2.2
unnamed: IC1.6 (-IN), R2.2 (S)
unnamed: R5.2, X1.2
unnamed: R8.2, X1.1
unnamed: R6.2, X1.3
unnamed: R7.2, X1.4
unnamed: IC1.1 (OUT), R8.1
unnamed: IC1.7 (OUT), R5.1
unnamed: IC2.3 (+IN), X2.3
unnamed: IC2.2 (-IN), R3.2 (S)
unnamed: IC2.5 (+IN), X2.4
unnamed: IC2.6 (-IN), R4.2 (S)
unnamed: IC2.1 (OUT), R6.1
unnamed: IC2.7 (OUT), R7.1
VCC: C1.1, C2.1, IC1.8 (V+), IC2.8 (V+), R1.3 (E), R2.3 (E), R3.3 (E), R4.3 (E), X1.6, X2.6

Notes on the sheet:
This documentation describes Open Hardware and is licensed under the CERN OHL v. 1.2. You may redistribute and modify this documentation under the terms of the CERN OHL v.1.2. (http://ohwr.org/cernohl). This documentation is distributed WITHOUT ANY EXPRESS OR IMPLIED WARRANTY, INCLUDING OF MERCHANT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
Copyright Oliver Krebs 2018

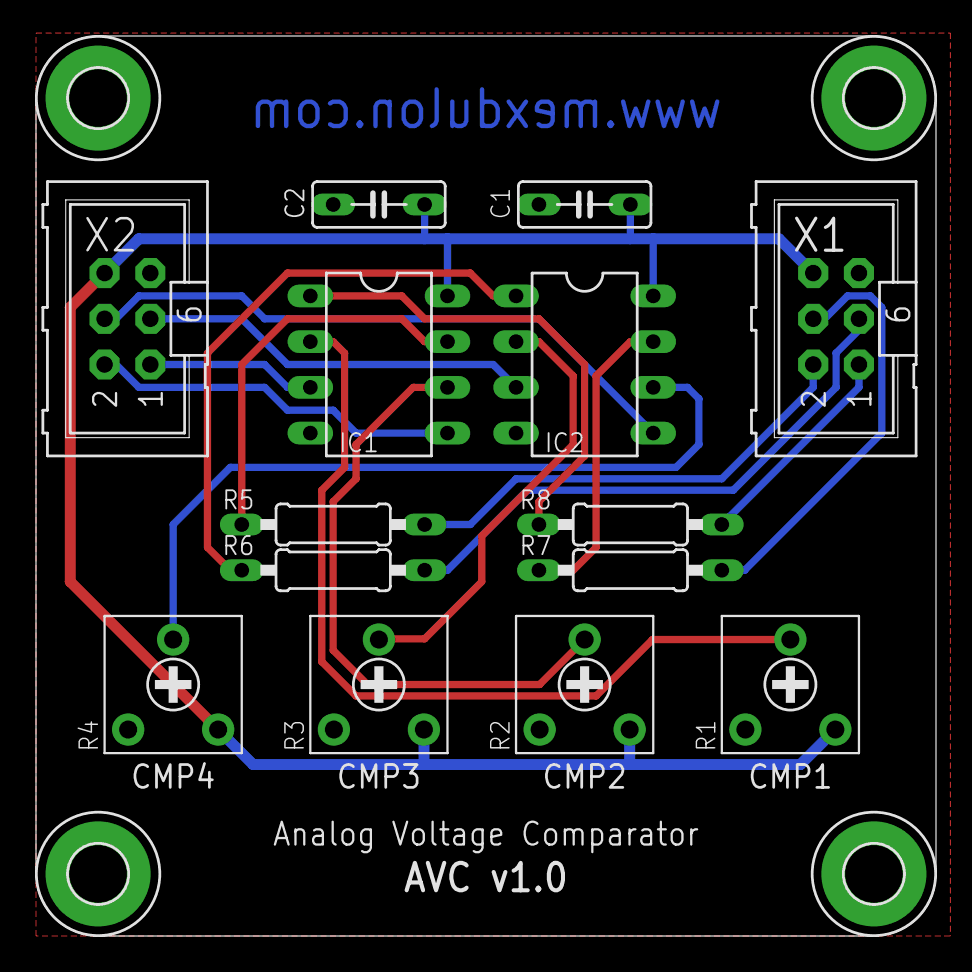
[picture p228: board AVC_1_0.brd from above]

Board: 2 copper layers, 50.0 x 50.0 mm, 18 parts (0 on the bottom side), 18 nets.
