mexdulon/tetra-Boards/eagle/PWR_1_0.brd

## EAGLE design eagle/PWR_1_0.brd (2018-08-21)

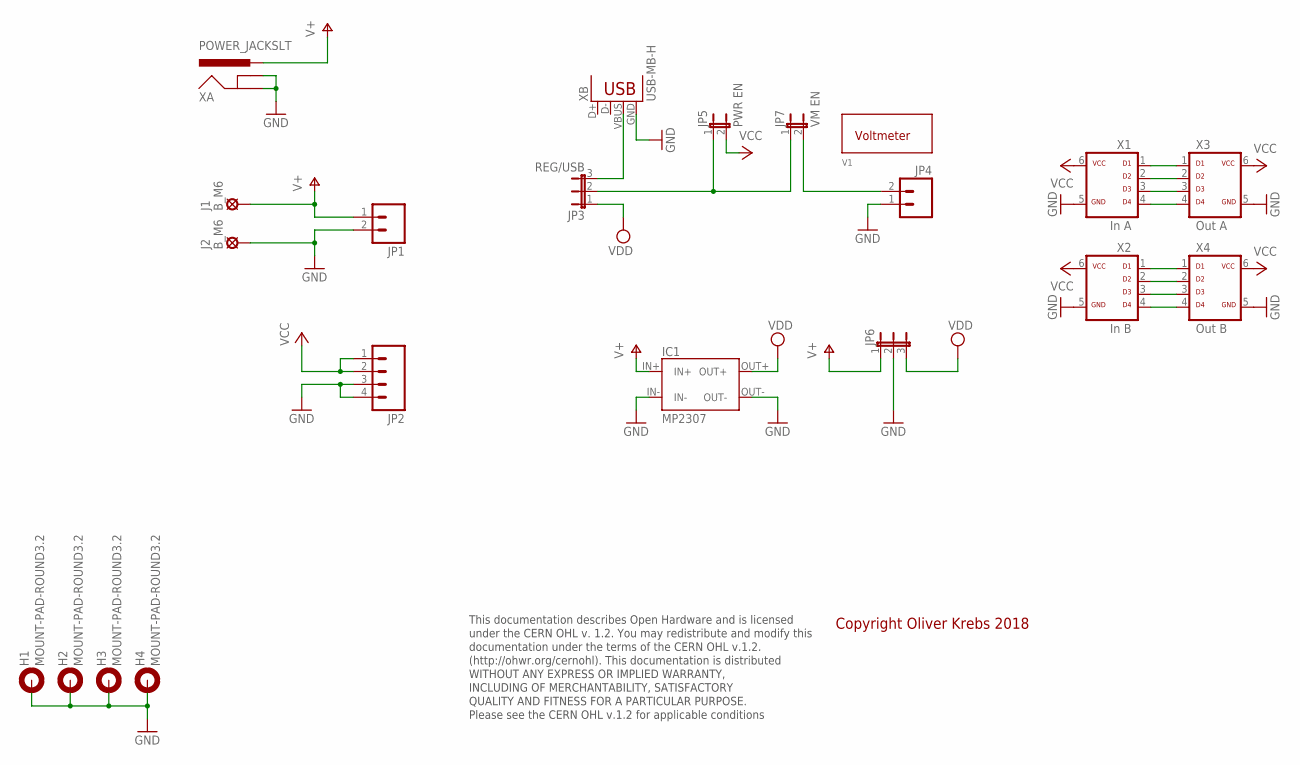
[picture p229: schematic PWR_1_0.sch]

Parts:
H1, H2, H3, H4: MOUNT-PAD-ROUND3.2; 3,2-PAD
IC1: MP2307
J1, J2: B_M6; BANANA_M6
JP1: M021.3MM-5.08; 1X02_BIG_5.08
JP2: M04PTH; 1X04
JP3: REG/USB; JP2-U
JP4: M02PTH; 1X02
JP5: PWR EN; JP1
JP6: JP2EJP2-U; JP2-U
JP7: VM EN; JP1
V1: VOLTMETER-28
X1: In A; ML-6
X2: In B; ML-6
X3: Out A; ML-6
X4: Out B; ML-6
XA: POWER_JACKSLT; POWER_JACK_SLOT
XB: USB-MB-H

Connections:
GND: H1.B3,2, H2.B3,2, H3.B3,2, H4.B3,2, IC1.IN-, IC1.OUT-, J2.1, JP1.2, JP2.3, JP2.4, JP4.1, JP6.2, X1.5, X2.5, X3.5, X4.5, XA.GND@1 (GNDBREAK), XA.GND@2 (GND), XB.GND
unnamed: X1.1, X3.1
unnamed: X1.2, X3.2
unnamed: X1.3, X3.3
unnamed: X1.4, X3.4
unnamed: X2.1, X4.1
unnamed: X2.2, X4.2
unnamed: X2.3, X4.3
unnamed: X2.4, X4.4
unnamed: JP3.2, JP5.1, JP7.1
unnamed: JP3.3, XB.VBUS
unnamed: JP4.2, JP7.2
V+: IC1.IN+, J1.1, JP1.1, JP6.1, XA.PWR
VCC: JP2.1, JP2.2, JP5.2, X1.6, X2.6, X3.6, X4.6
VDD: IC1.OUT+, JP3.1, JP6.3

Notes on the sheet:
This documentation describes Open Hardware and is licensed under the CERN OHL v. 1.2. You may redistribute and modify this documentation under the terms of the CERN OHL v.1.2. (http://ohwr.org/cernohl). This documentation is distributed WITHOUT ANY EXPRESS OR IMPLIED WARRANTY, INCLUDING OF MERCHANT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
Copyright Oliver Krebs 2018
