mexdulon/tetra-Boards/eagle/PWR_1_0.brd

## EAGLE design eagle/PWR_1_0.brd (continued)

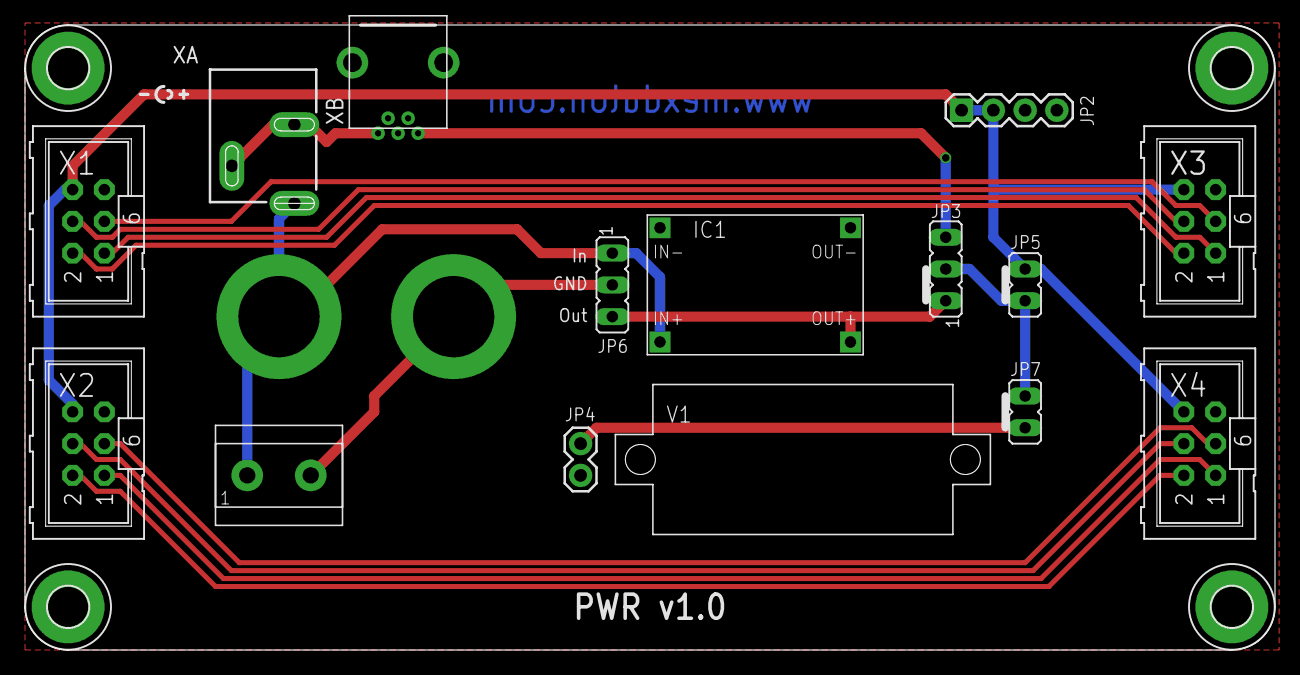
[picture p230: board PWR_1_0.brd from above]

Board: 2 copper layers, 100.0 x 50.0 mm, 21 parts (0 on the bottom side), 15 nets.
