mexdulon/tetra-Boards/eagle/PIN_1_1.brd

## EAGLE design eagle/PIN_1_1.brd (2018-08-21)

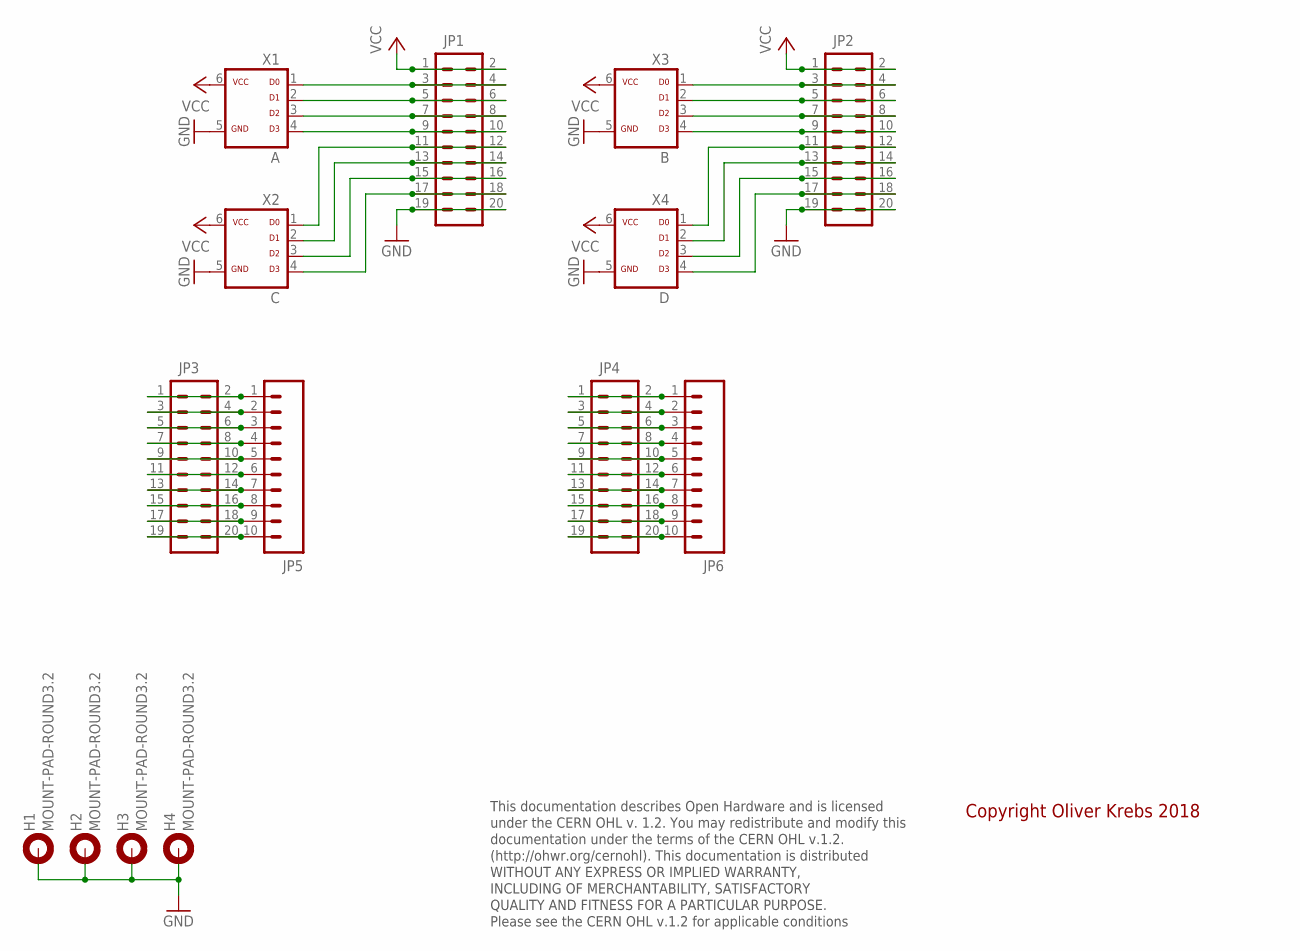
[picture p231: schematic PIN_1_1.sch]

Parts:
H1, H2, H3, H4: MOUNT-PAD-ROUND3.2; 3,2-PAD
JP1, JP2, JP3, JP4: M10X2; 2X10
JP5, JP6: M10SILK_FEMALE_PTH; 1X10
X1: A; ML-6
X2: C; ML-6
X3: B; ML-6
X4: D; ML-6

Connections:
GND: H1.B3,2, H2.B3,2, H3.B3,2, H4.B3,2, JP1.19, JP1.20, JP2.19, JP2.20, X1.5, X2.5, X3.5, X4.5
unnamed: JP2.3, JP2.4, X3.1
unnamed: JP2.5, JP2.6, X3.2
unnamed: JP2.7, JP2.8, X3.3
unnamed: JP2.9, JP2.10, X3.4
unnamed: JP2.11, JP2.12, X4.1
unnamed: JP2.13, JP2.14, X4.2
unnamed: JP2.15, JP2.16, X4.3
unnamed: JP2.17, JP2.18, X4.4
unnamed: JP1.3, JP1.4, X1.1
unnamed: JP1.5, JP1.6, X1.2
unnamed: JP1.7, JP1.8, X1.3
unnamed: JP1.9, JP1.10, X1.4
unnamed: JP1.11, JP1.12, X2.1
unnamed: JP1.13, JP1.14, X2.2
unnamed: JP1.15, JP1.16, X2.3
unnamed: JP1.17, JP1.18, X2.4
unnamed: JP3.1, JP3.2, JP5.1
unnamed: JP3.3, JP3.4, JP5.2
unnamed: JP3.5, JP3.6, JP5.3
unnamed: JP3.7, JP3.8, JP5.4
unnamed: JP4.7, JP4.8, JP6.4
unnamed: JP3.11, JP3.12, JP5.6
unnamed: JP3.13, JP3.14, JP5.7
unnamed: JP3.15, JP3.16, JP5.8
unnamed: JP3.17, JP3.18, JP5.9
unnamed: JP3.19, JP3.20, JP5.10
unnamed: JP4.1, JP4.2, JP6.1
unnamed: JP4.3, JP4.4, JP6.2
unnamed: JP4.5, JP4.6, JP6.3
unnamed: JP4.9, JP4.10, JP6.5
unnamed: JP3.9, JP3.10, JP5.5
unnamed: JP4.11, JP4.12, JP6.6
unnamed: JP4.13, JP4.14, JP6.7
unnamed: JP4.15, JP4.16, JP6.8
unnamed: JP4.17, JP4.18, JP6.9
unnamed: JP4.19, JP4.20, JP6.10
VCC: JP1.1, JP1.2, JP2.1, JP2.2, X1.6, X2.6, X3.6, X4.6

Notes on the sheet:
This documentation describes Open Hardware and is licensed under the CERN OHL v. 1.2. You may redistribute and modify this documentation under the terms of the CERN OHL v.1.2. (http://ohwr.org/cernohl). This documentation is distributed WITHOUT ANY EXPRESS OR IMPLIED WARRANTY, INCLUDING OF MERCHANT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
Copyright Oliver Krebs 2018

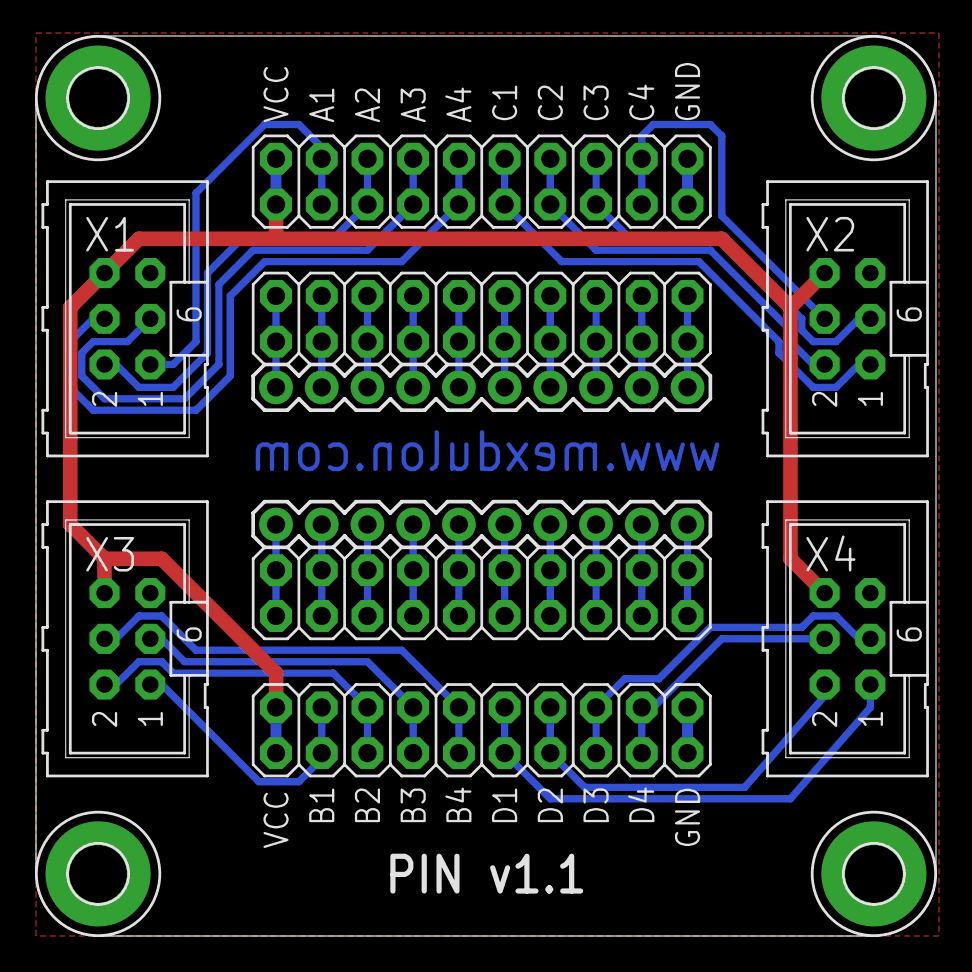
[picture p232: board PIN_1_1.brd from above]

Board: 2 copper layers, 50.0 x 50.0 mm, 14 parts (0 on the bottom side), 38 nets.
