mexdulon/tetra-Boards/eagle/POT_1_0.brd

## EAGLE design eagle/POT_1_0.brd (2018-08-21)

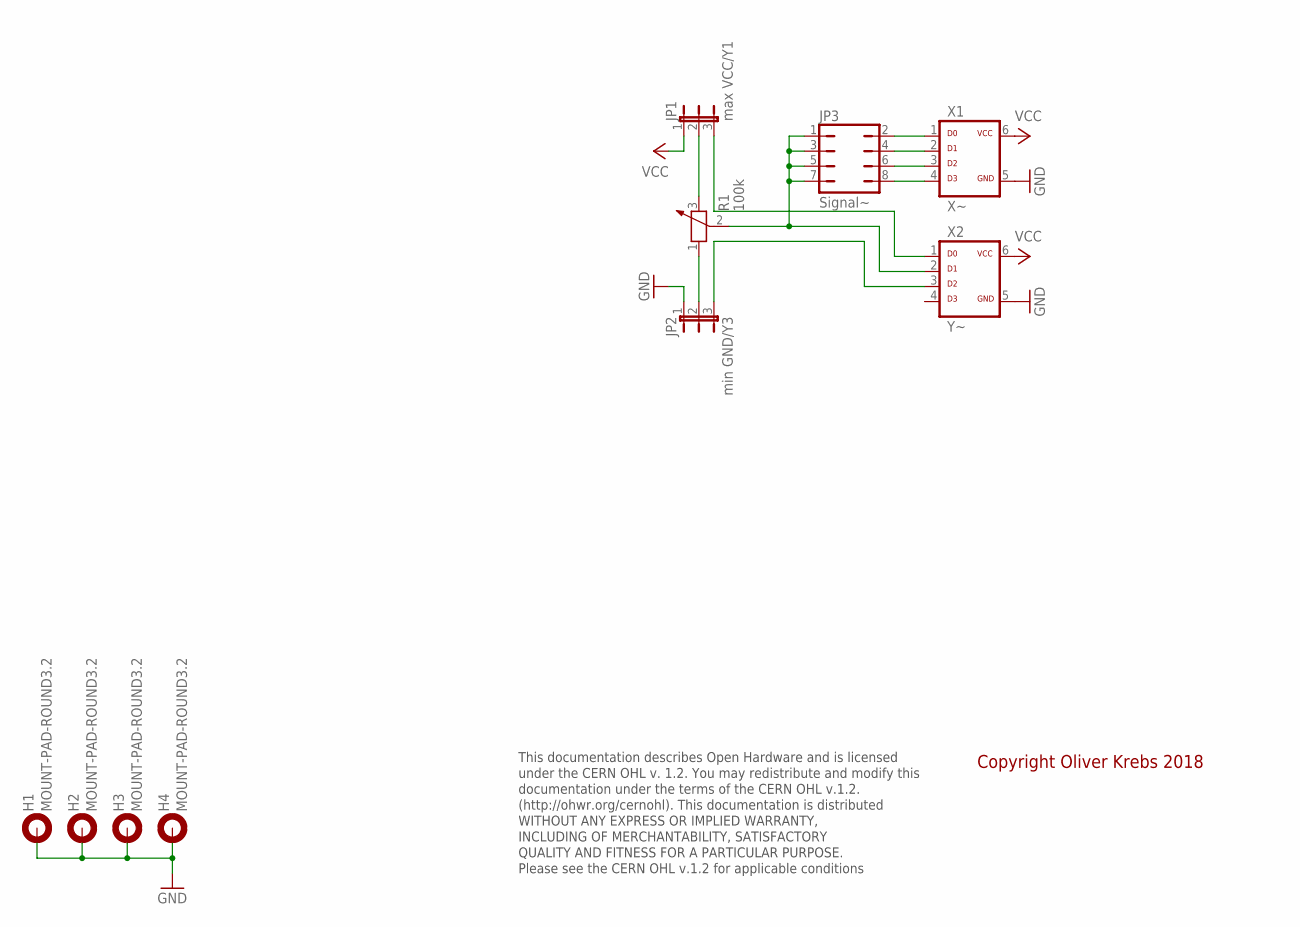
[picture p233: schematic POT_1_0.sch]

Parts:
H1, H2, H3, H4: MOUNT-PAD-ROUND3.2; 3,2-PAD
JP1: max VCC/Y1; JP2-U
JP2: min GND/Y3; JP2-U
JP3: Signal~; JP4Q
R1: 100k; RK09K113
X1: X~; ML-6
X2: Y~; ML-6

Connections:
GND: H1.B3,2, H2.B3,2, H3.B3,2, H4.B3,2, JP2.1, X1.5, X2.5
unnamed: JP3.2, X1.1
unnamed: JP1.3, X2.1
unnamed: JP2.3, X2.3
unnamed: JP3.4, X1.2
unnamed: JP1.2, R1.3 (2)
unnamed: JP2.2, R1.1
unnamed: JP3.6, X1.3
unnamed: JP3.8, X1.4
unnamed: JP3.1, JP3.3, JP3.5, JP3.7, R1.2 (3), X2.2
VCC: JP1.1, X1.6, X2.6

Notes on the sheet:
This documentation describes Open Hardware and is licensed under the CERN OHL v. 1.2. You may redistribute and modify this documentation under the terms of the CERN OHL v.1.2. (http://ohwr.org/cernohl). This documentation is distributed WITHOUT ANY EXPRESS OR IMPLIED WARRANTY, INCLUDING OF MERCHANT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
Copyright Oliver Krebs 2018

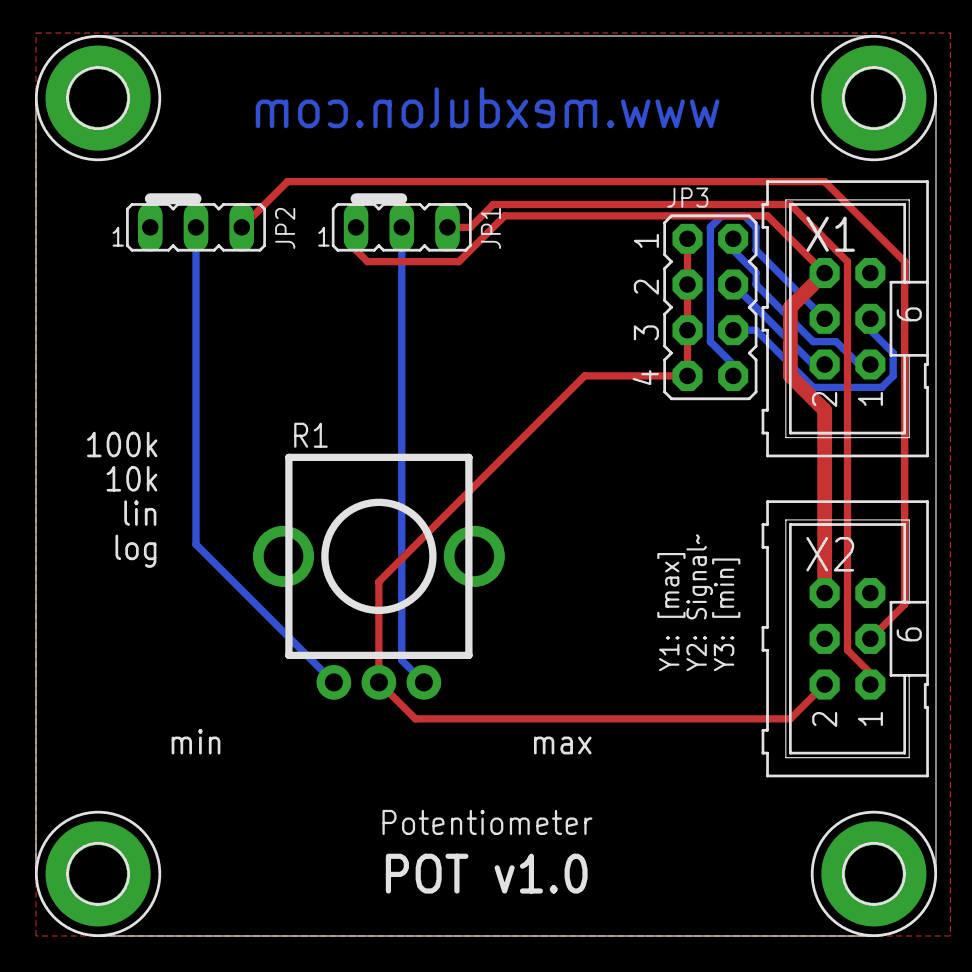
[picture p234: board POT_1_0.brd from above]

Board: 2 copper layers, 50.0 x 50.0 mm, 10 parts (0 on the bottom side), 11 nets.
