mexdulon/tetra-Boards/eagle/RGB_1_1b.brd

## EAGLE design eagle/RGB_1_1b.brd (2018-04-19)

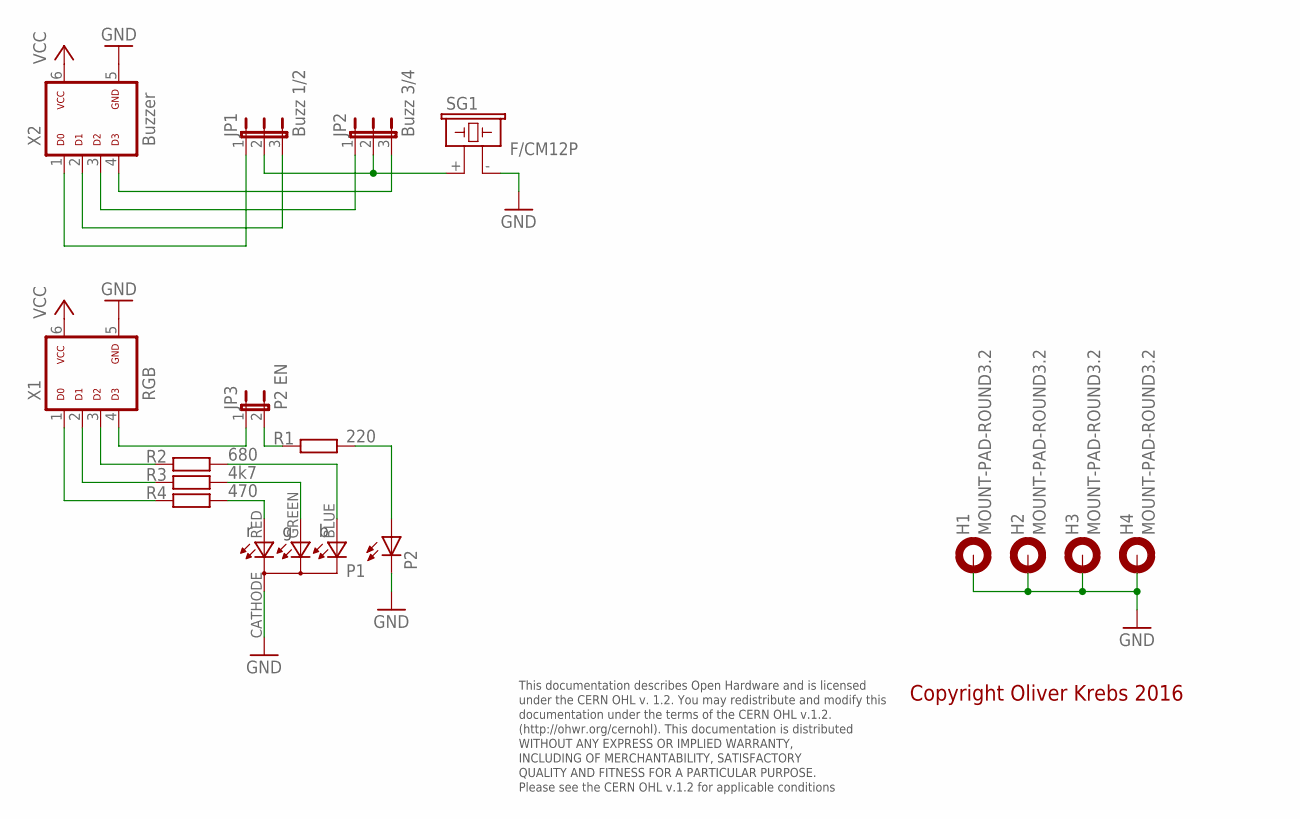
[picture p235: schematic RGB_1_1b.sch]

Parts:
H1, H2, H3, H4: MOUNT-PAD-ROUND3.2; 3,2-PAD
JP1: Buzz 1/2; JP2
JP2: Buzz 3/4; JP2
JP3: P2 EN; JP1
P1: RGB-5MM; RGB5MM
P2: LED5MM
R1: 220; 0207/10
R2: 680; 0207/10
R3: 4k7; 0207/10
R4: 470; 0207/10
SG1: F/CM12P
X1: RGB; ML-6
X2: Buzzer; ML-6

Connections:
GND: H1.B3,2, H2.B3,2, H3.B3,2, H4.B3,2, P1.CATHODE, P2.K (C), SG1.- (2), X1.5, X2.5
unnamed: JP1.2, JP2.2, SG1.+ (1)
unnamed: JP3.1, X1.4
unnamed: JP1.1, X2.1
unnamed: JP1.3, X2.2
unnamed: JP2.1, X2.3
unnamed: JP2.3, X2.4
unnamed: R2.1, X1.3
unnamed: R4.1, X1.1
unnamed: R3.1, X1.2
unnamed: P1.RED (A-RED), R4.2
unnamed: P1.GREEN (A-GREEN), R3.2
unnamed: P1.BLUE (A-BLUE), R2.2
unnamed: P2.A, R1.2
unnamed: JP3.2, R1.1
VCC: X1.6, X2.6

Notes on the sheet:
This documentation describes Open Hardware and is licensed under the CERN OHL v. 1.2. You may redistribute and modify this documentation under the terms of the CERN OHL v.1.2. (http://ohwr.org/cernohl). This documentation is distributed WITHOUT ANY EXPRESS OR IMPLIED WARRANTY, INCLUDING OF MERCHANT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
Copyright Oliver Krebs 2016

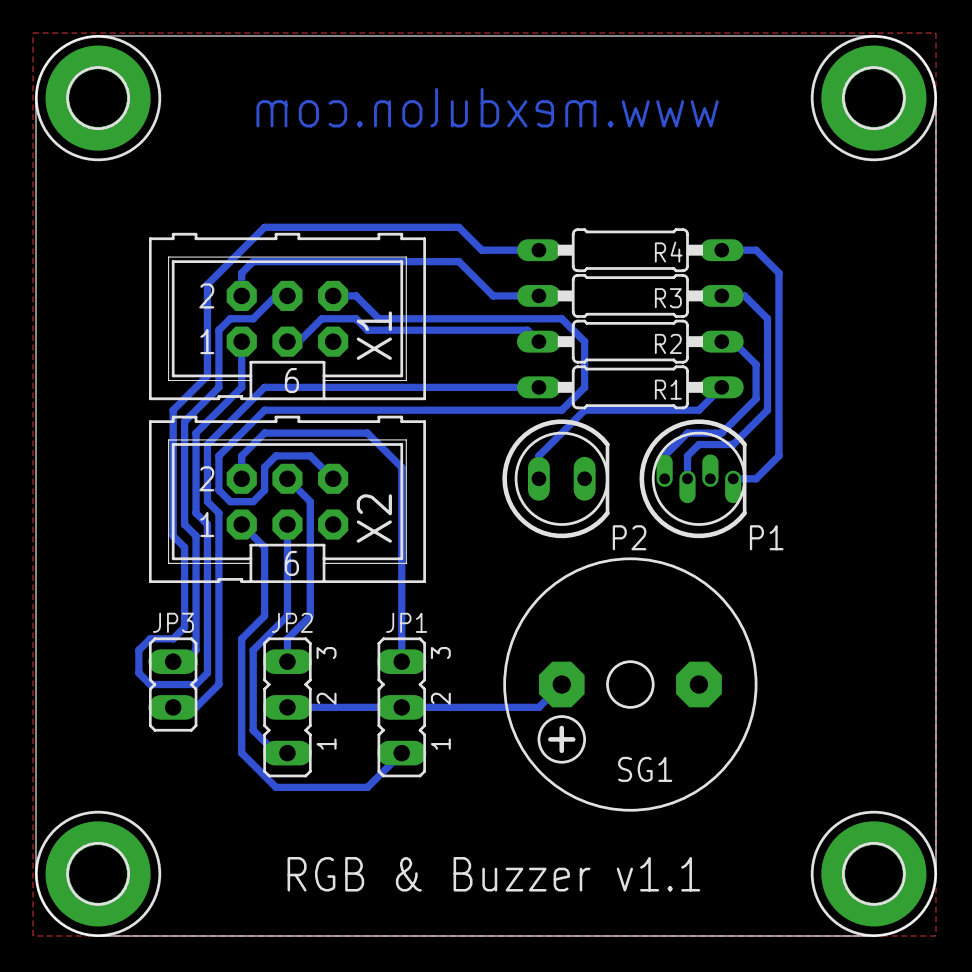
[picture p236: board RGB_1_1b.brd from above]

Board: 2 copper layers, 50.0 x 50.0 mm, 16 parts (0 on the bottom side), 16 nets.
