mexdulon/tetra-Boards/eagle/IOP_1_0.brd

## EAGLE design eagle/IOP_1_0.brd (2018-04-19)

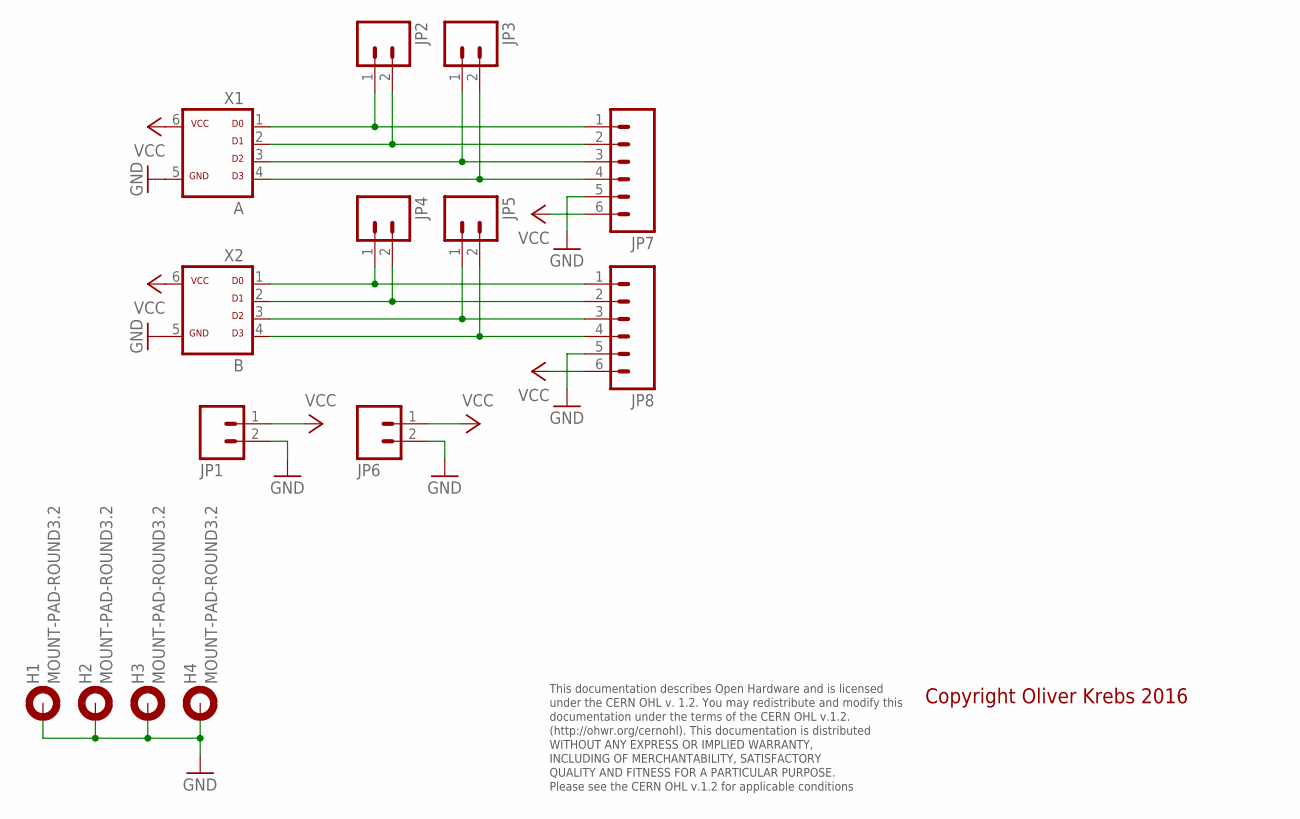
[picture p237: schematic IOP_1_0.sch]

Parts:
H1, H2, H3, H4: MOUNT-PAD-ROUND3.2; 3,2-PAD
JP1, JP2, JP3, JP4, JP5, JP6: M021.3MM-5.08; 1X02_BIG_5.08
JP7, JP8: M06SILK_FEMALE_PTH; 1X06
X1: A; ML-6
X2: B; ML-6

Connections:
GND: H1.B3,2, H2.B3,2, H3.B3,2, H4.B3,2, JP1.2, JP6.2, JP7.5, JP8.5, X1.5, X2.5
unnamed: JP2.2, JP7.2, X1.2
unnamed: JP2.1, JP7.1, X1.1
unnamed: JP3.1, JP7.3, X1.3
unnamed: JP3.2, JP7.4, X1.4
unnamed: JP4.1, JP8.1, X2.1
unnamed: JP4.2, JP8.2, X2.2
unnamed: JP5.1, JP8.3, X2.3
unnamed: JP5.2, JP8.4, X2.4
VCC: JP1.1, JP6.1, JP7.6, JP8.6, X1.6, X2.6

Notes on the sheet:
This documentation describes Open Hardware and is licensed under the CERN OHL v. 1.2. You may redistribute and modify this documentation under the terms of the CERN OHL v.1.2. (http://ohwr.org/cernohl). This documentation is distributed WITHOUT ANY EXPRESS OR IMPLIED WARRANTY, INCLUDING OF MERCHANT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
Copyright Oliver Krebs 2016

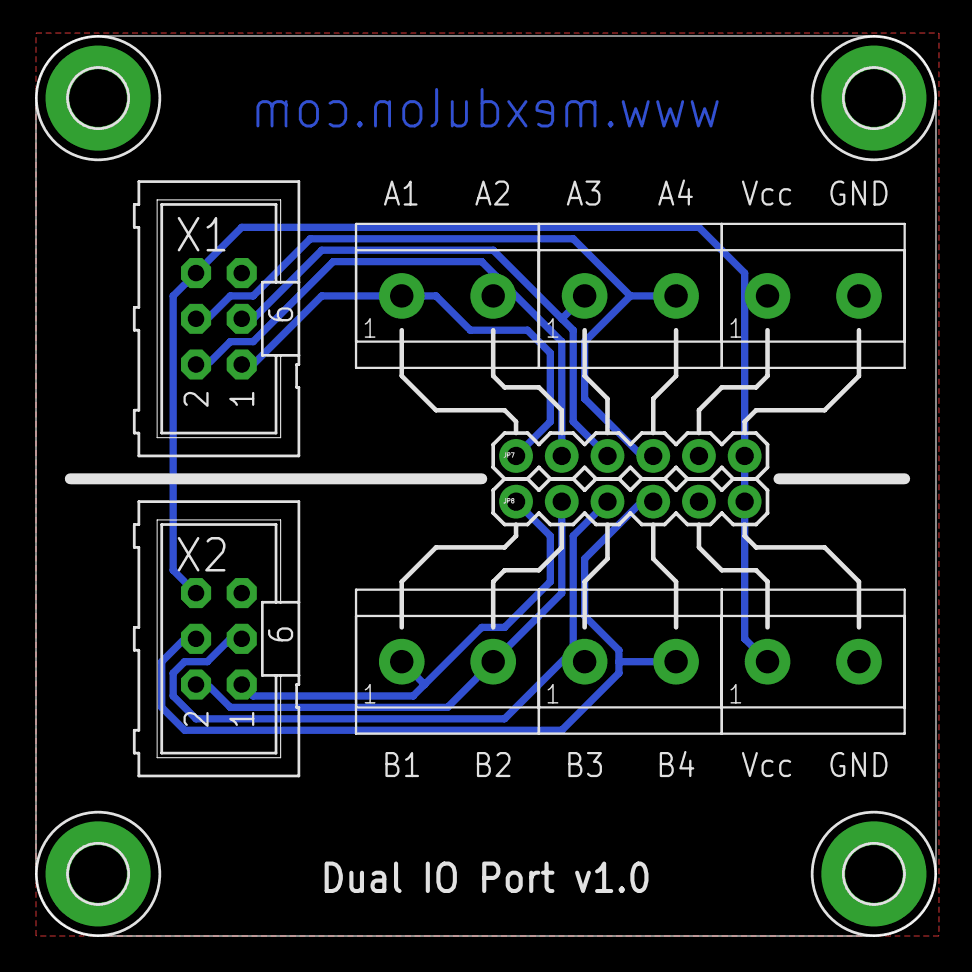
[picture p238: board IOP_1_0.brd from above]

Board: 2 copper layers, 50.0 x 50.0 mm, 14 parts (0 on the bottom side), 10 nets.
