mexdulon/tetra-Boards/eagle/TFF_1_0.brd

## EAGLE design eagle/TFF_1_0.brd (2018-04-12)

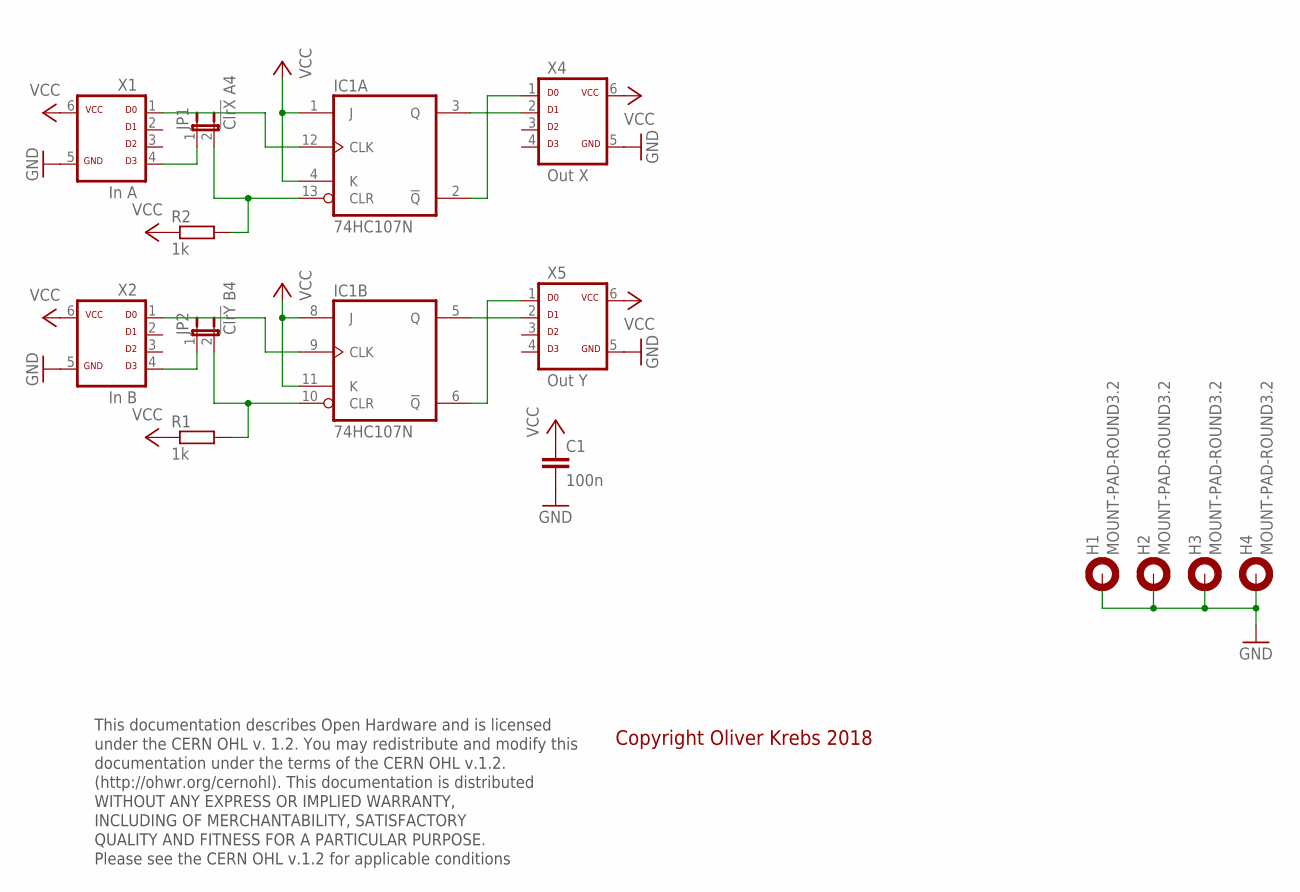
[picture p239: schematic TFF_1_0.sch]

Parts:
C1: 100n; C050-025X075
H1, H2, H3, H4: MOUNT-PAD-ROUND3.2; 3,2-PAD
IC1: 74HC107N; DIL14
JP1: !ClrX! A4; JP1
JP2: !ClrY! B4; JP1
R1, R2: 1k; 0207/10
X1: In A; ML-6
X2: In B; ML-6
X4: Out X; ML-6
X5: Out Y; ML-6

Connections:
GND: C1.2, H1.B3,2, H2.B3,2, H3.B3,2, H4.B3,2, IC1.7 (GND), X1.5, X2.5, X4.5, X5.5
unnamed: IC1.13 (CLR), JP1.2, R2.2
unnamed: JP1.1, X1.4
unnamed: JP2.1, X2.4
unnamed: IC1.10 (CLR), JP2.2, R1.2
unnamed: IC1.9 (CLK), X2.1
unnamed: IC1.12 (CLK), X1.1
unnamed: IC1.2 (!Q), X4.1
unnamed: IC1.3 (Q), X4.2
unnamed: IC1.6 (!Q), X5.1
unnamed: IC1.5 (Q), X5.2
VCC: C1.1, IC1.1 (J), IC1.4 (K), IC1.8 (J), IC1.11 (K), IC1.14 (VCC), R1.1, R2.1, X1.6, X2.6, X4.6, X5.6

Notes on the sheet:
This documentation describes Open Hardware and is licensed under the CERN OHL v. 1.2. You may redistribute and modify this documentation under the terms of the CERN OHL v.1.2. (http://ohwr.org/cernohl). This documentation is distributed WITHOUT ANY EXPRESS OR IMPLIED WARRANTY, INCLUDING OF MERCHANT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
Copyright Oliver Krebs 2018

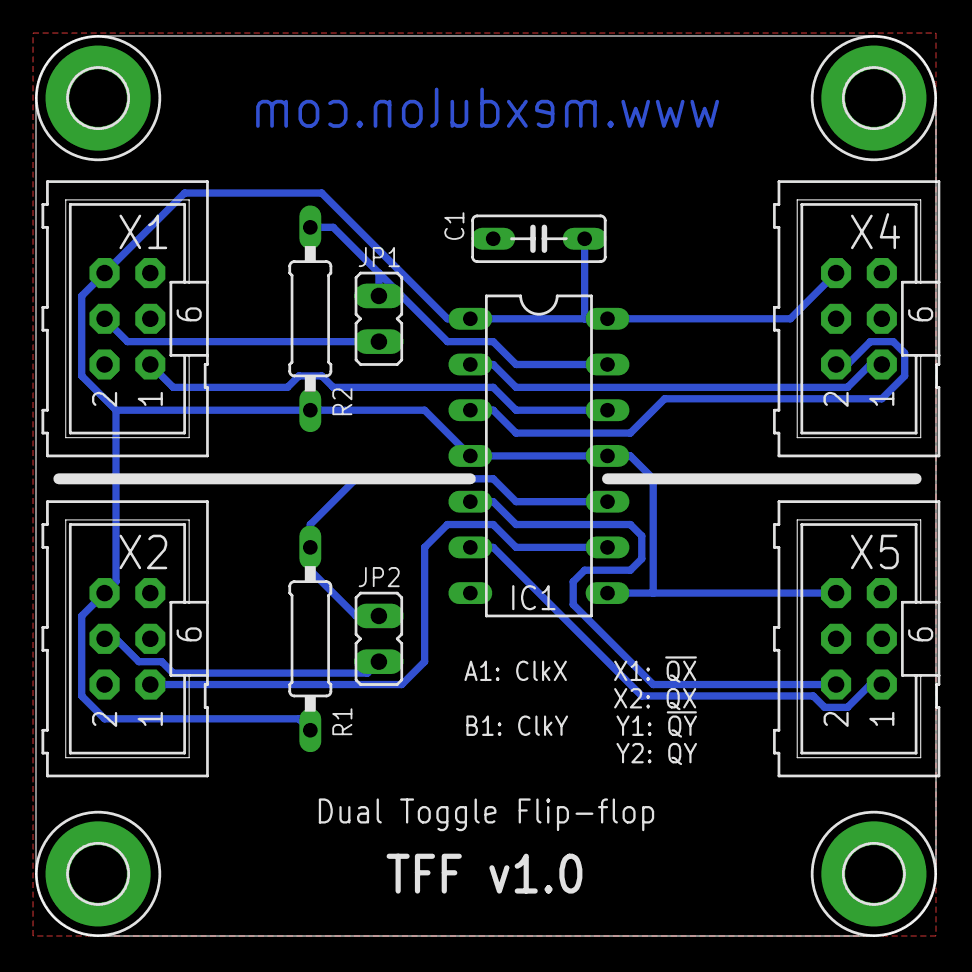
[picture p240: board TFF_1_0.brd from above]

Board: 2 copper layers, 50.0 x 50.0 mm, 14 parts (0 on the bottom side), 12 nets.
