mexdulon/tetra-Boards/eagle/LAD_1_1.brd

## EAGLE design eagle/LAD_1_1.brd (2018-04-12)

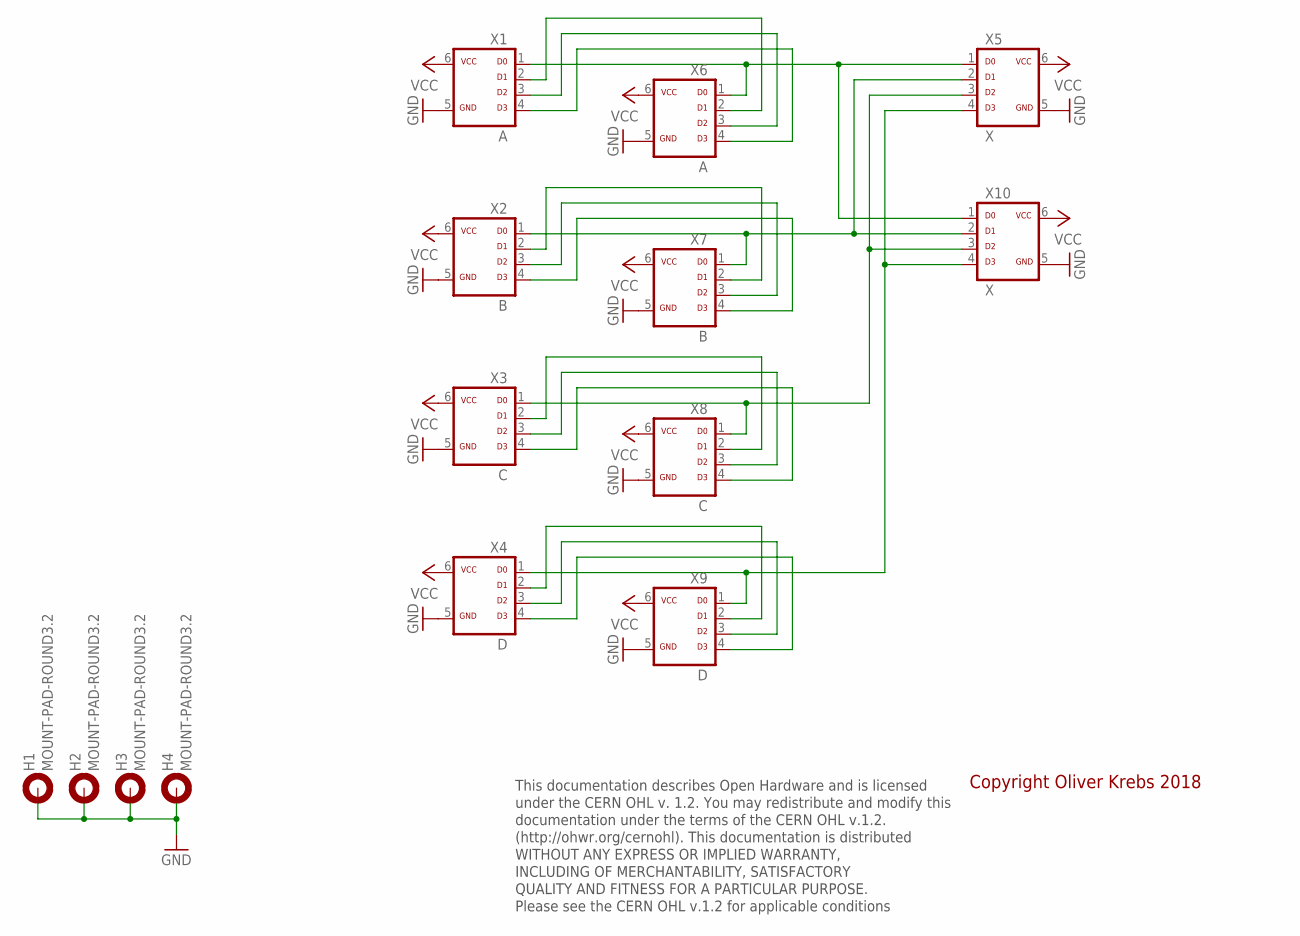
[picture p241: schematic LAD_1_1.sch]

Parts:
H1, H2, H3, H4: MOUNT-PAD-ROUND3.2; 3,2-PAD
X1, X6: A; ML-6
X2, X7: B; ML-6
X3, X8: C; ML-6
X4, X9: D; ML-6
X5, X10: X; ML-6

Connections:
GND: H1.B3,2, H2.B3,2, H3.B3,2, H4.B3,2, X1.5, X2.5, X3.5, X4.5, X5.5, X6.5, X7.5, X8.5, X9.5, X10.5
unnamed: X1.2, X6.2
unnamed: X1.3, X6.3
unnamed: X1.4, X6.4
unnamed: X4.1, X5.4, X9.1, X10.4
unnamed: X2.4, X7.4
unnamed: X3.1, X5.3, X8.1, X10.3
unnamed: X2.1, X5.2, X7.1, X10.2
unnamed: X1.1, X5.1, X6.1, X10.1
unnamed: X2.3, X7.3
unnamed: X2.2, X7.2
unnamed: X3.2, X8.2
unnamed: X3.3, X8.3
unnamed: X3.4, X8.4
unnamed: X4.2, X9.2
unnamed: X4.3, X9.3
unnamed: X4.4, X9.4
VCC: X1.6, X2.6, X3.6, X4.6, X5.6, X6.6, X7.6, X8.6, X9.6, X10.6

Notes on the sheet:
This documentation describes Open Hardware and is licensed under the CERN OHL v. 1.2. You may redistribute and modify this documentation under the terms of the CERN OHL v.1.2. (http://ohwr.org/cernohl). This documentation is distributed WITHOUT ANY EXPRESS OR IMPLIED WARRANTY, INCLUDING OF MERCHANT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
Copyright Oliver Krebs 2018

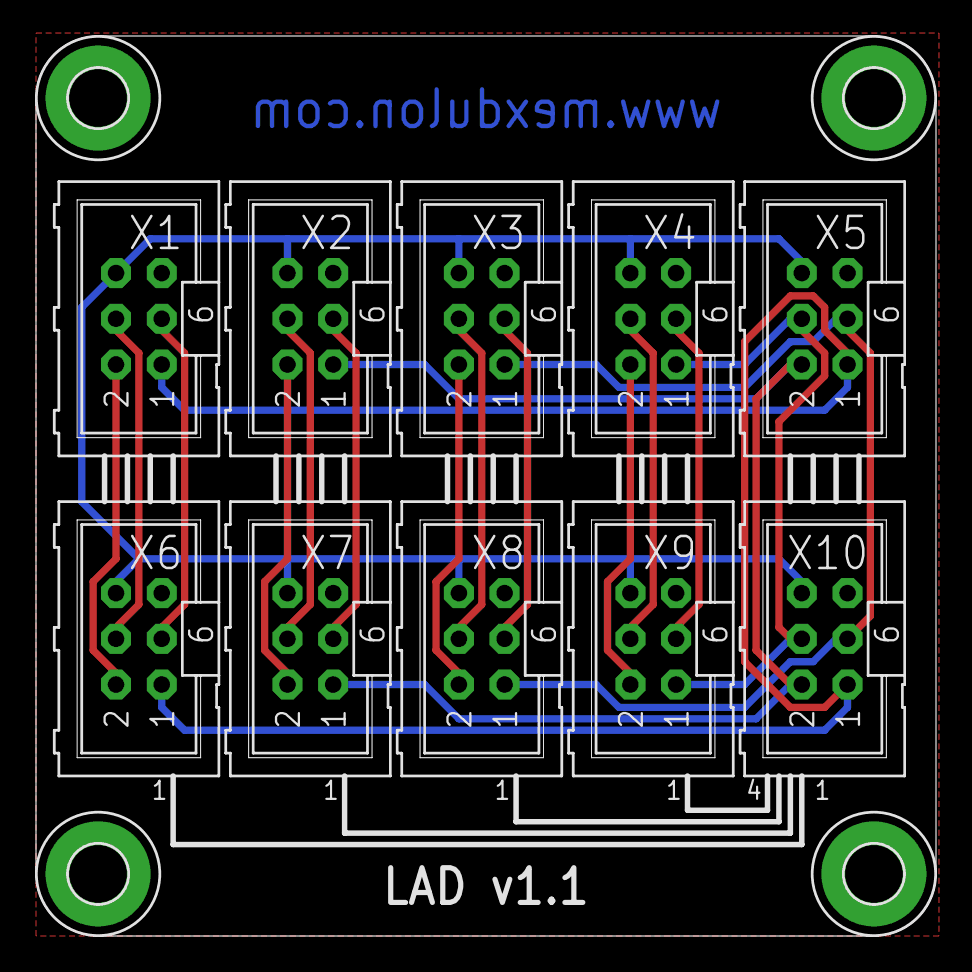
[picture p242: board LAD_1_1.brd from above]

Board: 2 copper layers, 50.0 x 50.0 mm, 14 parts (0 on the bottom side), 18 nets.
