mexdulon/tetra-Boards/eagle/NOT_1_0.brd

## EAGLE design eagle/NOT_1_0.brd (2018-04-12)

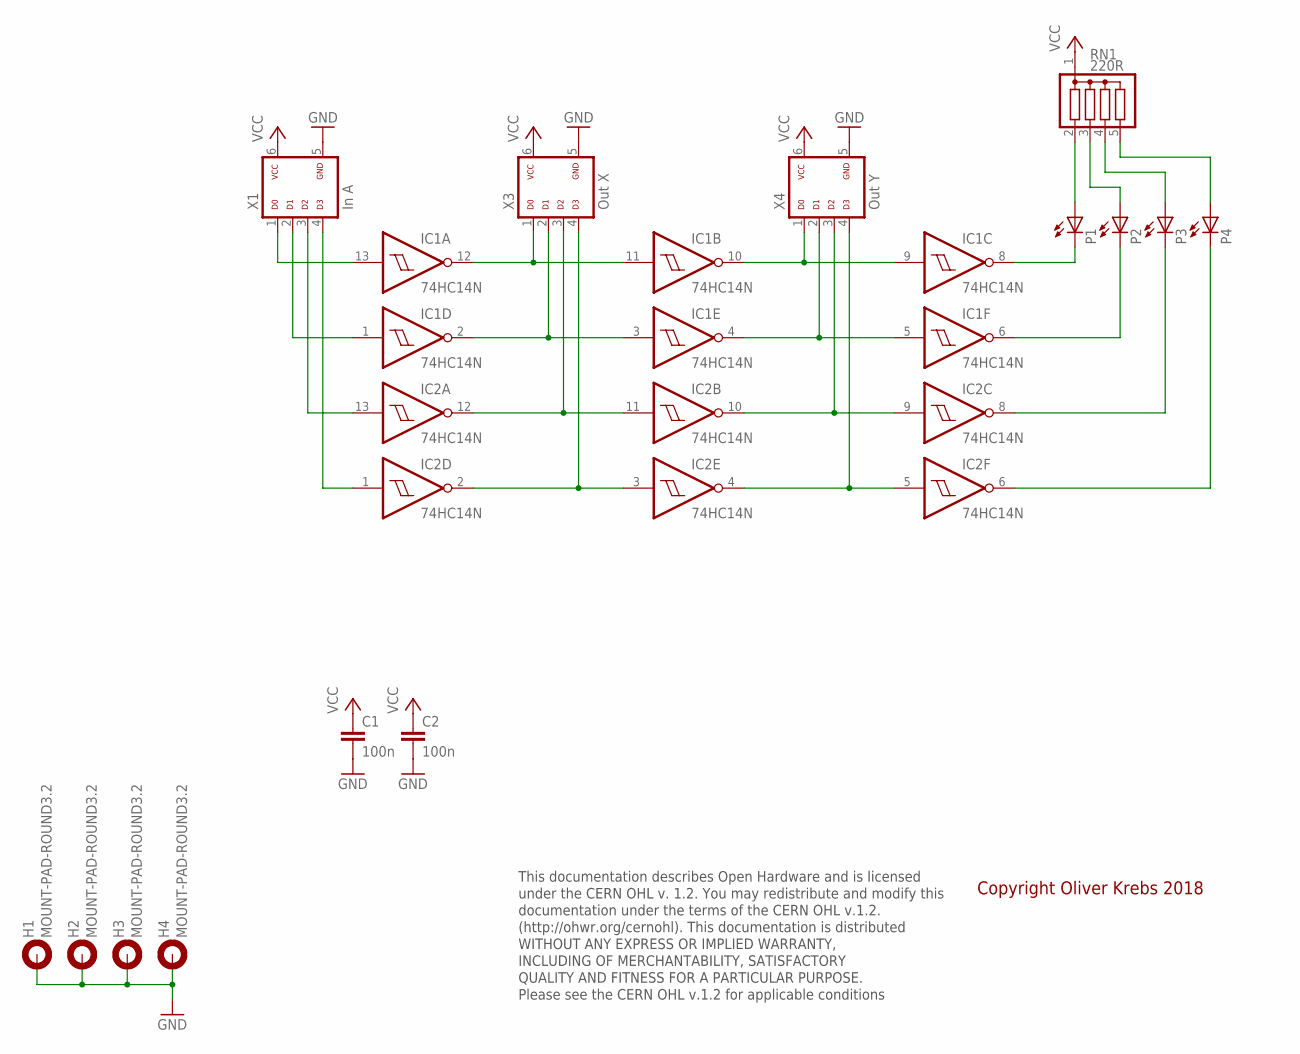
[picture p243: schematic NOT_1_0.sch]

Parts:
C1, C2: 100n; C050-025X075
H1, H2, H3, H4: MOUNT-PAD-ROUND3.2; 3,2-PAD
IC1, IC2: 74HC14N; DIL14
P1, P2, P3, P4: LED3MM
RN1: 220R; SIL5
X1: In A; ML-6
X3: Out X; ML-6
X4: Out Y; ML-6

Connections:
GND: C1.2, C2.2, H1.B3,2, H2.B3,2, H3.B3,2, H4.B3,2, IC1.7 (GND), IC2.7 (GND), X1.5, X3.5, X4.5
unnamed: IC1.8 (O), P1.K (C)
unnamed: IC1.6 (O), P2.K (C)
unnamed: IC2.8 (O), P3.K (C)
unnamed: IC2.6 (O), P4.K (C)
unnamed: IC1.9 (I), IC1.10 (O), X4.1
unnamed: IC1.4 (O), IC1.5 (I), X4.2
unnamed: IC2.9 (I), IC2.10 (O), X4.3
unnamed: IC2.4 (O), IC2.5 (I), X4.4
unnamed: IC1.13 (I), X1.1
unnamed: IC1.11 (I), IC1.12 (O), X3.1
unnamed: IC1.2 (O), IC1.3 (I), X3.2
unnamed: IC1.1 (I), X1.2
unnamed: IC2.13 (I), X1.3
unnamed: IC2.11 (I), IC2.12 (O), X3.3
unnamed: IC2.1 (I), X1.4
unnamed: IC2.2 (O), IC2.3 (I), X3.4
unnamed: P1.A, RN1.2
unnamed: P2.A, RN1.3
unnamed: P3.A, RN1.4
unnamed: P4.A, RN1.5
VCC: C1.1, C2.1, IC1.14 (VCC), IC2.14 (VCC), RN1.1, X1.6, X3.6, X4.6

Notes on the sheet:
This documentation describes Open Hardware and is licensed under the CERN OHL v. 1.2. You may redistribute and modify this documentation under the terms of the CERN OHL v.1.2. (http://ohwr.org/cernohl). This documentation is distributed WITHOUT ANY EXPRESS OR IMPLIED WARRANTY, INCLUDING OF MERCHANT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
Copyright Oliver Krebs 2018

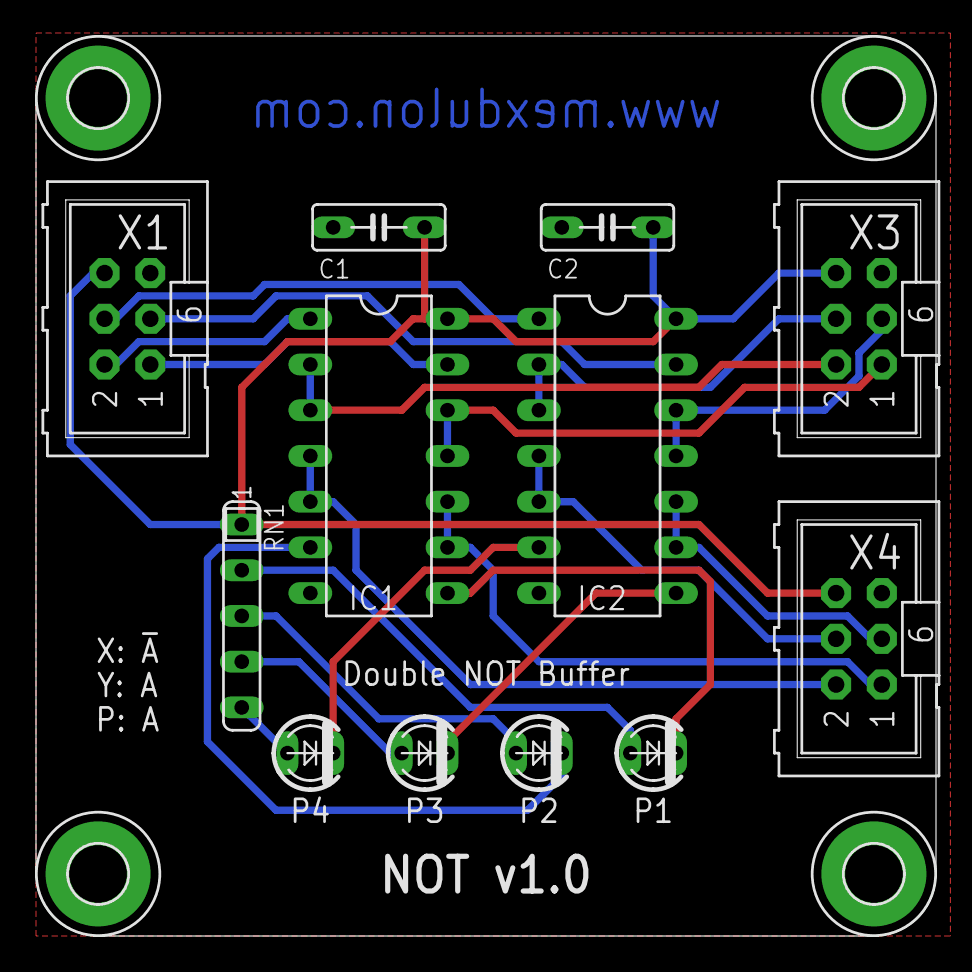
[picture p244: board NOT_1_0.brd from above]

Board: 2 copper layers, 50.0 x 50.0 mm, 16 parts (0 on the bottom side), 22 nets.
