mexdulon/tetra-Boards/eagle/DLS_1_0.brd

## EAGLE design eagle/DLS_1_0.brd (2018-04-12)

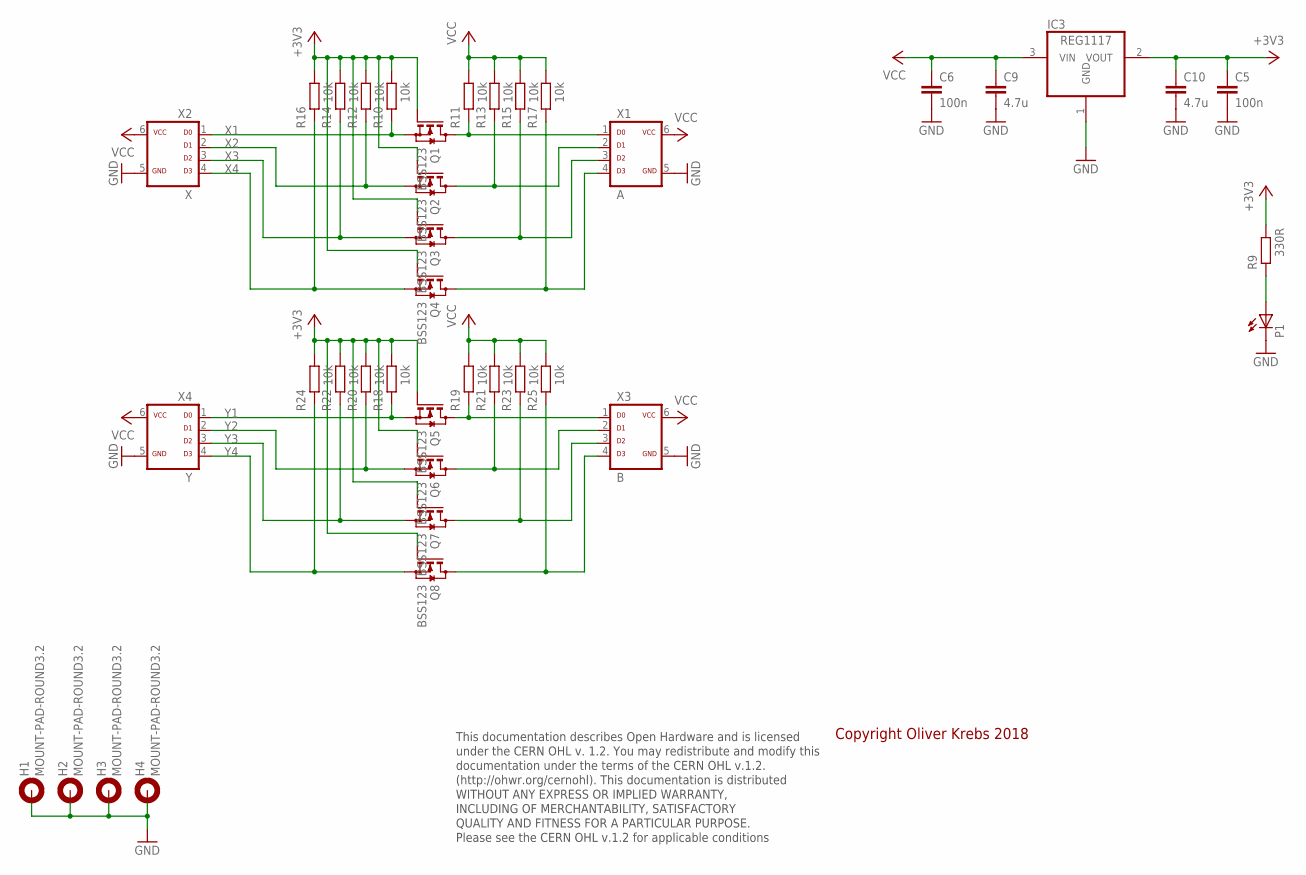
[picture p245: schematic DLS_1_0.sch]

Parts:
C5, C6: 100n; C0603
C9, C10: 4.7u; C0805K
H1, H2, H3, H4: MOUNT-PAD-ROUND3.2; 3,2-PAD
IC3: REG1117; SOT223
P1: LEDCHIPLED_1206; CHIPLED_1206
Q1, Q2, Q3, Q4, Q5, Q6, Q7, Q8: BSS123; SOT23
R9: 330R; R0402
R10, R11, R12, R13, R14, R15, R16, R17, R18, R19, R20, R21, R22, R23, R24, R25: 10k; R0402
X1: A; ML-6
X2: X; ML-6
X3: B; ML-6
X4: Y; ML-6

Connections:
+3V3: C5.1, C10.1, IC3.2 (VOUT), Q1.1 (G), Q2.1 (G), Q3.1 (G), Q4.1 (G), Q5.1 (G), Q6.1 (G), Q7.1 (G), Q8.1 (G), R9.2, R10.2, R12.2, R14.2, R16.2, R18.2, R20.2, R22.2, R24.2
GND: C5.2, C6.2, C9.2, C10.2, H1.B3,2, H2.B3,2, H3.B3,2, H4.B3,2, IC3.1 (GND), P1.C, X1.5, X2.5, X3.5, X4.5
unnamed: Q1.3 (D), R11.1, X1.1
unnamed: Q5.3 (D), R19.1, X3.1
unnamed: Q2.3 (D), R13.1, X1.2
unnamed: Q3.3 (D), R15.1, X1.3
unnamed: Q4.3 (D), R17.1, X1.4
unnamed: Q6.3 (D), R21.1, X3.2
unnamed: Q7.3 (D), R23.1, X3.3
unnamed: Q8.3 (D), R25.1, X3.4
unnamed: P1.A, R9.1
VCC: C6.1, C9.1, IC3.3 (VIN), R11.2, R13.2, R15.2, R17.2, R19.2, R21.2, R23.2, R25.2, X1.6, X2.6, X3.6, X4.6
X1: Q1.2 (S), R10.1, X2.1
X2: Q2.2 (S), R12.1, X2.2
X3: Q3.2 (S), R14.1, X2.3
X4: Q4.2 (S), R16.1, X2.4
Y1: Q5.2 (S), R18.1, X4.1
Y2: Q6.2 (S), R20.1, X4.2
Y3: Q7.2 (S), R22.1, X4.3
Y4: Q8.2 (S), R24.1, X4.4

Notes on the sheet:
This documentation describes Open Hardware and is licensed under the CERN OHL v. 1.2. You may redistribute and modify this documentation under the terms of the CERN OHL v.1.2. (http://ohwr.org/cernohl). This documentation is distributed WITHOUT ANY EXPRESS OR IMPLIED WARRANTY, INCLUDING OF MERCHANT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
Copyright Oliver Krebs 2018
