mexdulon/tetra-Boards/eagle/DLS_1_0.brd

## EAGLE design eagle/DLS_1_0.brd (continued)

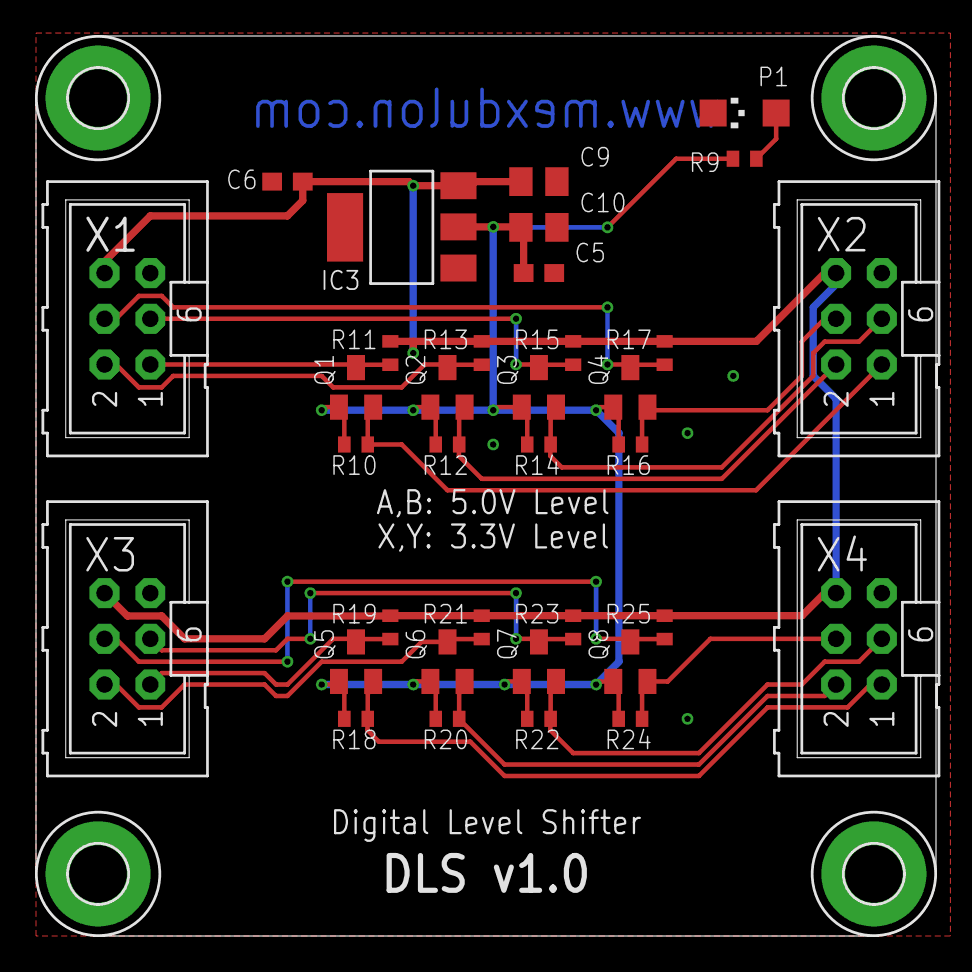
[picture p246: board DLS_1_0.brd from above]

Board: 2 copper layers, 50.0 x 50.0 mm, 39 parts (0 on the bottom side), 20 nets.
