mexdulon/tetra-Boards/eagle/M81_1_0.brd

## EAGLE design eagle/M81_1_0.brd (2017-11-03)

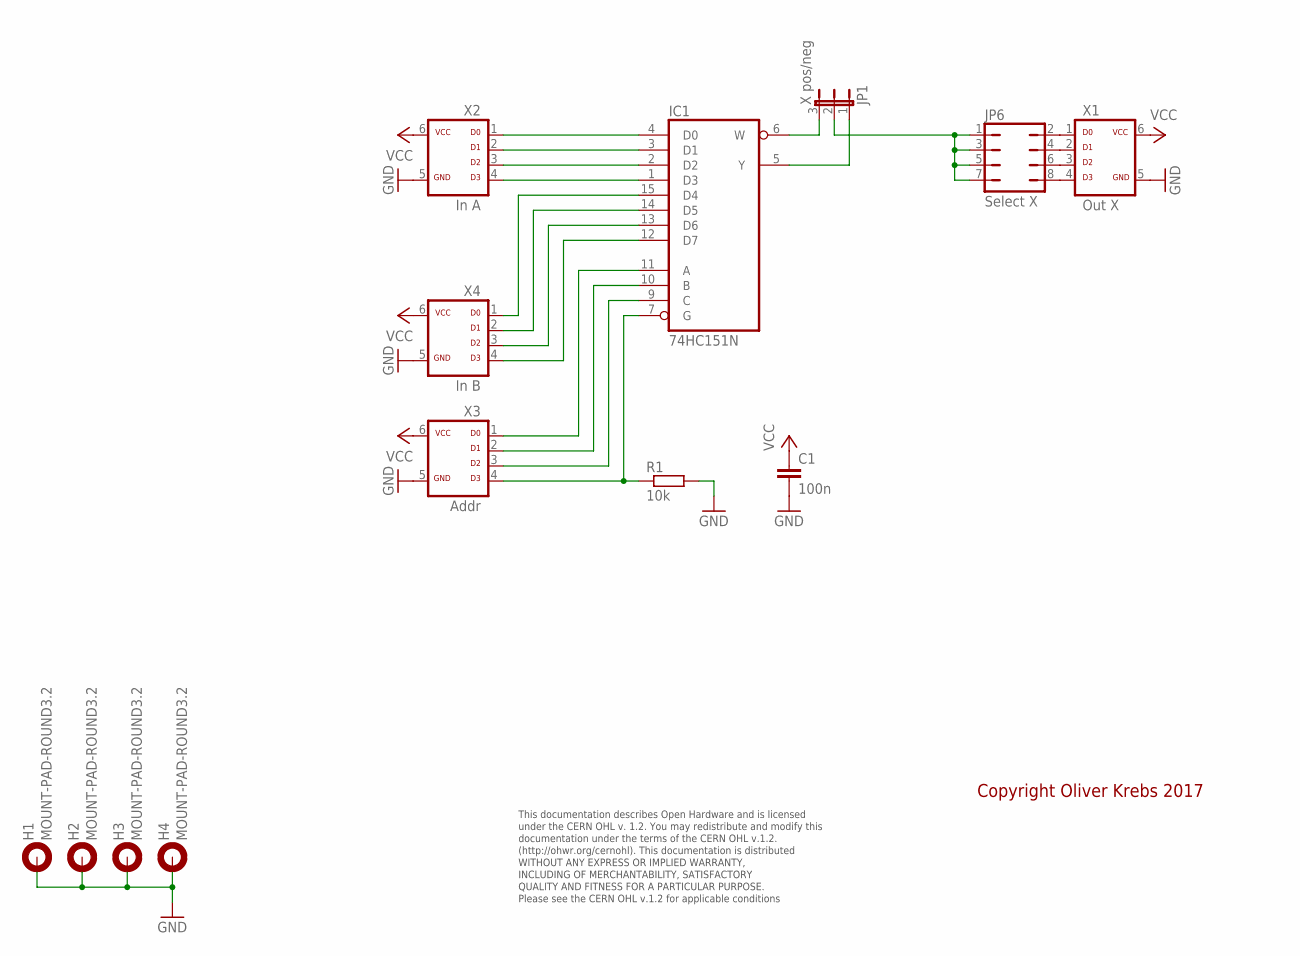
[picture p247: schematic M81_1_0.sch]

Parts:
C1: 100n; C050-025X075
H1, H2, H3, H4: MOUNT-PAD-ROUND3.2; 3,2-PAD
IC1: 74HC151N; DIL16
JP1: X pos/neg; JP2
JP6: Select X; JP4Q
R1: 10k; 0207/10
X1: Out X; ML-6
X2: In A; ML-6
X3: Addr; ML-6
X4: In B; ML-6

Connections:
GND: C1.2, H1.B3,2, H2.B3,2, H3.B3,2, H4.B3,2, IC1.8 (GND), R1.2, X1.5, X2.5, X3.5, X4.5
unnamed: IC1.5 (Y), JP1.1
unnamed: IC1.6 (W), JP1.3
unnamed: JP1.2, JP6.1, JP6.3, JP6.5, JP6.7
unnamed: IC1.4 (D0), X2.1
unnamed: IC1.3 (D1), X2.2
unnamed: IC1.2 (D2), X2.3
unnamed: IC1.1 (D3), X2.4
unnamed: IC1.15 (D4), X4.1
unnamed: IC1.14 (D5), X4.2
unnamed: IC1.13 (D6), X4.3
unnamed: IC1.12 (D7), X4.4
unnamed: IC1.11 (A), X3.1
unnamed: IC1.10 (B), X3.2
unnamed: IC1.9 (C), X3.3
unnamed: IC1.7 (G), R1.1, X3.4
unnamed: JP6.2, X1.1
unnamed: JP6.4, X1.2
unnamed: JP6.6, X1.3
unnamed: JP6.8, X1.4
VCC: C1.1, IC1.16 (VCC), X1.6, X2.6, X3.6, X4.6

Notes on the sheet:
This documentation describes Open Hardware and is licensed under the CERN OHL v. 1.2. You may redistribute and modify this documentation under the terms of the CERN OHL v.1.2. (http://ohwr.org/cernohl). This documentation is distributed WITHOUT ANY EXPRESS OR IMPLIED WARRANTY, INCLUDING OF MERCHANT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
Copyright Oliver Krebs 2017

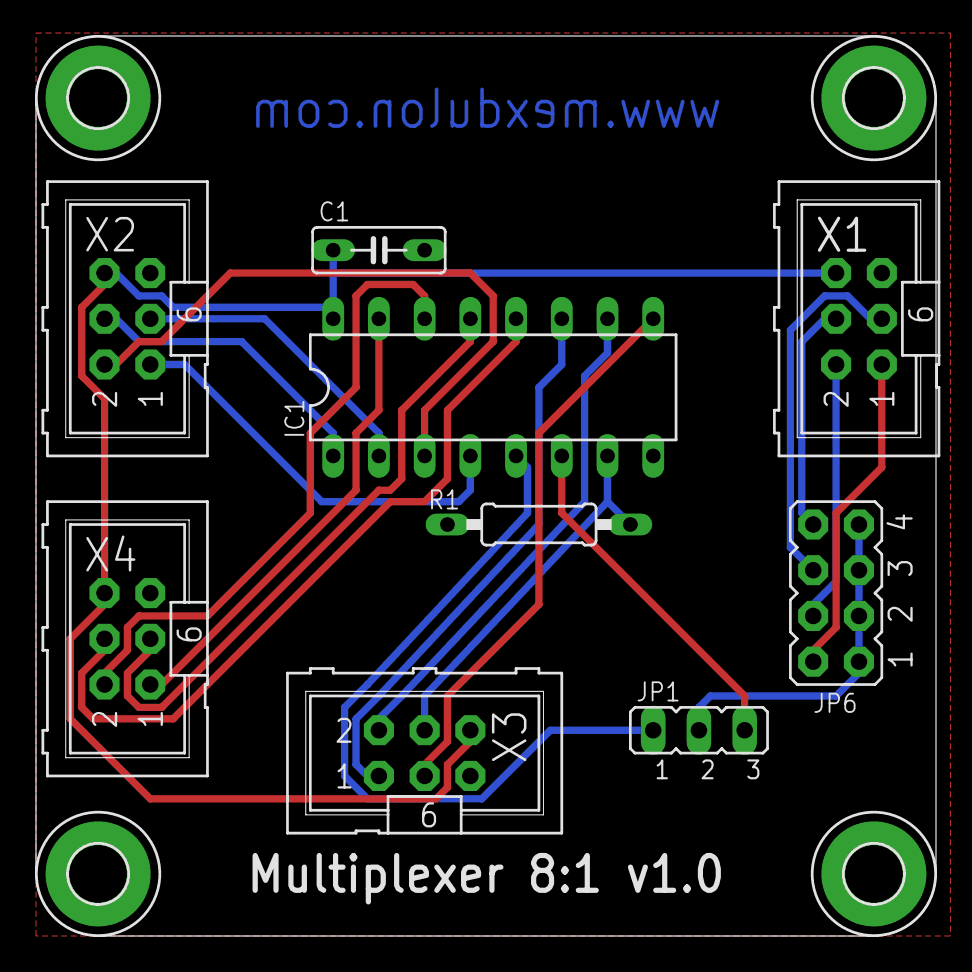
[picture p248: board M81_1_0.brd from above]

Board: 2 copper layers, 50.0 x 50.0 mm, 13 parts (0 on the bottom side), 21 nets.
