mexdulon/tetra-Boards/eagle/D14_1_0.brd

## EAGLE design eagle/D14_1_0.brd (2017-11-03)

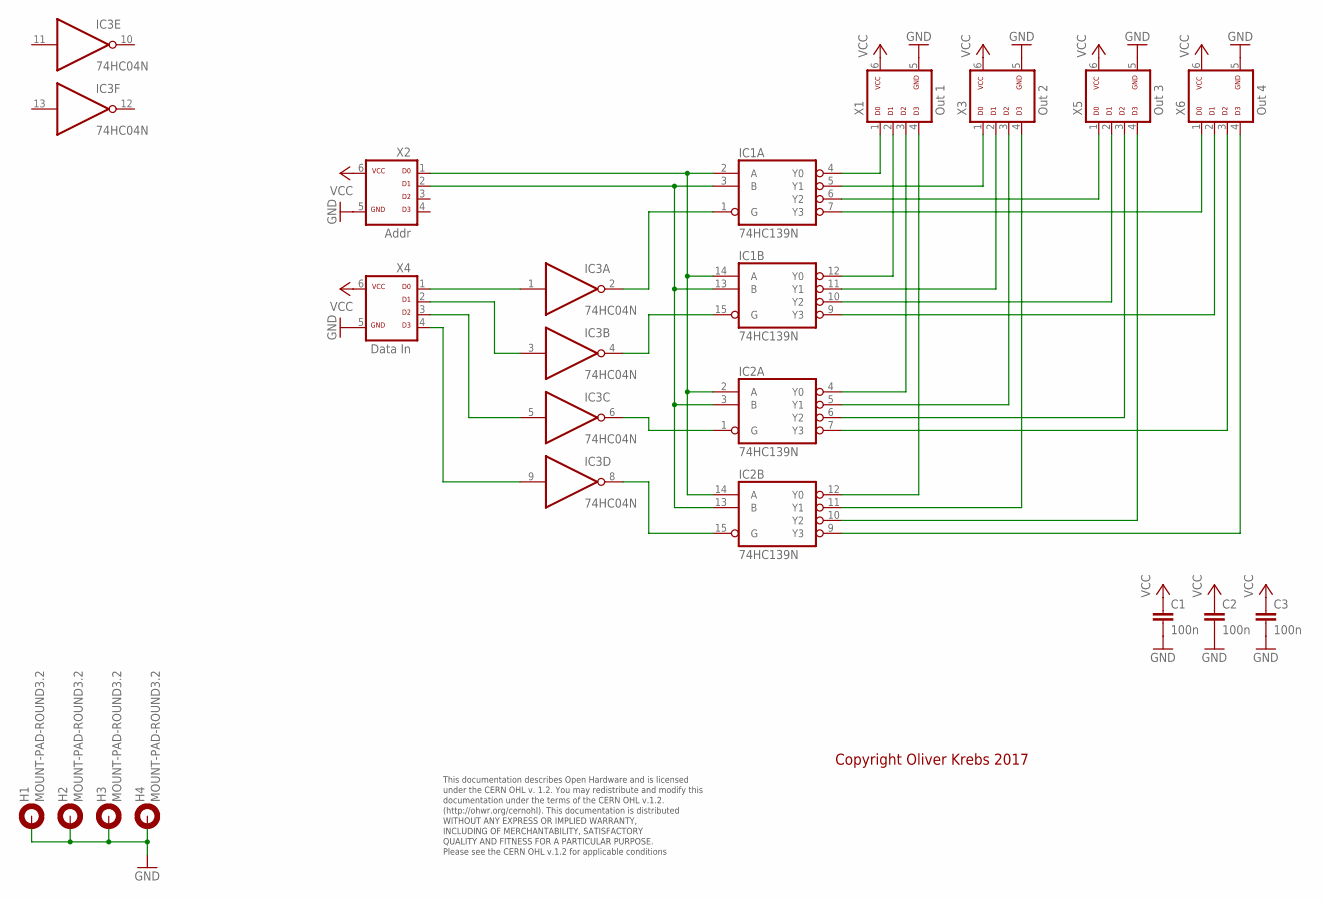
[picture p249: schematic D14_1_0.sch]

Parts:
C1, C2, C3: 100n; C050-025X075
H1, H2, H3, H4: MOUNT-PAD-ROUND3.2; 3,2-PAD
IC1, IC2: 74HC139N; DIL16
IC3: 74HC04N; DIL14
X1: Out 1; ML-6
X2: Addr; ML-6
X3: Out 2; ML-6
X4: Data In; ML-6
X5: Out 3; ML-6
X6: Out 4; ML-6

Connections:
GND: C1.2, C2.2, C3.2, H1.B3,2, H2.B3,2, H3.B3,2, H4.B3,2, IC1.8 (GND), IC2.8 (GND), IC3.7 (GND), X1.5, X2.5, X3.5, X4.5, X5.5, X6.5
unnamed: IC1.2 (A), IC1.14 (A), IC2.2 (A), IC2.14 (A), X2.1
unnamed: IC1.3 (B), IC1.13 (B), IC2.3 (B), IC2.13 (B), X2.2
unnamed: IC1.4 (Y0), X1.1
unnamed: IC1.12 (Y0), X1.2
unnamed: IC2.4 (Y0), X1.3
unnamed: IC2.12 (Y0), X1.4
unnamed: IC1.5 (Y1), X3.1
unnamed: IC1.11 (Y1), X3.2
unnamed: IC2.5 (Y1), X3.3
unnamed: IC2.11 (Y1), X3.4
unnamed: IC1.6 (Y2), X5.1
unnamed: IC1.10 (Y2), X5.2
unnamed: IC2.6 (Y2), X5.3
unnamed: IC2.10 (Y2), X5.4
unnamed: IC1.7 (Y3), X6.1
unnamed: IC1.9 (Y3), X6.2
unnamed: IC2.7 (Y3), X6.3
unnamed: IC2.9 (Y3), X6.4
unnamed: IC1.1 (G), IC3.2 (O)
unnamed: IC1.15 (G), IC3.4 (O)
unnamed: IC2.1 (G), IC3.6 (O)
unnamed: IC2.15 (G), IC3.8 (O)
unnamed: IC3.1 (I), X4.1
unnamed: IC3.3 (I), X4.2
unnamed: IC3.5 (I), X4.3
unnamed: IC3.9 (I), X4.4
VCC: C1.1, C2.1, C3.1, IC1.16 (VCC), IC2.16 (VCC), IC3.14 (VCC), X1.6, X2.6, X3.6, X4.6, X5.6, X6.6

Notes on the sheet:
This documentation describes Open Hardware and is licensed under the CERN OHL v. 1.2. You may redistribute and modify this documentation under the terms of the CERN OHL v.1.2. (http://ohwr.org/cernohl). This documentation is distributed WITHOUT ANY EXPRESS OR IMPLIED WARRANTY, INCLUDING OF MERCHANT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
Copyright Oliver Krebs 2017

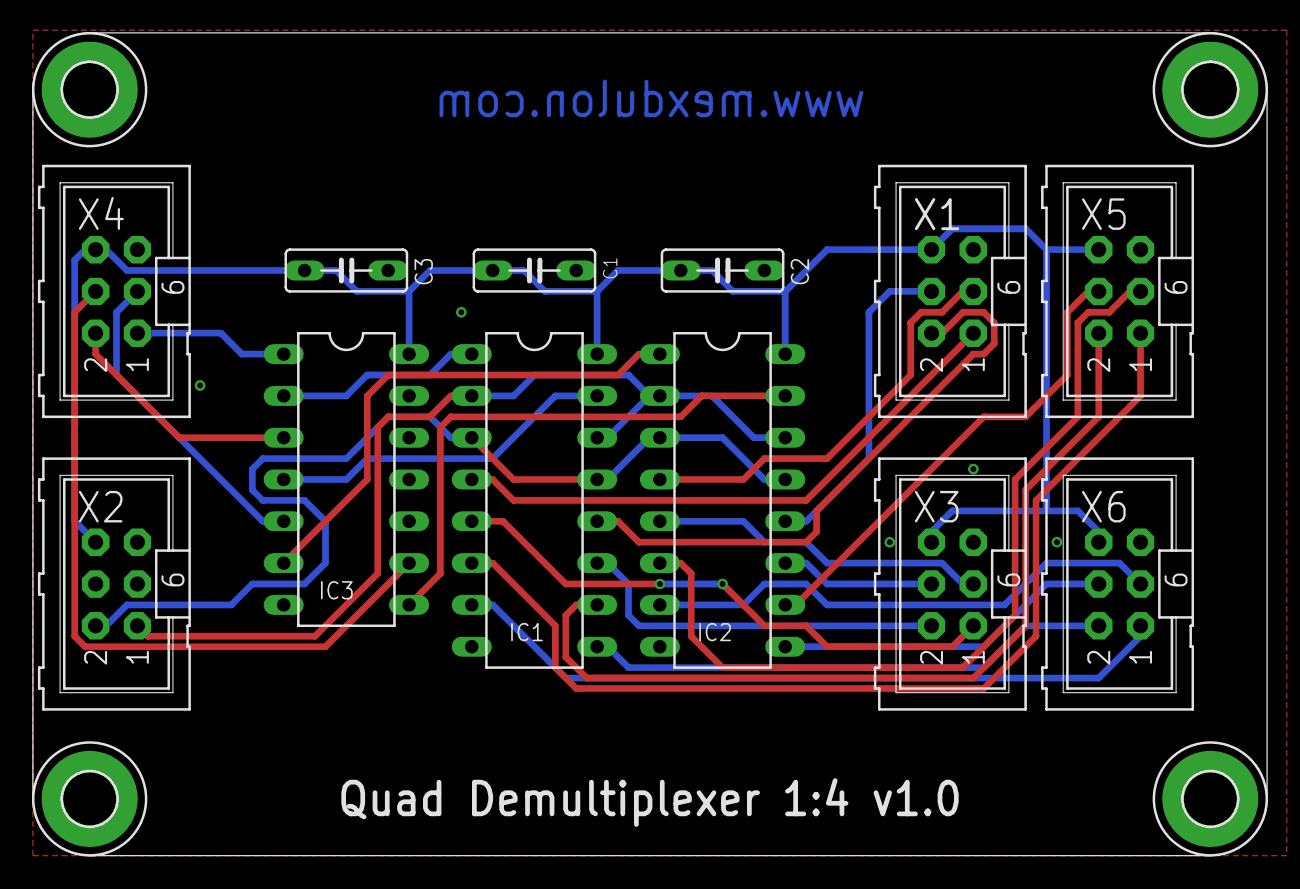
[picture p250: board D14_1_0.brd from above]

Board: 2 copper layers, 75.0 x 50.0 mm, 16 parts (0 on the bottom side), 28 nets.
