mexdulon/tetra-Boards/eagle/SWI_1_1.brd

## EAGLE design eagle/SWI_1_1.brd (2017-11-03)

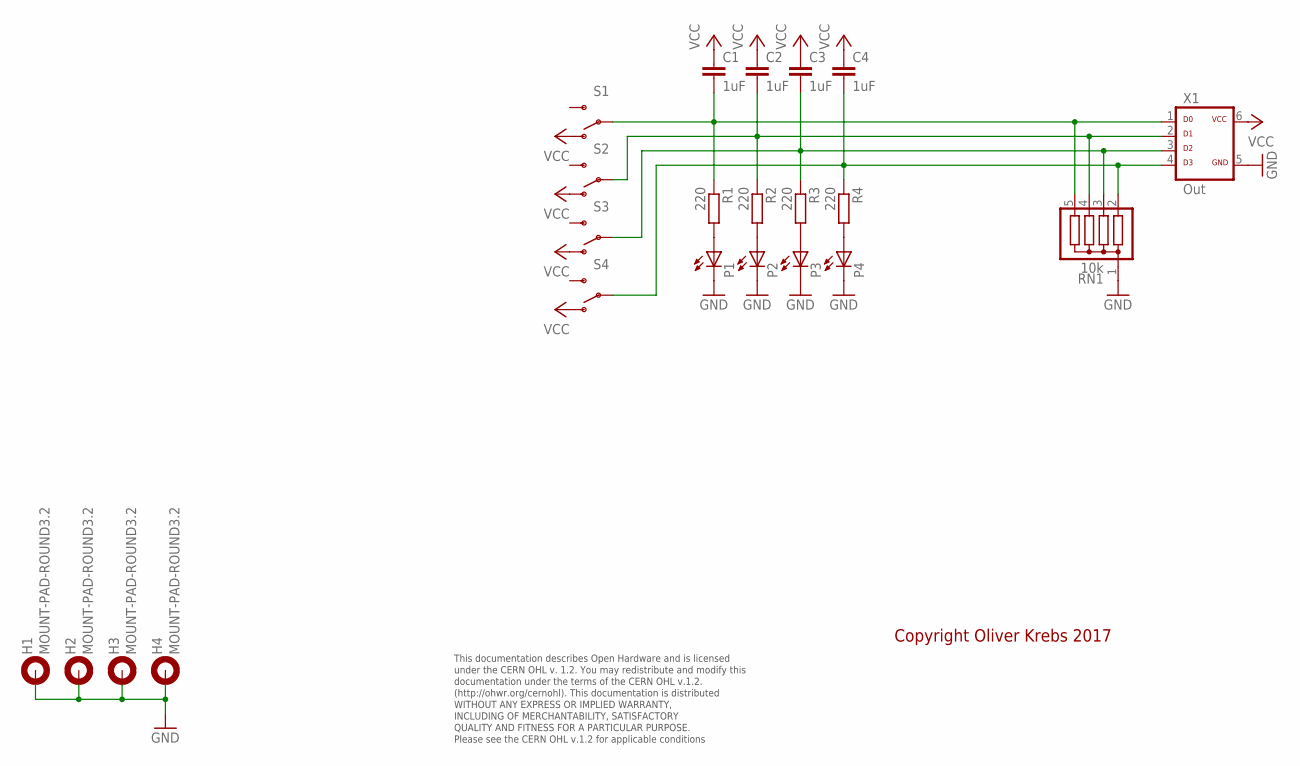
[picture p251: schematic SWI_1_1.sch]

Parts:
C1, C2, C3, C4: 1uF; C050-025X075
H1, H2, H3, H4: MOUNT-PAD-ROUND3.2; 3,2-PAD
P1, P2, P3, P4: LED3MM
R1, R2, R3, R4: 220; 0207/10
RN1: 10k; SIL5
S1, S2, S3, S4: SWITCH-AS500APC
X1: Out; ML-6

Connections:
GND: H1.B3,2, H2.B3,2, H3.B3,2, H4.B3,2, P1.K (C), P2.K (C), P3.K (C), P4.K (C), RN1.1, X1.5
unnamed: C1.2, R1.1, RN1.5, S1.P, X1.1
unnamed: C2.2, R2.1, RN1.4, S2.P, X1.2
unnamed: C3.2, R3.1, RN1.3, S3.P, X1.3
unnamed: C4.2, R4.1, RN1.2, S4.P, X1.4
unnamed: P1.A, R1.2
unnamed: P2.A, R2.2
unnamed: P3.A, R3.2
unnamed: P4.A, R4.2
VCC: C1.1, C2.1, C3.1, C4.1, S1.O, S2.O, S3.O, S4.O, X1.6

Notes on the sheet:
This documentation describes Open Hardware and is licensed under the CERN OHL v. 1.2. You may redistribute and modify this documentation under the terms of the CERN OHL v.1.2. (http://ohwr.org/cernohl). This documentation is distributed WITHOUT ANY EXPRESS OR IMPLIED WARRANTY, INCLUDING OF MERCHANT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
Copyright Oliver Krebs 2017

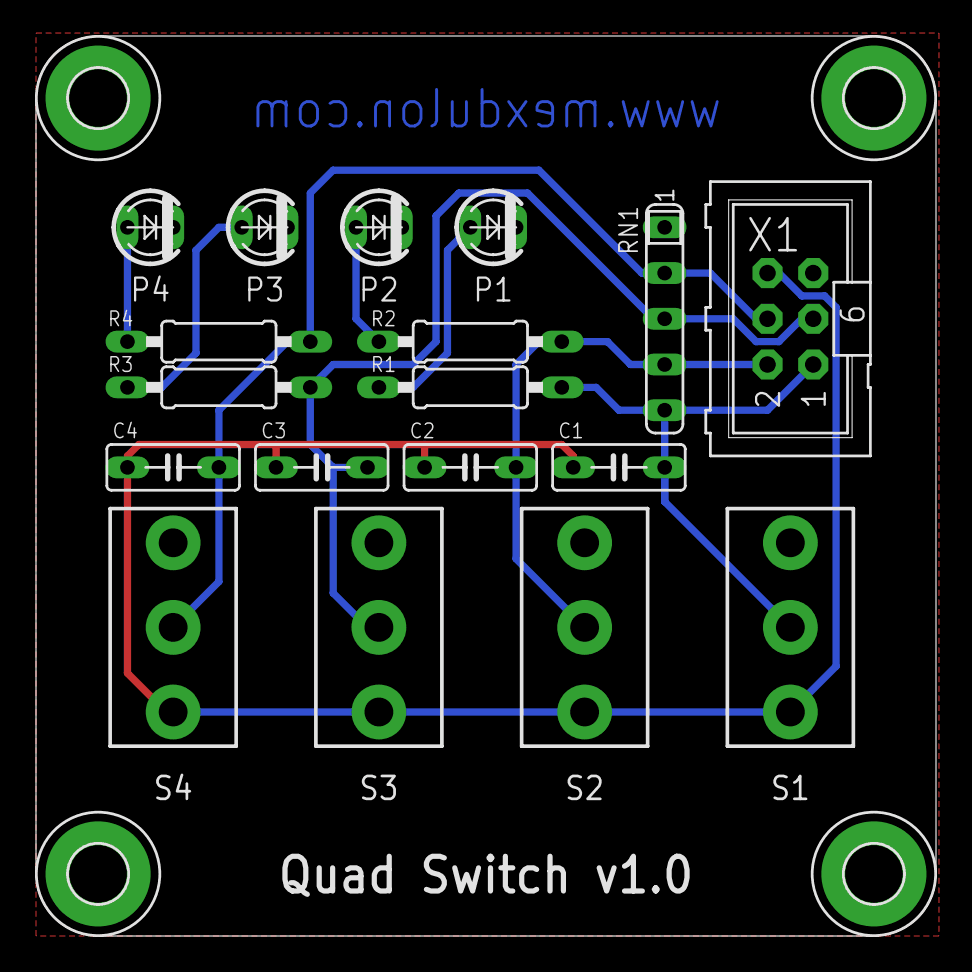
[picture p252: board SWI_1_1.brd from above]

Board: 2 copper layers, 50.0 x 50.0 mm, 22 parts (0 on the bottom side), 10 nets.
