mexdulon/tetra-Boards/eagle/DIP_1_0.brd

## EAGLE design eagle/DIP_1_0.brd (2017-11-03)

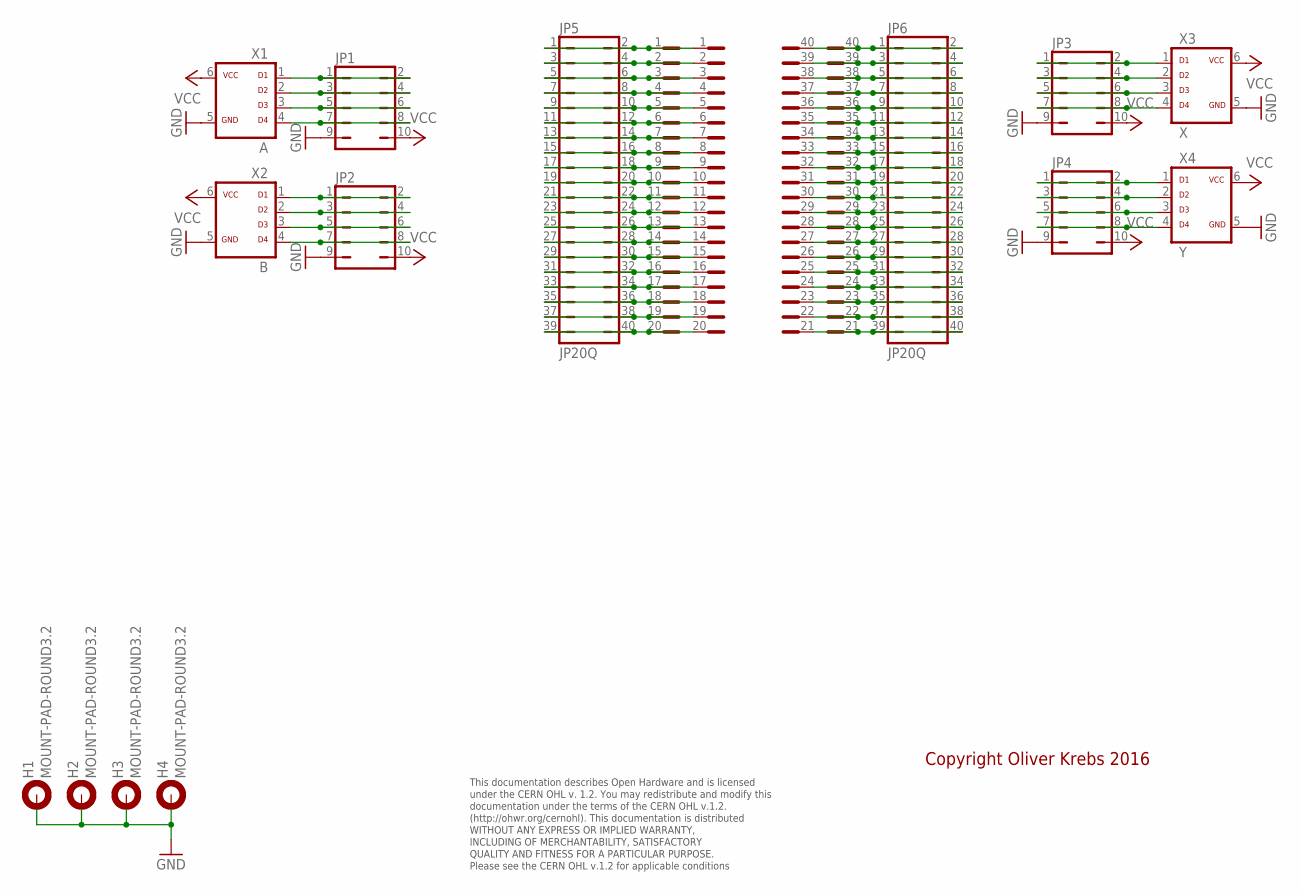
[picture p253: schematic DIP_1_0.sch]

Parts:
H1, H2, H3, H4: MOUNT-PAD-ROUND3.2; 3,2-PAD
JP1, JP2, JP3, JP4: JP5Q
JP5, JP6: JP20Q
X1: A; ML-6
X2: B; ML-6
X3: X; ML-6
X4: Y; ML-6
X5: DIL40-3
X6: DIL40-6

Connections:
GND: H1.B3,2, H2.B3,2, H3.B3,2, H4.B3,2, JP1.9, JP2.9, JP3.9, JP4.9, X1.5, X2.5, X3.5, X4.5
unnamed: JP3.1, JP3.2, X3.1
unnamed: JP3.3, JP3.4, X3.2
unnamed: JP3.5, JP3.6, X3.3
unnamed: JP3.7, JP3.8, X3.4
unnamed: JP4.1, JP4.2, X4.1
unnamed: JP4.3, JP4.4, X4.2
unnamed: JP4.5, JP4.6, X4.3
unnamed: JP4.7, JP4.8, X4.4
unnamed: JP1.1, JP1.2, X1.1
unnamed: JP1.3, JP1.4, X1.2
unnamed: JP1.5, JP1.6, X1.3
unnamed: JP1.7, JP1.8, X1.4
unnamed: JP2.1, JP2.2, X2.1
unnamed: JP2.3, JP2.4, X2.2
unnamed: JP2.5, JP2.6, X2.3
unnamed: JP2.7, JP2.8, X2.4
unnamed: JP5.1, JP5.2, X5.1, X6.1
unnamed: JP5.3, JP5.4, X5.2, X6.2
unnamed: JP5.5, JP5.6, X5.3, X6.3
unnamed: JP5.7, JP5.8, X5.4, X6.4
unnamed: JP5.9, JP5.10, X5.5, X6.5
unnamed: JP5.11, JP5.12, X5.6, X6.6
unnamed: JP5.13, JP5.14, X5.7, X6.7
unnamed: JP5.15, JP5.16, X5.8, X6.8
unnamed: JP5.17, JP5.18, X5.9, X6.9
unnamed: JP5.19, JP5.20, X5.10, X6.10
unnamed: JP5.21, JP5.22, X5.11, X6.11
unnamed: JP5.23, JP5.24, X5.12, X6.12
unnamed: JP5.25, JP5.26, X5.13, X6.13
unnamed: JP5.27, JP5.28, X5.14, X6.14
unnamed: JP5.29, JP5.30, X5.15, X6.15
unnamed: JP5.31, JP5.32, X5.16, X6.16
unnamed: JP5.33, JP5.34, X5.17, X6.17
unnamed: JP5.35, JP5.36, X5.18, X6.18
unnamed: JP5.37, JP5.38, X5.19, X6.19
unnamed: JP5.39, JP5.40, X5.20, X6.20
unnamed: JP6.1, JP6.2, X5.40, X6.40
unnamed: JP6.3, JP6.4, X5.39, X6.39
unnamed: JP6.5, JP6.6, X5.38, X6.38
unnamed: JP6.7, JP6.8, X5.37, X6.37
unnamed: JP6.9, JP6.10, X5.36, X6.36
unnamed: JP6.11, JP6.12, X5.35, X6.35
unnamed: JP6.13, JP6.14, X5.34, X6.34
unnamed: JP6.15, JP6.16, X5.33, X6.33
unnamed: JP6.17, JP6.18, X5.32, X6.32
unnamed: JP6.19, JP6.20, X5.31, X6.31
unnamed: JP6.21, JP6.22, X5.30, X6.30
unnamed: JP6.23, JP6.24, X5.29, X6.29
unnamed: JP6.25, JP6.26, X5.28, X6.28
unnamed: JP6.27, JP6.28, X5.27, X6.27
unnamed: JP6.29, JP6.30, X5.26, X6.26
unnamed: JP6.31, JP6.32, X5.25, X6.25
unnamed: JP6.33, JP6.34, X5.24, X6.24
unnamed: JP6.35, JP6.36, X5.23, X6.23
unnamed: JP6.37, JP6.38, X5.22, X6.22
unnamed: JP6.39, JP6.40, X5.21, X6.21
VCC: JP1.10, JP2.10, JP3.10, JP4.10, X1.6, X2.6, X3.6, X4.6

Notes on the sheet:
This documentation describes Open Hardware and is licensed under the CERN OHL v. 1.2. You may redistribute and modify this documentation under the terms of the CERN OHL v.1.2. (http://ohwr.org/cernohl). This documentation is distributed WITHOUT ANY EXPRESS OR IMPLIED WARRANTY, INCLUDING OF MERCHANT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
Copyright Oliver Krebs 2016

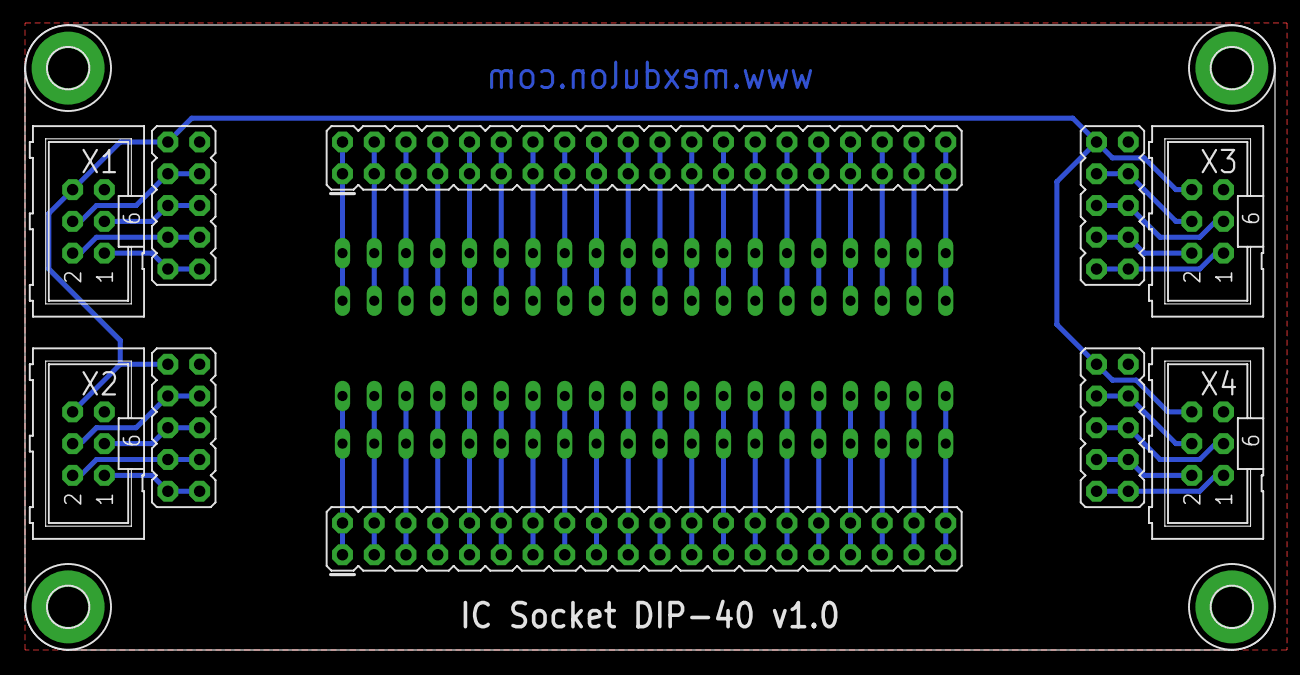
[picture p254: board DIP_1_0.brd from above]

Board: 2 copper layers, 100.0 x 50.0 mm, 16 parts (0 on the bottom side), 58 nets.
