mexdulon/tetra-Boards/eagle/ALU_1_0.brd

## EAGLE design eagle/ALU_1_0.brd (2017-11-03)

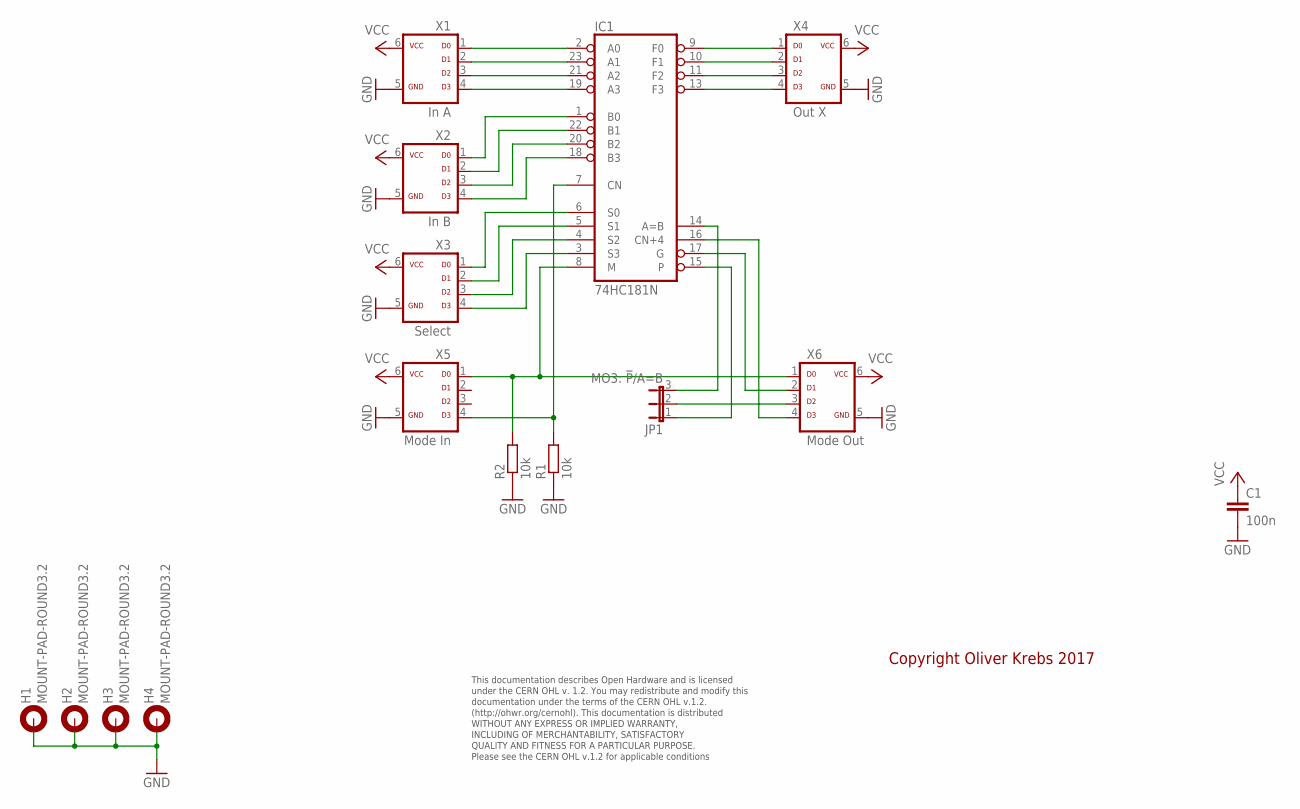
[picture p255: schematic ALU_1_0.sch]

Parts:
C1: 100n; C050-025X075
H1, H2, H3, H4: MOUNT-PAD-ROUND3.2; 3,2-PAD
IC1: 74HC181N; DIL24-6
JP1: MO3: !P!/A=B; JP2
R1, R2: 10k; 0207/10
X1: In A; ML-6
X2: In B; ML-6
X3: Select; ML-6
X4: Out X; ML-6
X5: Mode In; ML-6
X6: Mode Out; ML-6

Connections:
GND: C1.2, H1.B3,2, H2.B3,2, H3.B3,2, H4.B3,2, IC1.12 (GND), R1.1, R2.1, X1.5, X2.5, X3.5, X4.5, X5.5, X6.5
unnamed: IC1.9 (F0), X4.1
unnamed: IC1.10 (F1), X4.2
unnamed: IC1.11 (F2), X4.3
unnamed: IC1.13 (F3), X4.4
unnamed: IC1.2 (A0), X1.1
unnamed: IC1.23 (A1), X1.2
unnamed: IC1.21 (A2), X1.3
unnamed: IC1.19 (A3), X1.4
unnamed: IC1.1 (B0), X2.1
unnamed: IC1.22 (B1), X2.2
unnamed: IC1.20 (B2), X2.3
unnamed: IC1.18 (B3), X2.4
unnamed: IC1.6 (S0), X3.1
unnamed: IC1.5 (S1), X3.2
unnamed: IC1.4 (S2), X3.3
unnamed: IC1.3 (S3), X3.4
unnamed: IC1.8 (M), R2.2, X5.1, X6.1
unnamed: IC1.7 (CN), R1.2, X5.4
unnamed: IC1.16 (CN+4), X6.4
unnamed: IC1.15, JP1.1
unnamed: JP1.2, X6.3
unnamed: IC1.14 (A=B), JP1.3
unnamed: IC1.17 (G), X6.2
VCC: C1.1, IC1.24 (VCC), X1.6, X2.6, X3.6, X4.6, X5.6, X6.6

Notes on the sheet:
This documentation describes Open Hardware and is licensed under the CERN OHL v. 1.2. You may redistribute and modify this documentation under the terms of the CERN OHL v.1.2. (http://ohwr.org/cernohl). This documentation is distributed WITHOUT ANY EXPRESS OR IMPLIED WARRANTY, INCLUDING OF MERCHANT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
Copyright Oliver Krebs 2017

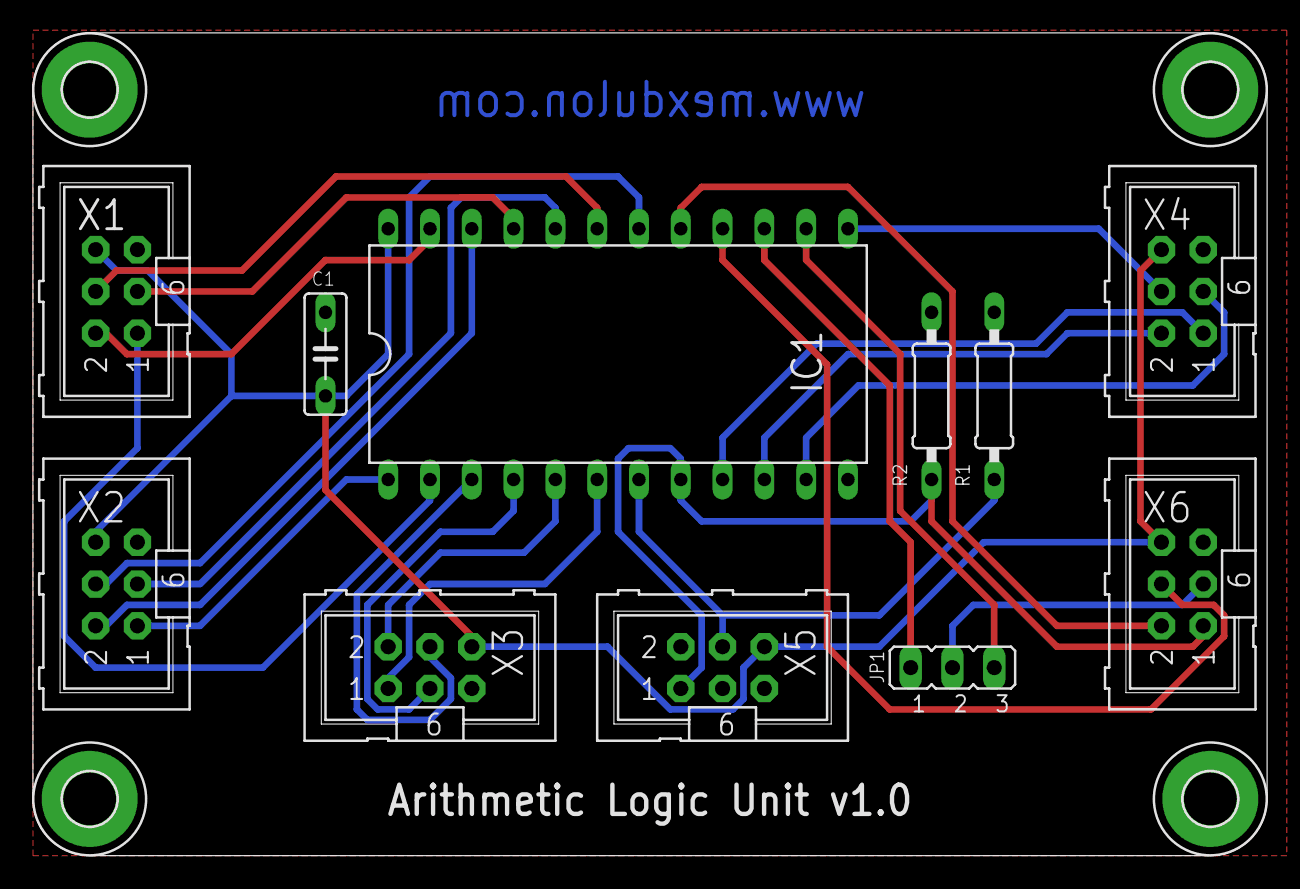
[picture p256: board ALU_1_0.brd from above]

Board: 2 copper layers, 75.0 x 50.0 mm, 15 parts (0 on the bottom side), 25 nets.
