mexdulon/tetra-Boards/eagle/N33_1_0.brd

## EAGLE design eagle/N33_1_0.brd (2017-11-03)

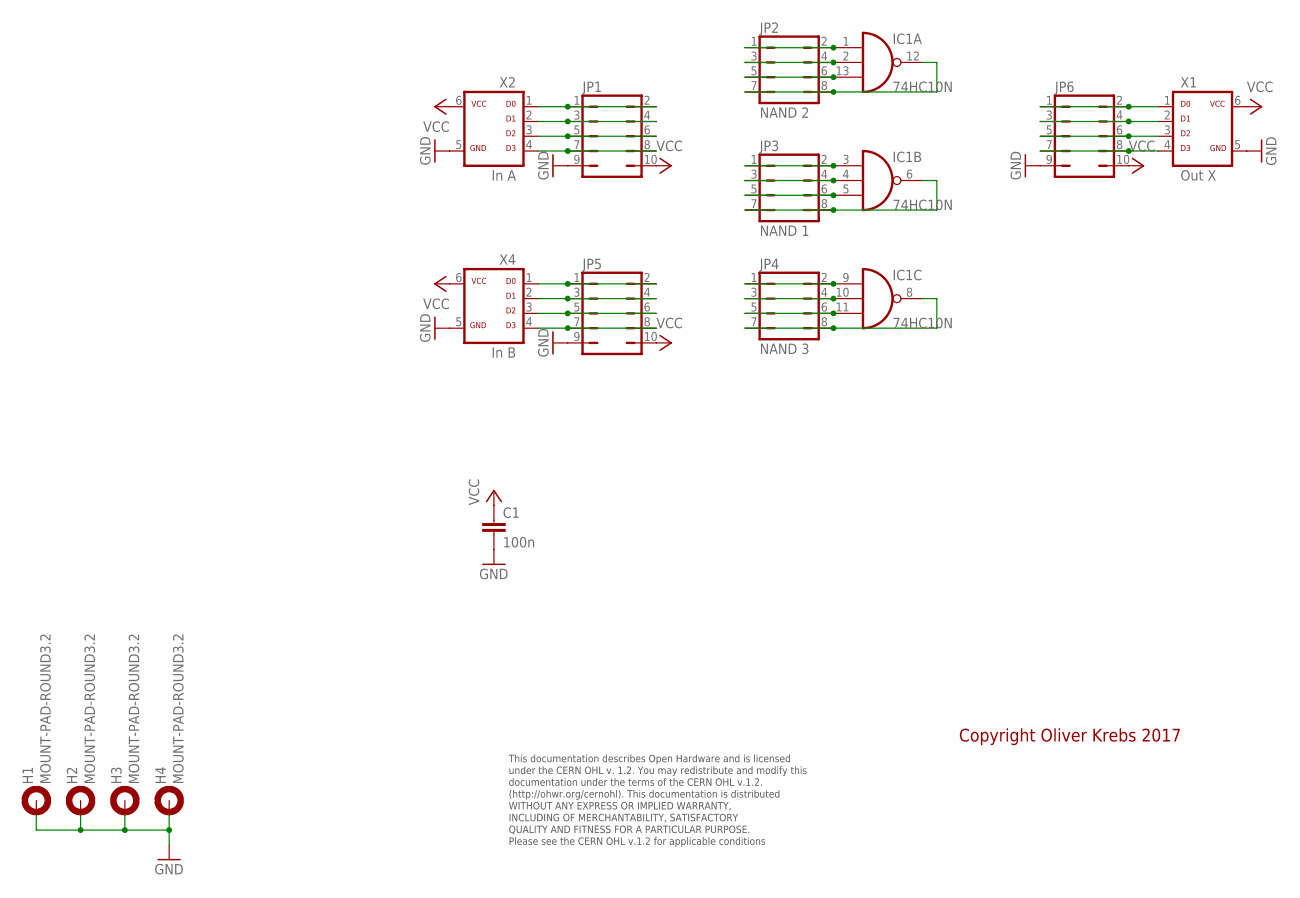
[picture p257: schematic N33_1_0.sch]

Parts:
C1: 100n; C050-025X075
H1, H2, H3, H4: MOUNT-PAD-ROUND3.2; 3,2-PAD
IC1: 74HC10N; DIL14
JP1, JP5, JP6: JP5Q
JP2: NAND 2; JP4Q
JP3: NAND 1; JP4Q
JP4: NAND 3; JP4Q
X1: Out X; ML-6
X2: In A; ML-6
X4: In B; ML-6

Connections:
GND: C1.2, H1.B3,2, H2.B3,2, H3.B3,2, H4.B3,2, IC1.7 (GND), JP1.9, JP5.9, JP6.9, X1.5, X2.5, X4.5
unnamed: IC1.1 (I0), JP2.1, JP2.2
unnamed: IC1.2 (I1), JP2.3, JP2.4
unnamed: IC1.13 (I2), JP2.5, JP2.6
unnamed: IC1.3 (I0), JP3.1, JP3.2
unnamed: IC1.4 (I1), JP3.3, JP3.4
unnamed: JP5.1, JP5.2, X4.1
unnamed: JP5.3, JP5.4, X4.2
unnamed: JP5.5, JP5.6, X4.3
unnamed: JP5.7, JP5.8, X4.4
unnamed: IC1.5 (I2), JP3.5, JP3.6
unnamed: IC1.9 (I0), JP4.1, JP4.2
unnamed: IC1.10 (I1), JP4.3, JP4.4
unnamed: IC1.11 (I2), JP4.5, JP4.6
unnamed: JP1.1, JP1.2, X2.1
unnamed: JP1.3, JP1.4, X2.2
unnamed: JP1.5, JP1.6, X2.3
unnamed: JP1.7, JP1.8, X2.4
unnamed: JP6.1, JP6.2, X1.1
unnamed: JP6.3, JP6.4, X1.2
unnamed: JP6.5, JP6.6, X1.3
unnamed: JP6.7, JP6.8, X1.4
unnamed: IC1.8 (O), JP4.7, JP4.8
unnamed: IC1.6 (O), JP3.7, JP3.8
unnamed: IC1.12 (O), JP2.7, JP2.8
VCC: C1.1, IC1.14 (VCC), JP1.10, JP5.10, JP6.10, X1.6, X2.6, X4.6

Notes on the sheet:
This documentation describes Open Hardware and is licensed under the CERN OHL v. 1.2. You may redistribute and modify this documentation under the terms of the CERN OHL v.1.2. (http://ohwr.org/cernohl). This documentation is distributed WITHOUT ANY EXPRESS OR IMPLIED WARRANTY, INCLUDING OF MERCHANT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
Copyright Oliver Krebs 2017

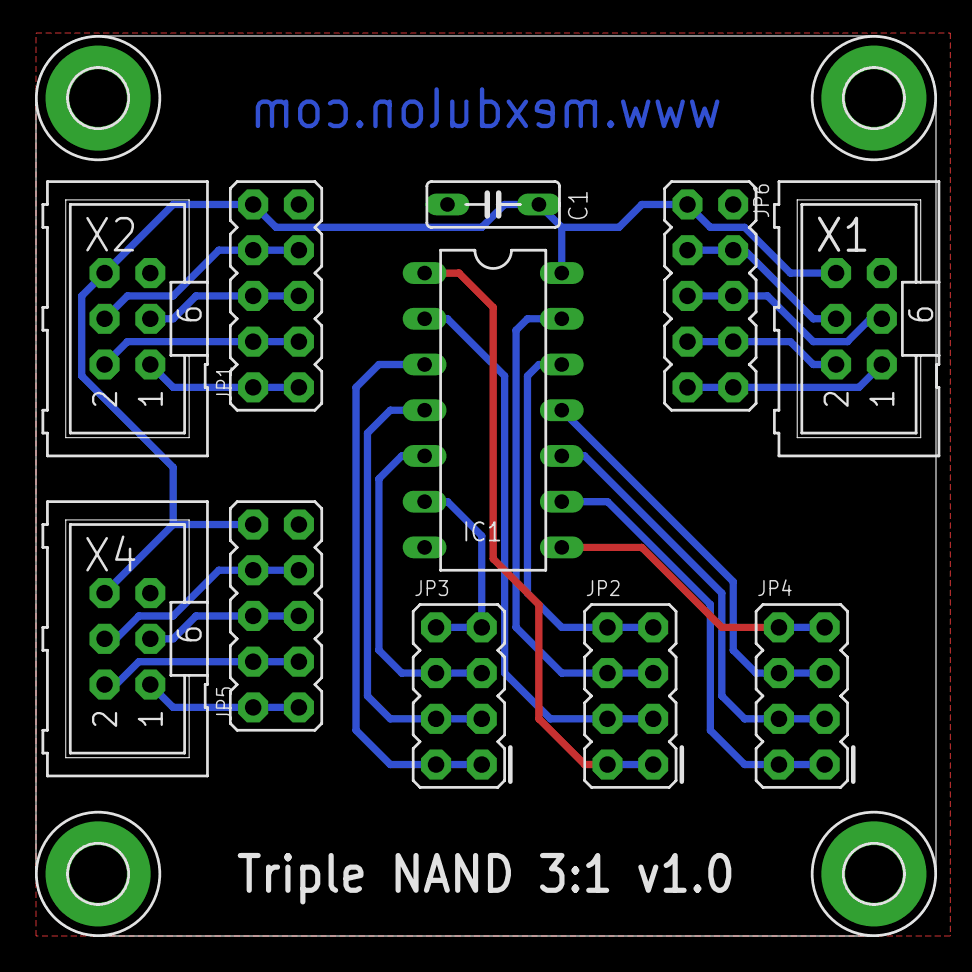
[picture p258: board N33_1_0.brd from above]

Board: 2 copper layers, 50.0 x 50.0 mm, 15 parts (0 on the bottom side), 26 nets.
