mexdulon/tetra-Boards/eagle/CNT_1_1.brd

## EAGLE design eagle/CNT_1_1.brd (2017-11-03)

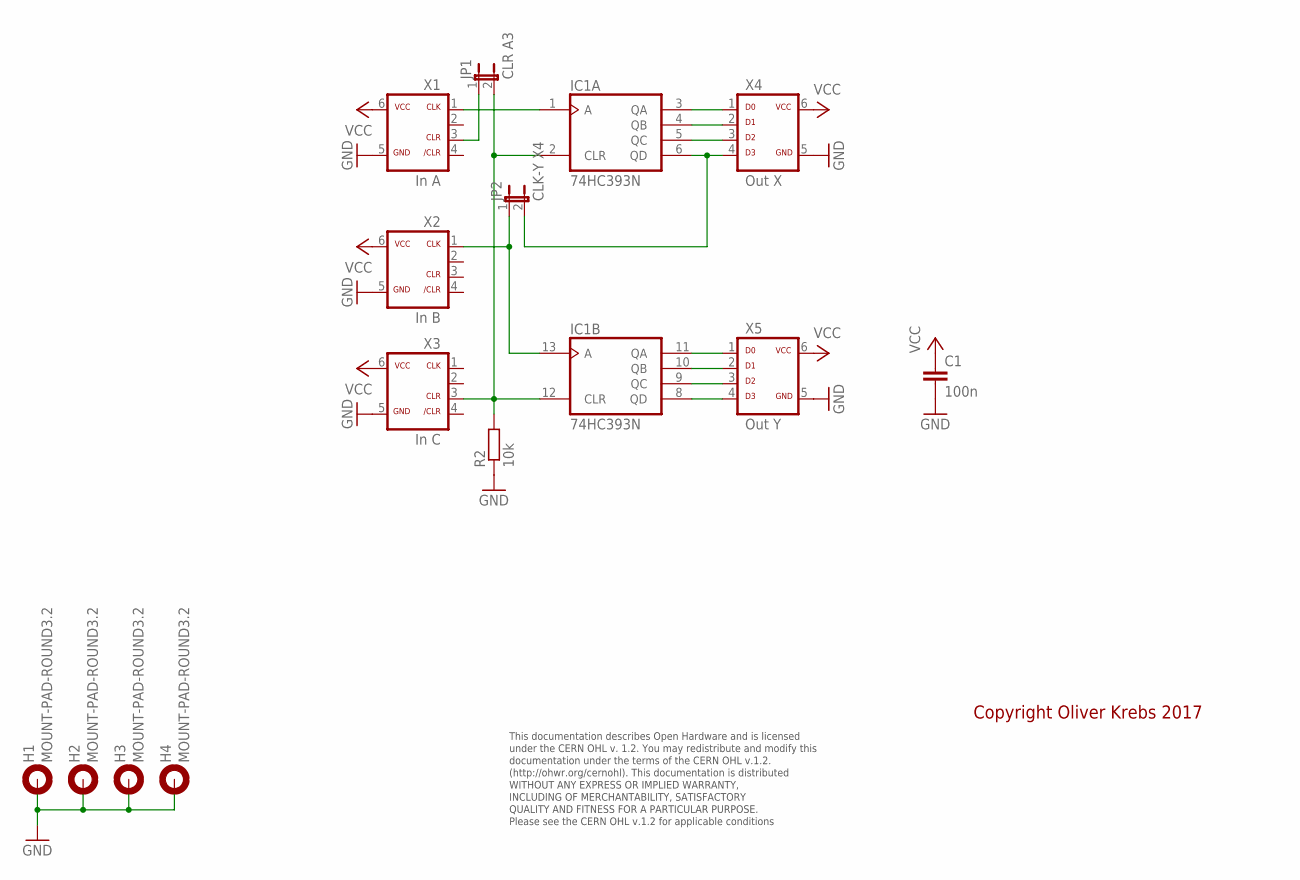
[picture p259: schematic CNT_1_1.sch]

Parts:
C1: 100n; C050-025X075
H1, H2, H3, H4: MOUNT-PAD-ROUND3.2; 3,2-PAD
IC1: 74HC393N; DIL14
JP1: CLR A3; JP1
JP2: CLK-Y X4; JP1
R2: 10k; 0207/10
X1: In A; ML-6
X2: In B; ML-6
X3: In C; ML-6
X4: Out X; ML-6
X5: Out Y; ML-6

Connections:
GND: C1.2, H1.B3,2, H2.B3,2, H3.B3,2, H4.B3,2, IC1.7 (GND), R2.1, X1.5, X2.5, X3.5, X4.5, X5.5
unnamed: IC1.3 (QA), X4.1
unnamed: IC1.4 (QB), X4.2
unnamed: IC1.5 (QC), X4.3
unnamed: IC1.1 (A), X1.1
unnamed: JP1.1, X1.3
unnamed: IC1.6 (QD), JP2.2, X4.4
unnamed: IC1.2 (CLR), IC1.12 (CLR), JP1.2, R2.2, X3.3
unnamed: IC1.13 (A), JP2.1, X2.1
unnamed: IC1.11 (QA), X5.1
unnamed: IC1.10 (QB), X5.2
unnamed: IC1.9 (QC), X5.3
unnamed: IC1.8 (QD), X5.4
VCC: C1.1, IC1.14 (VCC), X1.6, X2.6, X3.6, X4.6, X5.6

Notes on the sheet:
This documentation describes Open Hardware and is licensed under the CERN OHL v. 1.2. You may redistribute and modify this documentation under the terms of the CERN OHL v.1.2. (http://ohwr.org/cernohl). This documentation is distributed WITHOUT ANY EXPRESS OR IMPLIED WARRANTY, INCLUDING OF MERCHANT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
Copyright Oliver Krebs 2017

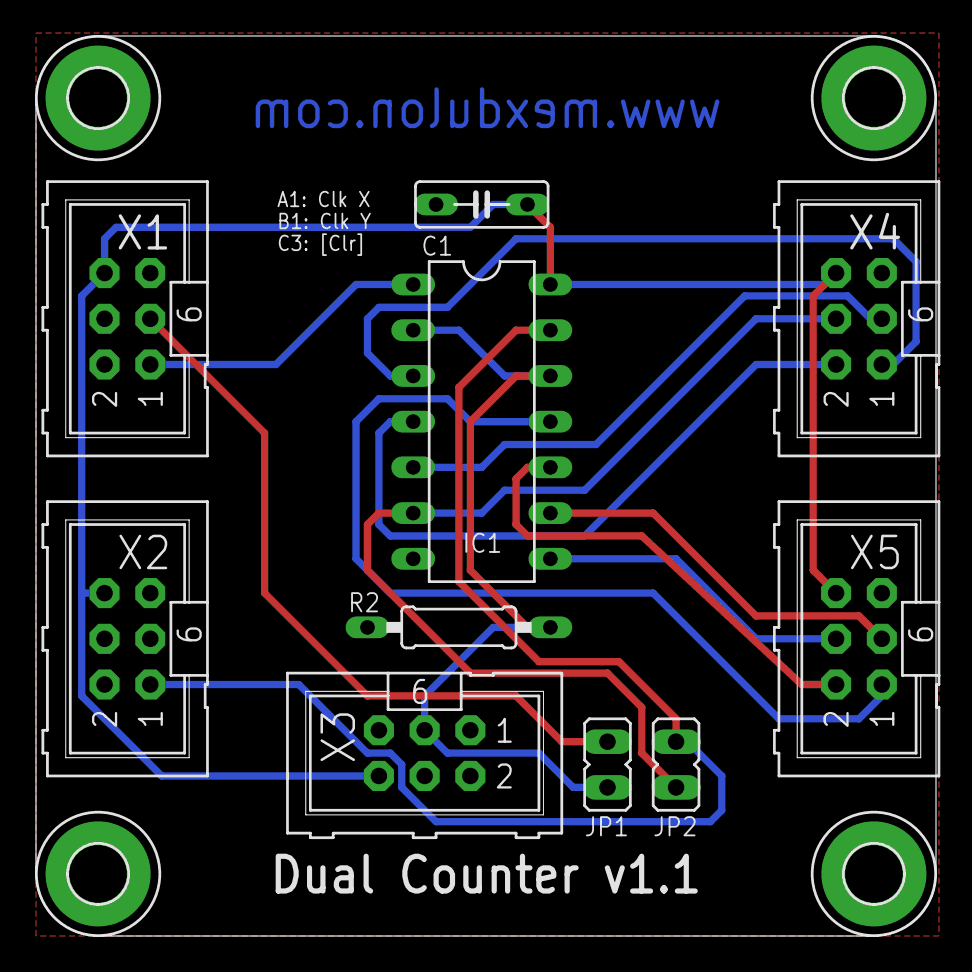
[picture p260: board CNT_1_1.brd from above]

Board: 2 copper layers, 50.0 x 50.0 mm, 14 parts (0 on the bottom side), 14 nets.
