mexdulon/tetra-Boards/eagle/D12_1_0.brd

## EAGLE design eagle/D12_1_0.brd (2017-11-03)

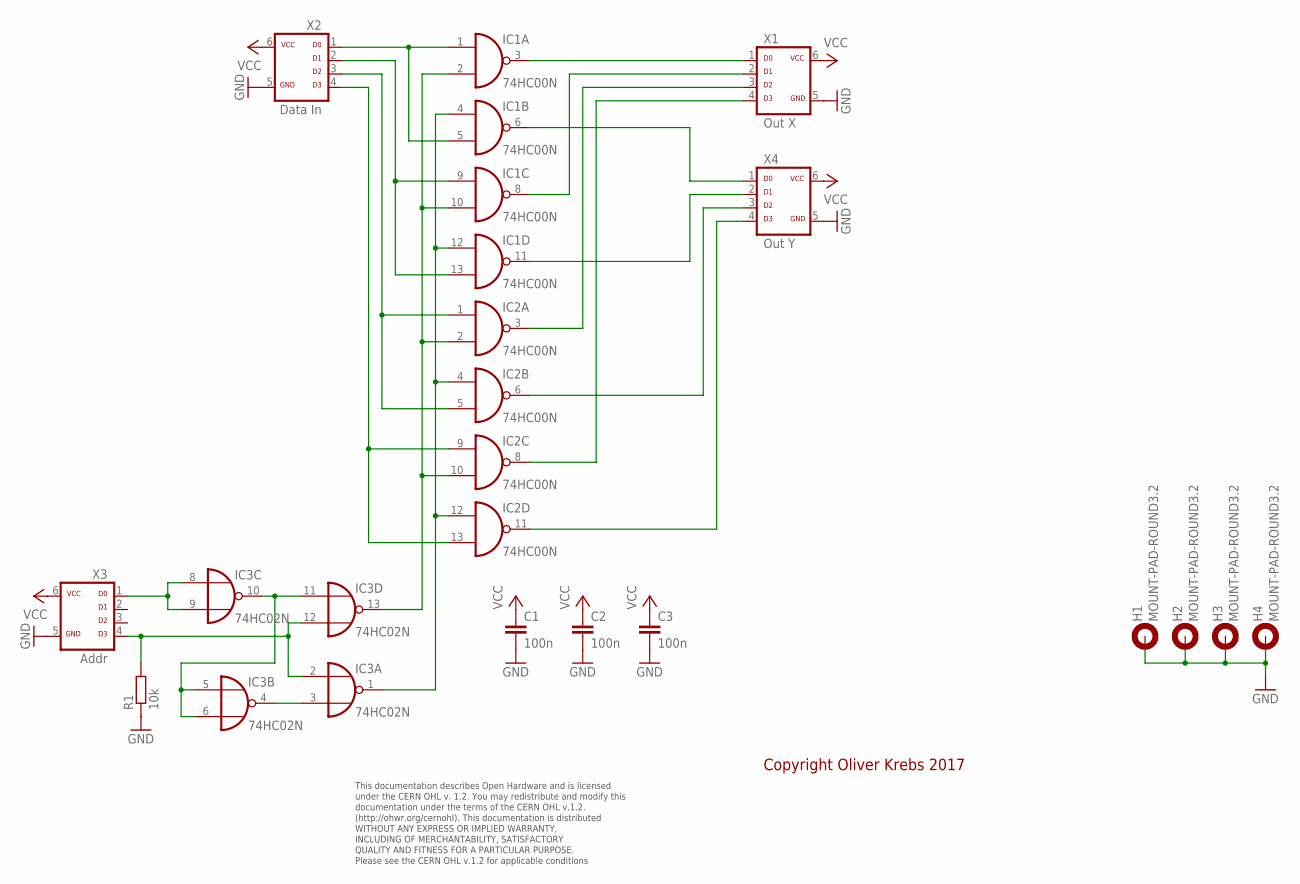
[picture p261: schematic D12_1_0.sch]

Parts:
C1, C2, C3: 100n; C050-025X075
H1, H2, H3, H4: MOUNT-PAD-ROUND3.2; 3,2-PAD
IC1, IC2: 74HC00N; DIL14
IC3: 74HC02N; DIL14
R1: 10k; 0207/10
X1: Out X; ML-6
X2: Data In; ML-6
X3: Addr; ML-6
X4: Out Y; ML-6

Connections:
GND: C1.2, C2.2, C3.2, H1.B3,2, H2.B3,2, H3.B3,2, H4.B3,2, IC1.7 (GND), IC2.7 (GND), IC3.7 (GND), R1.1, X1.5, X2.5, X3.5, X4.5
unnamed: IC1.3 (O), X1.1
unnamed: IC1.8 (O), X1.2
unnamed: IC2.3 (O), X1.3
unnamed: IC1.1 (I0), IC1.5 (I1), X2.1
unnamed: IC1.9 (I0), IC1.13 (I1), X2.2
unnamed: IC2.1 (I0), IC2.5 (I1), X2.3
unnamed: IC2.9 (I0), IC2.13 (I1), X2.4
unnamed: IC2.8 (O), X1.4
unnamed: IC1.6 (O), X4.1
unnamed: IC1.11 (O), X4.2
unnamed: IC2.6 (O), X4.3
unnamed: IC2.11 (O), X4.4
unnamed: IC3.5 (I0), IC3.6 (I1), IC3.10 (O), IC3.11 (I0)
unnamed: IC3.2 (I0), IC3.12 (I1), R1.2, X3.4
unnamed: IC1.2 (I1), IC1.10 (I1), IC2.2 (I1), IC2.10 (I1), IC3.13 (O)
unnamed: IC1.4 (I0), IC1.12 (I0), IC2.4 (I0), IC2.12 (I0), IC3.1 (O)
unnamed: IC3.3 (I1), IC3.4 (O)
unnamed: IC3.8 (I0), IC3.9 (I1), X3.1
VCC: C1.1, C2.1, C3.1, IC1.14 (VCC), IC2.14 (VCC), IC3.14 (VCC), X1.6, X2.6, X3.6, X4.6

Notes on the sheet:
This documentation describes Open Hardware and is licensed under the CERN OHL v. 1.2. You may redistribute and modify this documentation under the terms of the CERN OHL v.1.2. (http://ohwr.org/cernohl). This documentation is distributed WITHOUT ANY EXPRESS OR IMPLIED WARRANTY, INCLUDING OF MERCHANT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
Copyright Oliver Krebs 2017

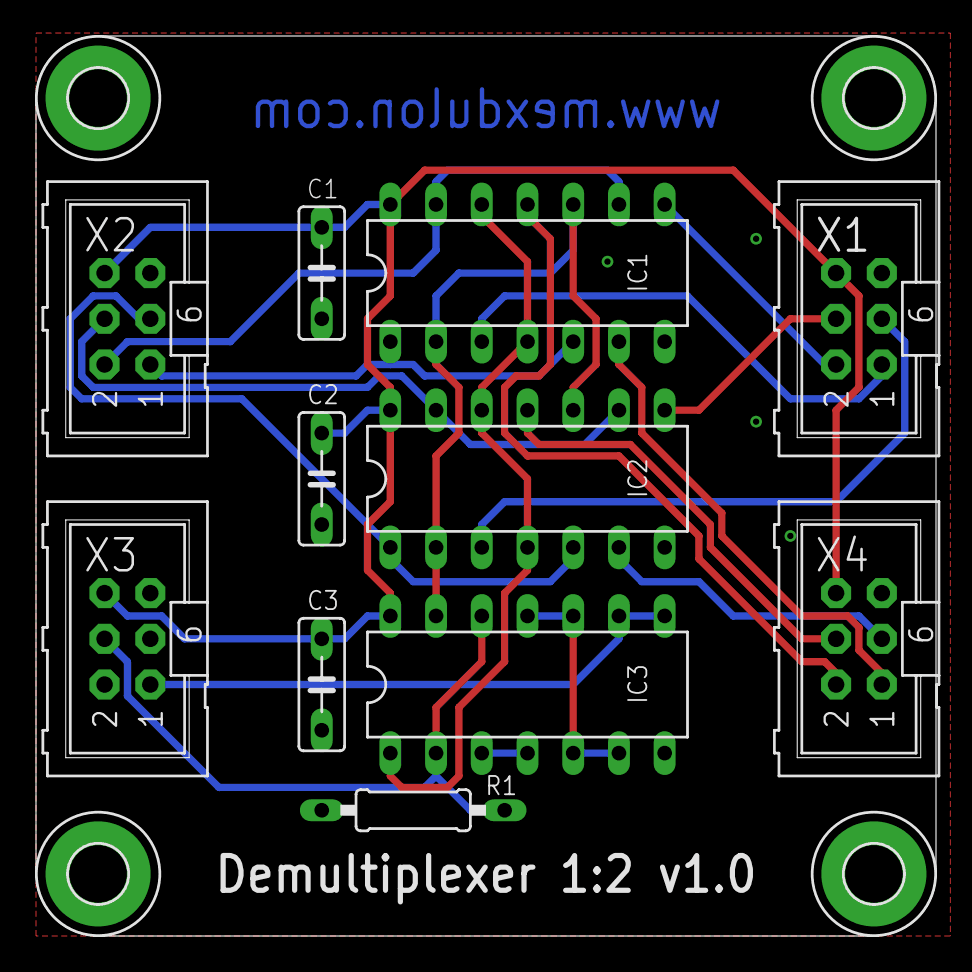
[picture p262: board D12_1_0.brd from above]

Board: 2 copper layers, 50.0 x 50.0 mm, 15 parts (0 on the bottom side), 20 nets.
