mexdulon/tetra-Boards/eagle/SRG_1_0.brd

## EAGLE design eagle/SRG_1_0.brd (2017-10-13)

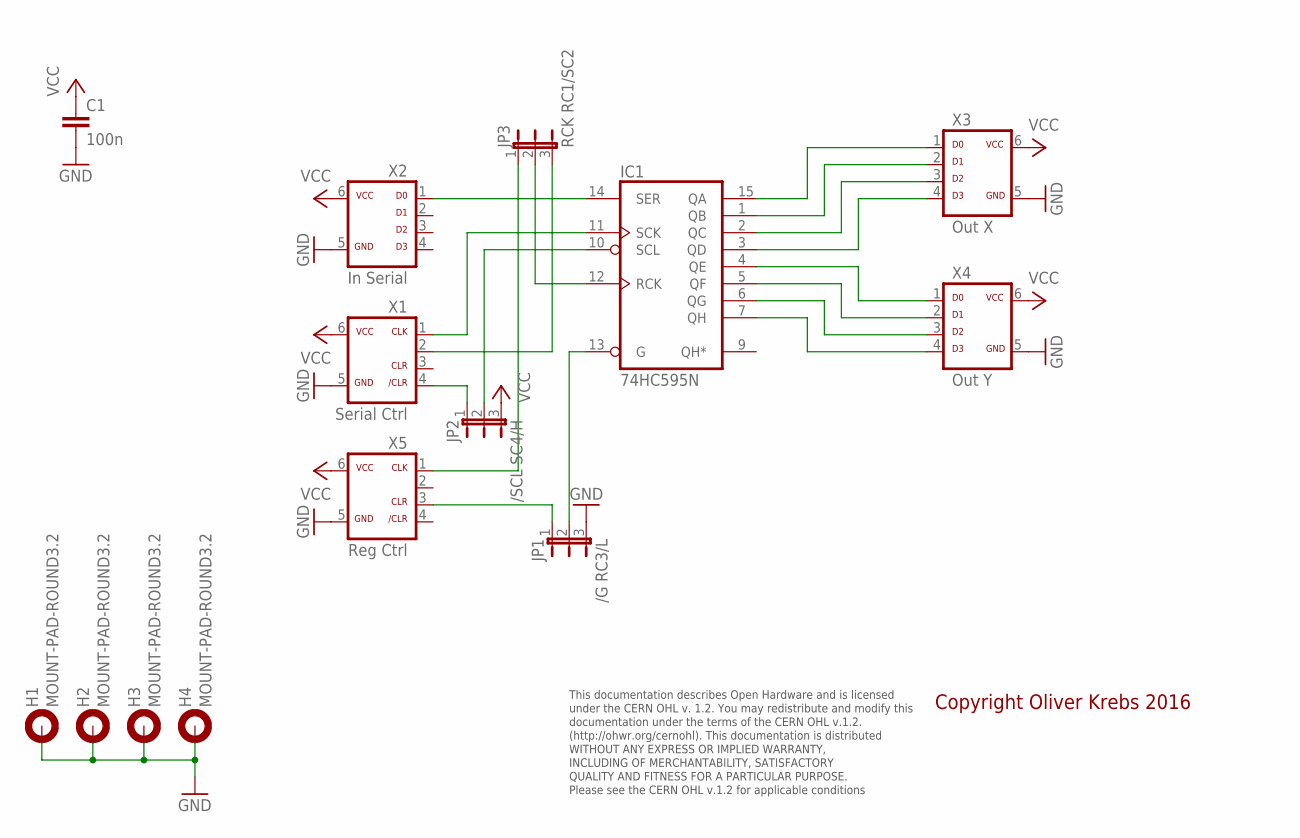
[picture p263: schematic SRG_1_0.sch]

Parts:
C1: 100n; C050-025X075
H1, H2, H3, H4: MOUNT-PAD-ROUND3.2; 3,2-PAD
IC1: 74HC595N; DIL16
JP1: /G RC3/L; JP2-U
JP2: /SCL SC4/H; JP2-U
JP3: RCK RC1/SC2; JP2-U
X1: Serial Ctrl; ML-6
X2: In Serial; ML-6
X3: Out X; ML-6
X4: Out Y; ML-6
X5: Reg Ctrl; ML-6

Connections:
GND: C1.2, H1.B3,2, H2.B3,2, H3.B3,2, H4.B3,2, IC1.8 (GND), JP1.3, X1.5, X2.5, X3.5, X4.5, X5.5
unnamed: IC1.15 (QA), X3.1
unnamed: IC1.1 (QB), X3.2
unnamed: IC1.2 (QC), X3.3
unnamed: IC1.3 (QD), X3.4
unnamed: IC1.4 (QE), X4.1
unnamed: IC1.5 (QF), X4.2
unnamed: IC1.6 (QG), X4.3
unnamed: IC1.7 (QH), X4.4
unnamed: IC1.14 (SER), X2.1
unnamed: IC1.10 (SCL), JP2.2
unnamed: IC1.11 (SCK), X1.1
unnamed: IC1.12 (RCK), JP3.2
unnamed: IC1.13 (G), JP1.2
unnamed: JP1.1, X5.3
unnamed: JP2.1, X1.4
unnamed: JP3.1, X5.1
unnamed: JP3.3, X1.2
VCC: C1.1, IC1.16 (VCC), JP2.3, X1.6, X2.6, X3.6, X4.6, X5.6

Notes on the sheet:
This documentation describes Open Hardware and is licensed under the CERN OHL v. 1.2. You may redistribute and modify this documentation under the terms of the CERN OHL v.1.2. (http://ohwr.org/cernohl). This documentation is distributed WITHOUT ANY EXPRESS OR IMPLIED WARRANTY, INCLUDING OF MERCHANT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
Copyright Oliver Krebs 2016

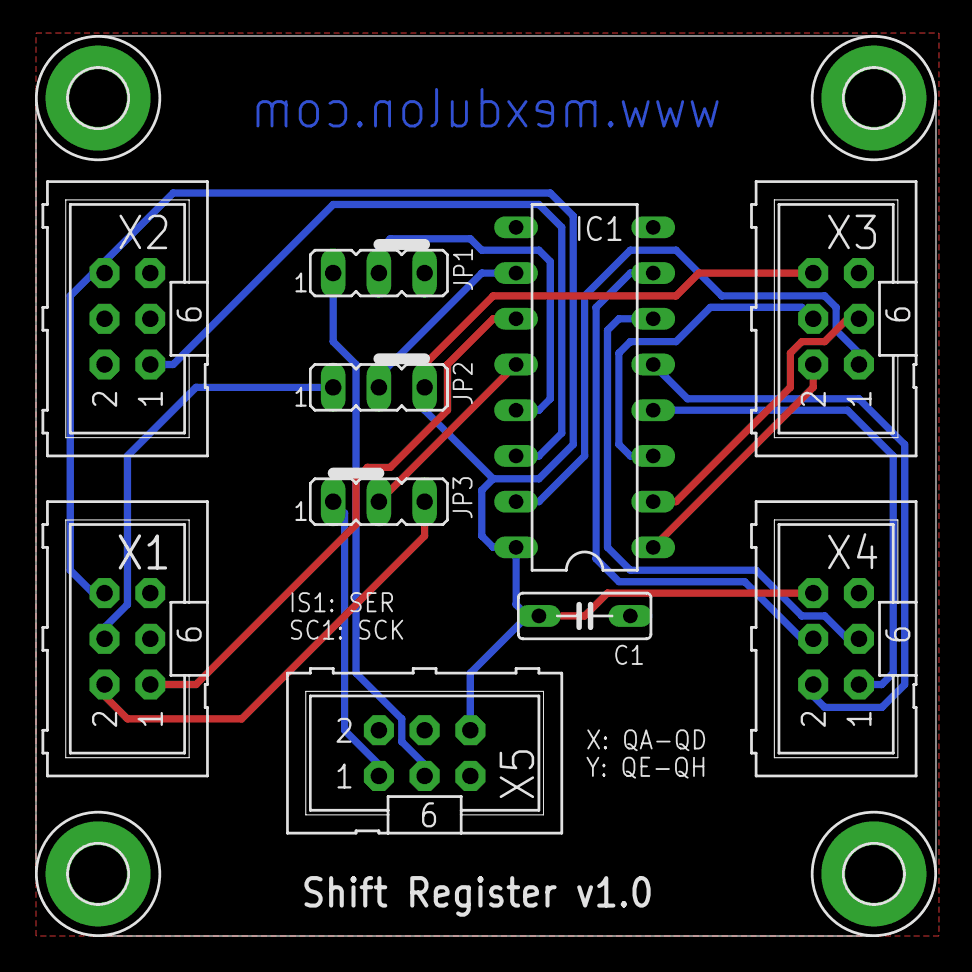
[picture p264: board SRG_1_0.brd from above]

Board: 2 copper layers, 50.0 x 50.0 mm, 14 parts (0 on the bottom side), 19 nets.
