mexdulon/tetra-Boards/eagle/DAC_1_0.brd

## EAGLE design eagle/DAC_1_0.brd (2017-10-13)

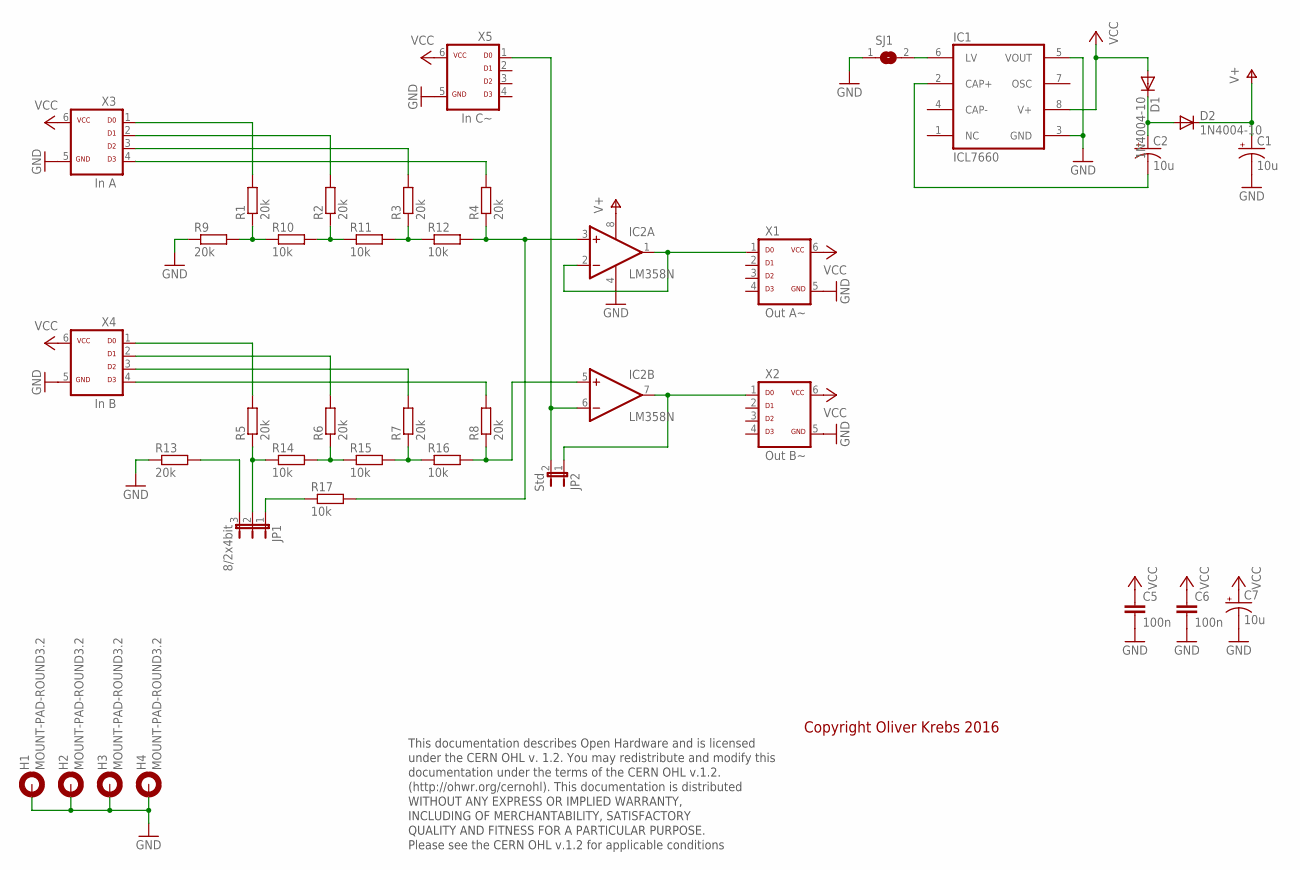
[picture p265: schematic DAC_1_0.sch]

Parts:
C1, C2, C7: 10u; CPOL-RADIAL-10UF-25V
C5, C6: 100n; CAP-PTH-5MM
D1, D2: 1N4004-10; DO41-10
H1, H2, H3, H4: MOUNT-PAD-ROUND3.2; 3,2-PAD
IC1: ICL7660; DIL08
IC2: LM358N; DIL08
JP1: 8/2x4bit; JP2-U
JP2: Std; JP1
R1, R2, R3, R4, R5, R6, R7, R8, R9, R13: 20k; 0207/2V
R10, R11, R12, R14, R15, R16, R17: 10k; 0207/2V
SJ1: SJ
X1: Out A~; ML-6
X2: Out B~; ML-6
X3: In A; ML-6
X4: In B; ML-6
X5: In C~; ML-6

Connections:
GND: C1.2 (-), C5.2, C6.2, C7.2 (-), H1.B3,2, H2.B3,2, H3.B3,2, H4.B3,2, IC1.3 (GND), IC1.5 (VOUT), IC2.4 (V-), R9.1, R13.1, SJ1.1, X1.5, X2.5, X3.5, X4.5, X5.5
unnamed: R1.2, X3.1
unnamed: R2.2, X3.2
unnamed: R3.2, X3.3
unnamed: R4.2, X3.4
unnamed: C2.2 (-), IC1.2 (CAP+)
unnamed: C2.1 (+), D1.C, D2.A
unnamed: R1.1, R9.2, R10.1
unnamed: R2.1, R10.2, R11.1
unnamed: R3.1, R11.2, R12.1
unnamed: IC2.3 (+IN), R4.1, R12.2, R17.2
unnamed: R5.2, X4.1
unnamed: R6.2, X4.2
unnamed: R7.2, X4.3
unnamed: R8.2, X4.4
unnamed: JP1.2, R5.1, R14.1
unnamed: R6.1, R14.2, R15.1
unnamed: R7.1, R15.2, R16.1
unnamed: IC2.5 (+IN), R8.1, R16.2
unnamed: JP1.3, R13.2
unnamed: IC2.1 (OUT), IC2.2 (-IN), X1.1
unnamed: IC2.7 (OUT), JP2.1, X2.1
unnamed: JP1.1, R17.1
unnamed: IC1.6 (LV), SJ1.2
unnamed: IC2.6 (-IN), JP2.2, X5.1
V+: C1.1 (+), D2.C, IC2.8 (V+)
VCC: C5.1, C6.1, C7.1 (+), D1.A, IC1.8 (V+), X1.6, X2.6, X3.6, X4.6, X5.6

Notes on the sheet:
This documentation describes Open Hardware and is licensed under the CERN OHL v. 1.2. You may redistribute and modify this documentation under the terms of the CERN OHL v.1.2. (http://ohwr.org/cernohl). This documentation is distributed WITHOUT ANY EXPRESS OR IMPLIED WARRANTY, INCLUDING OF MERCHANT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
Copyright Oliver Krebs 2016

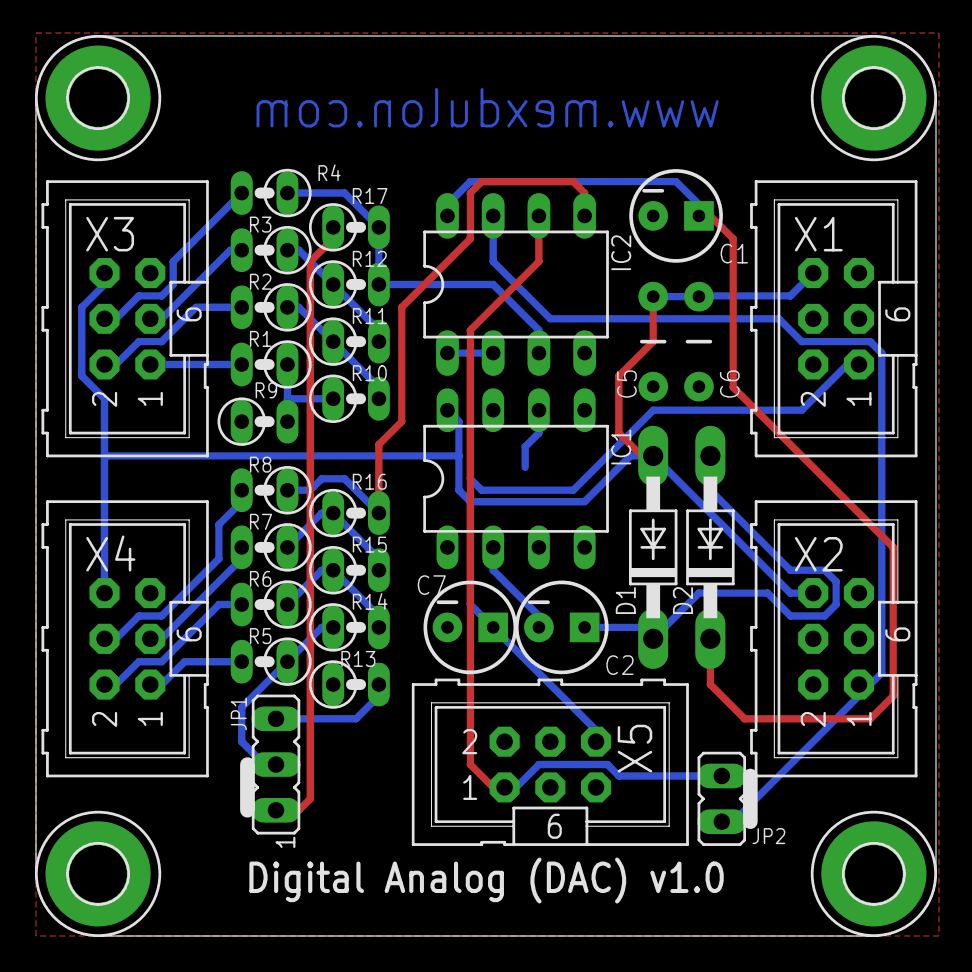
[picture p266: board DAC_1_0.brd from above]

Board: 2 copper layers, 50.0 x 50.0 mm, 38 parts (1 on the bottom side), 27 nets.
