mexdulon/tetra-Boards/eagle/REG_1_0.brd

## EAGLE design eagle/REG_1_0.brd (2017-10-13)

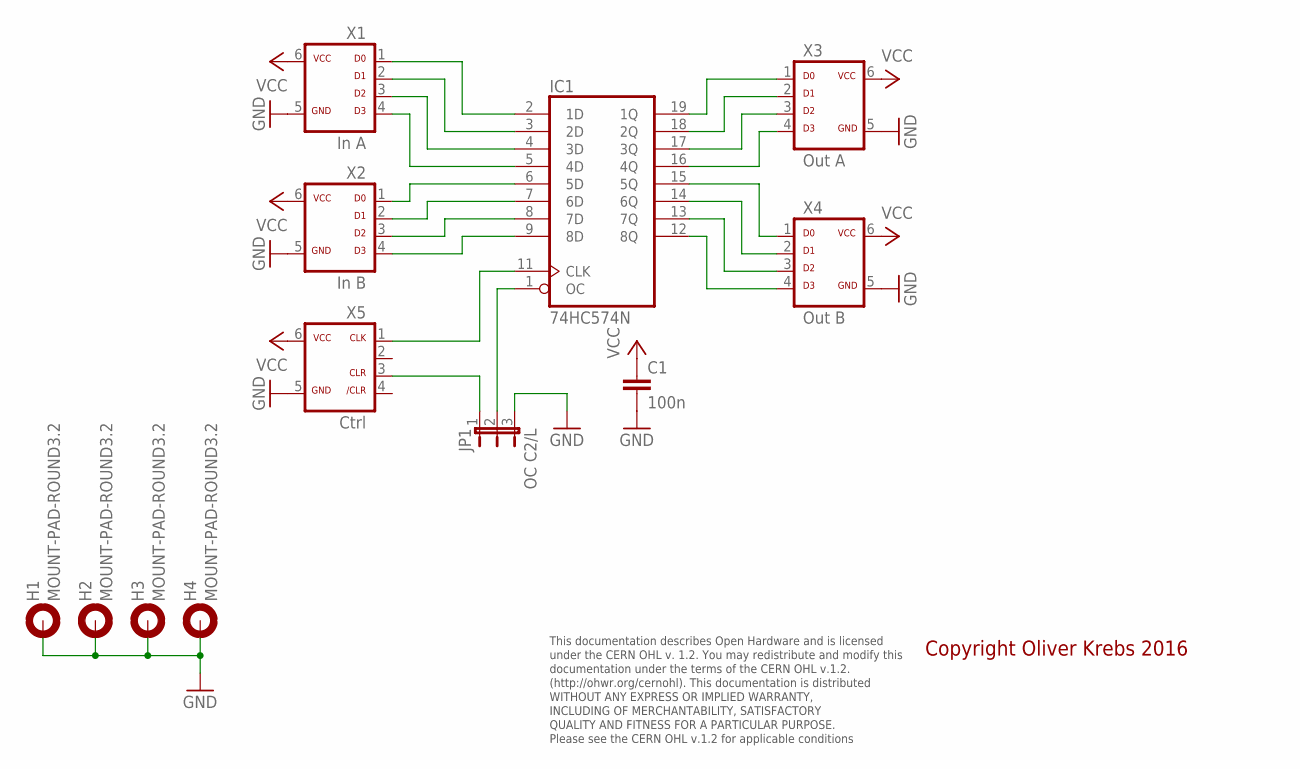
[picture p267: schematic REG_1_0.sch]

Parts:
C1: 100n; C050-025X075
H1, H2, H3, H4: MOUNT-PAD-ROUND3.2; 3,2-PAD
IC1: 74HC574N; DIL20
JP1: OC C2/L; JP2
X1: In A; ML-6
X2: In B; ML-6
X3: Out A; ML-6
X4: Out B; ML-6
X5: Ctrl; ML-6

Connections:
GND: C1.2, H1.B3,2, H2.B3,2, H3.B3,2, H4.B3,2, IC1.10 (GND), JP1.3, X1.5, X2.5, X3.5, X4.5, X5.5
unnamed: IC1.2 (1D), X1.1
unnamed: IC1.3 (2D), X1.2
unnamed: IC1.4 (3D), X1.3
unnamed: IC1.5 (4D), X1.4
unnamed: IC1.6 (5D), X2.1
unnamed: IC1.7 (6D), X2.2
unnamed: IC1.8 (7D), X2.3
unnamed: IC1.9 (8D), X2.4
unnamed: IC1.11 (CLK), X5.1
unnamed: IC1.1 (OC), JP1.2
unnamed: IC1.19 (1Q), X3.1
unnamed: IC1.18 (2Q), X3.2
unnamed: IC1.17 (3Q), X3.3
unnamed: IC1.16 (4Q), X3.4
unnamed: IC1.15 (5Q), X4.1
unnamed: IC1.14 (6Q), X4.2
unnamed: IC1.13 (7Q), X4.3
unnamed: IC1.12 (8Q), X4.4
unnamed: JP1.1, X5.3
VCC: C1.1, IC1.20 (VCC), X1.6, X2.6, X3.6, X4.6, X5.6

Notes on the sheet:
This documentation describes Open Hardware and is licensed under the CERN OHL v. 1.2. You may redistribute and modify this documentation under the terms of the CERN OHL v.1.2. (http://ohwr.org/cernohl). This documentation is distributed WITHOUT ANY EXPRESS OR IMPLIED WARRANTY, INCLUDING OF MERCHANT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
Copyright Oliver Krebs 2016

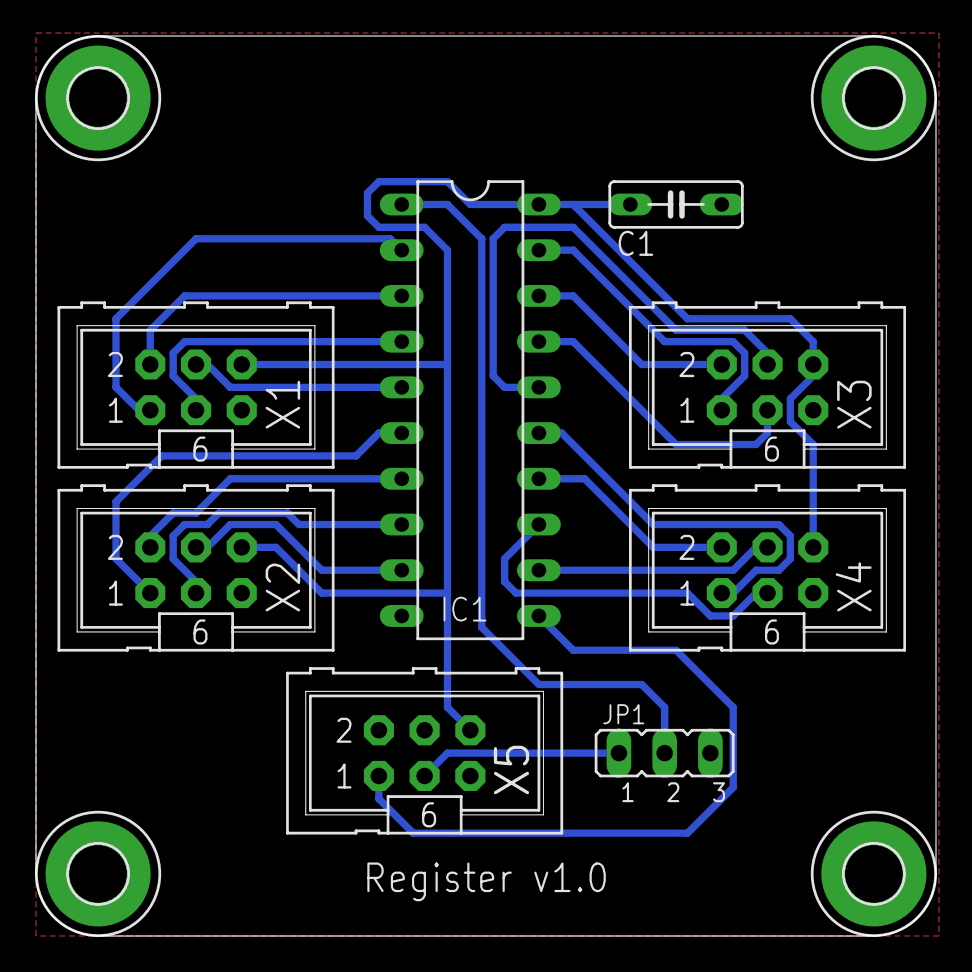
[picture p268: board REG_1_0.brd from above]

Board: 2 copper layers, 50.0 x 50.0 mm, 12 parts (0 on the bottom side), 21 nets.
