mexdulon/tetra-Boards/eagle/MTR_1_0.brd

## EAGLE design eagle/MTR_1_0.brd (2017-10-13)

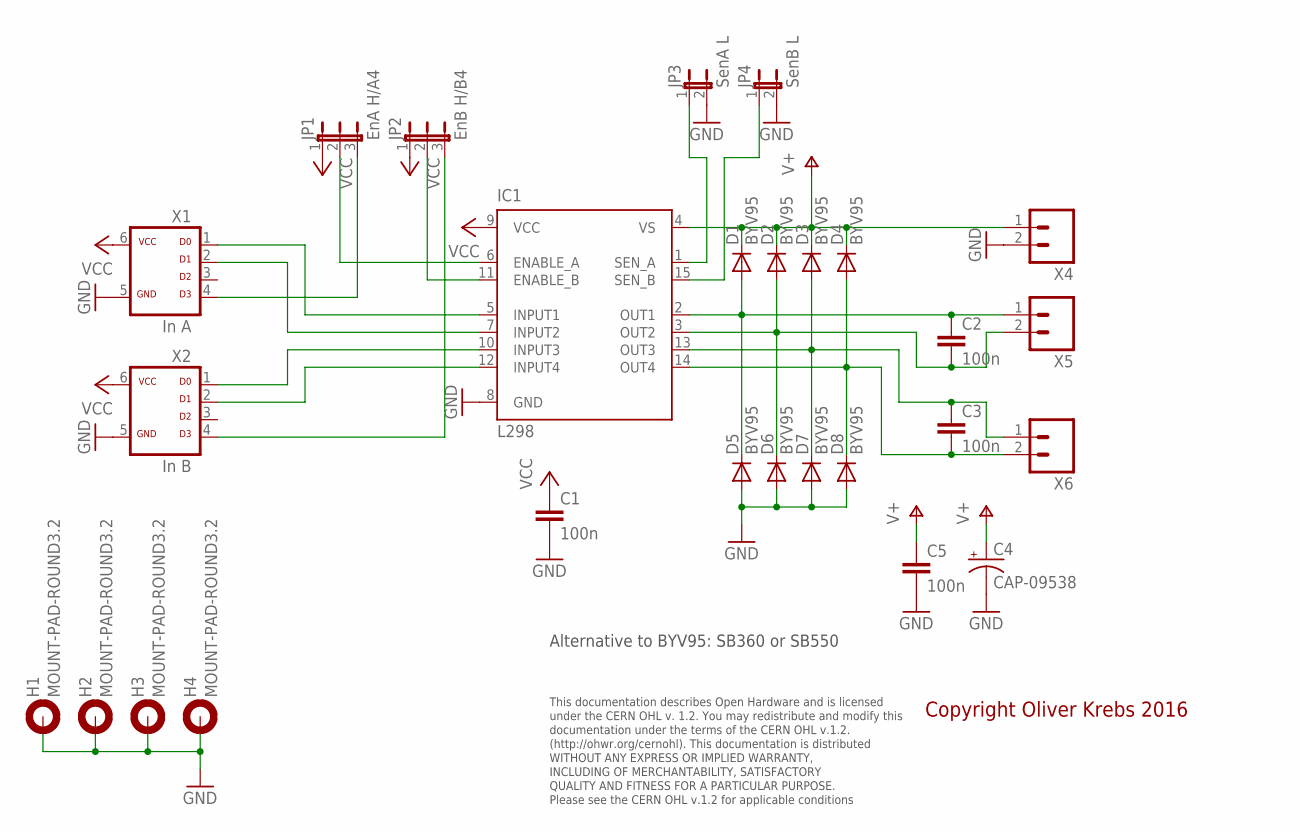
[picture p269: schematic MTR_1_0.sch]

Parts:
C1, C2, C3, C5: 100n; C050-025X075
C4: CAP-09538; CPOL-RADIAL-1000UF-25V
D1, D2, D3, D4, D5, D6, D7, D8: BYV95; SOD57-10
H1, H2, H3, H4: MOUNT-PAD-ROUND3.2; 3,2-PAD
IC1: L298; MULTIWATT-15
JP1: EnA H/A4; JP2-U
JP2: EnB H/B4; JP2-U
JP3: SenA L; JP1
JP4: SenB L; JP1
X1: In A; ML-6
X2: In B; ML-6
X4, X5, X6: M021.3MM-5.08; 1X02_BIG_5.08

Connections:
GND: C1.2, C4.-, C5.2, D5.A, D6.A, D7.A, D8.A, H1.B3,2, H2.B3,2, H3.B3,2, H4.B3,2, IC1.8 (GND), JP3.2, JP4.2, X1.5, X2.5, X4.2
unnamed: JP2.3, X2.4
unnamed: IC1.6 (ENABLE_A), JP1.2
unnamed: IC1.11 (ENABLE_B), JP2.2
unnamed: JP1.3, X1.4
unnamed: C2.1, D1.A, D5.C, IC1.2 (OUT1), X5.1
unnamed: C2.2, D2.A, D6.C, IC1.3 (OUT2), X5.2
unnamed: C3.1, D3.A, D7.C, IC1.13 (OUT3), X6.1
unnamed: C3.2, D4.A, D8.C, IC1.14 (OUT4), X6.2
unnamed: IC1.5 (INPUT1), X1.1
unnamed: IC1.1 (SEN_A), JP3.1
unnamed: IC1.15 (SEN_B), JP4.1
unnamed: IC1.7 (INPUT2), X1.2
unnamed: IC1.10 (INPUT3), X2.1
unnamed: IC1.12 (INPUT4), X2.2
V+: C4.+, C5.1, D1.C, D2.C, D3.C, D4.C, IC1.4 (VS), X4.1
VCC: C1.1, IC1.9 (VCC), JP1.1, JP2.1, X1.6, X2.6

Notes on the sheet:
This documentation describes Open Hardware and is licensed under the CERN OHL v. 1.2. You may redistribute and modify this documentation under the terms of the CERN OHL v.1.2. (http://ohwr.org/cernohl). This documentation is distributed WITHOUT ANY EXPRESS OR IMPLIED WARRANTY, INCLUDING OF MERCHANT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
Copyright Oliver Krebs 2016
Alternative to BYV95: SB360 or SB550

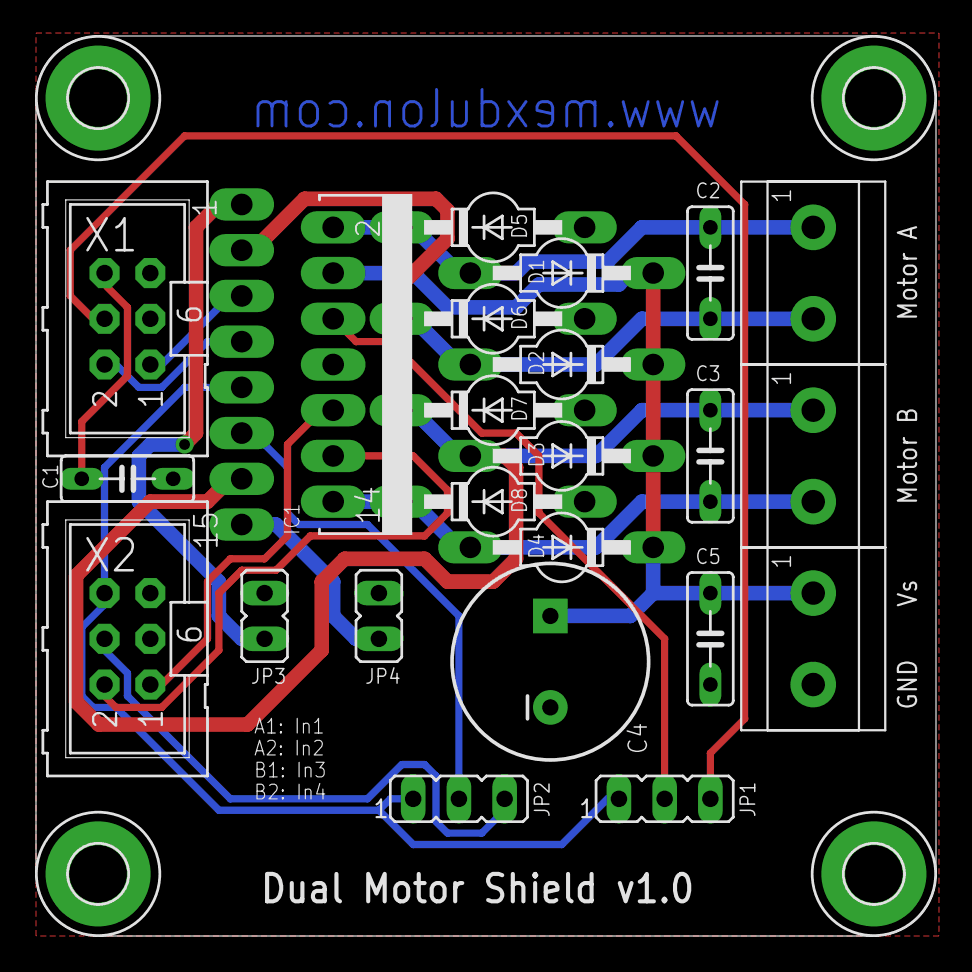
[picture p270: board MTR_1_0.brd from above]

Board: 2 copper layers, 50.0 x 50.0 mm, 27 parts (0 on the bottom side), 17 nets.
