mexdulon/tetra-Boards/eagle/ARD_1_0.brd

## EAGLE design eagle/ARD_1_0.brd (2017-10-13)

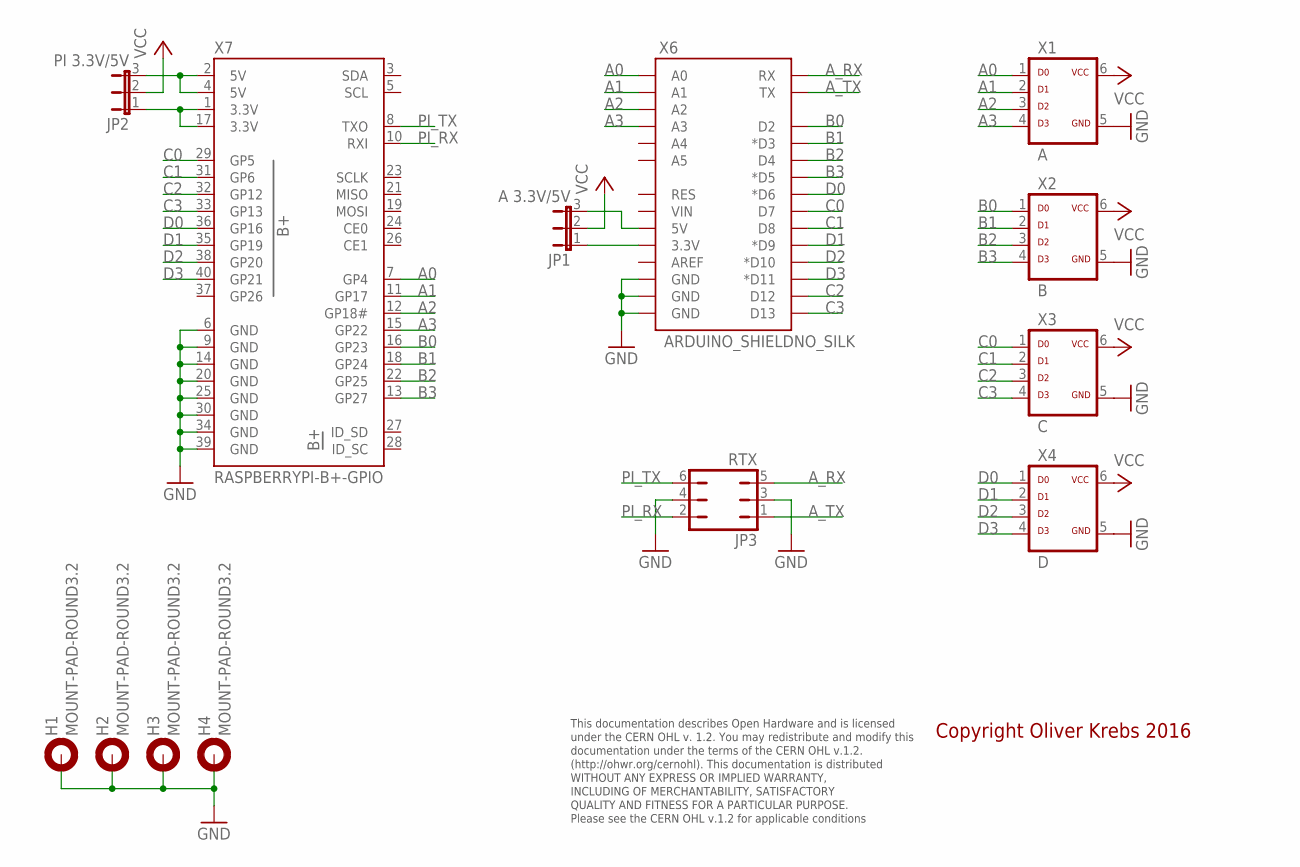
[picture p271: schematic ARD_1_0.sch]

Parts:
H1, H2, H3, H4: MOUNT-PAD-ROUND3.2; 3,2-PAD
JP1: A 3.3V/5V; JP2
JP2: PI 3.3V/5V; JP2
JP3: RTX; JP3Q
X1: A; ML-6
X2: B; ML-6
X3: C; ML-6
X4: D; ML-6
X6: ARDUINO_SHIELDNO_SILK; DUEMILANOVE_VIAS
X7: RASPBERRYPI-B+-GPIO; 2X20-SHROUDED

Connections:
A0: X1.1, X6.A0, X7.7 (GP4)
A1: X1.2, X6.A1, X7.11 (GP17)
A2: X1.3, X6.A2, X7.12 (GP18#)
A3: X1.4, X6.A3, X7.15 (GP22)
A_RX: JP3.5, X6.RX
A_TX: JP3.1, X6.TX
B0: X2.1, X6.D2, X7.16 (GP23)
B1: X2.2, X6.D3 (*D3), X7.18 (GP24)
B2: X2.3, X6.D4, X7.22 (GP25)
B3: X2.4, X6.D5 (*D5), X7.13 (GP27)
C0: X3.1, X6.D7, X7.29 (GP5)
C1: X3.2, X6.D8, X7.31 (GP6)
C2: X3.3, X6.D12, X7.32 (GP12)
C3: X3.4, X6.D13, X7.33 (GP13)
D0: X4.1, X6.D6 (*D6), X7.36 (GP16)
D1: X4.2, X6.D9 (*D9), X7.35 (GP19)
D2: X4.3, X6.D10 (*D10), X7.38 (GP20)
D3: X4.4, X6.D11 (*D11), X7.40 (GP21)
GND: H1.B3,2, H2.B3,2, H3.B3,2, H4.B3,2, JP3.3, JP3.4, X1.5, X2.5, X3.5, X4.5, X6.GND@0 (GND), X6.GND@1 (GND), X6.GND@2 (GND), X7.6 (GND), X7.9 (GND), X7.14 (GND), X7.20 (GND), X7.25 (GND), X7.30 (GND), X7.34 (GND), X7.39 (GND)
unnamed: JP2.3, X7.2 (5V), X7.4 (5V)
unnamed: JP2.1, X7.1 (3.3V), X7.17 (3.3V)
unnamed: JP1.1, X6.3.3V
unnamed: JP1.3, X6.5V
PI_RX: JP3.2, X7.10 (RXI)
PI_TX: JP3.6, X7.8 (TXO)
VCC: JP1.2, JP2.2, X1.6, X2.6, X3.6, X4.6

Notes on the sheet:
This documentation describes Open Hardware and is licensed under the CERN OHL v. 1.2. You may redistribute and modify this documentation under the terms of the CERN OHL v.1.2. (http://ohwr.org/cernohl). This documentation is distributed WITHOUT ANY EXPRESS OR IMPLIED WARRANTY, INCLUDING OF MERCHANT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
Copyright Oliver Krebs 2016

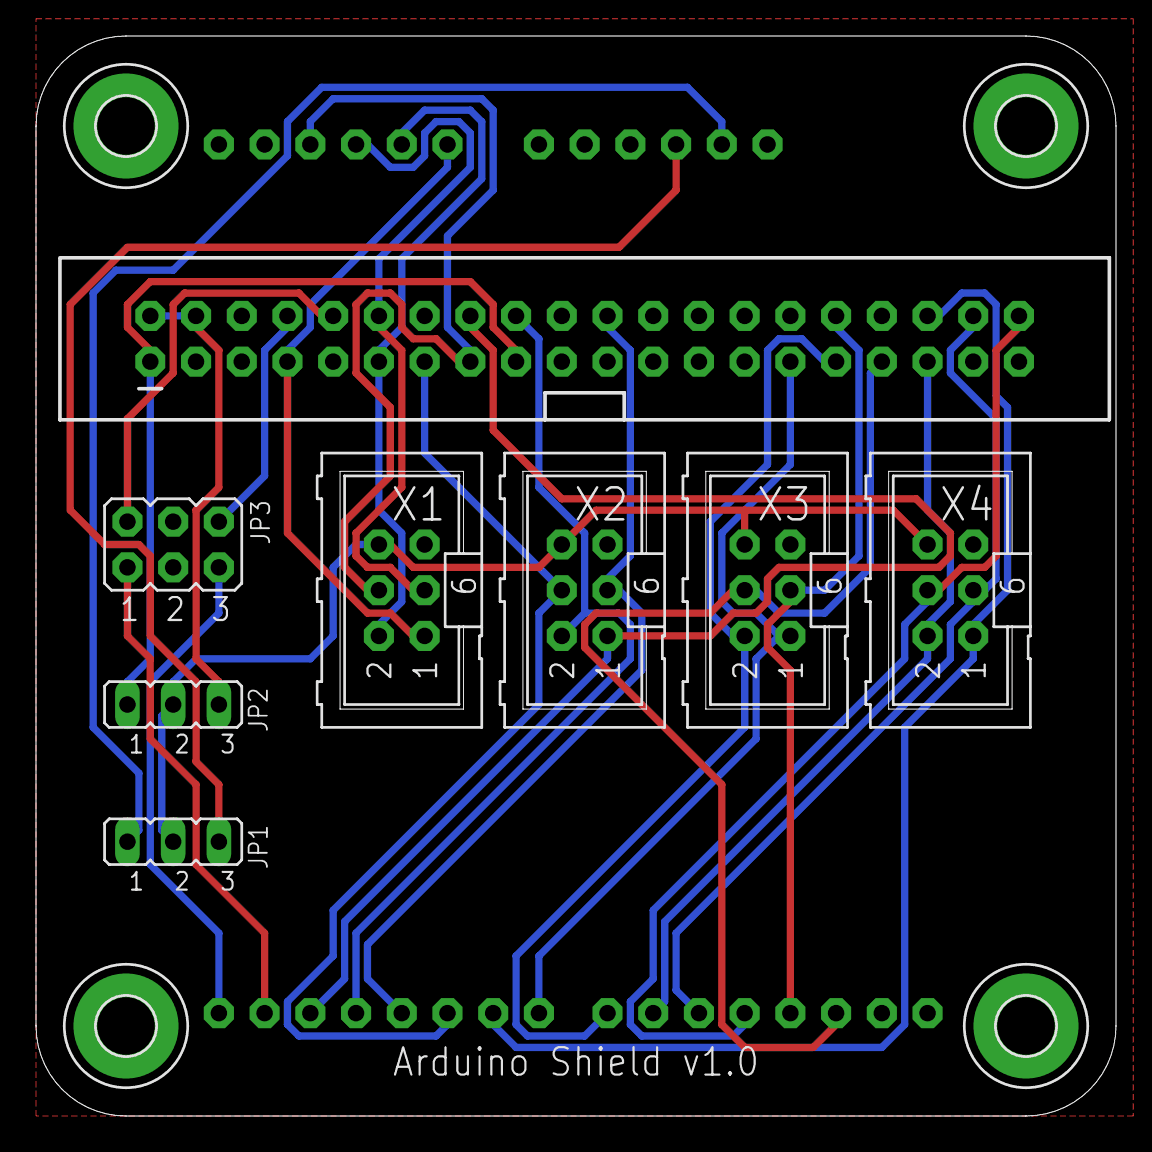
[picture p272: board ARD_1_0.brd from above]

Board: 2 copper layers, 60.0 x 60.0 mm, 13 parts (0 on the bottom side), 26 nets.
